orpheo28/physicallovablex/gtm-harness/context/profile.md

# Profile

Last updated: 2026-09-27. Truth order for product facts: `04_LIVRABLE/PRODUIT.md` > `04_LIVRABLE/PRD.md` > this file.

## Company
- **What it is:** PhysicalLovableX is a working name for an idea Hexa WTF is scoping. It is not a launched company: no revenue, no customers, no reference accounts (`00_ENONCE.md`; `03_DISCOVERY/envoi/SUIVI.md` shows 0 sent on 27/09).
- **Team (GTM):** Orphéo (O) runs outreach, calls and the harness. A hardware engineer contractor to sign Factory Packs is planned for W2 (**Hypothesis**, `04_LIVRABLE/deck/DECK_DRAFT.md` slide 9). Intros from the Hexa network are to ask, not assumed (same slide).
- **Stage:** pre-seed case study, 6-week plan W0-W6 (deck slide 9).

## Product (two pieces)
- **The Studio:** describe a product in one sentence, see it in 3D with unit cost and a factory shortlist, refine by prompting, then "Make it" runs 13 stages to a Launch Dossier. Measured: first version in 18-24 s; refines 4-7 s (colour, feature) and 11-24 s (geometry) (`PRODUIT.md`).
- **The Factory Pack (the primitive):** a spec package a factory can quote without back-and-forth: structured spec, CAD, BOM with component risk, DFM alerts, certification checklist, estimated landed cost, questions for the factory in EN + CN, assumption register (`PRODUIT.md`).
- **Two entry modes:** "I have an idea" (funnel, data) and "I have a prototype" (GTM wedge: funded founders stuck before production) (`PRODUIT.md`).

## What is real vs simulated
| Real (built, labelled Measured or Sourced) | Simulated (labelled "Fictional — demo data") |
|---|---|
| Brief, design, AI-written CAD (7/7 live prompts), measured DFM, certification map, LCSC part prices (dated snapshot), HTS lines from CBP rulings, Drewry freight index, cost engine, production plan, brand kit, production MCP over HTTP | The 15 partners (11 factories, 1 integrator, 3 installers), their capacity, quotes and negotiation replies, carrier quotes and transit days |

Source: `PRODUIT.md`, "Trust labels". Consequence for GTM: never present a factory, quote or delivery result as real in outreach or calls.

## Deal profile (all Hypothesis until a first deal)
| Tier | What the founder gets | Price | Cycle | Who signs |
|---|---|---|---|---|
| 1. Free Studio | Studio up to the Factory Pack | Free (land grab, data) | Self-serve | Founder |
| 2. Accompanied production | Human-reviewed pack, committed landed price, QC | Commission on the production order | Unknown; founder decides alone or with a co-founder (`context/icp.md`) | Founder |
| 3. Financing, logistics | Cash plan, freight | Take rate | Unknown | Founder |

Source: `PRODUIT.md`, "Business model (hypothesis)"; deck slide 5. Lighthouse founders are non-paying until proof of value; we test willingness to pay (amount already paid to intermediaries, W5 deposit or LOI), we do not optimise price (`context/icp.md`).
Comparable spend the founder already has: sourcing agents 5-10% of the order ([Dragon Sourcing](https://www.dragonsourcing.com/top-10-cost-insights-for-hiring-a-china-sourcing-agent/)); pre-shipment inspection $268 per man-day ([V-Trust](https://www.v-trust.com/en/our-network)).

## Reference customers
None yet. Do not imply any. The first documented case (prototype → Factory Pack → factory quote) is planned for W5-W6 (deck slide 9).
