orpheo28/physicallovablex/gtm-harness/outputs/research/pilet.md

# Pilet (Soulscircuit): account research (2026-09-26)

Run of `skills/account-research` on row 2 of `03_DISCOVERY/envoi/A_ENVOYER.md`.

## Pilet (Soulscircuit): score 5 (more than 12 months late, redesign after the campaign, backers organised a refund site; `outputs/accounts.csv`)
Problem: delivery promised for July 2025. On 2026-04-11, Update #20 ("Moving to Compute Module 5") switched the design from the Raspberry Pi 5 to the Compute Module 5, about five months past the deadline. The same articles say the team is also redesigning the case and building a display from scratch instead of using an off-the-shelf one. Raised CA$1,264,707 from 2,777 backers. No units shipped. ([C33 Technology](https://c33tech.com/blog/2026/04/how_not_to_pilet_a_kickstarter/), 2026-04-12; [Kickstarter update #20](https://www.kickstarter.com/projects/soulscircuit/pilet-opensource-modular-portable-mini-computer/posts/4654610), listed by search, page returns 403; [Hackster](https://www.hackster.io/news/soulscircuit-redesigns-its-pilet-handhelds-nearly-a-year-overdue-to-accept-the-raspberry-pi-cm5-d7f64a58cf36)). The creators' own sentence was not retrieved. The closest quote is from a backer in the C33 article: "We could use a quick message about how the manufacturer selection is going."
Root cause: design/engineering (redesign) | Confidence: high. **Hypothesis:** a second cause, factory selection, is suggested only by that backer quote, so it is not coded.
People: Christopher Stockall, co-founder ([Hackster post](https://www.facebook.com/hacksterio/posts/christopher-stockall-has-launched-a-crowdfunding-campaign-for-the-soulscircuit-p/1030775865757133/)); a second co-founder named "James" per `outputs/accounts.csv`, surname not found; engineering co-founder: none found
Channel: Kickstarter message
Next product: none found. Pilet 5 and Pilet 7 belong to the same campaign.
Angle: design/engineering question from `brief.md`: what the team learned between the prototype and manufacturing that led to the CM5 redesign.
Do not say: refunds, piletrefund.com, "in way over their head" (the C33 author's words), or update #22 screen failures. That detail comes only from piletrefund.com and was not reopened, so `RELANCE.md` #2 cites it with a warning.
