orpheo28/physicallovablex/gtm-harness/outputs/research/the-minimal-phone.md

# The Minimal Phone: account research (2026-09-26)

Run of `skills/account-research` on row 1 of `03_DISCOVERY/envoi/A_ENVOYER.md`.

## The Minimal Phone: score 5 (delivery date passed, only partly shipped, refund and complaint pressure; `outputs/accounts.csv`)
Problem: the delivery promised for summer 2024 moved to September, November-December, January-March and April-May 2025. The March 2025 Indiegogo update blamed a faulty screen temperature sensor and said assembly would resume 7 April. Complaints to the BBB continued into August 2026. Units affected: not stated. ([iTechGuides](https://www.itechguides.com/with-backers-losing-patience-the-long-delayed-minimal-phone-was-rumored-to-ship-in-two-weeks-what-happened/), 2026-08-18). The exact creator sentence was not retrieved: the page timed out and the Indiegogo page was not opened, so the sensor detail is from a search summary of that article. Medium confidence.
Root cause: components (screen temperature sensor defect) | Confidence: medium
People: Andre Youkhna, founder and CEO ([LinkedIn](https://www.linkedin.com/in/andre-youkhna/)); co-founder Armen Youssefian per `outputs/accounts.csv`, role not verified; engineering co-founder: none found
Channel: LinkedIn message to Andre Youkhna
Next product: **Minimal Phone 2 is now verified.** It launched on Kickstarter on 2026-08-11 at $599 / $675 / $899, with more than $800,000 from over 1,200 backers ([Gizmochina](https://www.gizmochina.com/2026/08/11/minimal-phone-2-swaps-e-ink-for-3-92-inch-oled-retains-qwerty-keyboard/)); a waitlist page existed on 2026-08-10 ([The Gadgeteer](https://the-gadgeteer.com/2026/08/10/minimal-phone-2-keyboard-smartphone/)). Shipping "December" comes from a search summary only: **Hypothesis**. This changes the note in `CLAUDE.md` and `signals.md` that called it unverified.
Angle: components question from `brief.md` ("How did you choose and qualify that component?"), tied to the screen sensor.
Do not say: BBB complaints, refunds, or backer anger; Minimal Phone 2 (the draft message leaves it out on purpose, and it is a delicate topic while the first phone is not fully shipped); "delivery not fully shipped" as fact, since full delivery status is unverified.
