orpheo28/physicallovablex/app/web/README.md

# web/

**Owner: W1 — Frontend.** Only this session edits this folder.

Next.js App Router + TS + Tailwind. Types: `src/types/contracts.ts` (generated — never edit; regenerate with `npm run gen:types`). API base URL: `NEXT_PUBLIC_API_URL` (default http://localhost:8000).

Contracts: `contracts/artifacts.py`, `contracts/api.md`, `contracts/stage_runner.md`, `contracts/fixtures.md`. Never edit `contracts/`, `api/main.py`, `pyproject.toml`, `web/package.json` — send a CONTRACT CHANGE REQUEST to the Monitor.
