orpheo28/physicallovablex/gtm-harness/outputs/weekly-log.md

# Weekly log

One row per `skills/weekly-update` run or harness change. Newest first. Details of skill runs are in `RUN_LOG.md`.

| Date | Files changed | Most significant change |
|---|---|---|
| 2026-09-27 | New `context/metrics.md`; new `skills/pvp-pack`, `skills/reply-handler`, `skills/aeo-check`; new `workflows/hook-experiments.md`; new `playbooks/free-as-marketing.md`, `build-in-public.md`, `lighthouse-ambassadors.md`; one-line links in `weekly-update`, `signal-to-sequence`, `founder-replied`; `CLAUDE.md`, `README.md` indexes + Borrowed playbooks | Lighthouse North Star set to products with a real factory quote from a Factory Pack, with the plan funnel (150 → 30 → 15 → 10 → 3, own targets); lessons from Verna/Osika (Lovable), Voje, Diode and Applied Intuition mapped to one file each. AEO, build in public and free-as-marketing are gated (post-go or Phase 2). |
| 2026-09-27 | `CLAUDE.md`, `README.md`; `context/` (new `profile.md`, `personas/factory-owner.md`, `personas/ecosystem-partner.md`; `icp.md`, `signals.md`, `positioning.md`, `competitors.md`, `personas/hardware-founder.md` rewritten); `skills/` (new `weekly-update`, `call-debrief`; the other 4 point to the new files and output names); new `workflows/` (3) and `playbooks/` (3); `outputs/` (`RUN_LOG.md` index, this file, campaign 01 `brief.md` and `tracking.md`, contact address removed from `research/wordrunner.md`) | Harness upgraded to the GTM repository structure (credits in `README.md`): signals now carry points, decay, combination bonuses, hooks and a performance table (all zeros, nothing sent); ICP gains tiers, qualification questions and an evolution log; campaign 01 tracking moves from 23 to 36 drafts (~32 sendable) plus the warm track (counts only). Open item: `outputs/accounts.csv` has 45 rows, `03_DISCOVERY/comptes.csv` has 55 (batch 3 not mirrored). |
