orpheo28/physicallovablex/gtm-harness/context/competitors.md

# Competitors (battlecards)

Last updated: 2026-09-27. Facts: `02_RECHERCHE/parallel/B_concurrence.md` (26/09/2026) unless linked. "Claimed" = stated by the company, not audited. **Every "we win / we lose" line is Hypothesis:** no deal has been won or lost yet. Format adapted from the GTM repository competitor radar (credits in `README.md`).

## The real alternatives (what founders do today)
| Alternative | What it is | We win when | We lose when |
|---|---|---|---|
| **DIY / "my contact in Shenzhen"** + spreadsheet + WeChat + third-party QC | The default (deck slide 7). Kill criterion if every founder already has a trusted contact (`PRD.md` §3) | The founder names a translation miss (spec read differently, component, certification) the contact did not catch | The contact already does the translation well: then stop, per the kill criterion |
| **Sourcing agent** (JingSourcing 5%, $100 min, [pricing](https://jingsourcing.com/pricing); agents 5-10%, [Dragon Sourcing](https://www.dragonsourcing.com/top-10-cost-insights-for-hiring-a-china-sourcing-agent/)) | Human commission on the order | Price committed upfront beats a commission, and the spec stays with the founder | The agent is trusted and cheap; no AI needed for a simple product |
| **Do nothing (tolerate the delay)** | > 75% of Kickstarter projects deliver late ([Mollick](https://papers.ssrn.com/sol3/papers.cfm?abstract_id=2088298)), ~9% never deliver ([Mollick](https://papers.ssrn.com/sol3/papers.cfm?abstract_id=2699251)) | The next product is at stake (S6) | Backers keep funding despite delay: vitamin risk (assumption A2) |
| Backer tools: PledgeBox, BackerKit (`outputs/accounts.csv`); QC $268 per man-day ([V-Trust](https://www.v-trust.com/en/our-network)) | Adjacent, not competing | Possible partners (`personas/ecosystem-partner.md`) | — |

## Idea to finished product
| Player | What it does | Funding | We win when | We lose when |
|---|---|---|---|---|
| **No Logo** (YC) | Vague idea → shipped product in ~1 month for creators; 25% on cost ([pricing](https://nologo.com/pricing)) | Not established | The founder already has a prototype and wants to own the spec; molds and specs stay the client's at No Logo | A creator with an audience and no product wants it done for them |
| **Cavela** | AI agent + human team: brief, RFQ, samples, QC, freight | $6.6M seed ([PR](https://www.prnewswire.com/news-releases/as-tariffs-drive-up-costs-cavela-ai-secures-6-6m-to-help-e-commerce-brands-pivot-production-fast-302621997.html)) | Outcome guarantee vs service; electronics with certification risk | E-commerce brand re-sourcing an existing product |
| **Sourcy** | "Prompt-to-product": spec → manufacturers, MOQ, samples; claims 300+ brands | $5M ([The Runway](https://www.therunway.ventures/p/sourcy)) | We publish delivery metrics | They show references we do not have |
| **Pietra** | Creator SaaS, $39 or $199 a month ([pricing](https://www.pietrastudio.com/plans-and-pricing)); Trustpilot 3/5, 107 reviews ([Trustpilot](https://ca.trustpilot.com/review/pietrastudio.com)) | ~$36M ([Tracxn](https://tracxn.com/d/companies/pietra/__JwjBftQ-SFH8mZMMACBpjOK6s2zcdriAyfKM6lLVEa8/funding-and-investors)) | The founder wants the lot risk carried, not a subscription | Simple private-label goods |
| **Sourcify / Wonnda** | Factory network, matchmaking ([Sourcify](https://www.sourcify.com/home-page-main), [Wonnda](https://wonnda.com/)) | Sourcify $150k ([Tracxn](https://tracxn.com/d/companies/sourcify/__Kv_MHbfagGUxUkLAHZy1HrHQJnQ0qoUO4--3tYcuLmc)) | No guarantee on their side | Founder only needs a factory name |

## AI sourcing, procurement and factory-side tools
| Player | What it does | Funding | We win when | We lose when |
|---|---|---|---|---|
| **Accio / Accio Work** (Alibaba). **Threat #1** | Supplier search, specs, RFQs, negotiation; $19.90-199 a month ([pricing](https://www.accio.com/pricing?pricingScene=manager&region=accio_work&language=en)); 230,000 businesses ([PR](https://www.prnewswire.com/news-releases/alibabas-accio-work-now-powers-230-000-online-stores-globally-302756549.html)) | Alibaba Group | Someone must be accountable for the delivered lot; Accio does not carry the risk | Price and supply depth decide; Alibaba owns both |
| **Saudara AI** (YC) | AI + human broker; claims "$1M+ sourced for 40+ brands in 5 months" ([YC](https://www.ycombinator.com/companies/saudara-ai)) | YC | Same as Accio | Same |
| **Didero, LightSource, Axya** | Procurement agents for industrial buyers | $30M ([blog](https://blog.didero.ai/blog/series-a-announcement)); $33M ([news](https://lightsource.ai/news/lightsource-secures-33-million-in-funding)); CAD 17M ([PR](https://www.prnewswire.com/news-releases/axya-secures-17-million-cad-in-funding-to-help-manufacturers-modernize-procurement-with-ai-302888441.html)) | Different buyer: a founder, not a procurement team | Not in our deals |
| **Monce** (Paris, 2024). Seller side, complementary | AI agents read inbound orders and quote requests in any format and push them into the factory ERP; claims 25 min → < 60 s per order, errors 8-12% → < 1% ([meetmonce.com](https://meetmonce.com/), 27/09/2026; [Automat-it case](https://newsblaze.com/business/technology/automat-it-helps-monce-build-an-aws-foundation-for-faster-industrial-growth_213346/), 13/04/2026). Verticals: construction, glass, aerospace, aluminium, mostly France | None disclosed (searched 27/09/2026); probable entity MONCE SAS ([Pappers](https://www.pappers.fr/entreprise/monce-934817198)), match unverified | We produce the clean RFQ (Factory Pack) that a Monce-equipped factory ingests: possible MCP partner | Not a competitor for founders; low threat |

## Upstream and downstream (parts, CAD)
Xometry $229M Q2 2026 revenue ([results](https://finance.yahoo.com/markets/stocks/articles/xometry-reports-record-second-quarter-110500200.html)); Fictiv joined MISUMI ([Fictiv](https://www.fictiv.com/articles/fictiv-joins-misumi-to-power-the-next-generation-of-digital-manufacturing)); Jiga $12M ([PR](https://www.prnewswire.com/news-releases/jiga-secures-12m-series-a-to-eliminate-hardware-sourcing-bottleneck-threatening-ai-scale-302618846.html)); text-to-CAD: RapidDirect AI Creator Lab ([GlobeNewswire](https://www.globenewswire.com/news-release/2026/06/15/3311907/0/en/Breaking-Design-Barriers-RapidDirect-s-AI-Creator-Lab-Allows-Anyone-to-Speak-Their-Product-Into-Ex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)), Adam, Zoo. Parts for engineers or AI design, not a finished consumer product with a guarantee.

**So what:** prompt-to-product is no longer empty and nobody publishes proof of delivery; carrying the risk is the gap (`B_concurrence.md`, "Lecture").

## Win / loss log
| Date | Account | Alternative chosen | Reason | Real loss or wrong fit? |
|---|---|---|---|---|
| — | none yet | — | Fill from `skills/call-debrief` whenever a founder names what they use instead | — |
