orpheo28/physicallovablex/gtm-harness/outputs/research/wordrunner.md

# Wordrunner (Astrohaus / Freewrite): account research (2026-09-26)

Run of `skills/account-research` on row 3 of `03_DISCOVERY/envoi/A_ENVOYER.md`.

## Wordrunner (Astrohaus / Freewrite): score 4 (date passed and still on pre-order, no redesign or silence signal to reach 5; `outputs/accounts.csv`)
Problem: shipping was promised for January 2026 ([Good e-Reader](https://goodereader.com/blog/technology/freewrite-wordrunner-is-shipping-out-in-january), 2025-11-15). On 2026-09-26 the product page still says "Preorder now to secure the best price and earliest priority" and gives no ship date ([getfreewrite.com](https://getfreewrite.com/products/wordrunner)). Kickstarter: $235,528 from 723 backers (`outputs/accounts.csv`). No creator statement was found: Kickstarter returns 403 and no update text was read. Units affected: not stated.
Root cause: not stated | Confidence: low. **Hypothesis:** a Reddit post reportedly mentions tooling and component changes, but it could not be opened (`outputs/accounts.csv`), so nothing is coded from it.
People: Adam Leeb, co-founder and CEO; Patrick Paul, co-founder ([Wikipedia: Astrohaus](https://en.wikipedia.org/wiki/Astrohaus)); engineering co-founder: none found
Channel: email (public brand address on the product page; the address itself is kept in `03_DISCOVERY/comptes.csv`, not in the harness)
Next product: none found. Astrohaus is a repeat hardware team per `02_RECHERCHE/parallel/00_SYNTHESE.md` §3, but no next product has a source.
Angle: since the cause is unknown, use open question 2 from `brief.md` ("What took longer or cost more than planned?") and let the founder name the bucket.
Do not say: tooling or component changes (Reddit, unverified), that the product is "late" beyond the two dated facts above, or the current price (three different prices are in circulation: $379, $459 and $500).
