orpheo28/physicallovablex/app/api/cad/prebuilt/demo_desk_lamp/d1.png

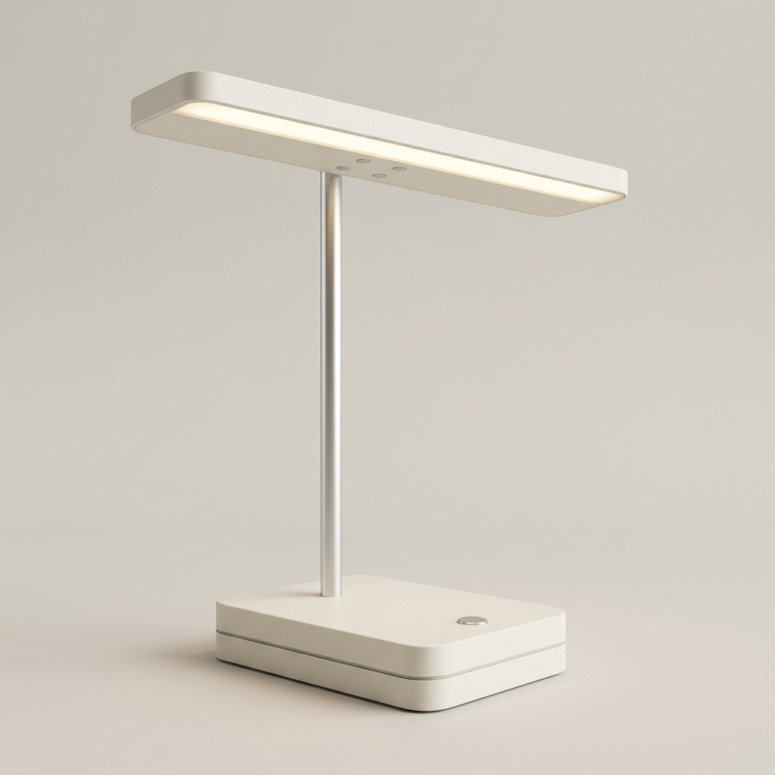
app/api/cad/prebuilt/demo_desk_lamp/d1.png
