orpheo28/physicallovablex/app/api/cad/prebuilt/demo_desk_lamp/d2.png

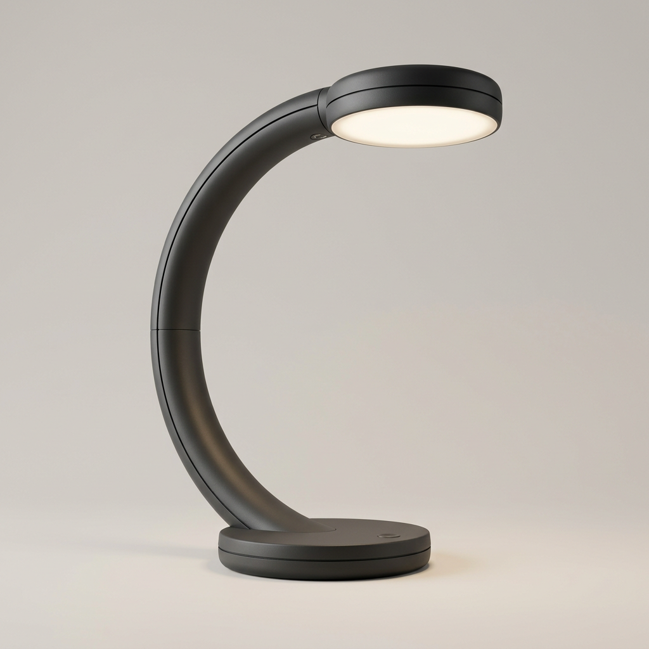
app/api/cad/prebuilt/demo_desk_lamp/d2.png
