orpheo28/physicallovablex/app/api/cad/prebuilt/demo_desk_lamp/hero_d3.png

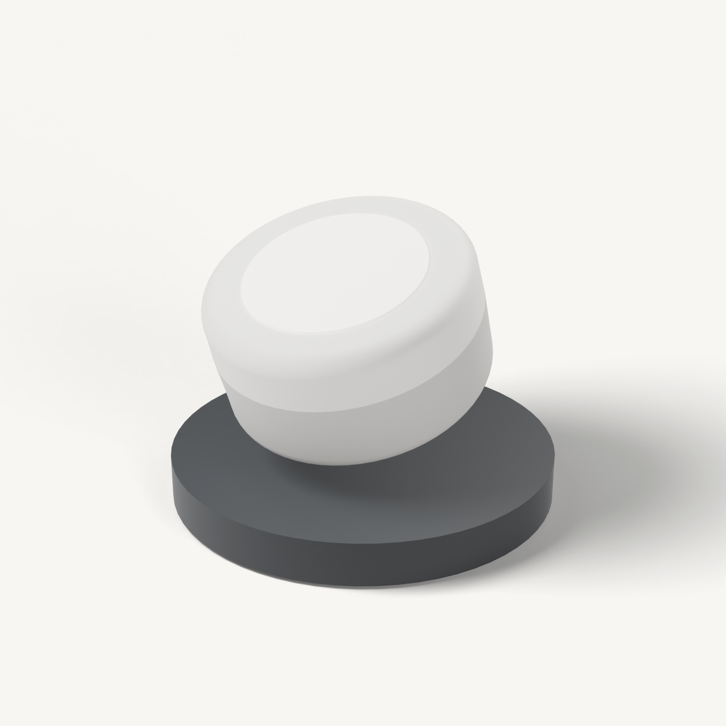
app/api/cad/prebuilt/demo_desk_lamp/hero_d3.png
