orpheo28/physicallovablex/app/api/cad/prebuilt/demo_tracker_card/d1.png

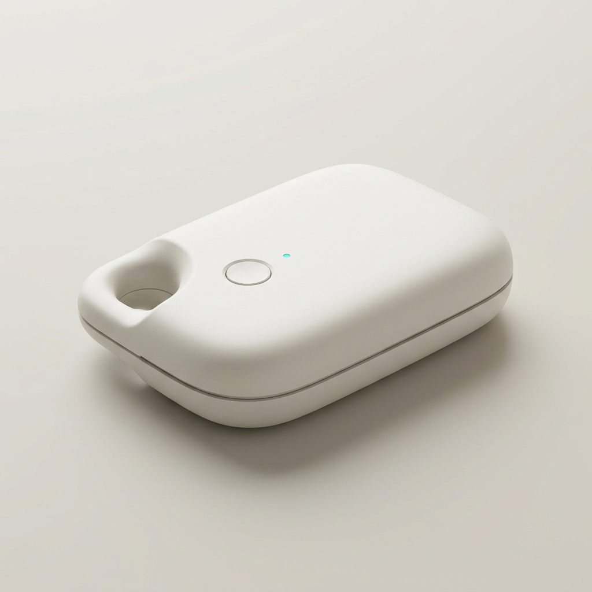
app/api/cad/prebuilt/demo_tracker_card/d1.png
