orpheo28/physicallovablex/app/api/cad/prebuilt/demo_tracker_card/hero_d3.png

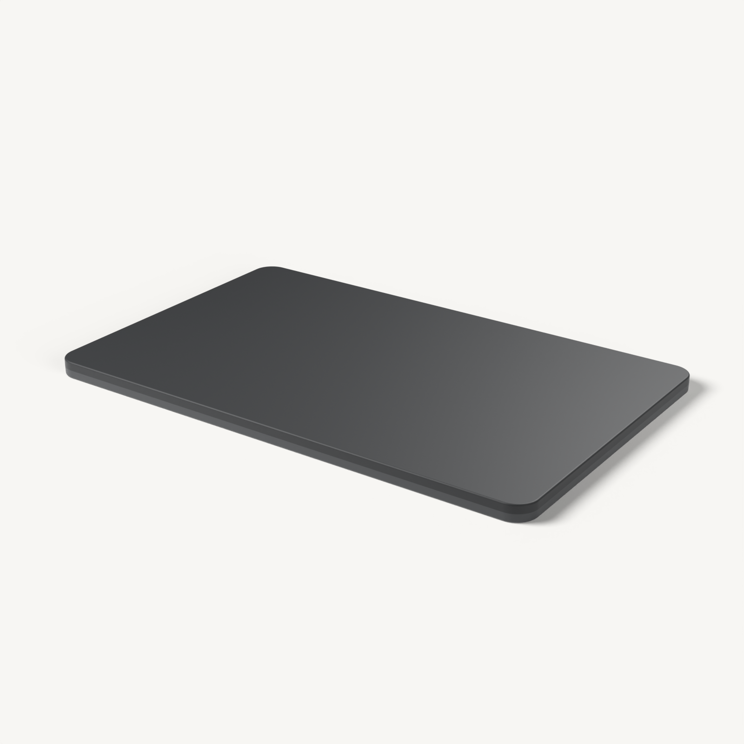
app/api/cad/prebuilt/demo_tracker_card/hero_d3.png
