orpheo28/physicallovablex/app/api/cad/prebuilt/showcase_changing_table/photo_v2_lifestyle.png

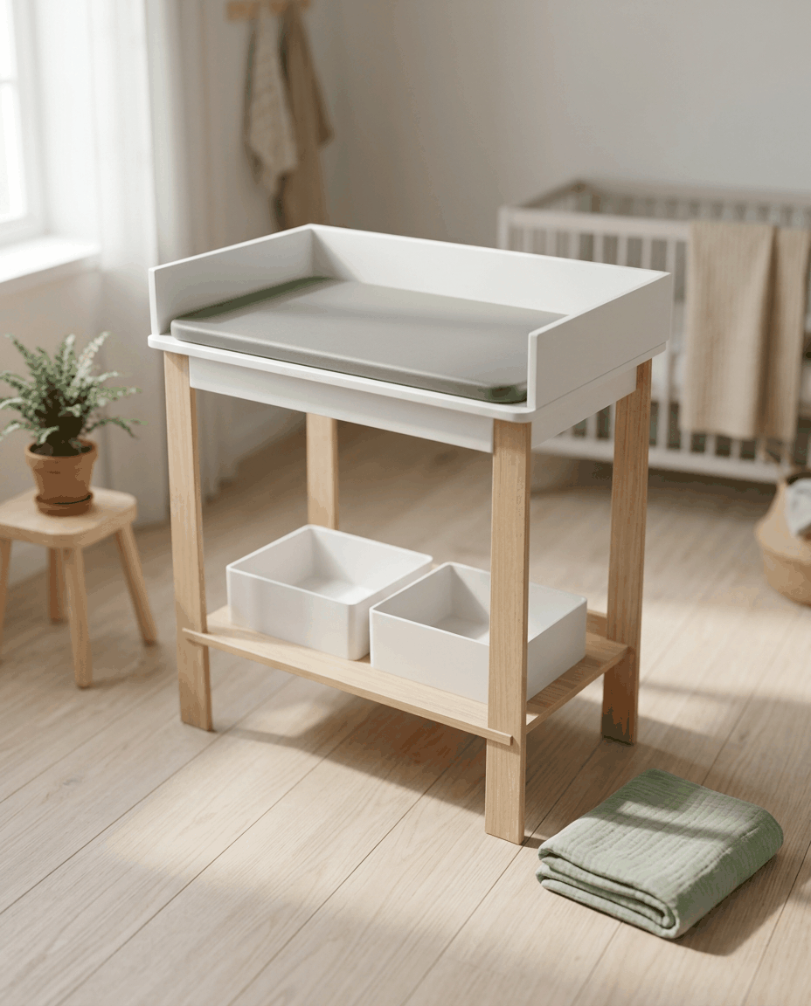
app/api/cad/prebuilt/showcase_changing_table/photo_v2_lifestyle.png
