orpheo28/physicallovablex/app/api/cad/prebuilt/showcase_changing_table/v1.png

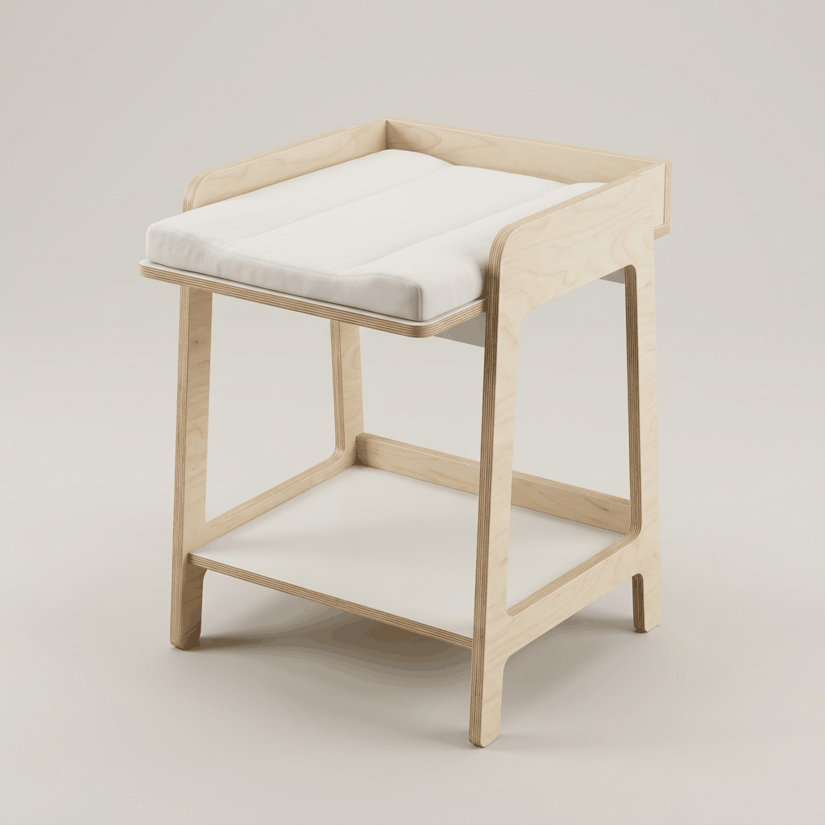
app/api/cad/prebuilt/showcase_changing_table/v1.png
