orpheo28/physicallovablex/app/api/cad/prebuilt/showcase_drone_follow/hero_v2.png

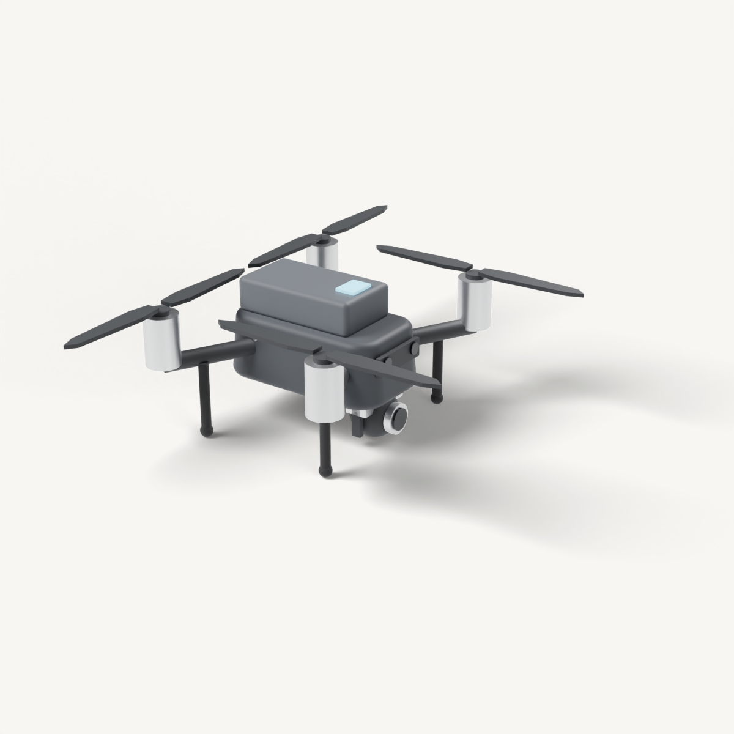
app/api/cad/prebuilt/showcase_drone_follow/hero_v2.png
