orpheo28/physicallovablex/app/api/cad/prebuilt/showcase_drone_follow/photo_v2_hero_studio.png

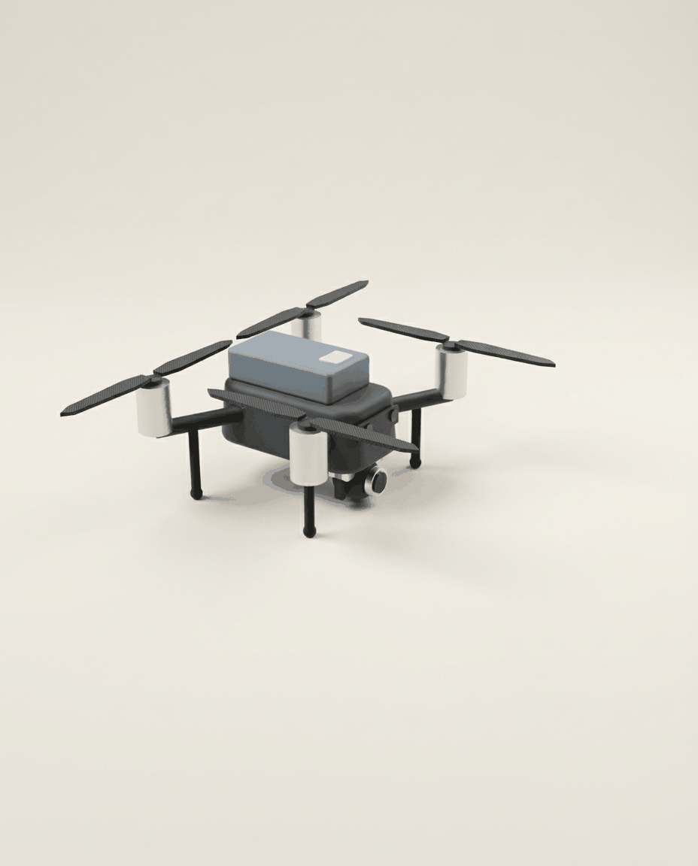
app/api/cad/prebuilt/showcase_drone_follow/photo_v2_hero_studio.png
