orpheo28/physicallovablex/app/api/cad/prebuilt/showcase_drone_follow/photo_v2_lifestyle.png

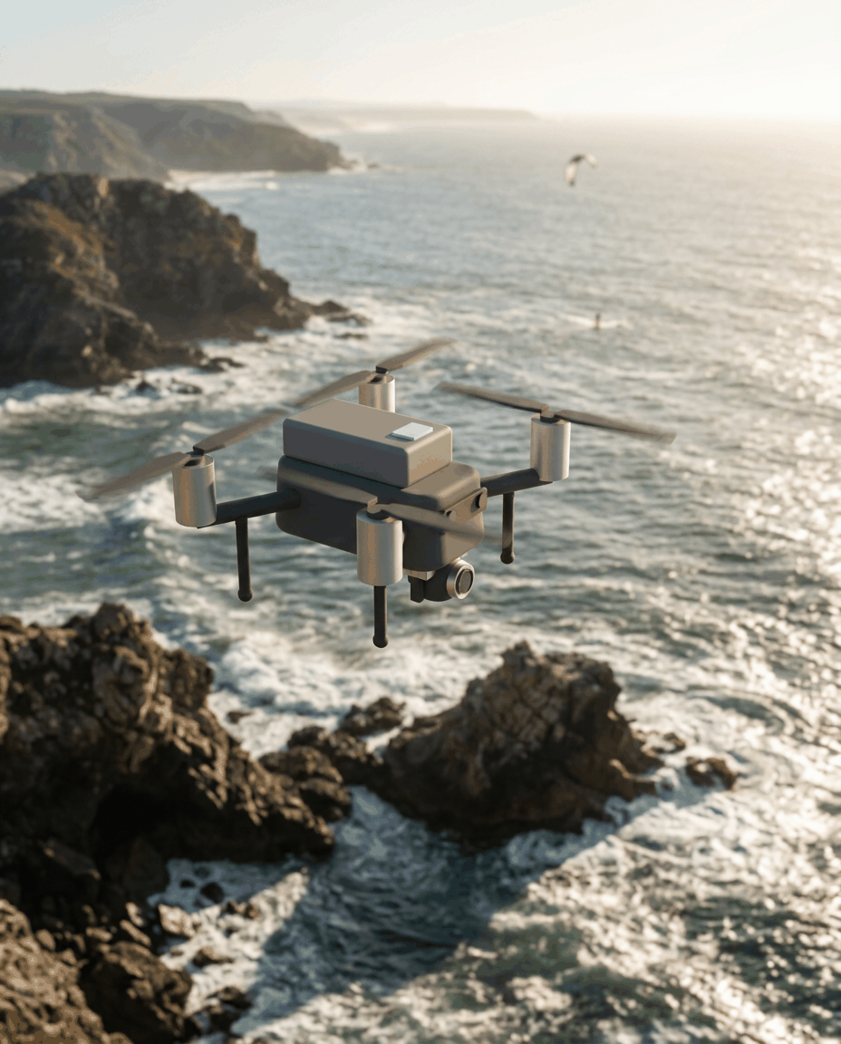
app/api/cad/prebuilt/showcase_drone_follow/photo_v2_lifestyle.png
