orpheo28/physicallovablex/app/api/cad/prebuilt/showcase_drone_follow/v1.png

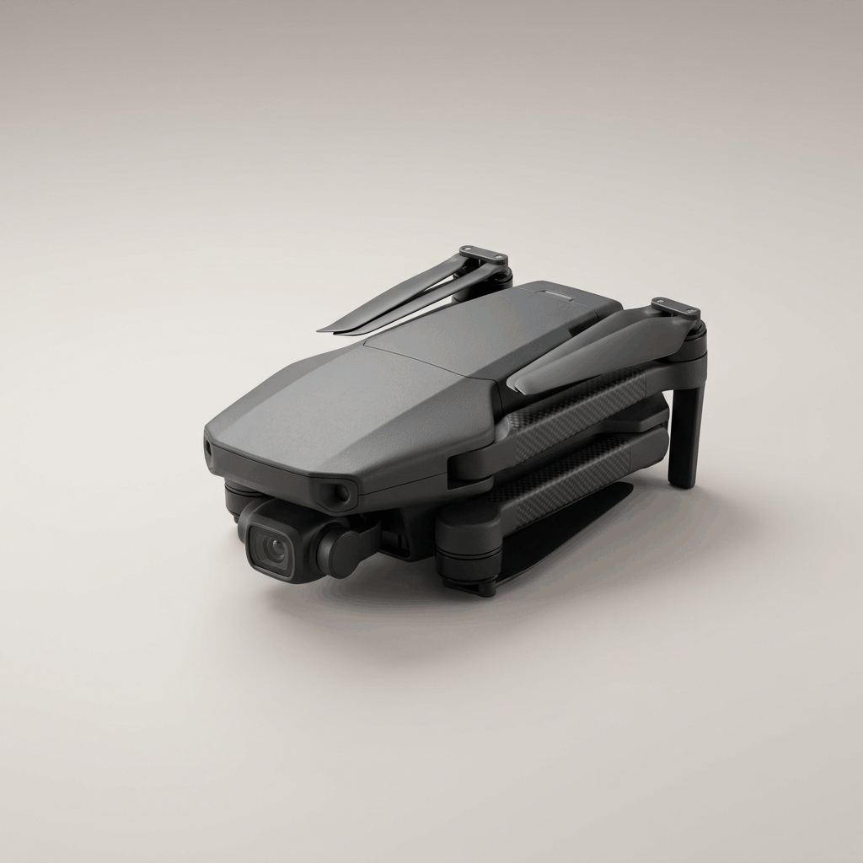
app/api/cad/prebuilt/showcase_drone_follow/v1.png
