orpheo28/physicallovablex/app/api/cad/prebuilt/showcase_hair_dryer/hero_v1.png

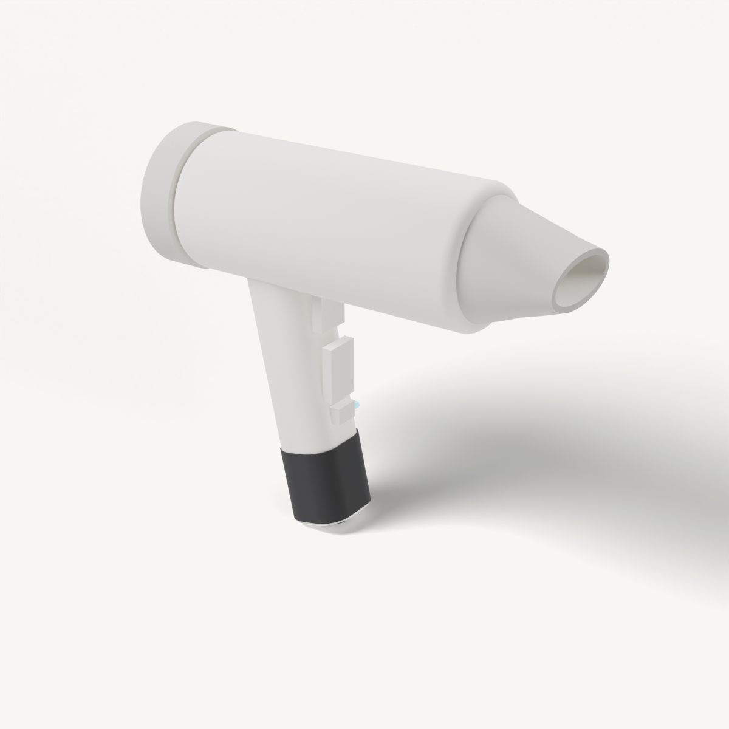
app/api/cad/prebuilt/showcase_hair_dryer/hero_v1.png
