orpheo28/physicallovablex/app/api/cad/prebuilt/showcase_hair_dryer/photo_v1_lifestyle.png

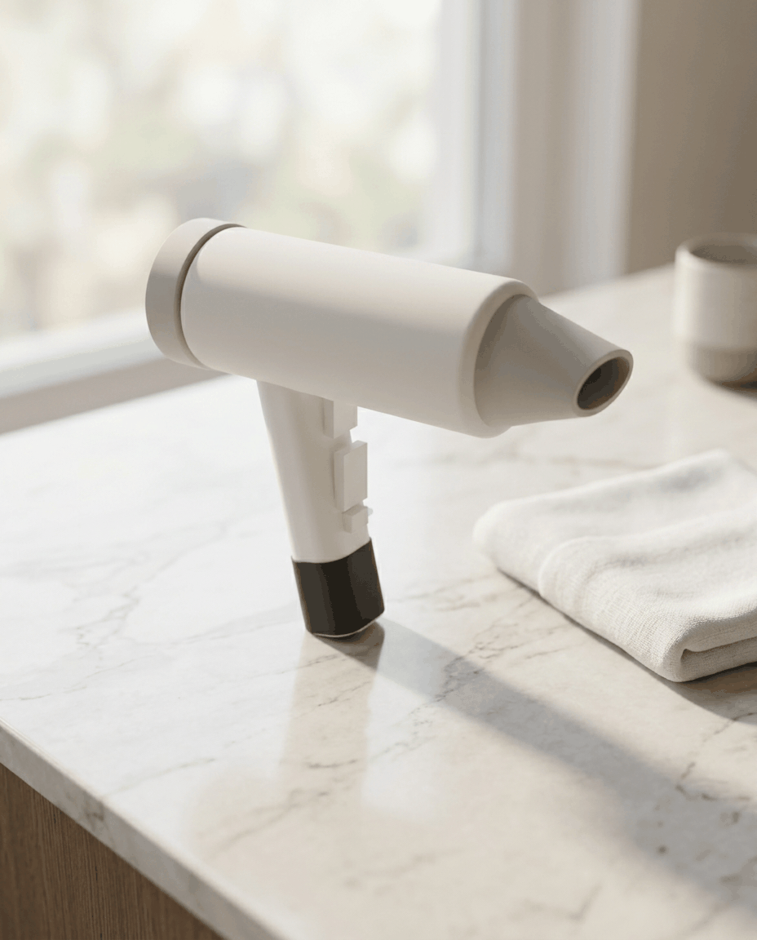
app/api/cad/prebuilt/showcase_hair_dryer/photo_v1_lifestyle.png
