orpheo28/physicallovablex/app/api/cad/prebuilt/showcase_home_robot/hero_v1.png

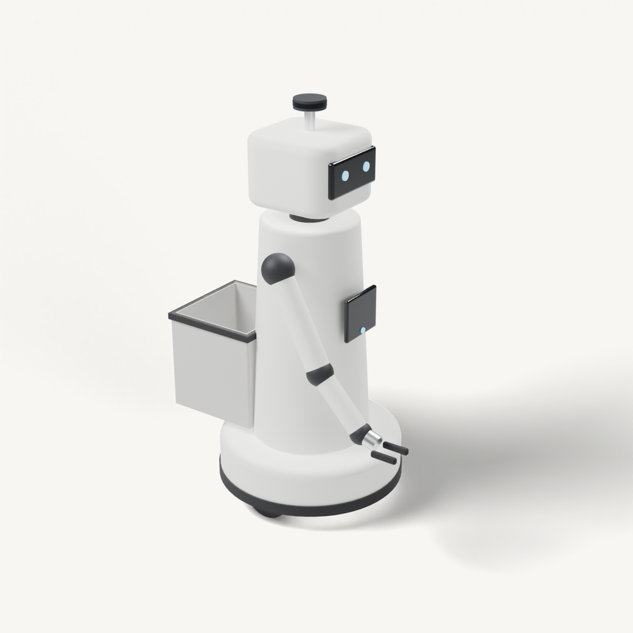
app/api/cad/prebuilt/showcase_home_robot/hero_v1.png
