orpheo28/physicallovablex/app/api/cad/prebuilt/showcase_home_robot/photo_v1_hero_studio.png

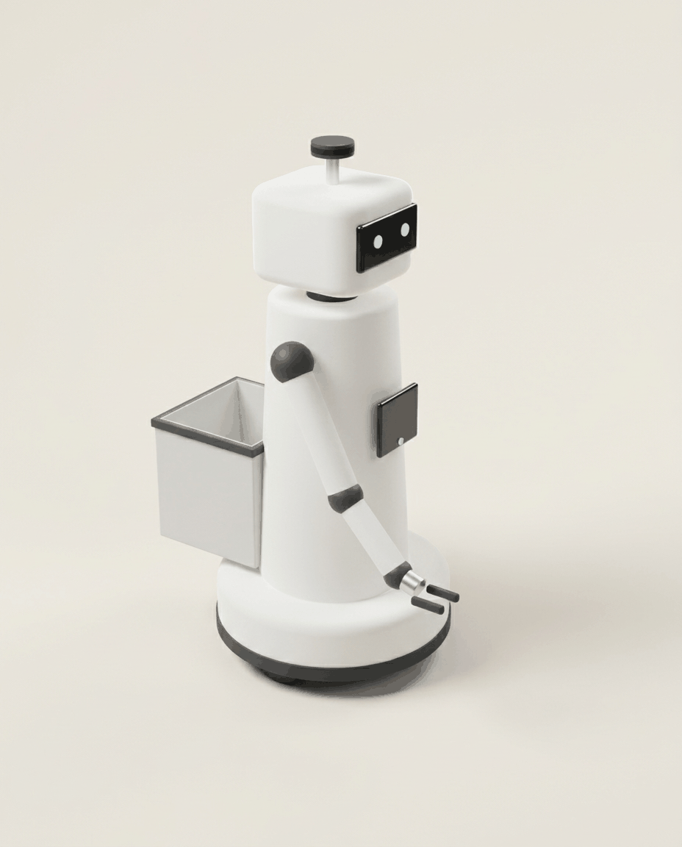
app/api/cad/prebuilt/showcase_home_robot/photo_v1_hero_studio.png
