orpheo28/physicallovablex/app/api/cad/prebuilt/showcase_home_robot/photo_v1_lifestyle.png

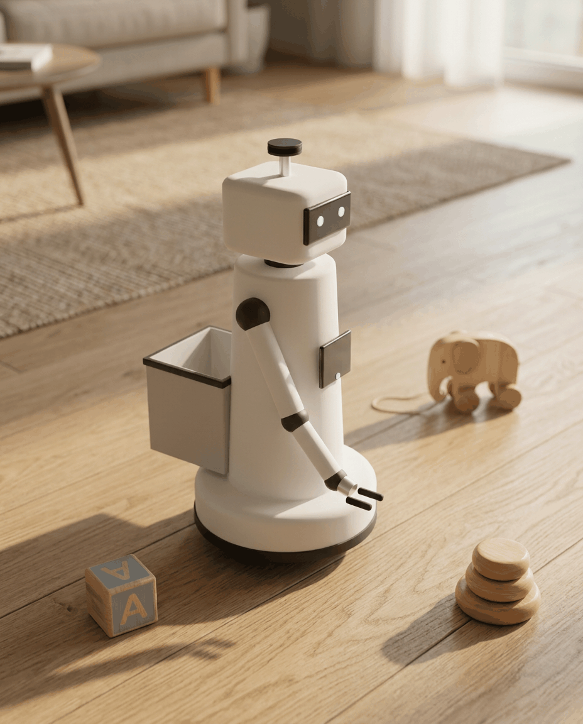
app/api/cad/prebuilt/showcase_home_robot/photo_v1_lifestyle.png
