orpheo28/physicallovablex/app/api/cad/prebuilt/showcase_instant_camera/hero_v1.png

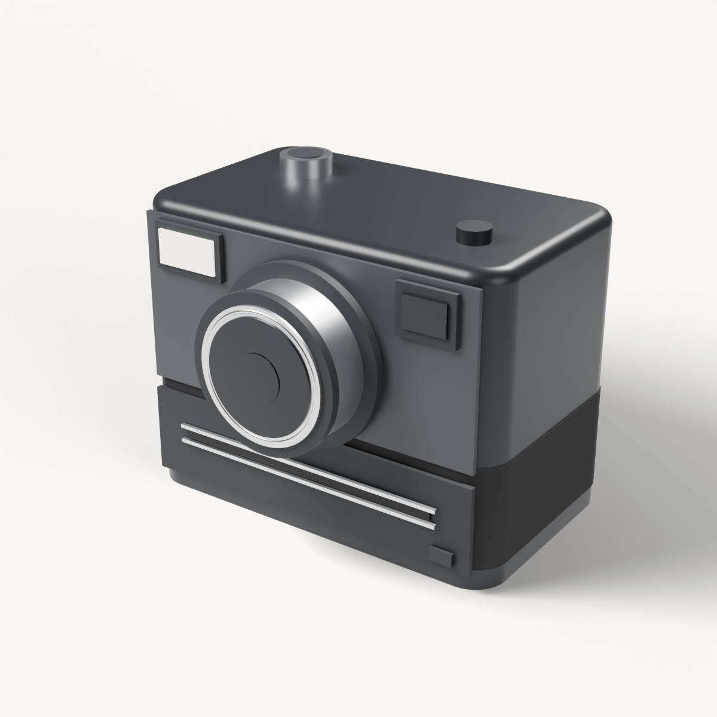
app/api/cad/prebuilt/showcase_instant_camera/hero_v1.png
