orpheo28/physicallovablex/app/api/cad/prebuilt/showcase_instant_camera/photo_v1_hero_studio.png

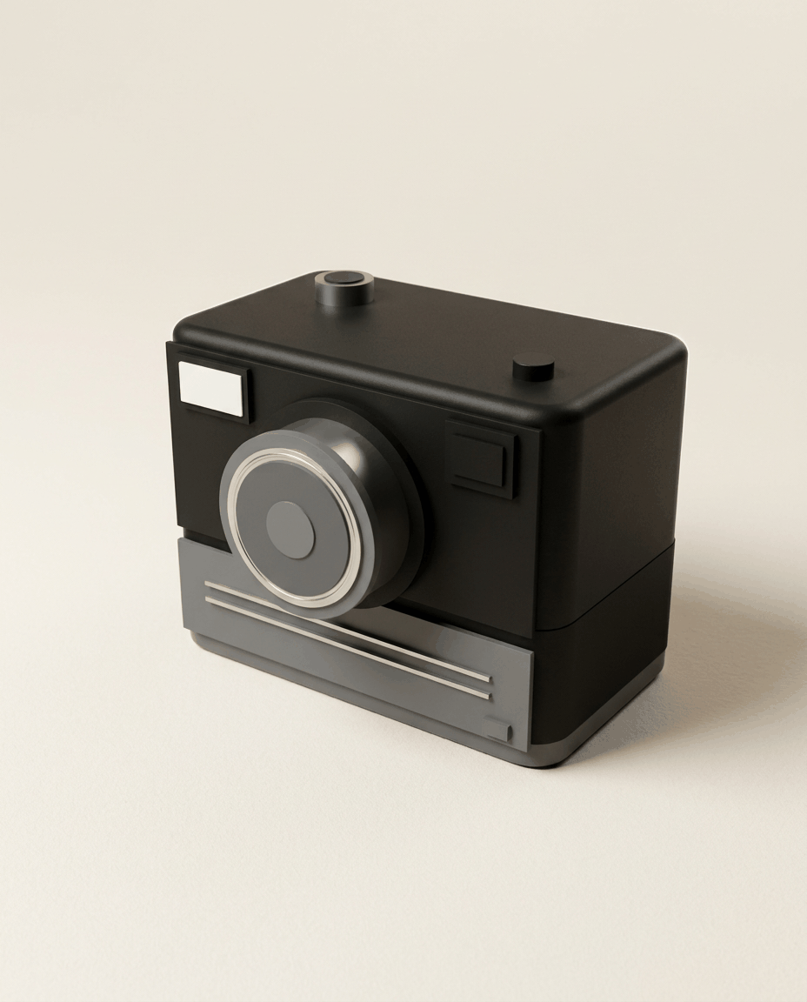
app/api/cad/prebuilt/showcase_instant_camera/photo_v1_hero_studio.png
