orpheo28/physicallovablex/app/api/cad/prebuilt/showcase_instant_camera/photo_v1_lifestyle.png

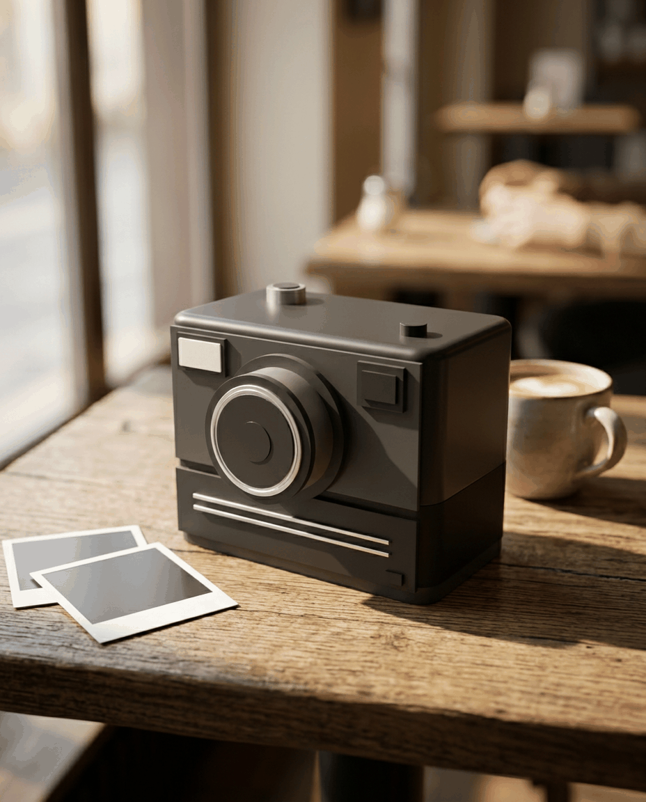
app/api/cad/prebuilt/showcase_instant_camera/photo_v1_lifestyle.png
