orpheo28/physicallovablex/app/api/cad/prebuilt/showcase_instant_camera/v1.png

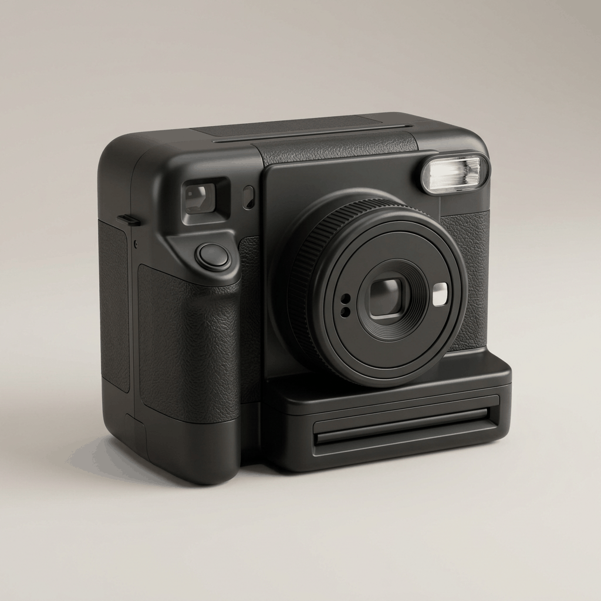
app/api/cad/prebuilt/showcase_instant_camera/v1.png
