orpheo28/physicallovablex/app/api/cad/prebuilt/showcase_irrigation_biarritz/hero_v2.png

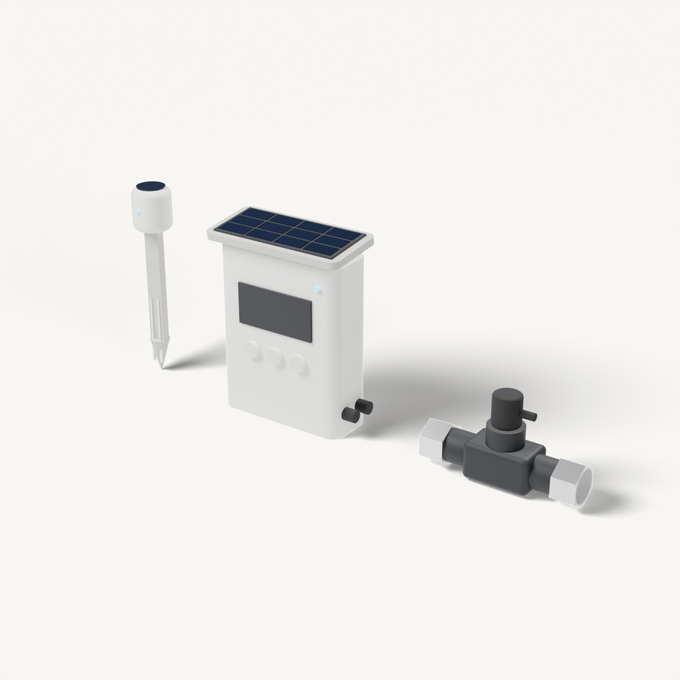
app/api/cad/prebuilt/showcase_irrigation_biarritz/hero_v2.png
