orpheo28/physicallovablex/app/api/cad/prebuilt/showcase_irrigation_biarritz/v1.png

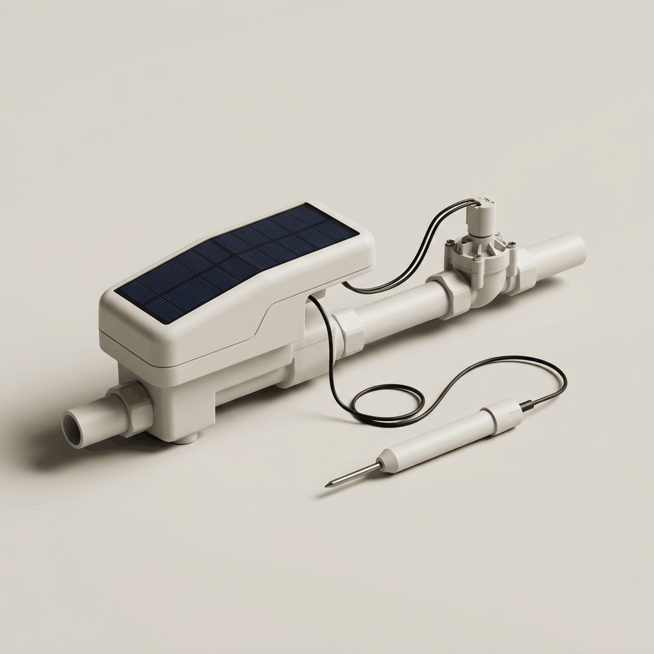
app/api/cad/prebuilt/showcase_irrigation_biarritz/v1.png
