orpheo28/physicallovablex/app/api/cad/prebuilt/showcase_minimal_phone/hero_v1.png

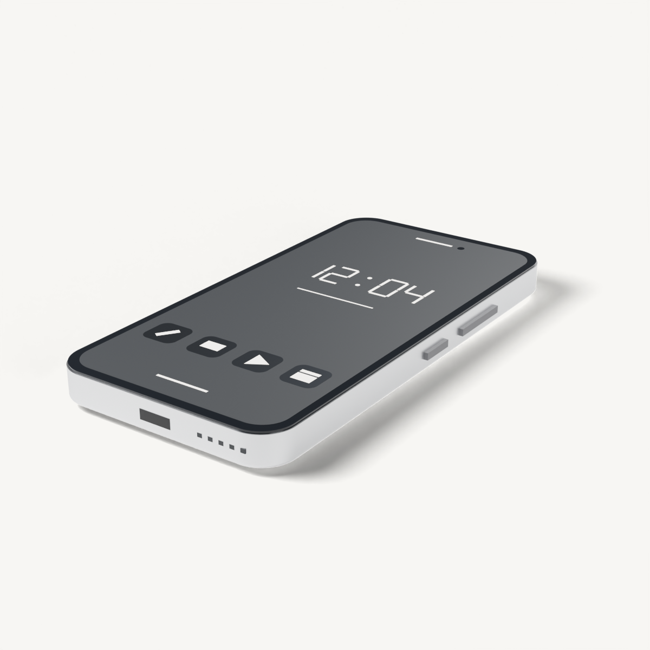
app/api/cad/prebuilt/showcase_minimal_phone/hero_v1.png
