orpheo28/physicallovablex/app/api/cad/prebuilt/showcase_minimal_phone/photo_v1_lifestyle.png

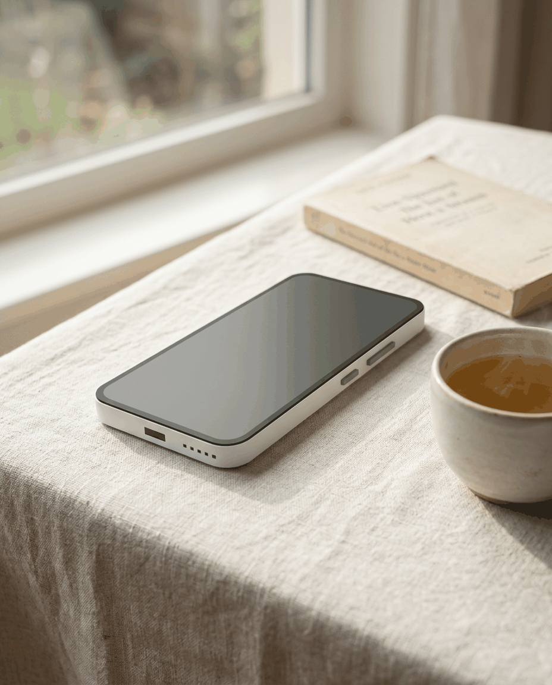
app/api/cad/prebuilt/showcase_minimal_phone/photo_v1_lifestyle.png
