orpheo28/physicallovablex/app/api/cad/prebuilt/showcase_solar_biarritz/hero_v2.png

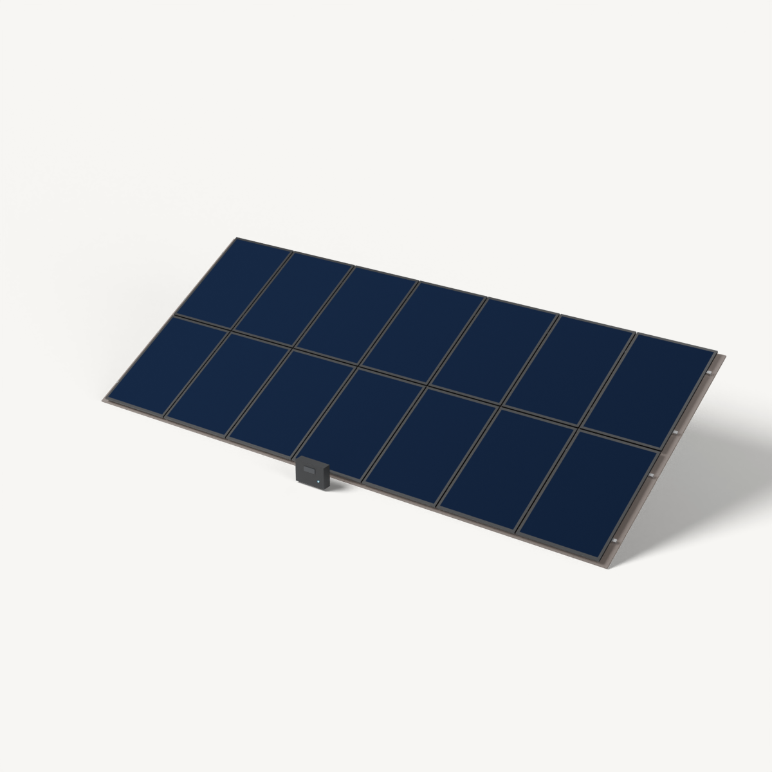
app/api/cad/prebuilt/showcase_solar_biarritz/hero_v2.png
