orpheo28/physicallovablex/app/api/cad/prebuilt/showcase_solar_biarritz/photo_v2_hero_studio.png

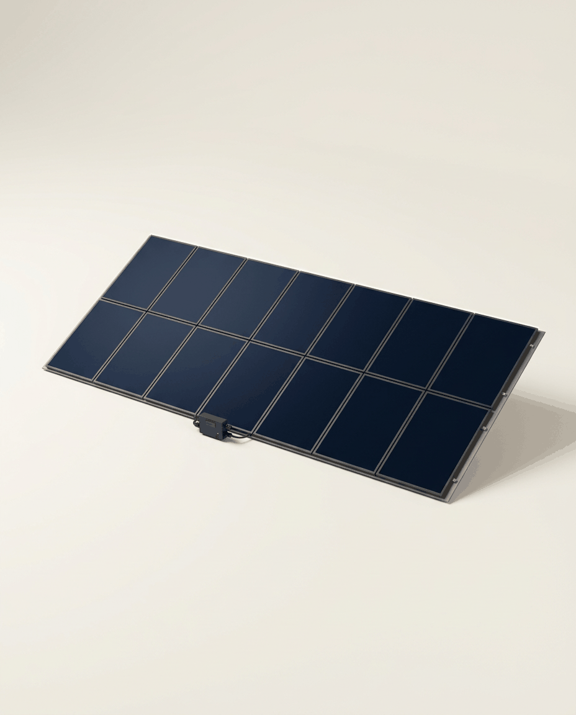
app/api/cad/prebuilt/showcase_solar_biarritz/photo_v2_hero_studio.png
