orpheo28/physicallovablex/app/api/cad/prebuilt/showcase_solar_biarritz/photo_v2_lifestyle.png

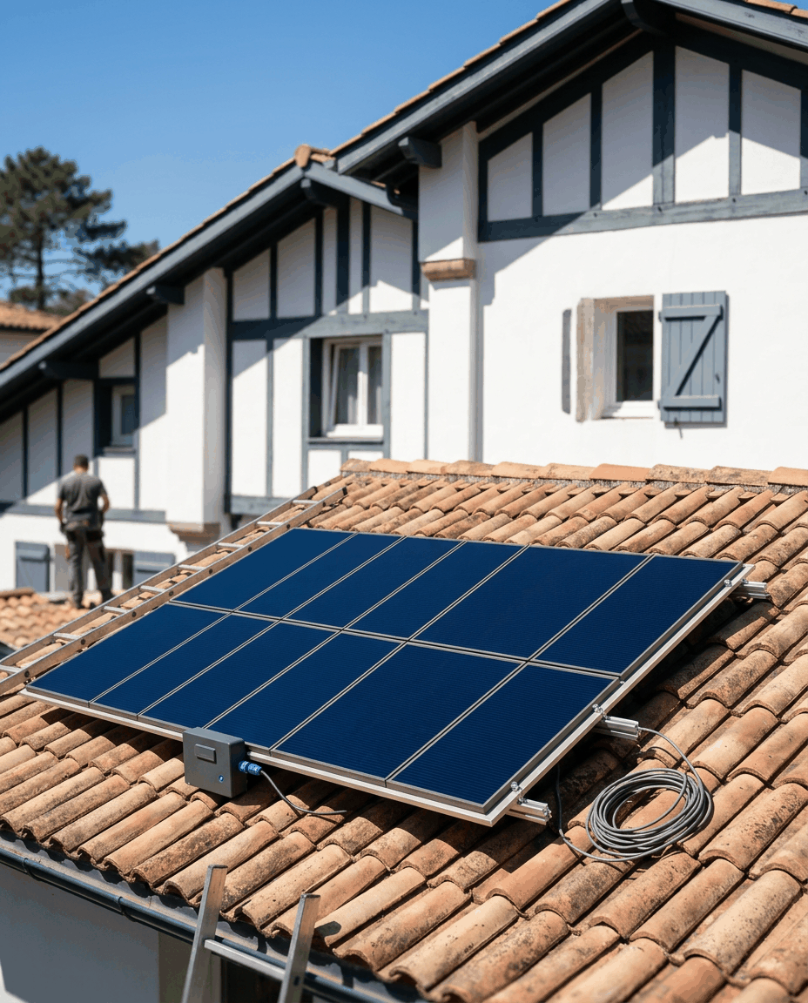
app/api/cad/prebuilt/showcase_solar_biarritz/photo_v2_lifestyle.png
