orpheo28/physicallovablex/app/api/cad/prebuilt/showcase_solar_biarritz/v1.png

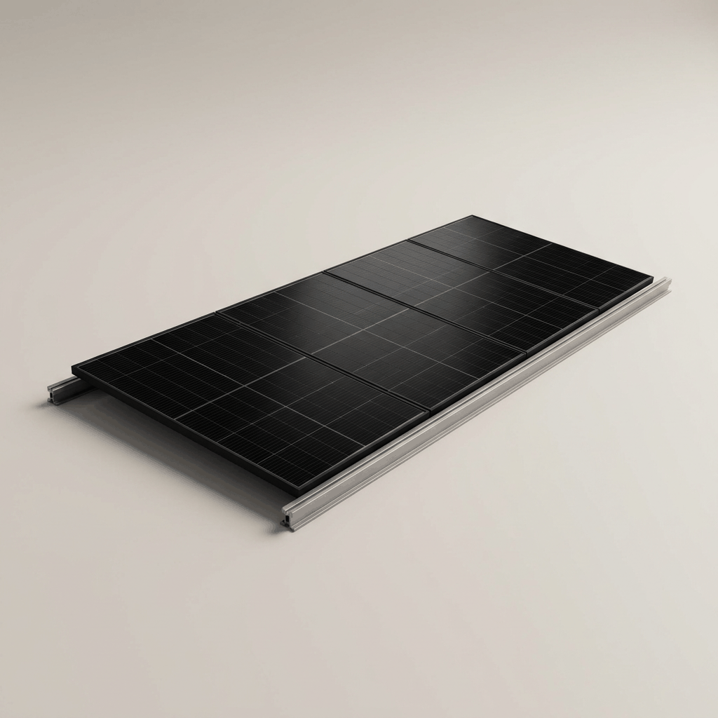
app/api/cad/prebuilt/showcase_solar_biarritz/v1.png
