orpheo28/physicallovablex/app/api/cad/prebuilt/showcase_stick_vacuum/hero_v2.png

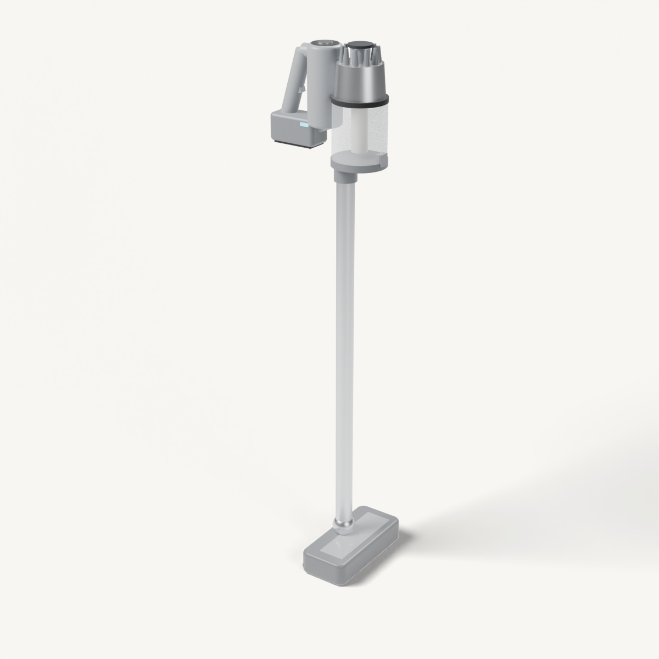
app/api/cad/prebuilt/showcase_stick_vacuum/hero_v2.png
