orpheo28/physicallovablex/app/api/cad/prebuilt/showcase_stick_vacuum/photo_v2_hero_studio.png

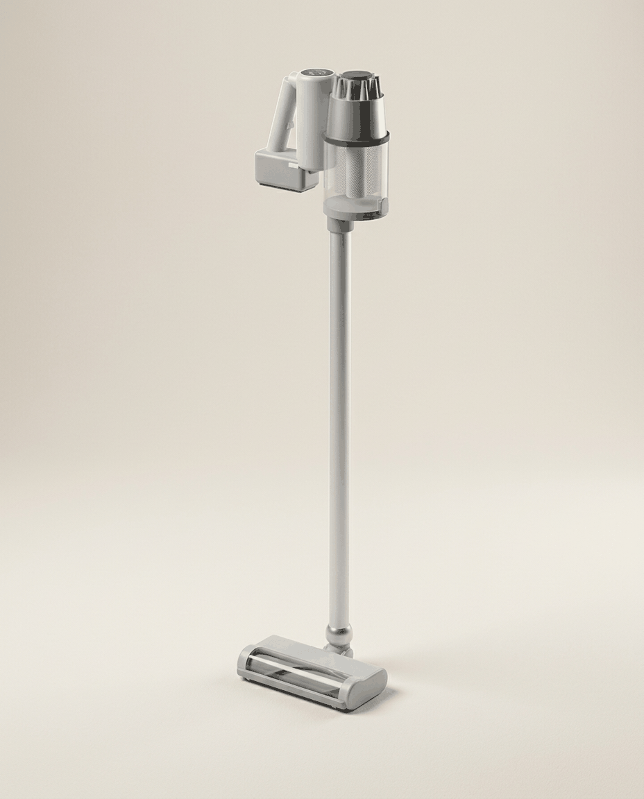
app/api/cad/prebuilt/showcase_stick_vacuum/photo_v2_hero_studio.png
