orpheo28/physicallovablex/app/api/cad/prebuilt/showcase_stick_vacuum/photo_v2_lifestyle.png

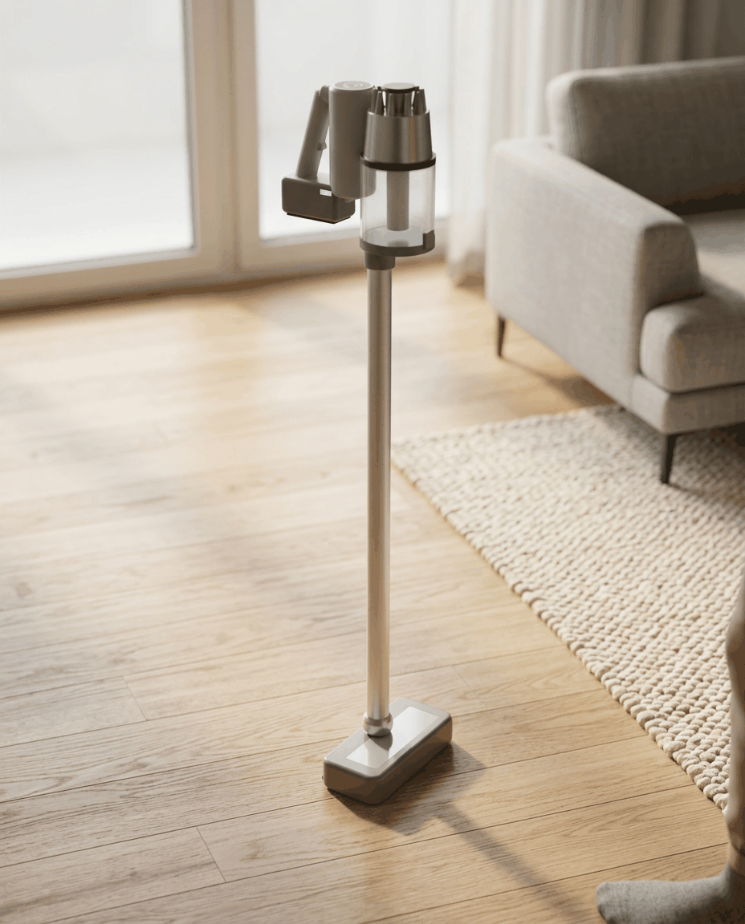
app/api/cad/prebuilt/showcase_stick_vacuum/photo_v2_lifestyle.png
