orpheo28/physicallovablex/app/api/cad/prebuilt/showcase_stick_vacuum/v1.png

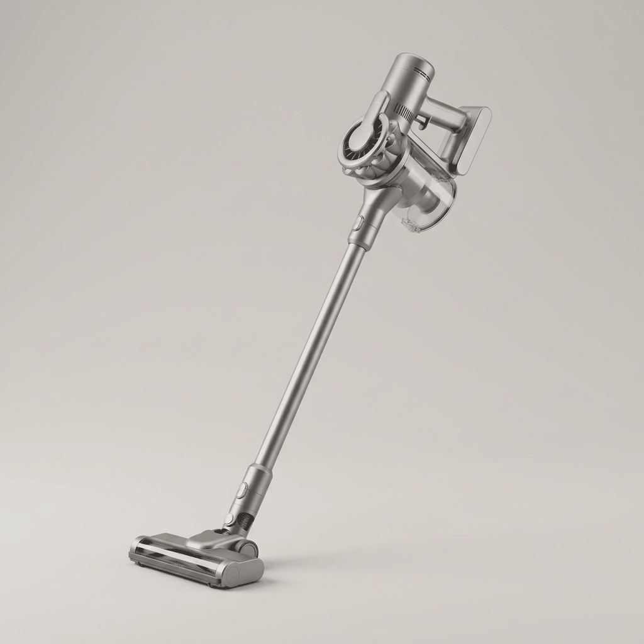
app/api/cad/prebuilt/showcase_stick_vacuum/v1.png
