orpheo28/physicallovablex/app/api/cad/prebuilt/showcase_surfboard_beginner/hero_v2.png

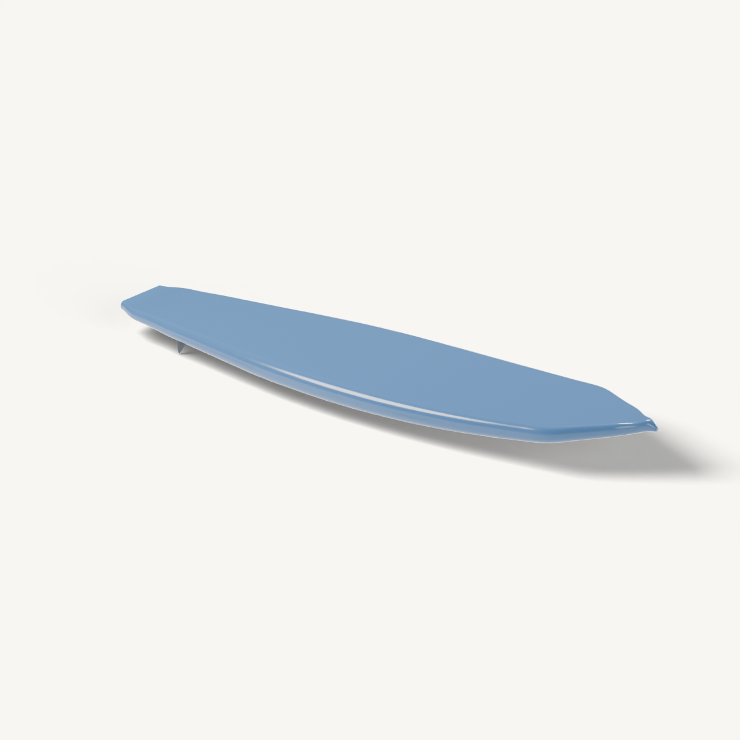
app/api/cad/prebuilt/showcase_surfboard_beginner/hero_v2.png
