orpheo28/physicallovablex/app/api/cad/prebuilt/showcase_surfboard_beginner/photo_v2_hero_studio.png

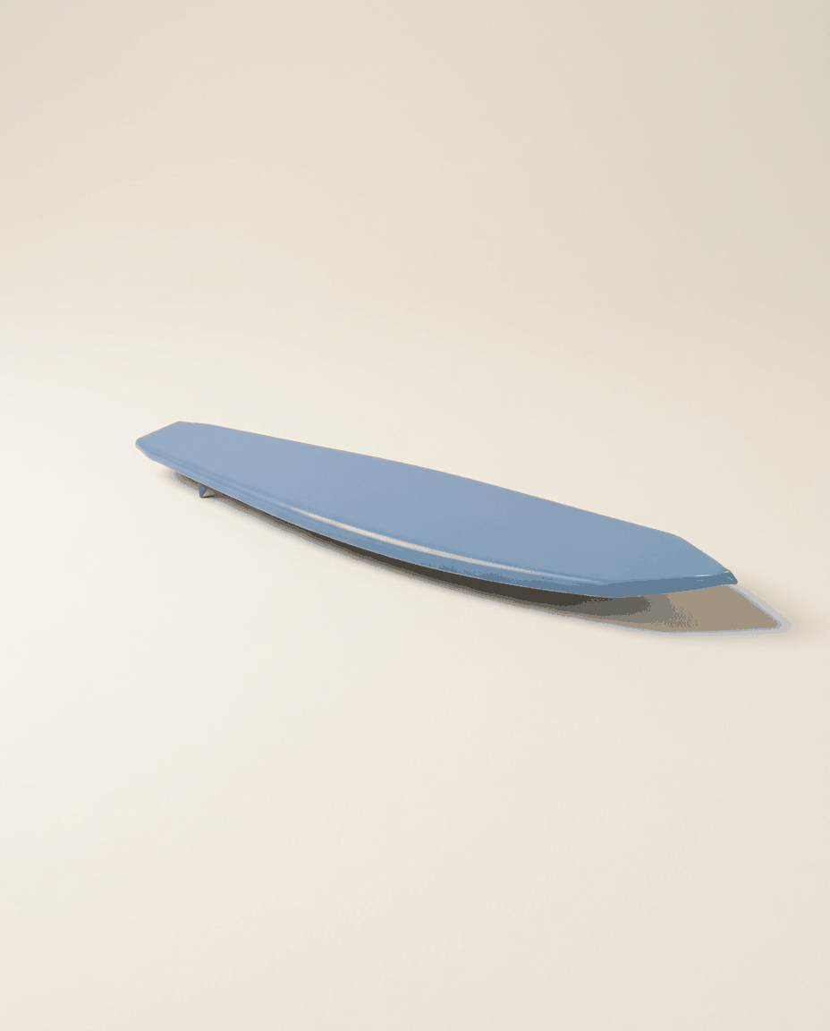
app/api/cad/prebuilt/showcase_surfboard_beginner/photo_v2_hero_studio.png
