orpheo28/physicallovablex/app/api/cad/prebuilt/showcase_surfboard_beginner/photo_v2_lifestyle.png

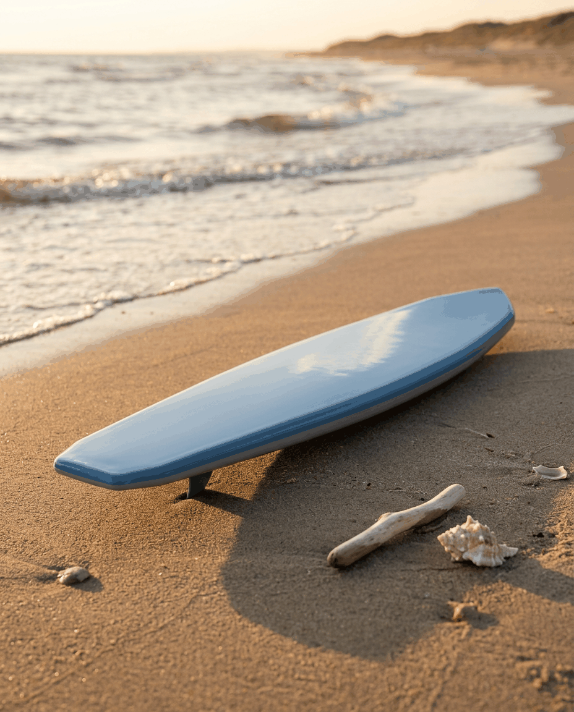
app/api/cad/prebuilt/showcase_surfboard_beginner/photo_v2_lifestyle.png
