orpheo28/physicallovablex/app/api/cad/prebuilt/showcase_surfboard_beginner/v1.png

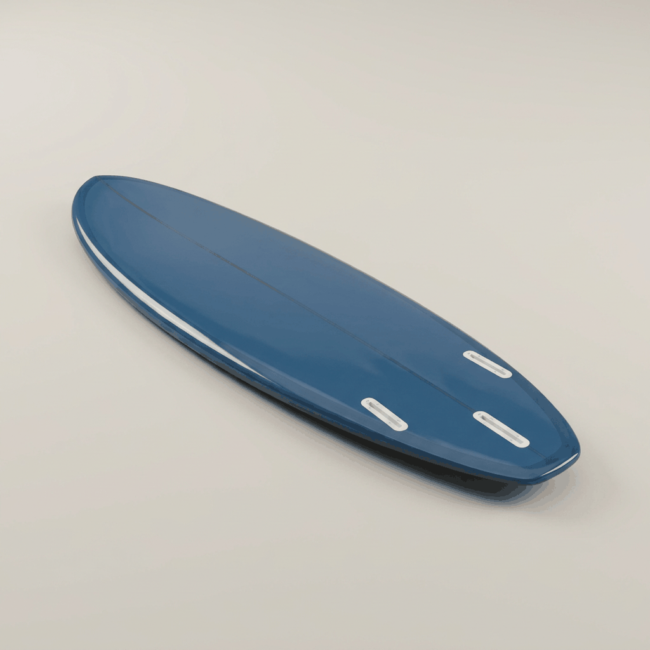
app/api/cad/prebuilt/showcase_surfboard_beginner/v1.png
