orpheo28/physicallovablex/app/api/cad/prebuilt/showcase_whoop_kitesurf/photo_v4_hero_studio.png

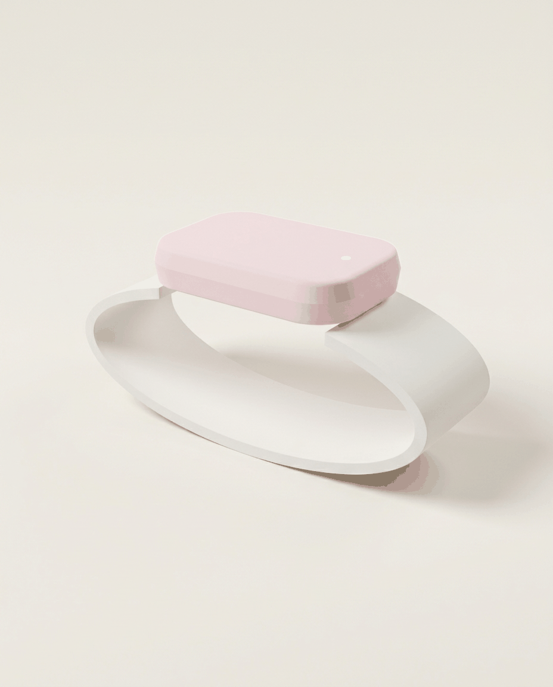
app/api/cad/prebuilt/showcase_whoop_kitesurf/photo_v4_hero_studio.png
