orpheo28/physicallovablex/app/api/cad/prebuilt/showcase_whoop_kitesurf/photo_v4_in_hand_scale.png

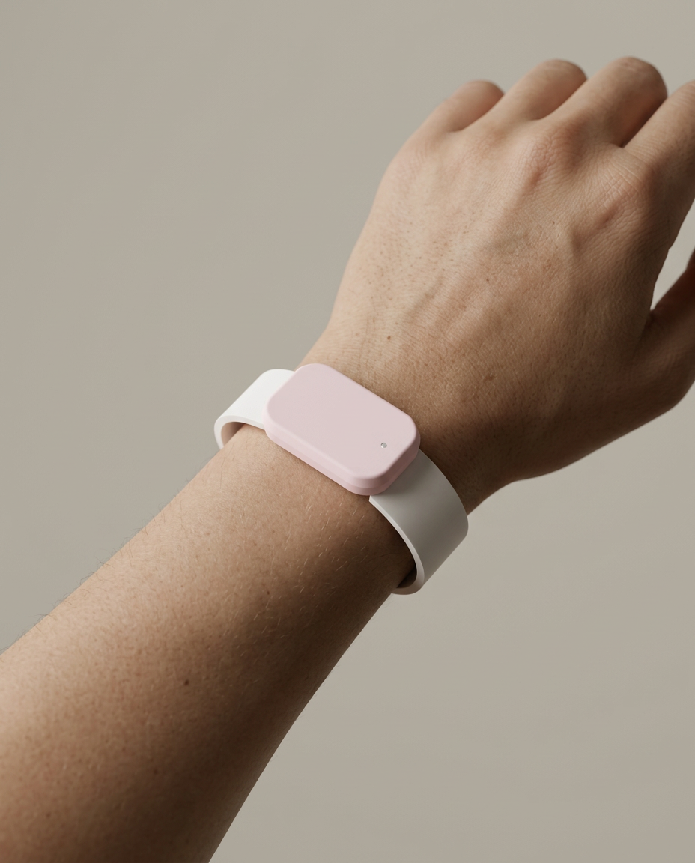
app/api/cad/prebuilt/showcase_whoop_kitesurf/photo_v4_in_hand_scale.png
