orpheo28/physicallovablex/app/api/cad/prebuilt/showcase_whoop_kitesurf/v3.png

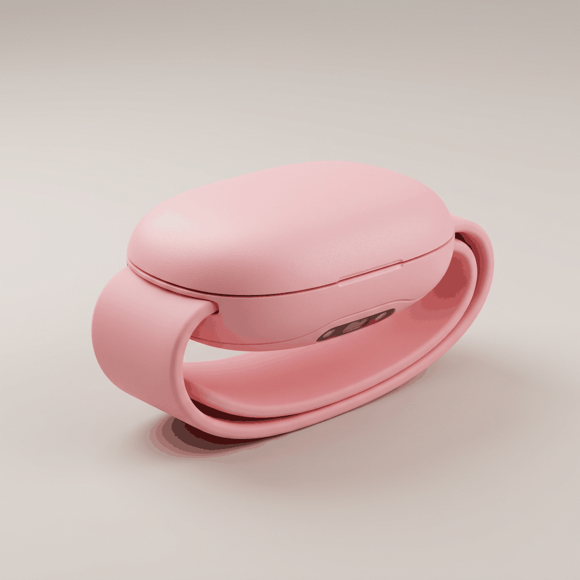
app/api/cad/prebuilt/showcase_whoop_kitesurf/v3.png
