orpheo28/physicallovablex/app/docs/screens/after/00_home.png

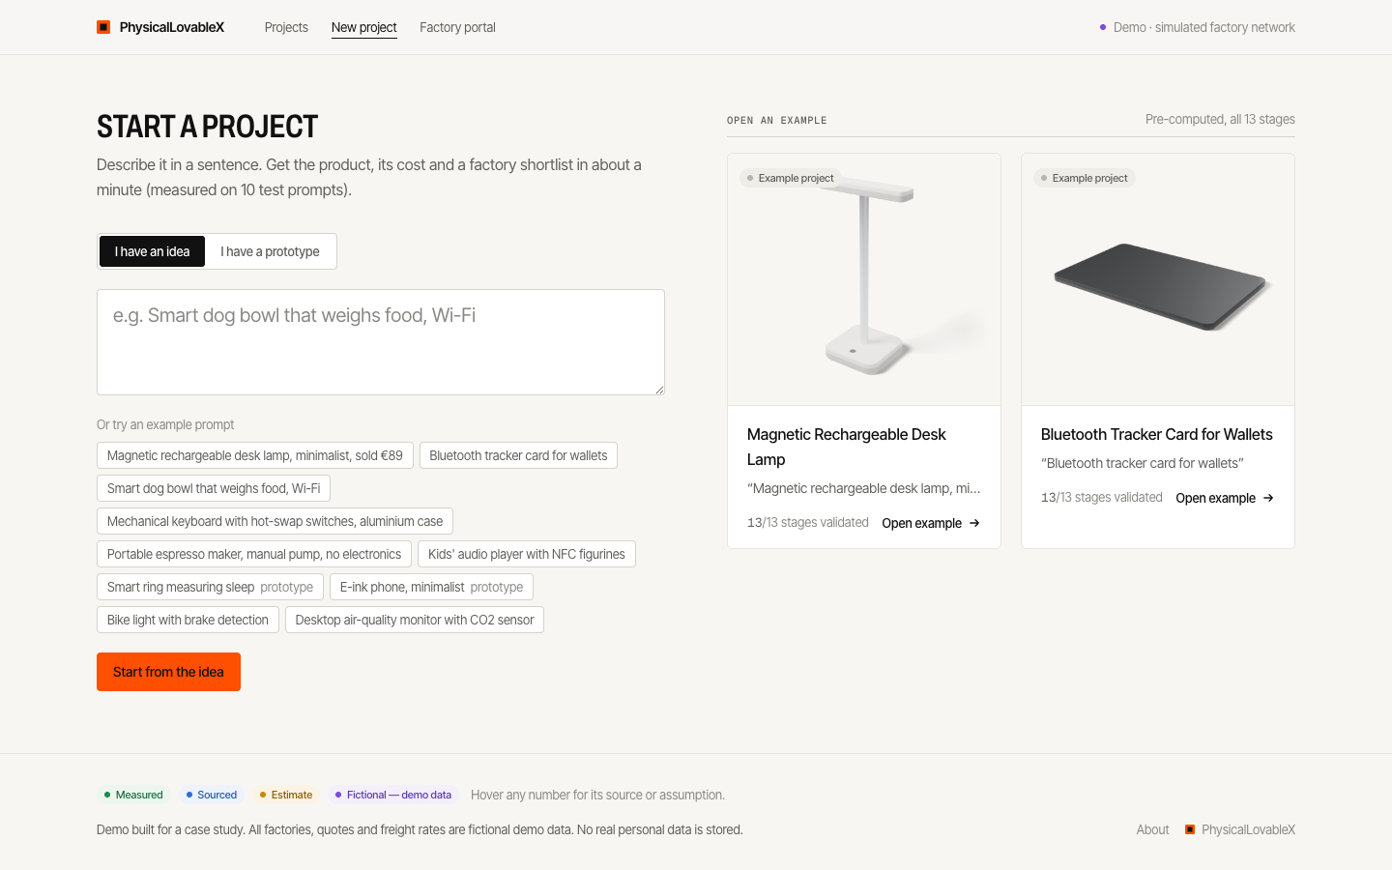
app/docs/screens/after/00_home.png
