orpheo28/physicallovablex/app/docs/screens/after/00_home_deeplink.png

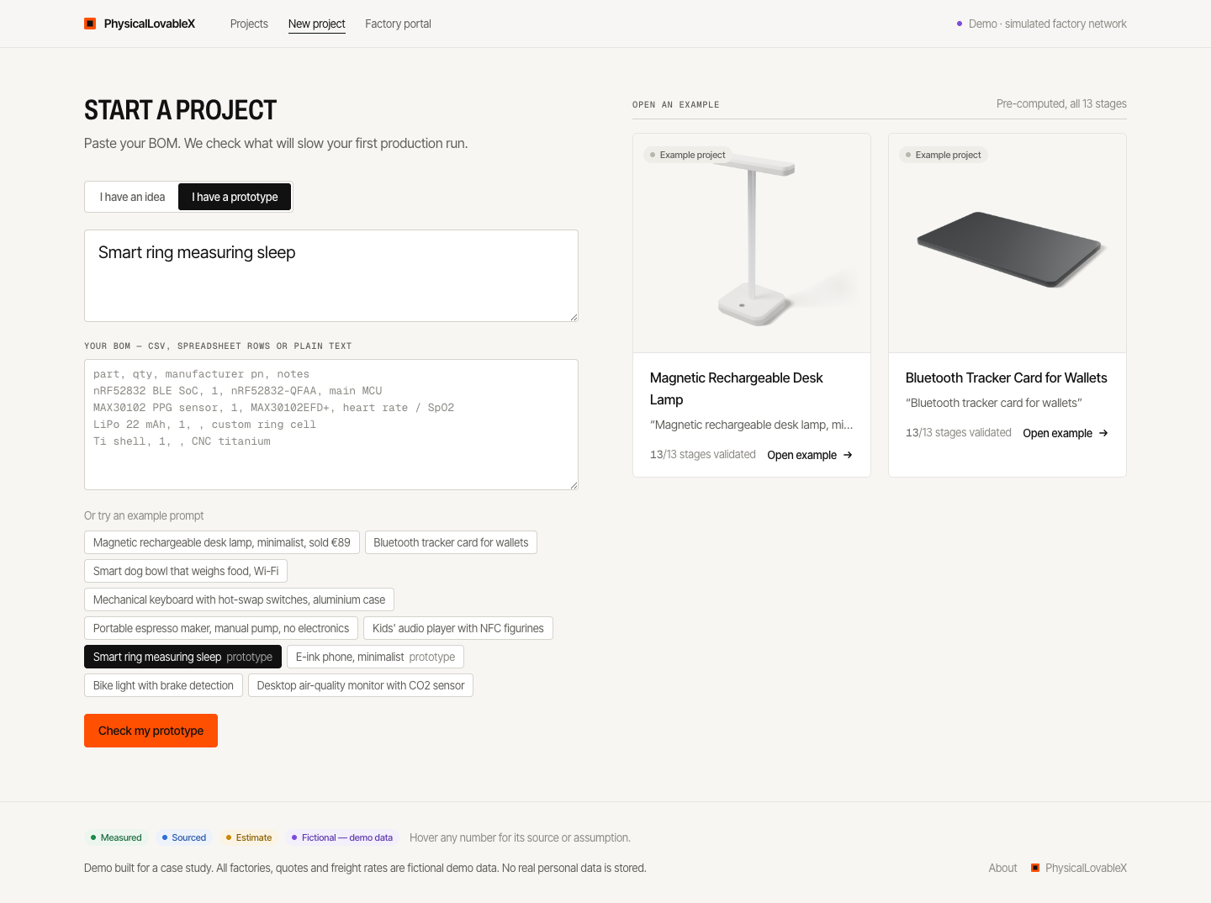
app/docs/screens/after/00_home_deeplink.png
