orpheo28/physicallovablex/app/docs/screens/after/01_wow_generated_cached.png

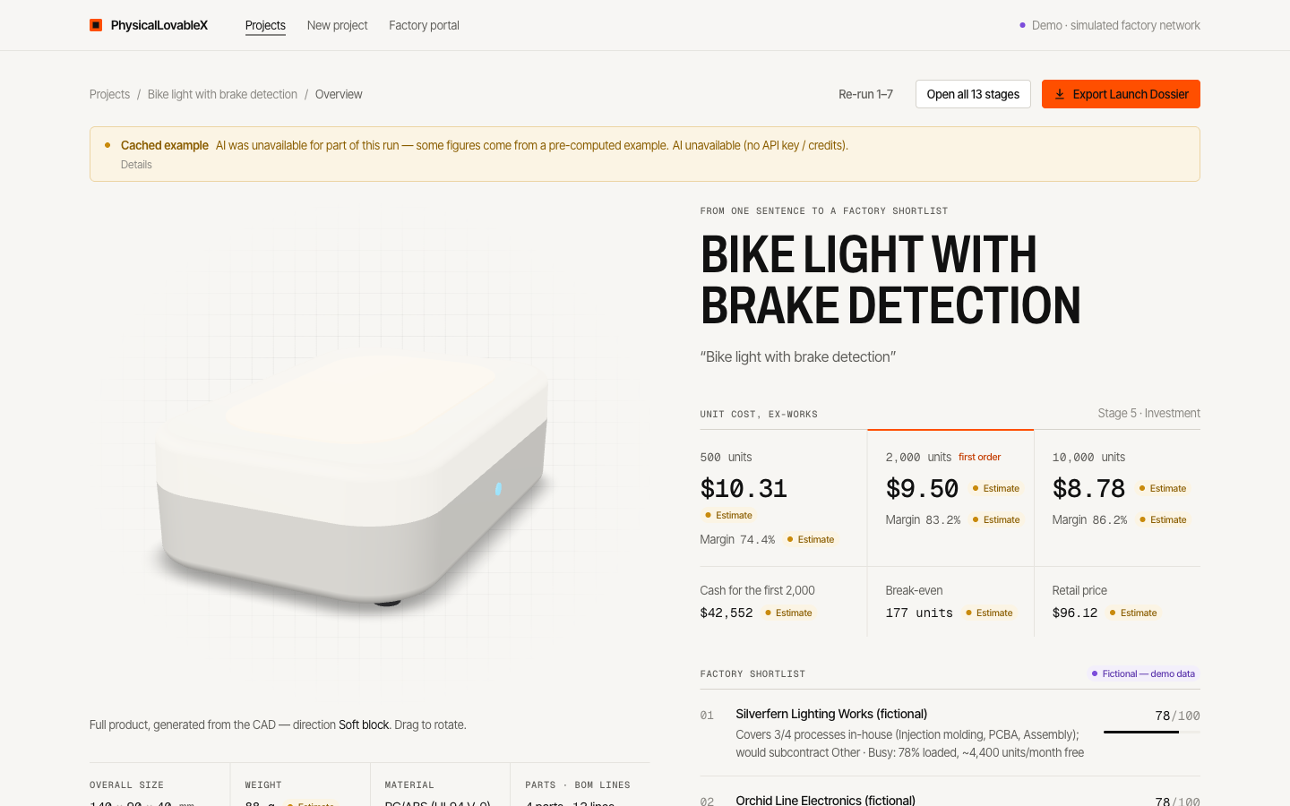
app/docs/screens/after/01_wow_generated_cached.png
