orpheo28/physicallovablex/app/docs/screens/after/01_wow_lamp.png

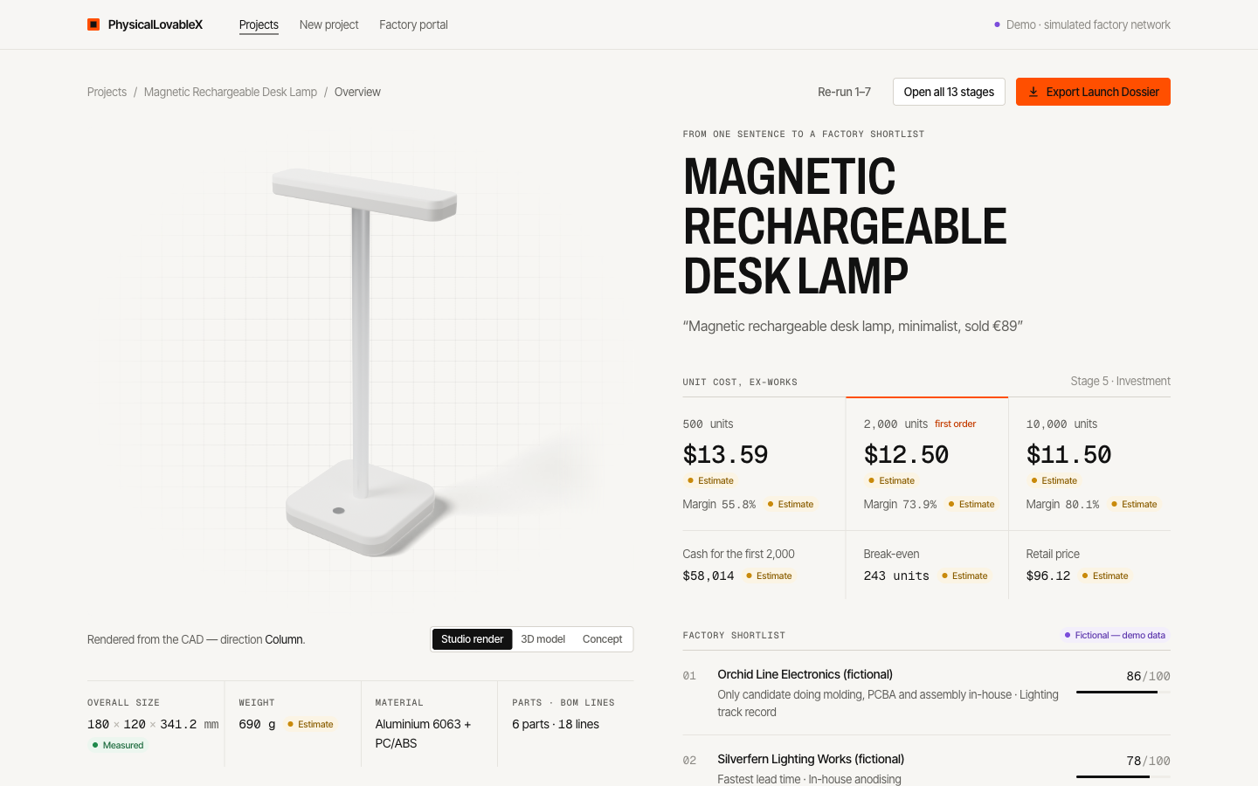
app/docs/screens/after/01_wow_lamp.png
