orpheo28/physicallovablex/app/docs/screens/after/01_wow_tracker.png

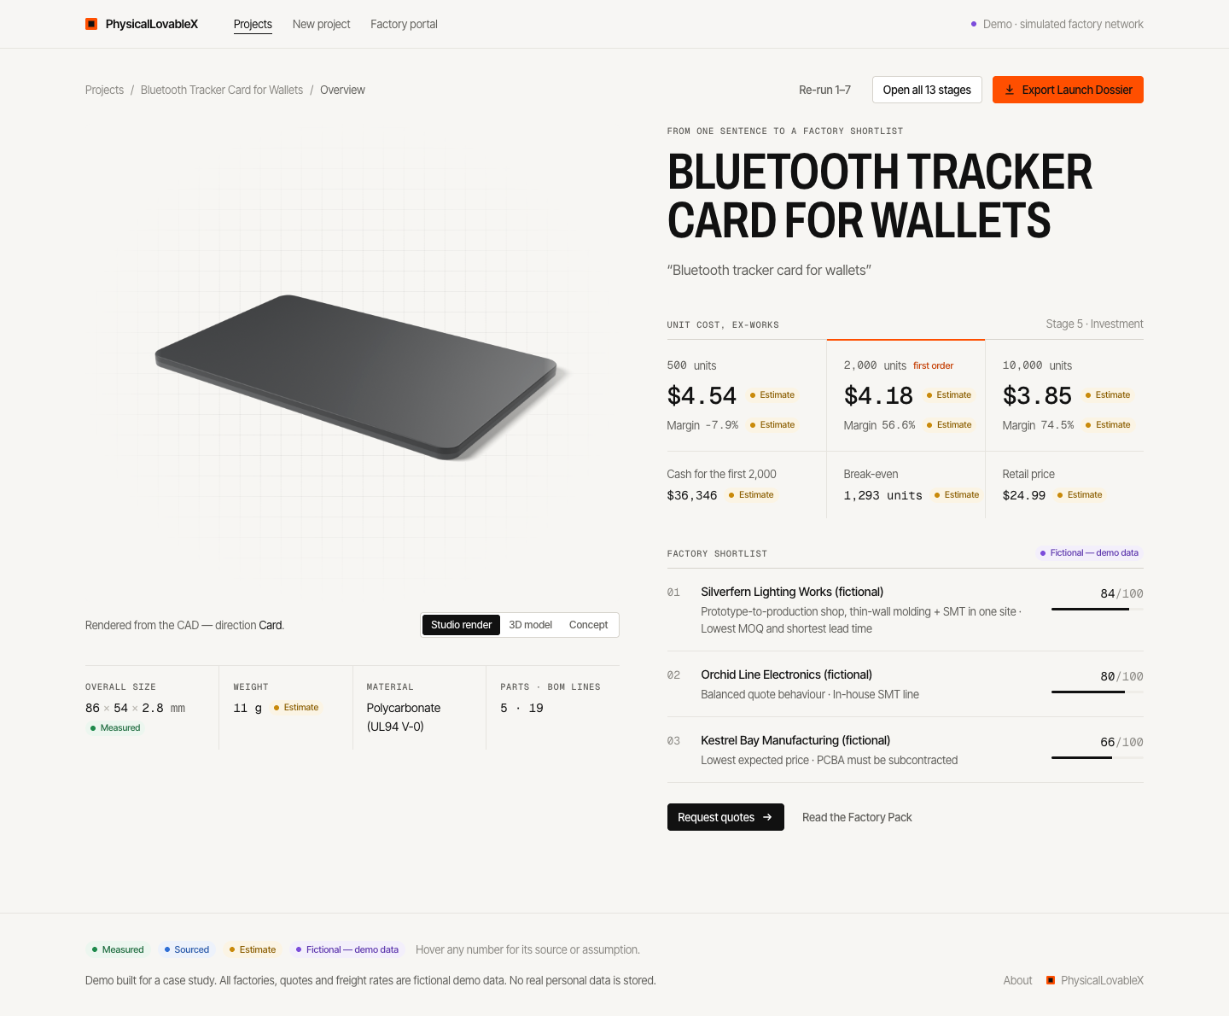
app/docs/screens/after/01_wow_tracker.png
