orpheo28/physicallovablex/app/docs/screens/after/02_about_landing_backup.png

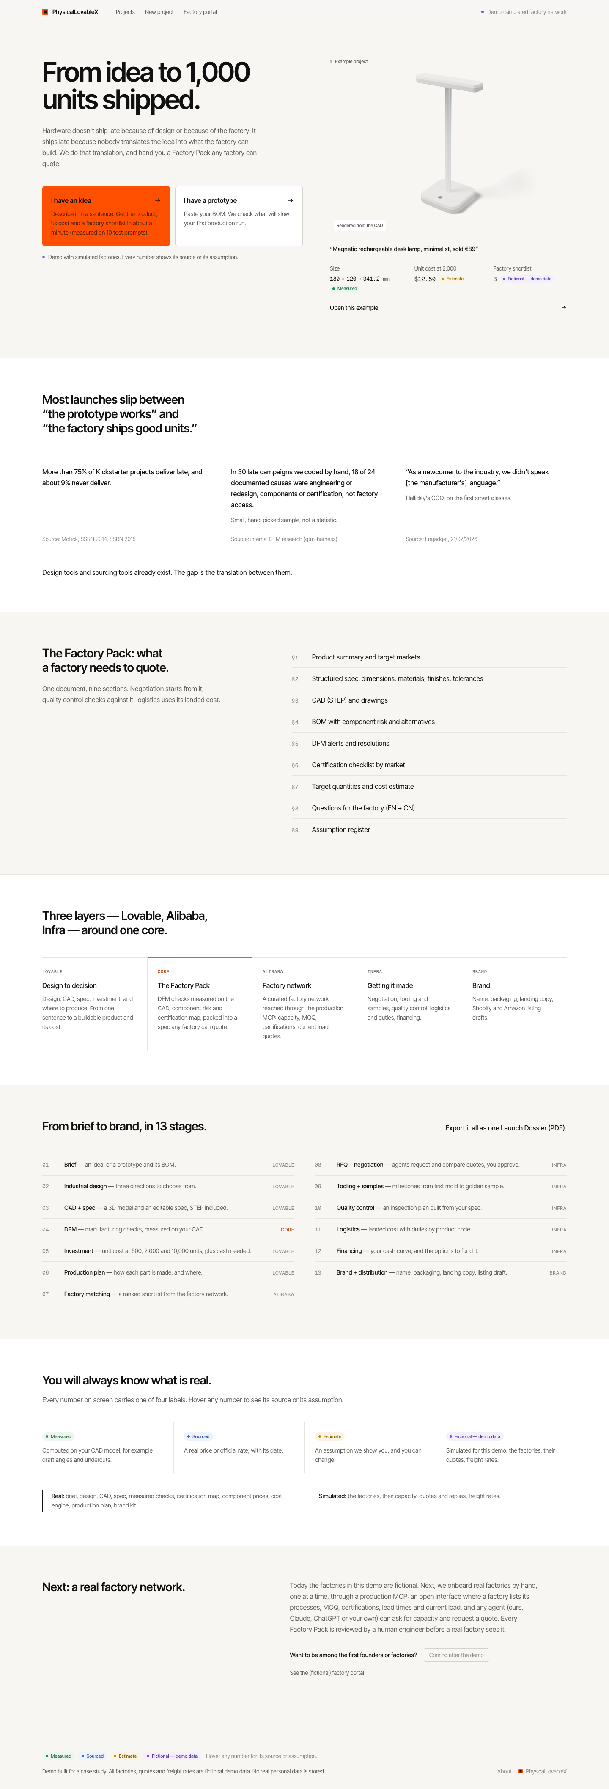
app/docs/screens/after/02_about_landing_backup.png
