orpheo28/physicallovablex/app/docs/screens/after/03_lamp_stage03.png

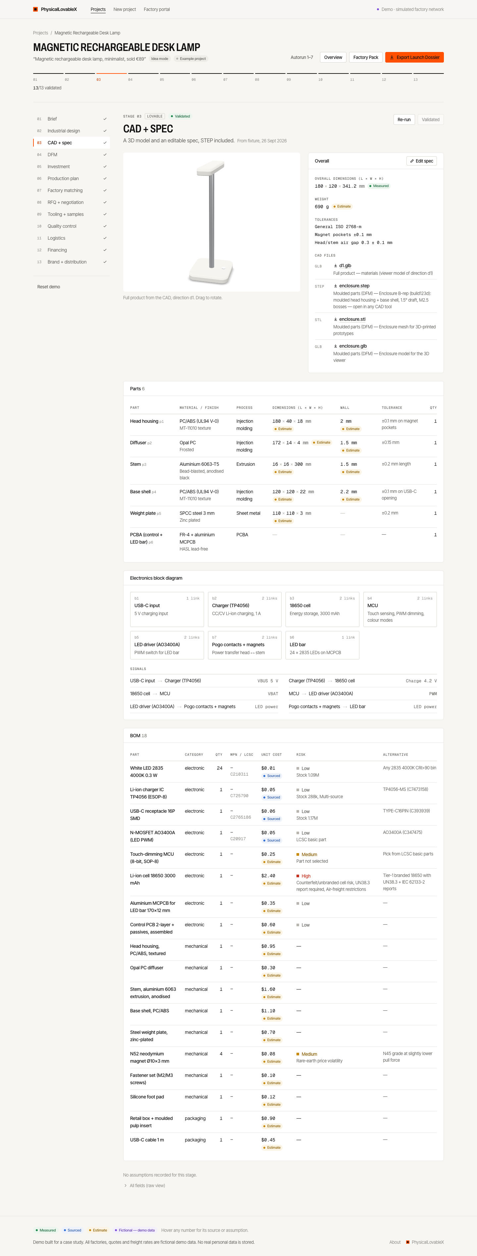
app/docs/screens/after/03_lamp_stage03.png
