orpheo28/physicallovablex/app/docs/screens/after/03_lamp_stage05.png

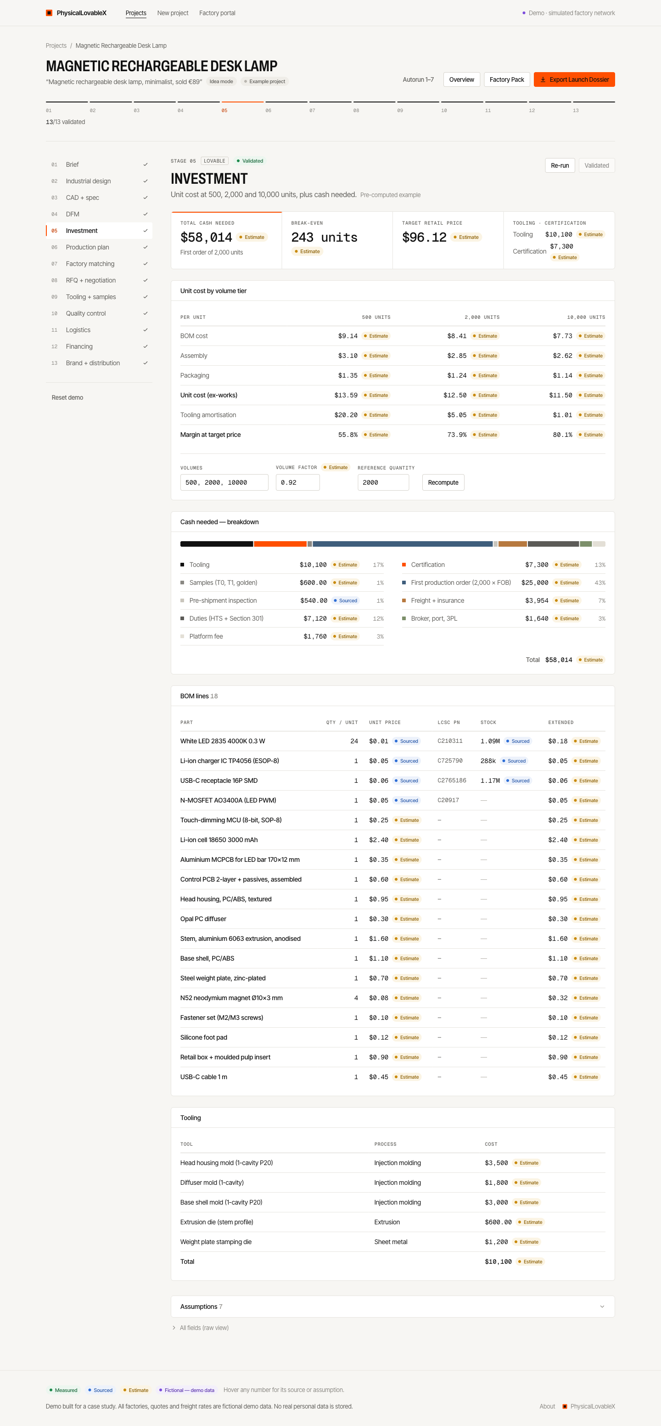
app/docs/screens/after/03_lamp_stage05.png
