orpheo28/physicallovablex/app/docs/screens/after/03_lamp_stage06.png

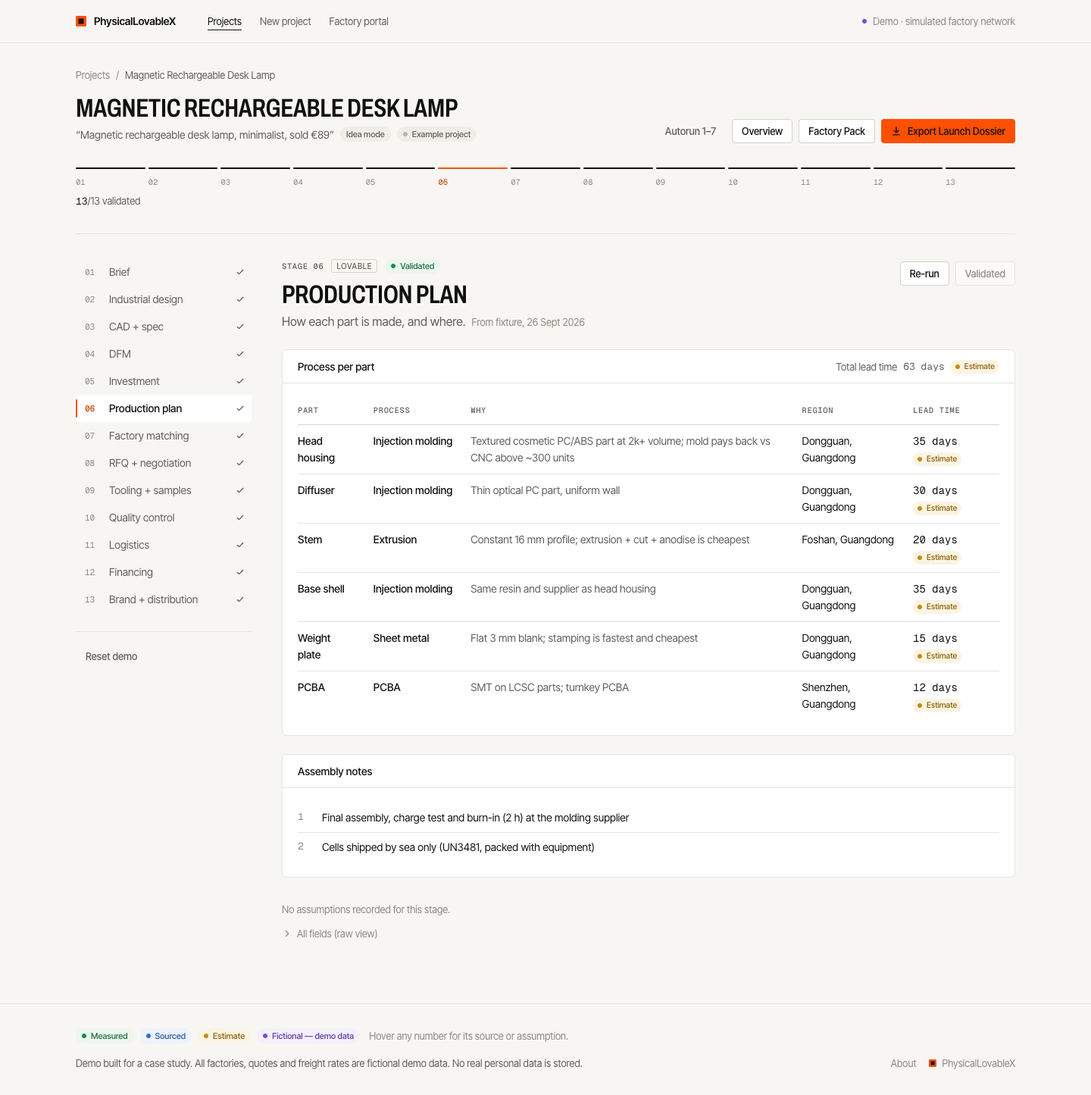
app/docs/screens/after/03_lamp_stage06.png
