orpheo28/physicallovablex/app/docs/screens/after/03_lamp_stage11.png

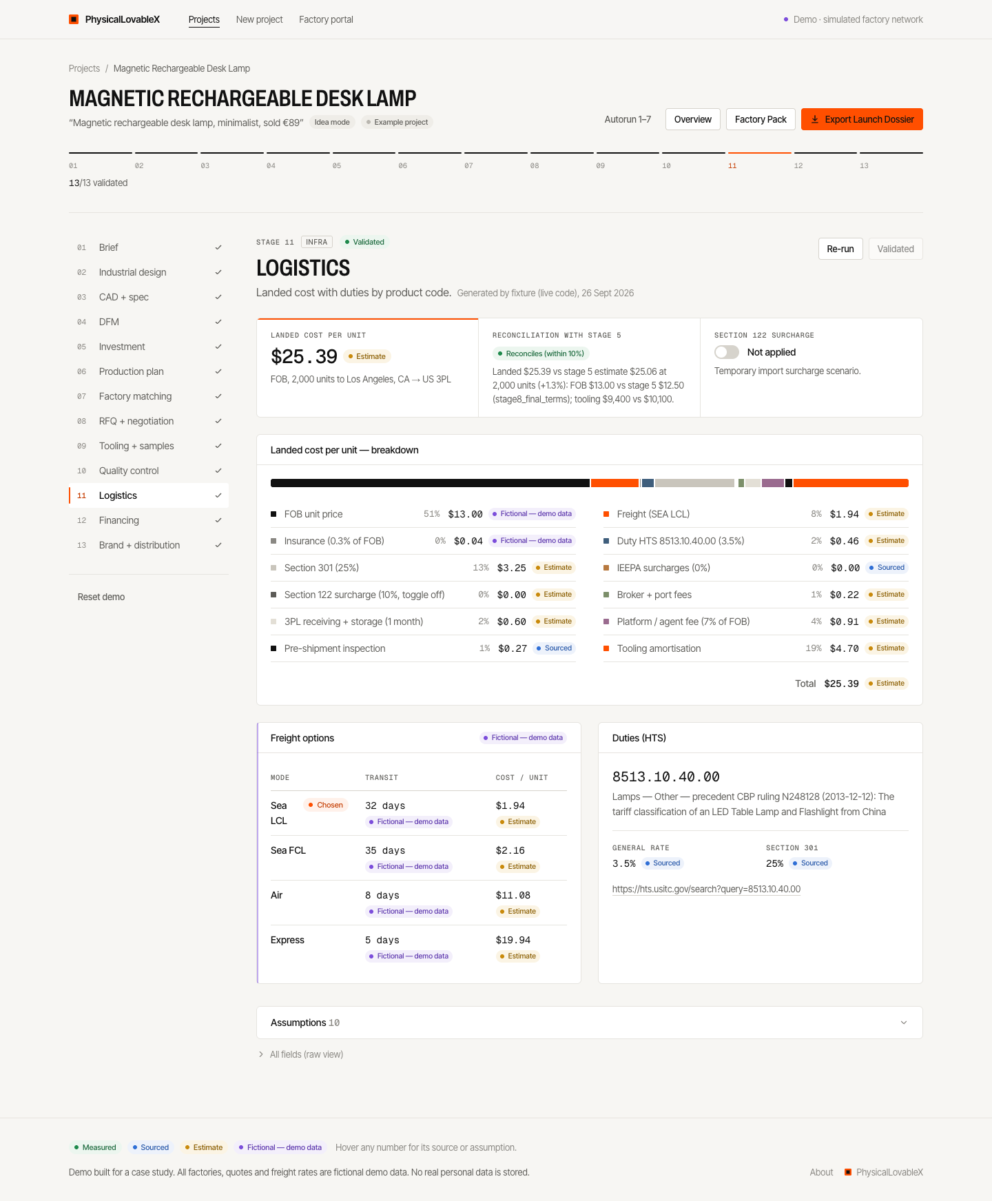
app/docs/screens/after/03_lamp_stage11.png
