orpheo28/physicallovablex/app/docs/screens/after/03_tracker_stage05.png

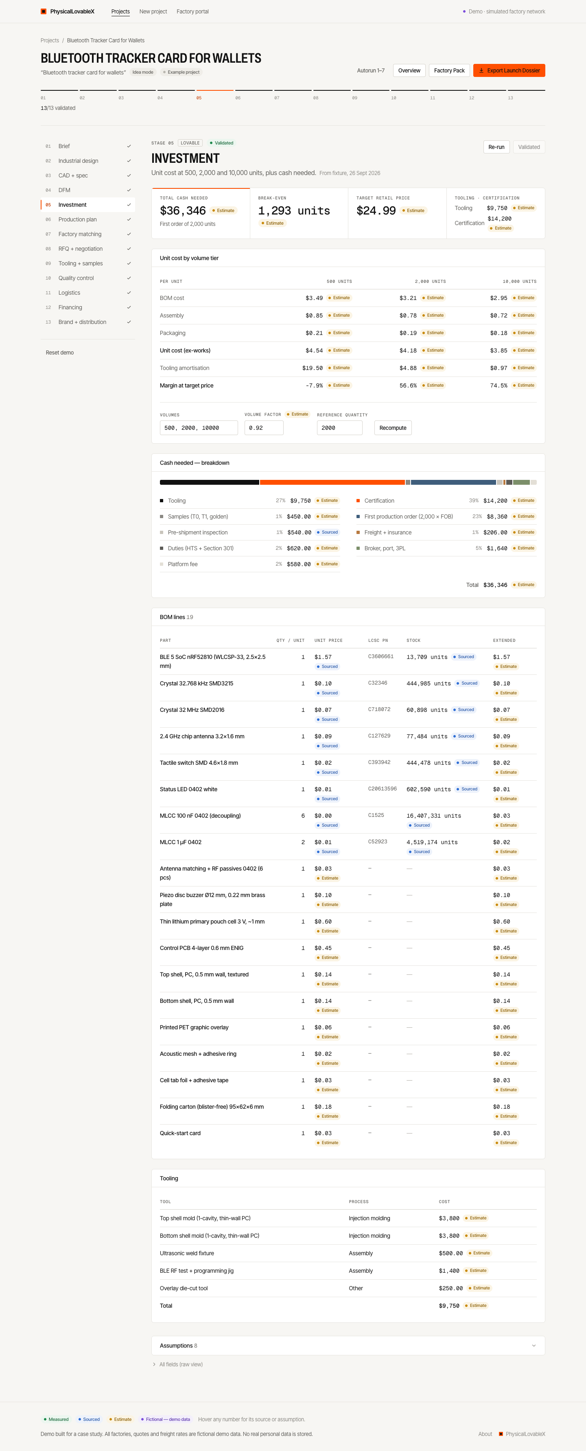
app/docs/screens/after/03_tracker_stage05.png
