orpheo28/physicallovablex/app/docs/screens/after/03_tracker_stage11.png

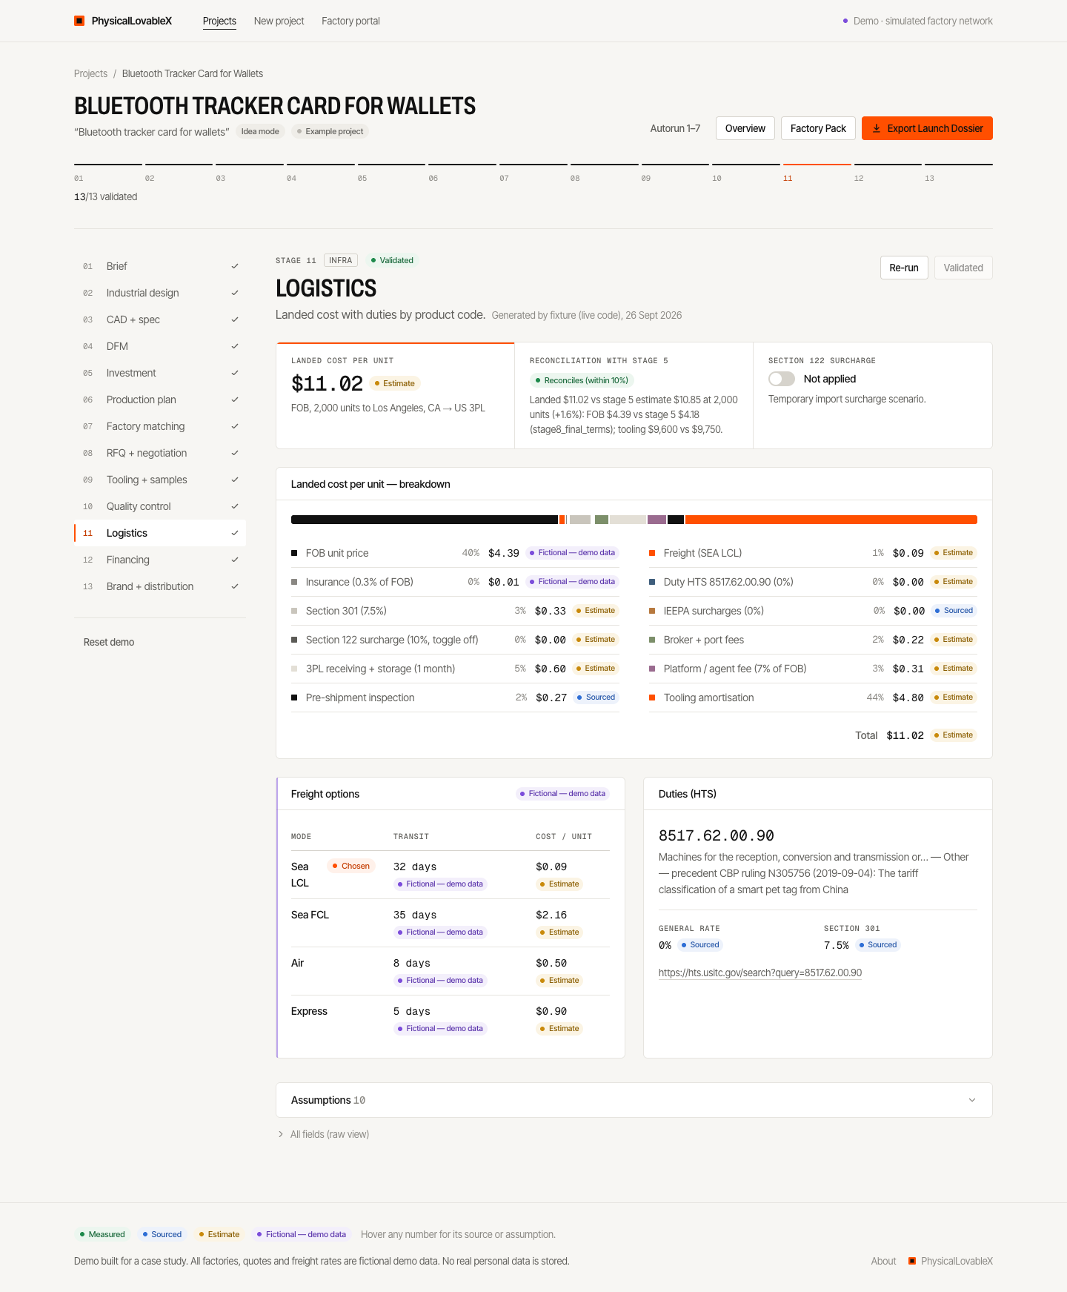
app/docs/screens/after/03_tracker_stage11.png
