orpheo28/physicallovablex/app/docs/screens/after/04_factory_pack_lamp.png

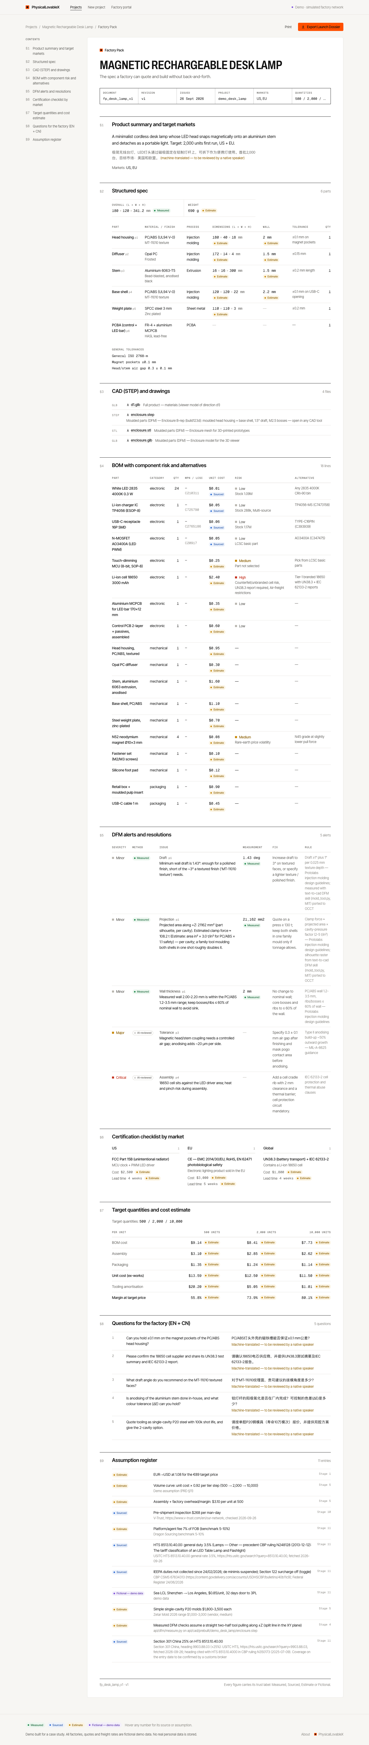
app/docs/screens/after/04_factory_pack_lamp.png
