orpheo28/physicallovablex/app/docs/screens/after/05_factories.png

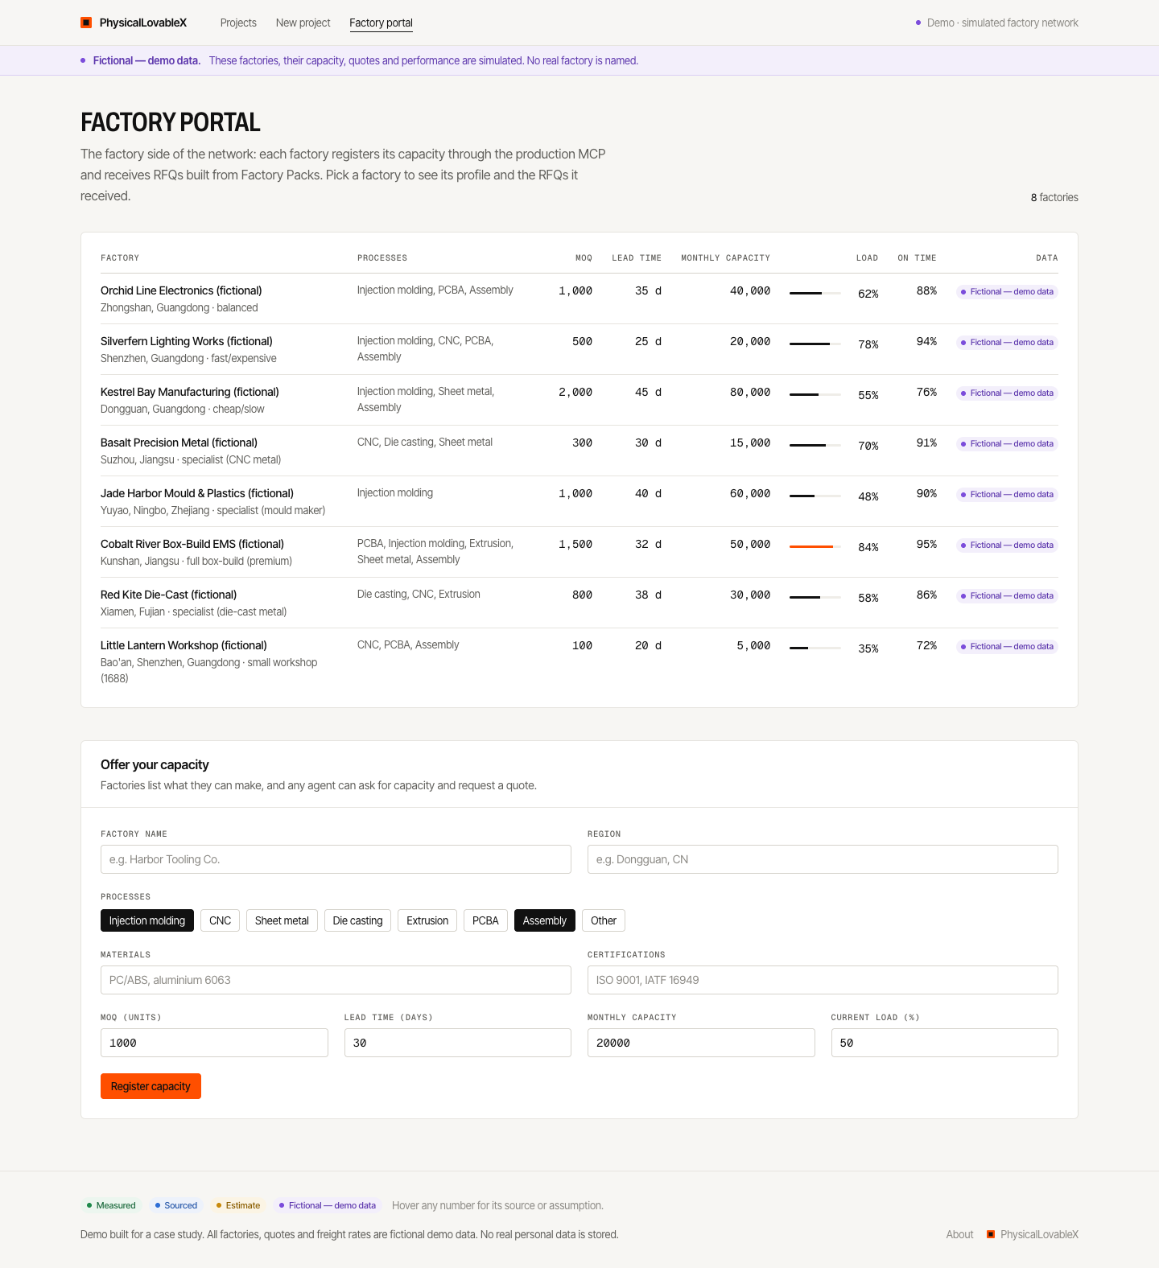
app/docs/screens/after/05_factories.png
