orpheo28/physicallovablex/app/docs/screens/after/05_factories_offer_capacity.png

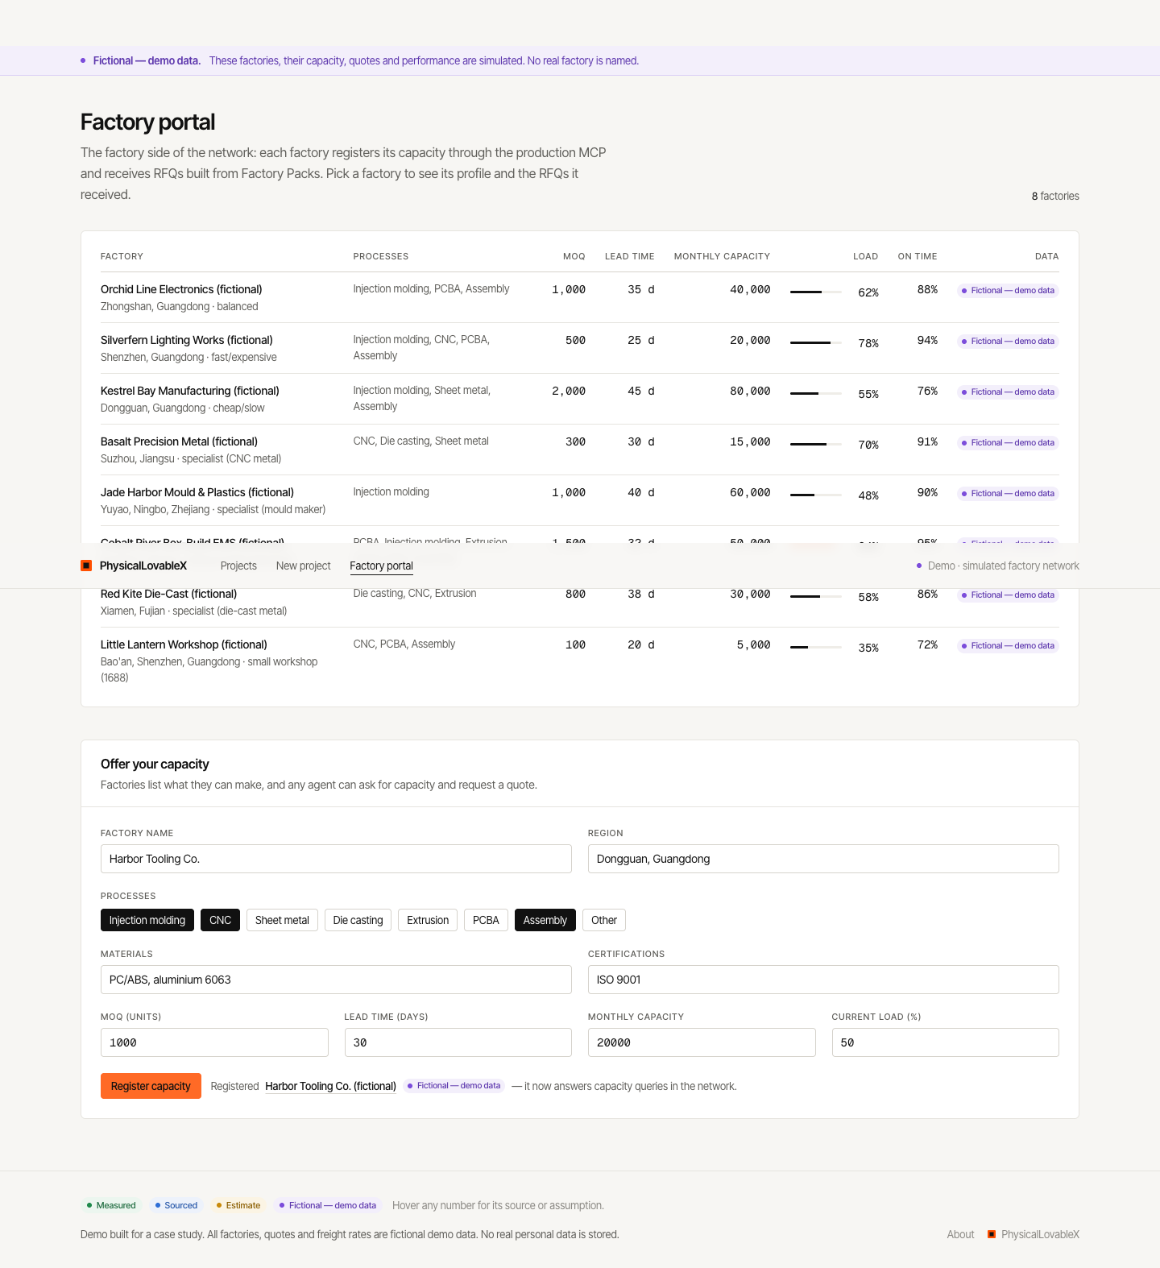
app/docs/screens/after/05_factories_offer_capacity.png
