orpheo28/physicallovablex/app/docs/screens/after/05_factory_orchid.png

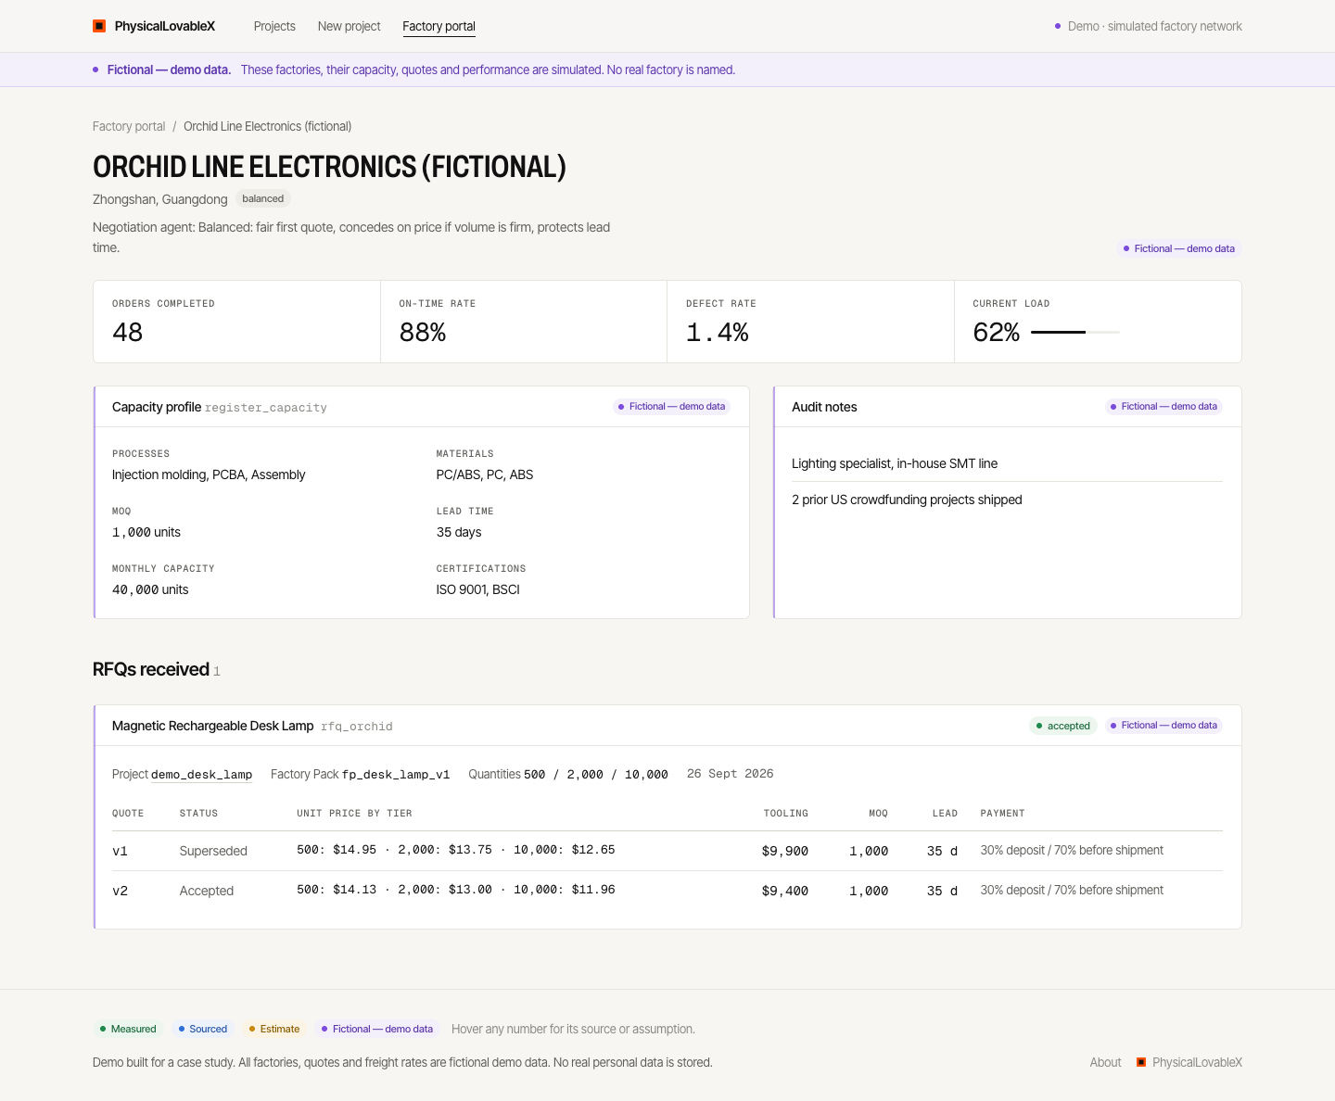
app/docs/screens/after/05_factory_orchid.png
