orpheo28/physicallovablex/app/docs/screens/after/06_new.png

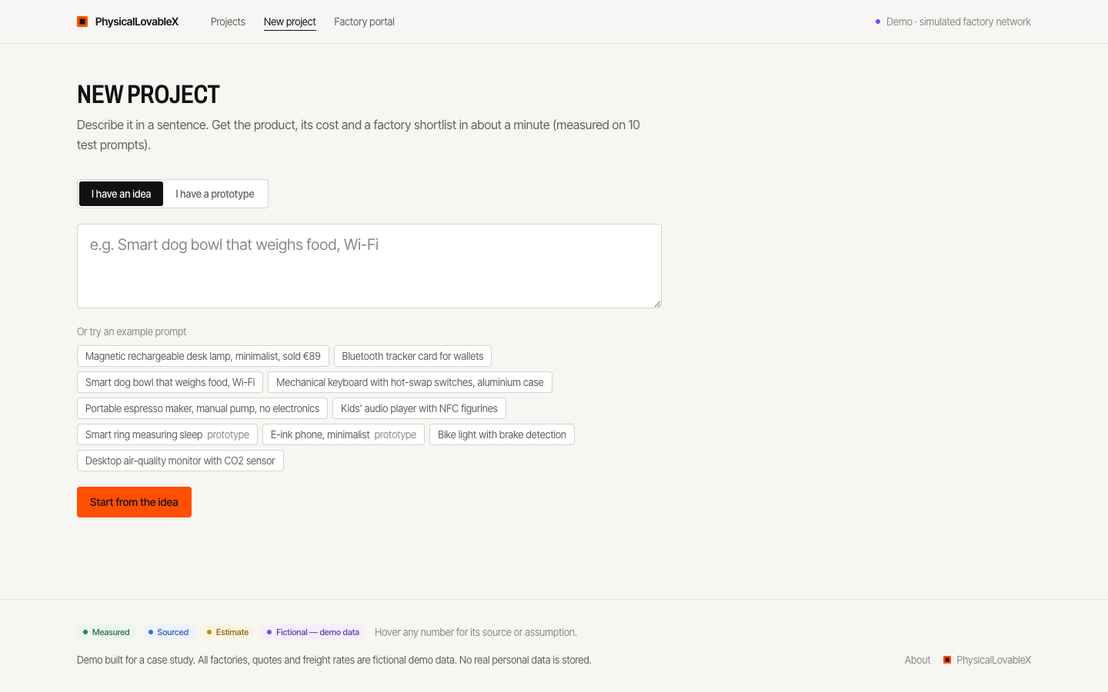
app/docs/screens/after/06_new.png
