orpheo28/physicallovablex/app/docs/screens/after/07_projects.png

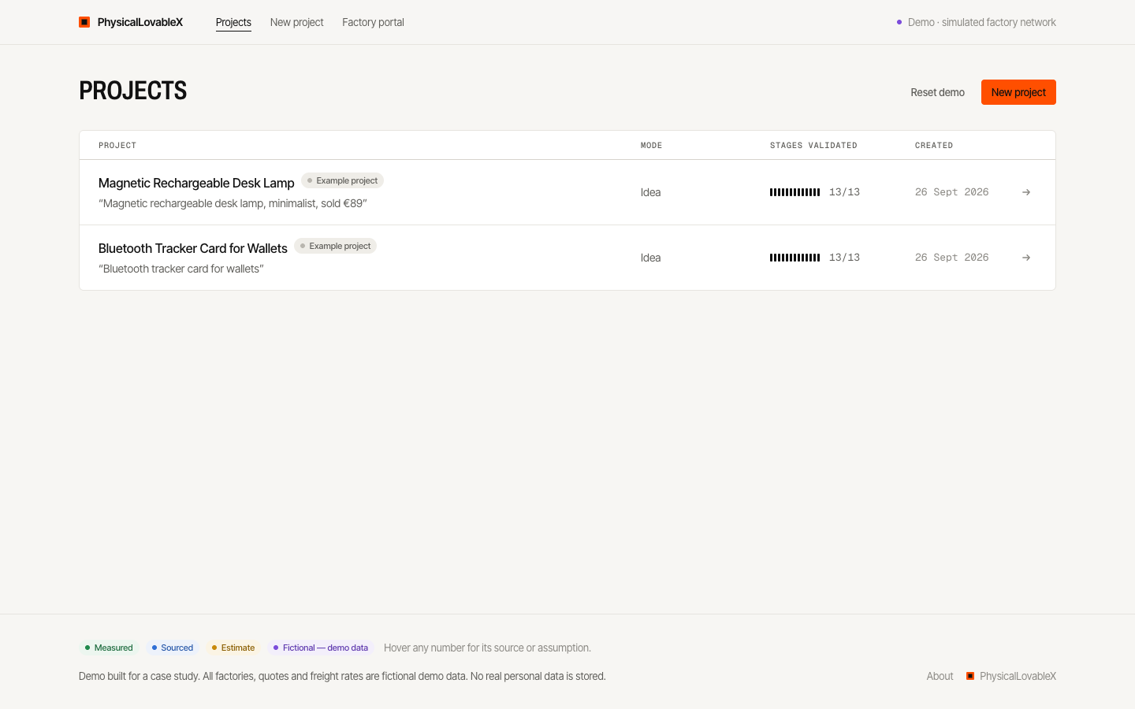
app/docs/screens/after/07_projects.png
