orpheo28/physicallovablex/app/docs/screens/after/08_live_03_wow_dog_bowl.png

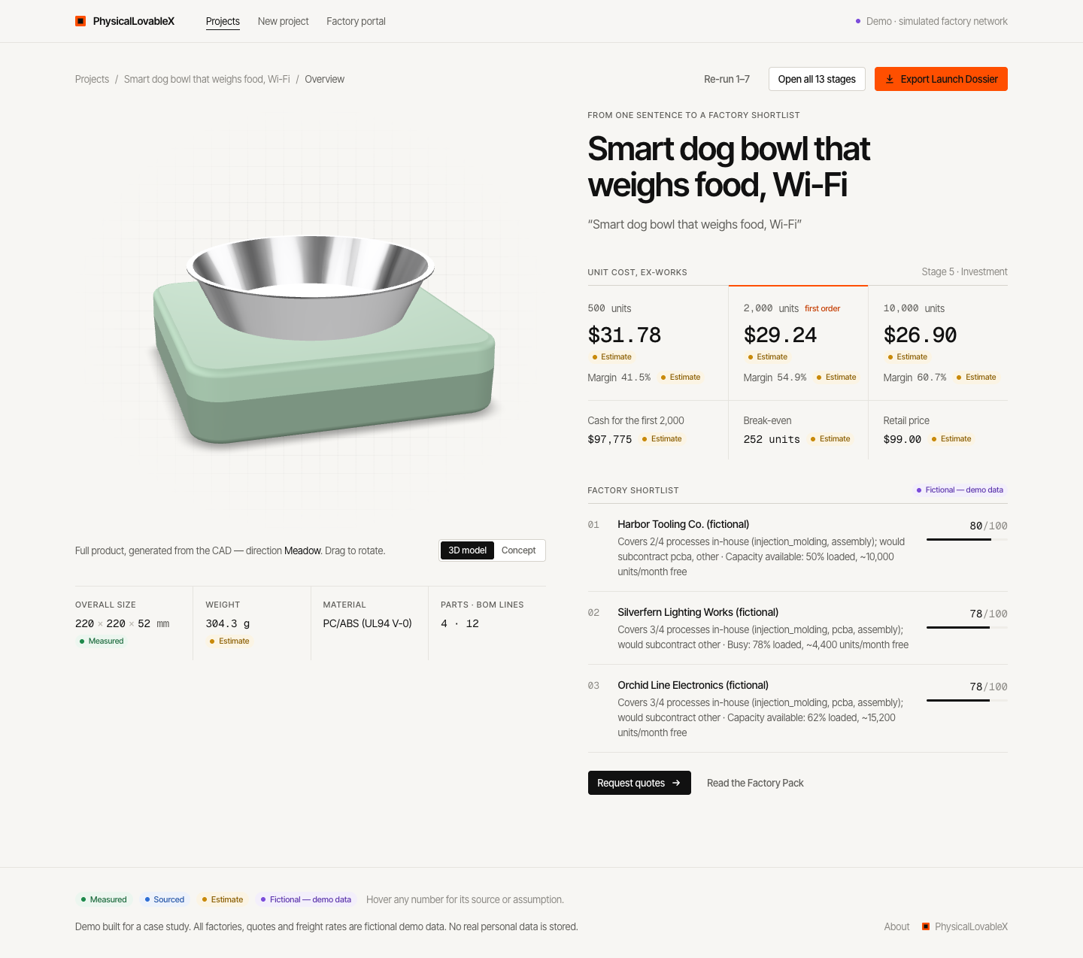
app/docs/screens/after/08_live_03_wow_dog_bowl.png
