orpheo28/physicallovablex/app/docs/screens/after/08_live_04_stage2_dog_bowl.png

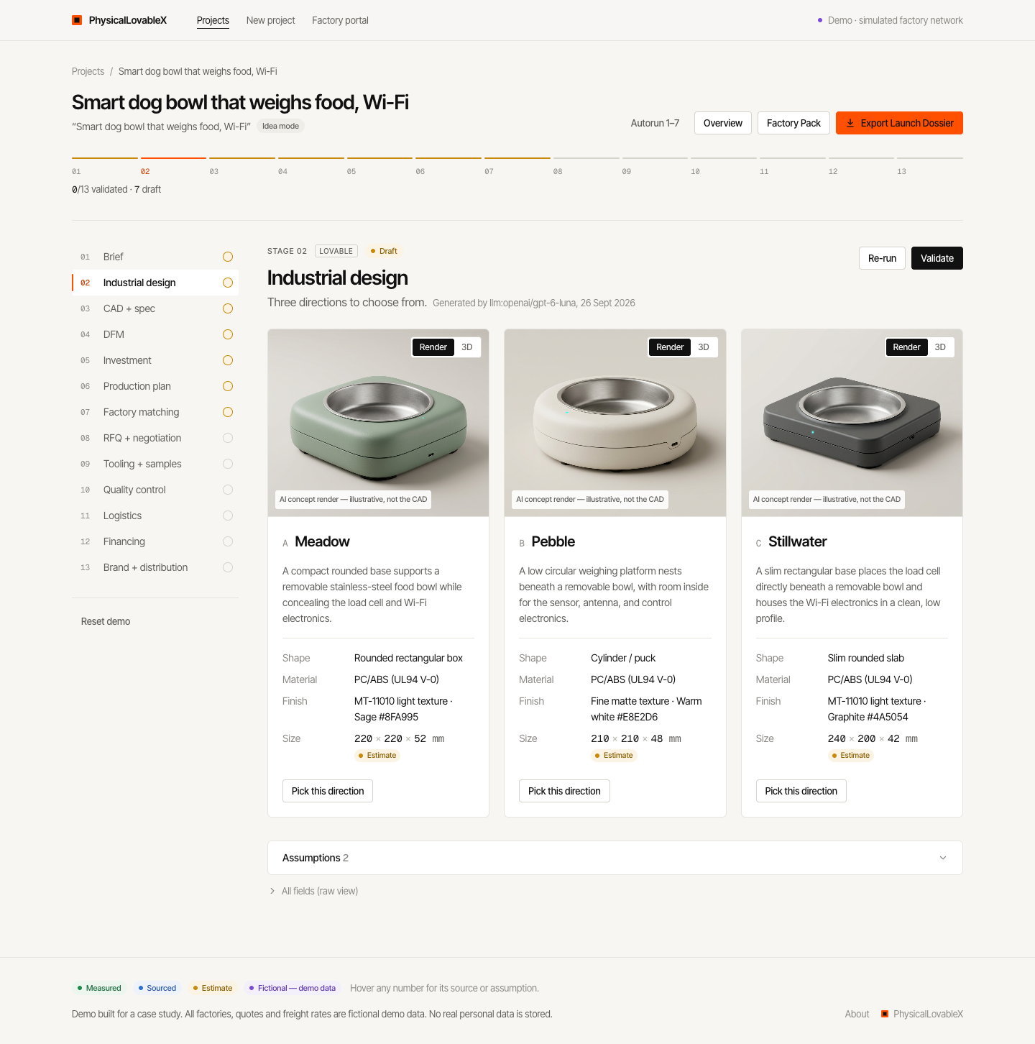
app/docs/screens/after/08_live_04_stage2_dog_bowl.png
