orpheo28/physicallovablex/app/docs/screens/after/08_live_05_stage3_dog_bowl.png

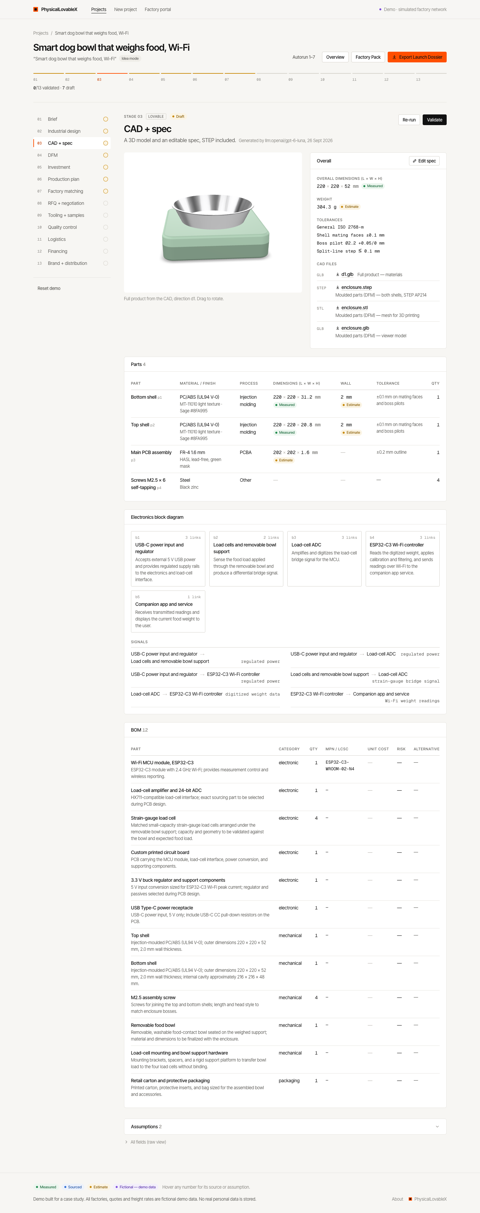
app/docs/screens/after/08_live_05_stage3_dog_bowl.png
