orpheo28/physicallovablex/app/docs/screens/after/09_stage2_render_busy.png

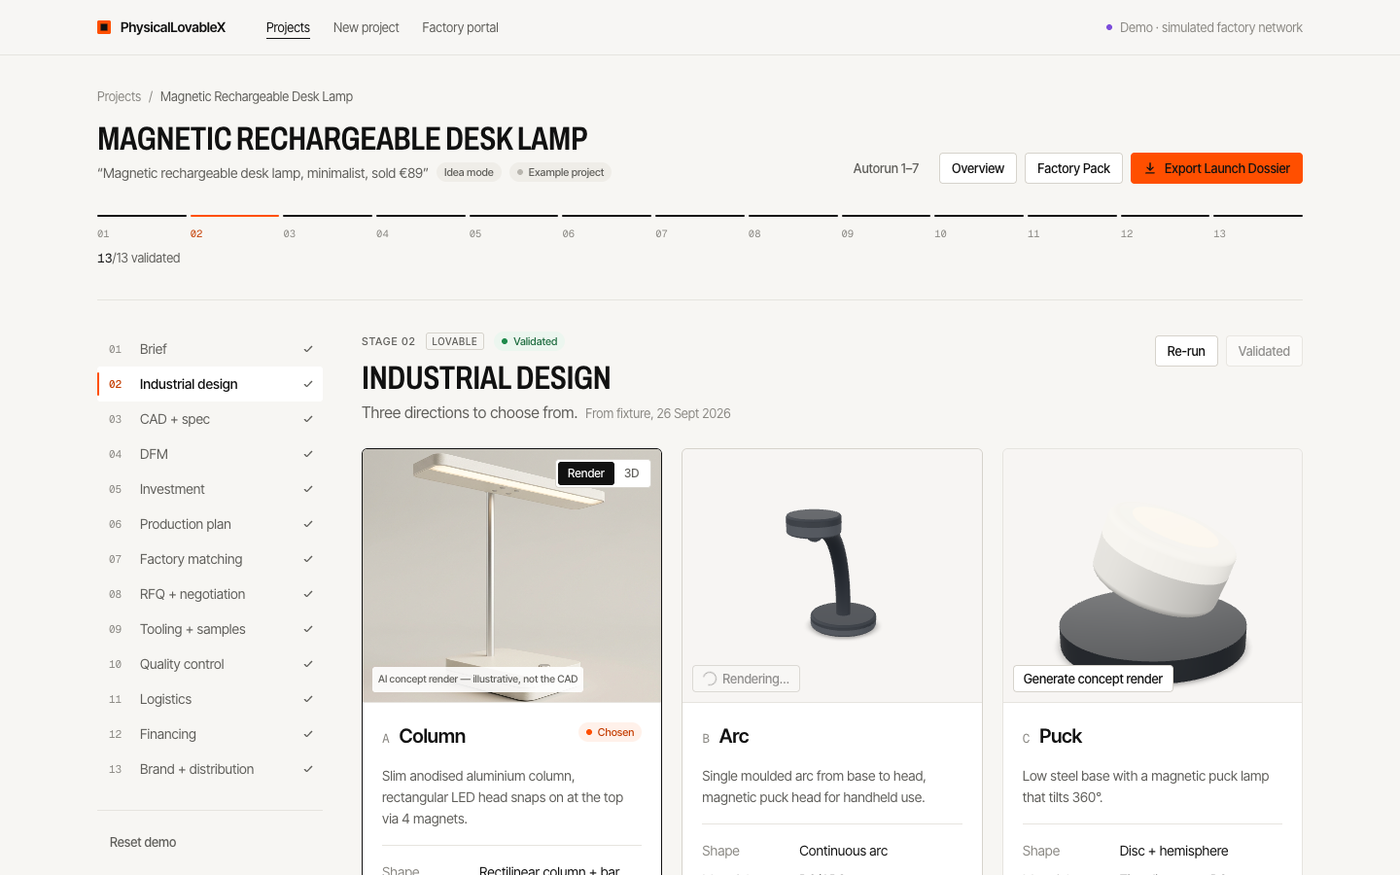
app/docs/screens/after/09_stage2_render_busy.png
