orpheo28/physicallovablex/app/docs/screens/after/09_stage2_render_done.png

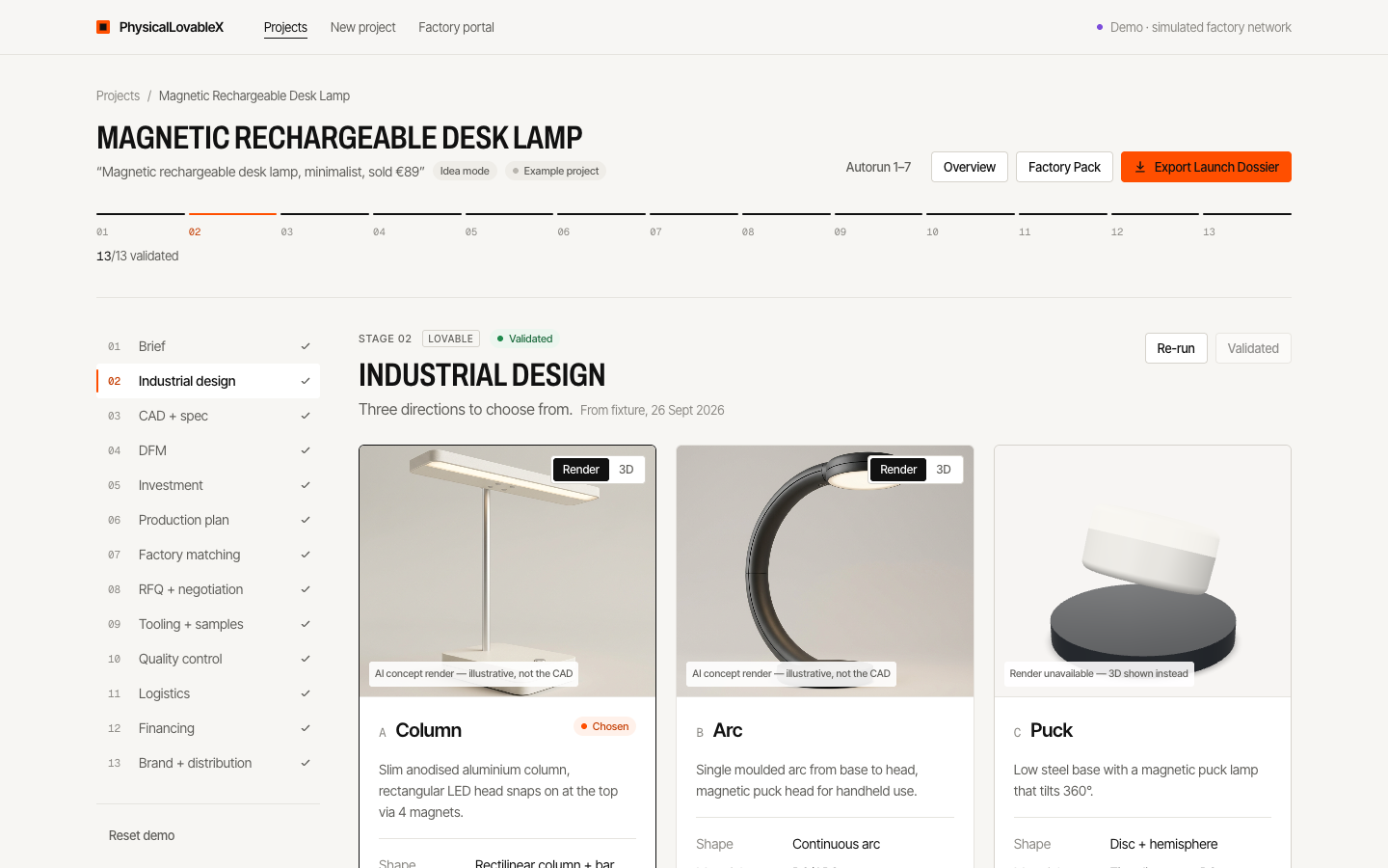
app/docs/screens/after/09_stage2_render_done.png
