orpheo28/physicallovablex/app/docs/screens/after/10_login.png

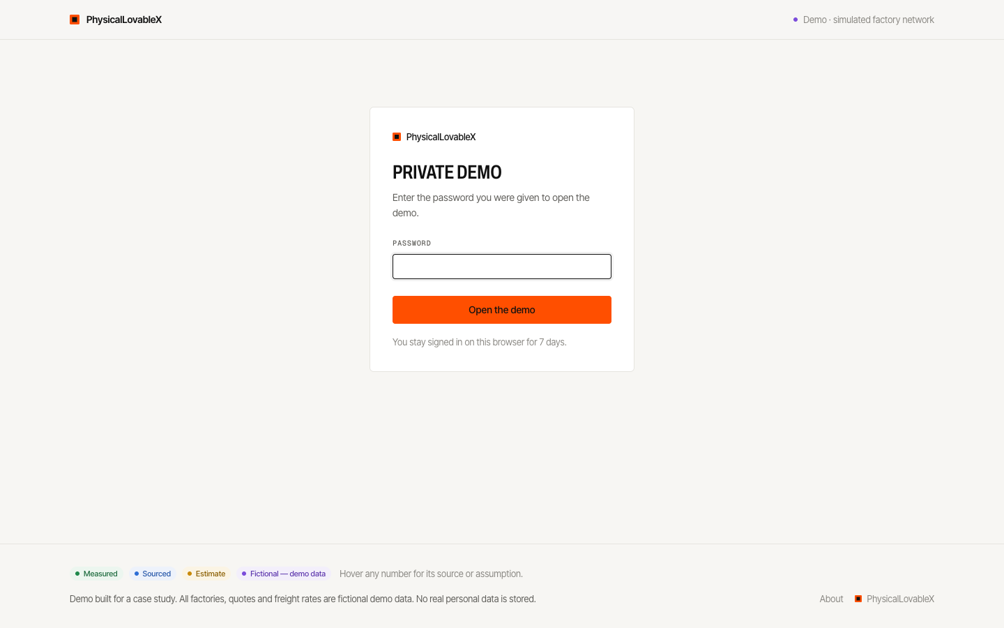
app/docs/screens/after/10_login.png
