orpheo28/physicallovablex/app/docs/screens/before/01_wow_lamp.png

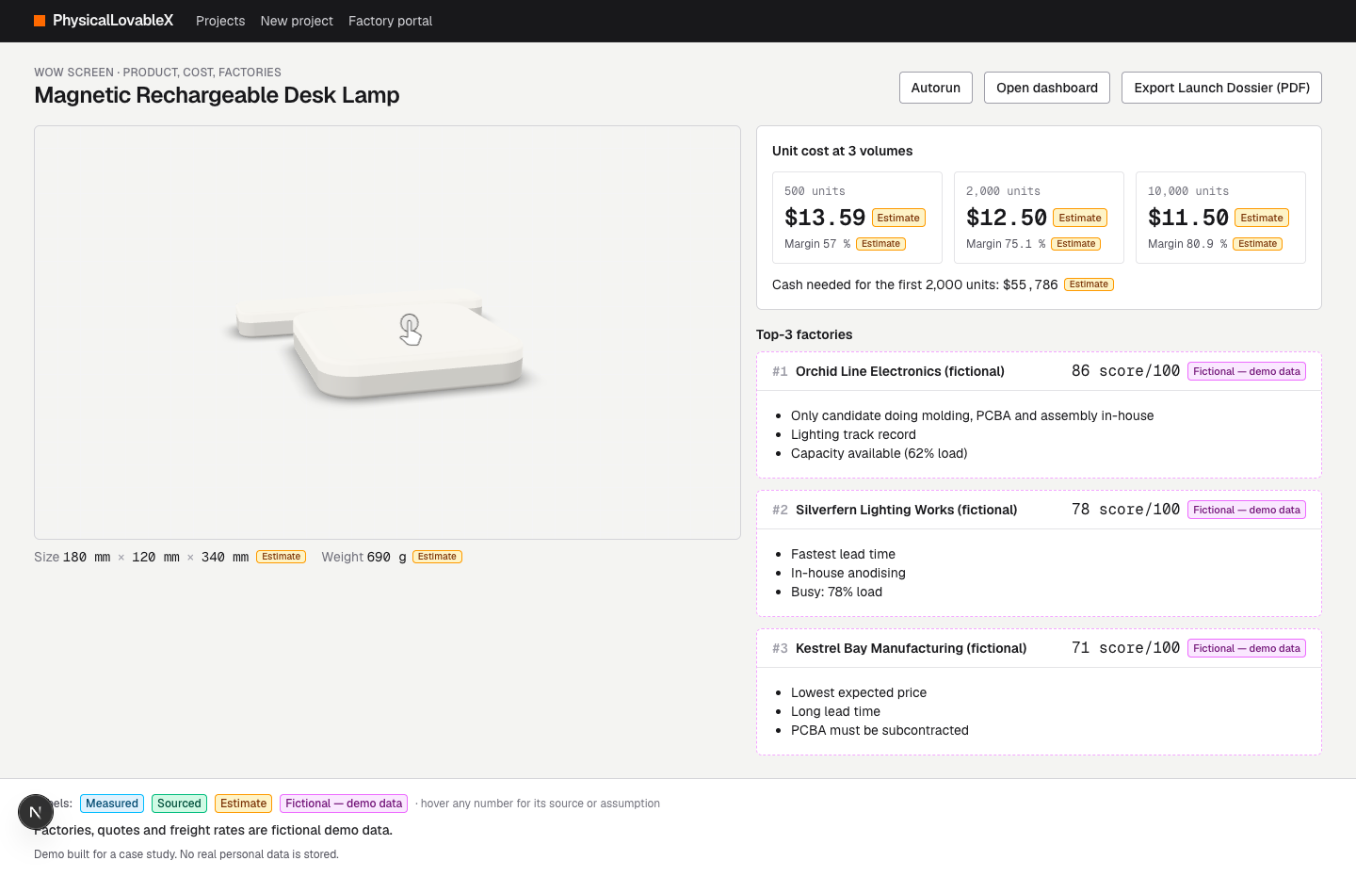
app/docs/screens/before/01_wow_lamp.png
