orpheo28/physicallovablex/app/docs/screens/before/02_landing.png

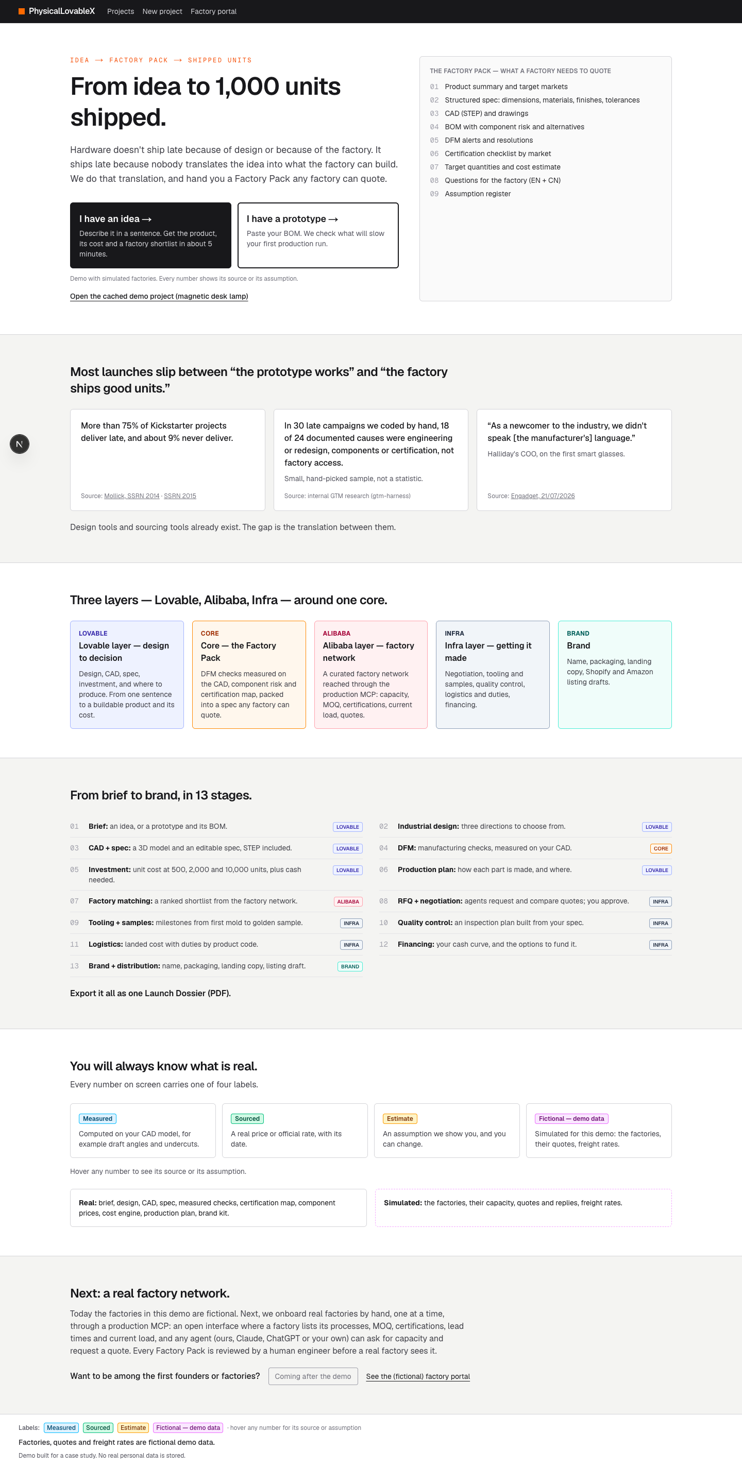
app/docs/screens/before/02_landing.png
