orpheo28/physicallovablex/app/docs/screens/before/03_dashboard_s2.png

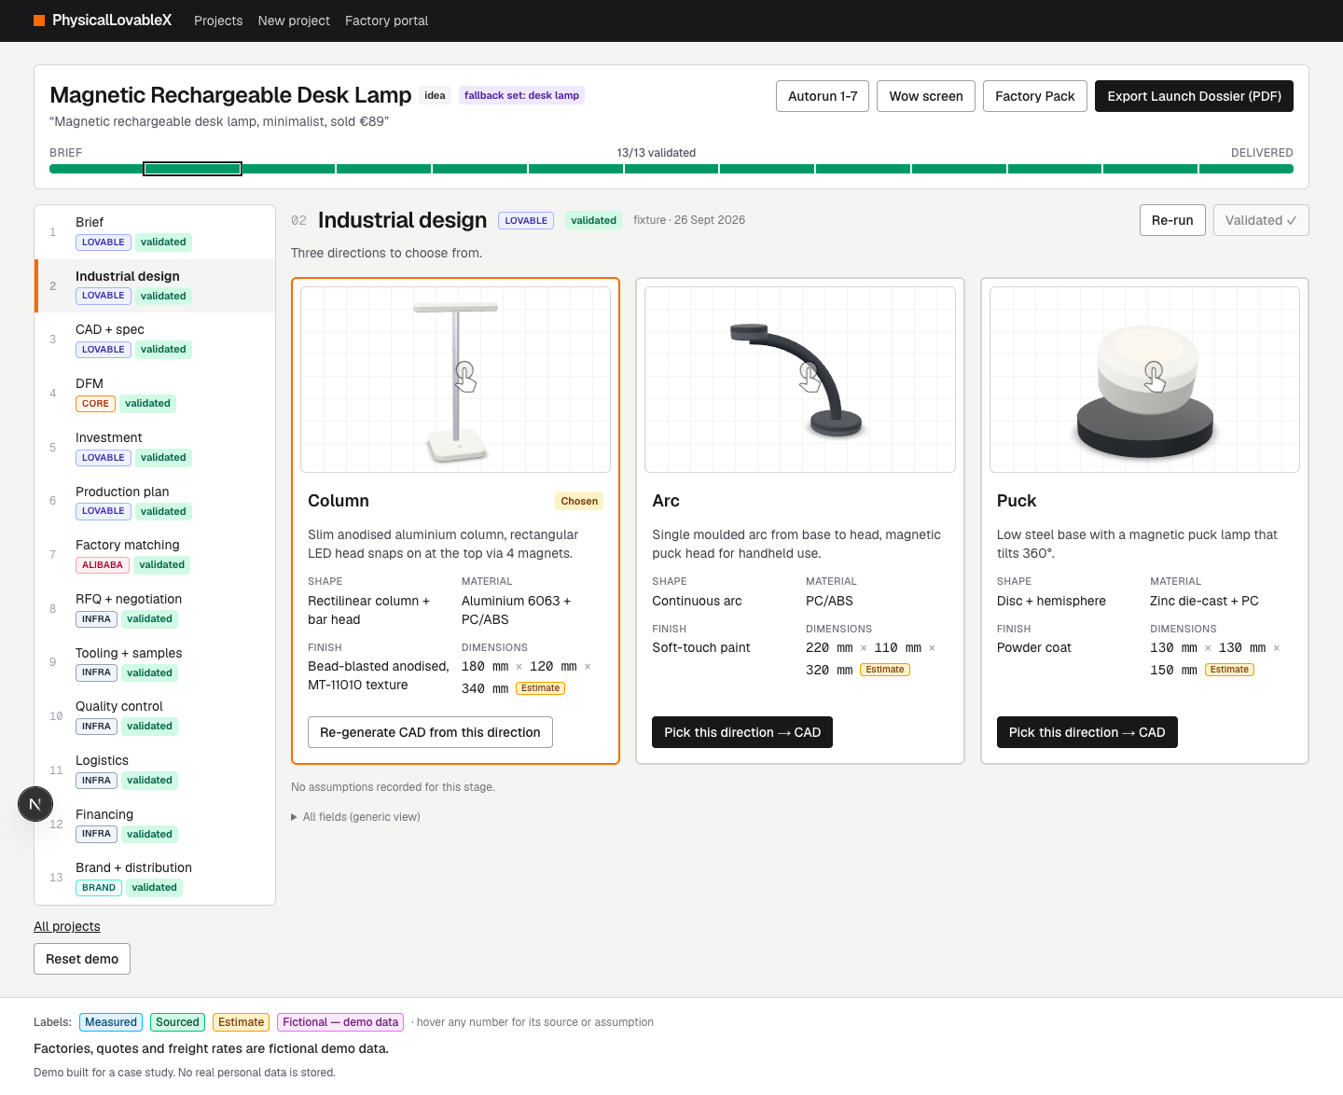
app/docs/screens/before/03_dashboard_s2.png
