orpheo28/physicallovablex/app/docs/screens/before/03_dashboard_s3.png

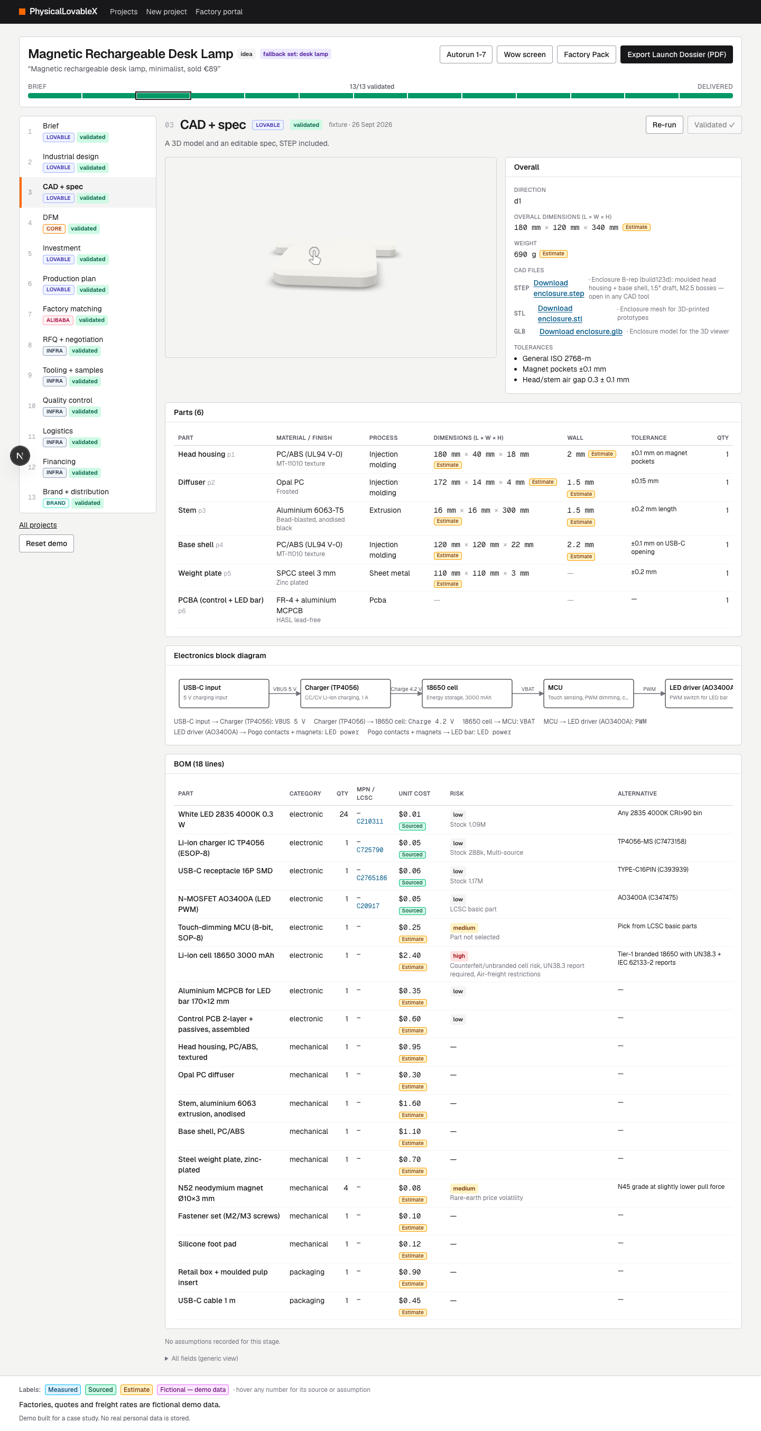
app/docs/screens/before/03_dashboard_s3.png
