orpheo28/physicallovablex/app/docs/screens/before/03_s4.png

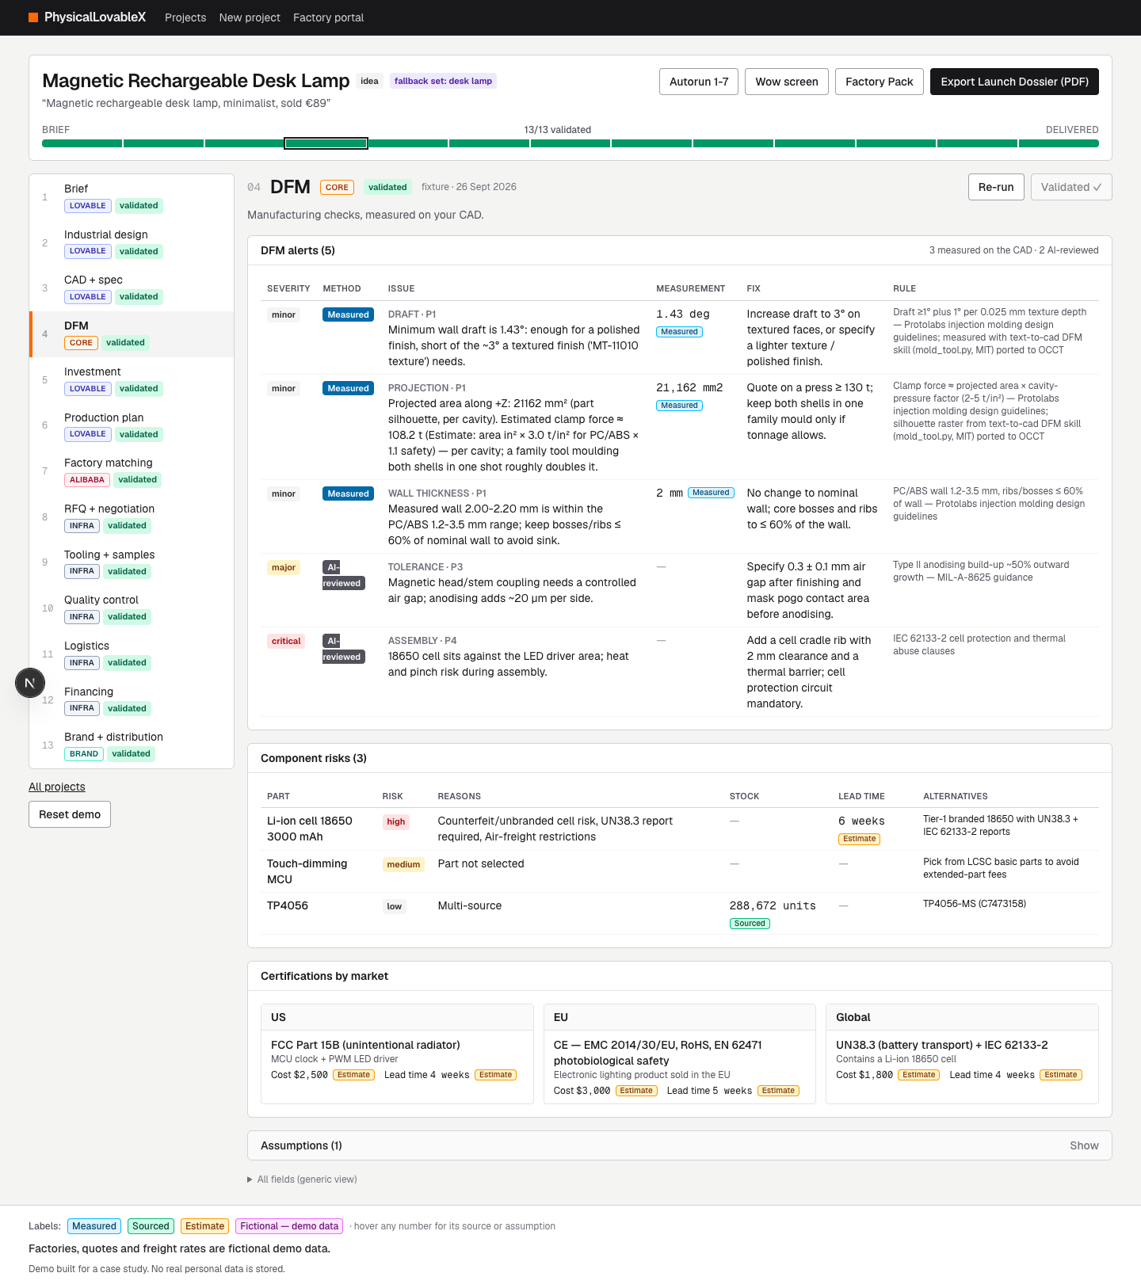
app/docs/screens/before/03_s4.png
