orpheo28/physicallovablex/app/docs/screens/before/03_s5.png

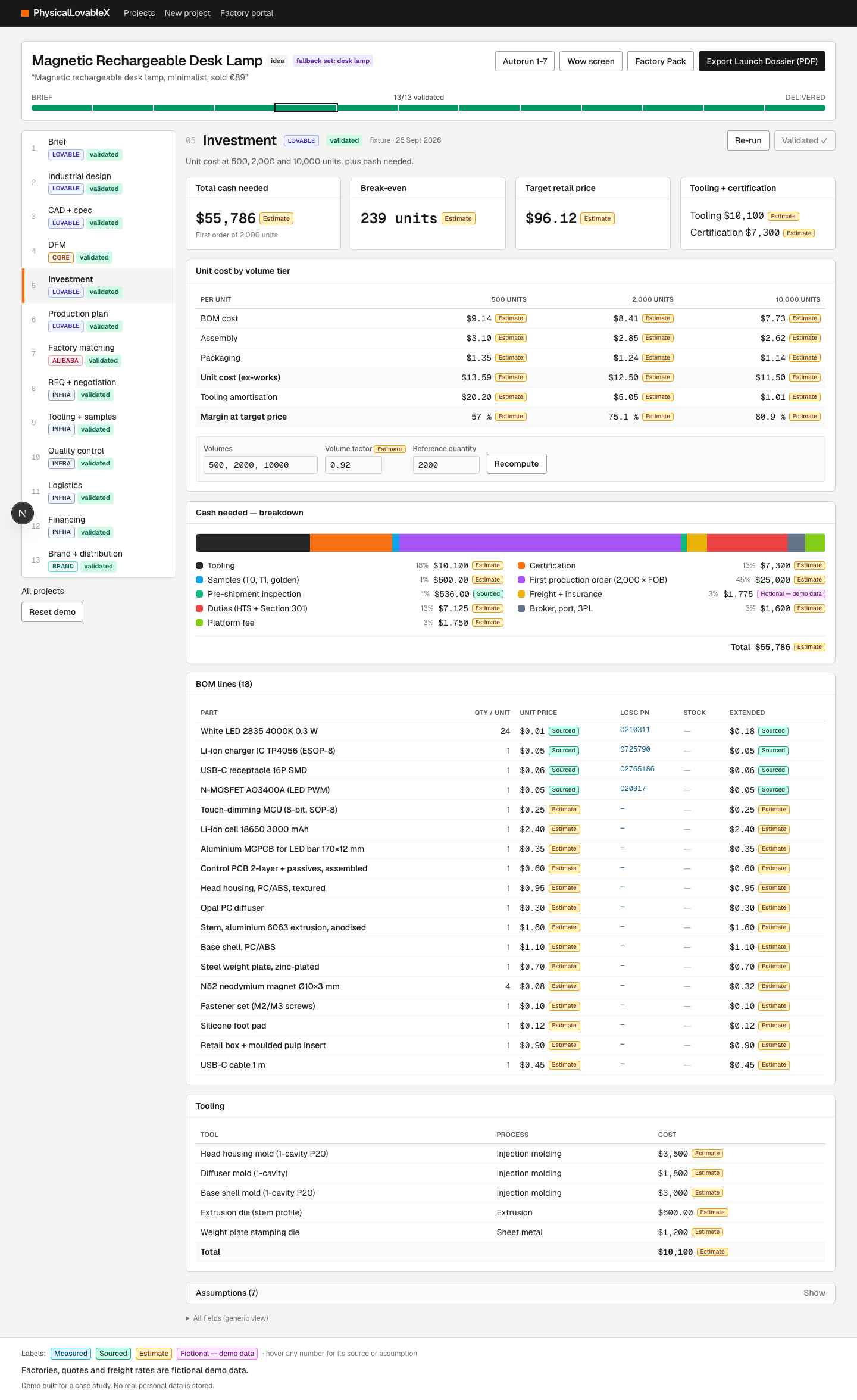
app/docs/screens/before/03_s5.png
