orpheo28/physicallovablex/app/docs/screens/before/03_s8.png

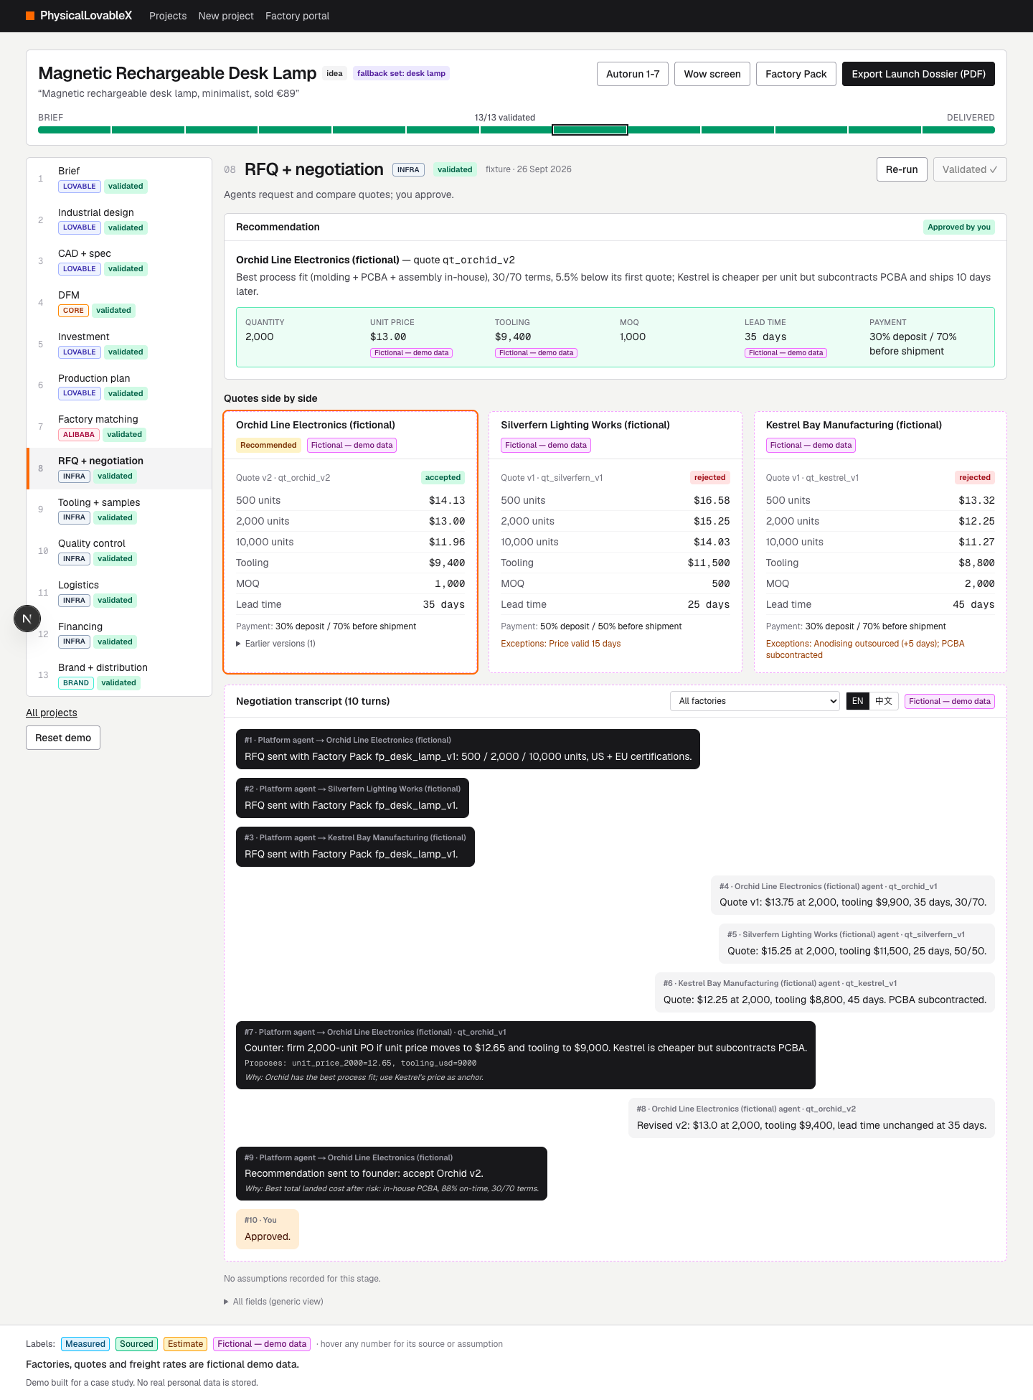
app/docs/screens/before/03_s8.png
