orpheo28/physicallovablex/app/docs/screens/before/03_s11.png

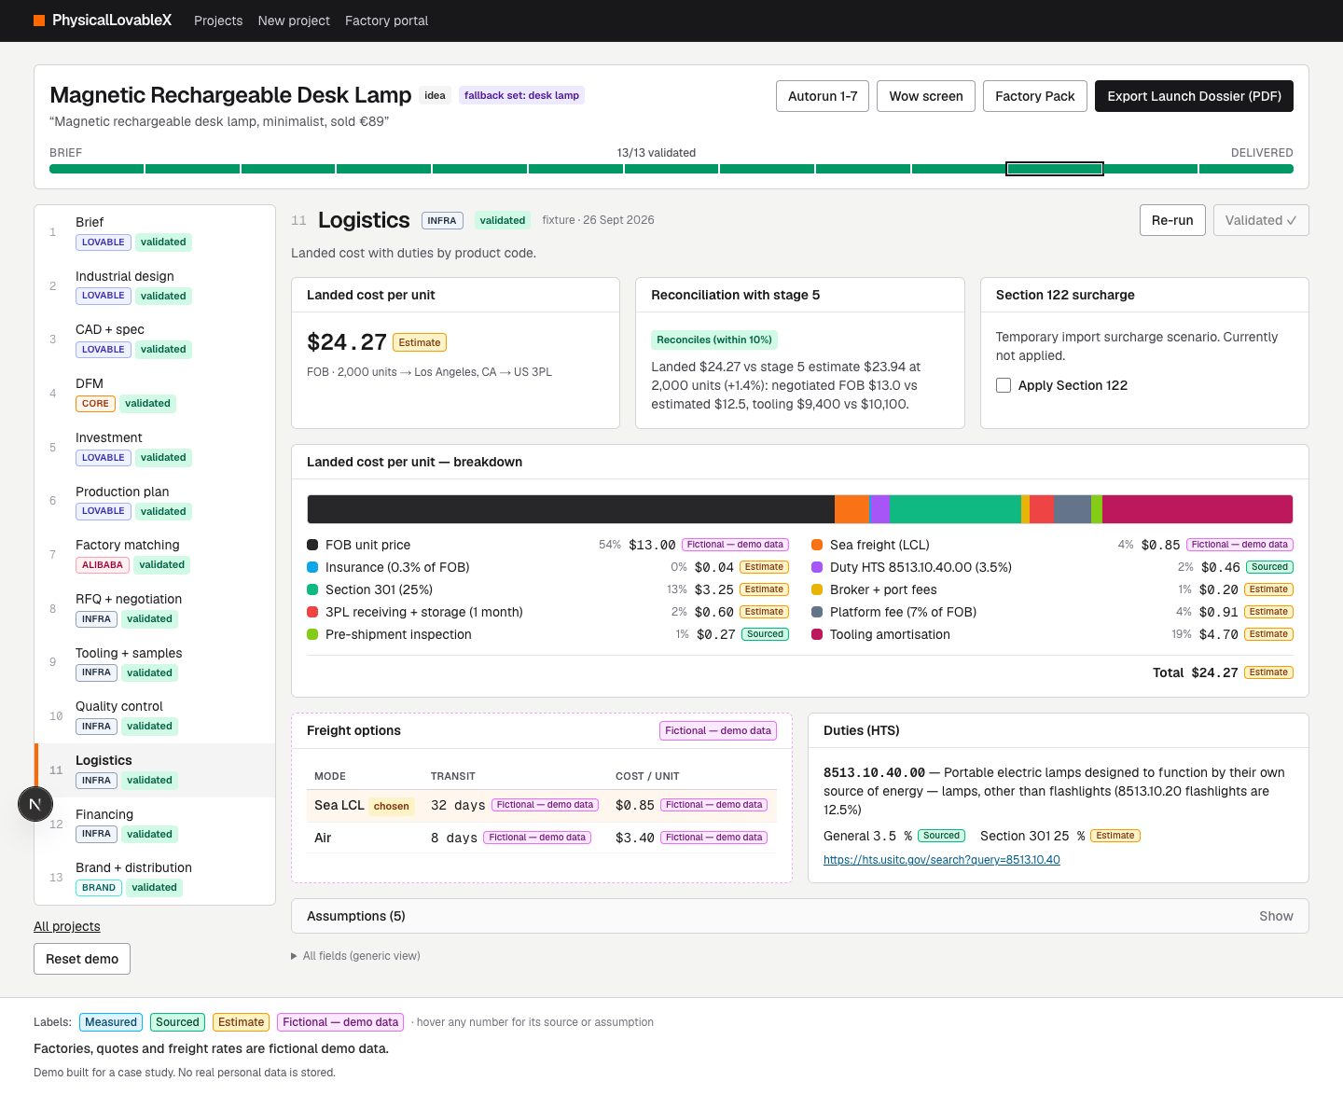
app/docs/screens/before/03_s11.png
