orpheo28/physicallovablex/app/docs/screens/before/03_s12.png

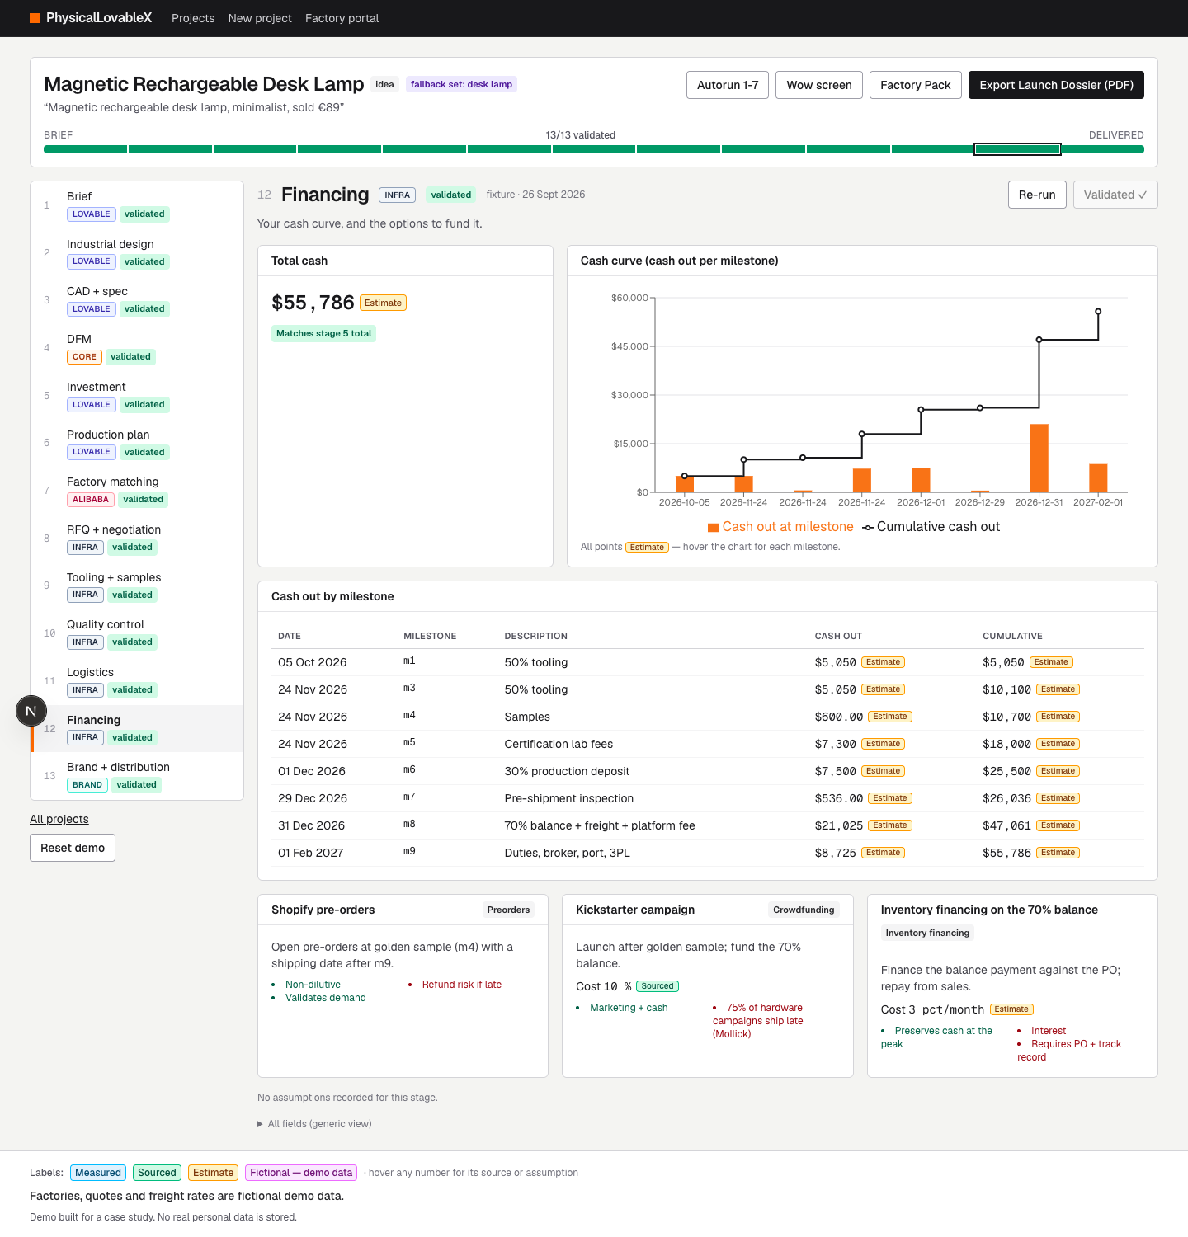
app/docs/screens/before/03_s12.png
