orpheo28/physicallovablex/app/docs/screens/before/04_factory_pack.png

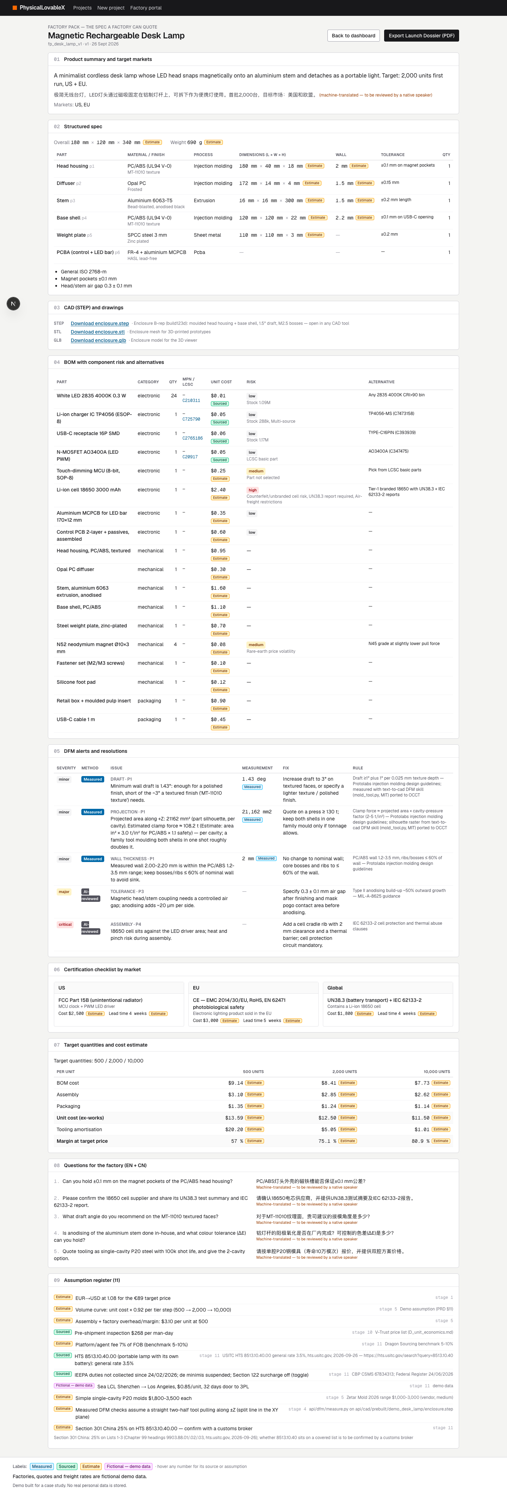
app/docs/screens/before/04_factory_pack.png
