orpheo28/physicallovablex/app/docs/screens/before/05_factories.png

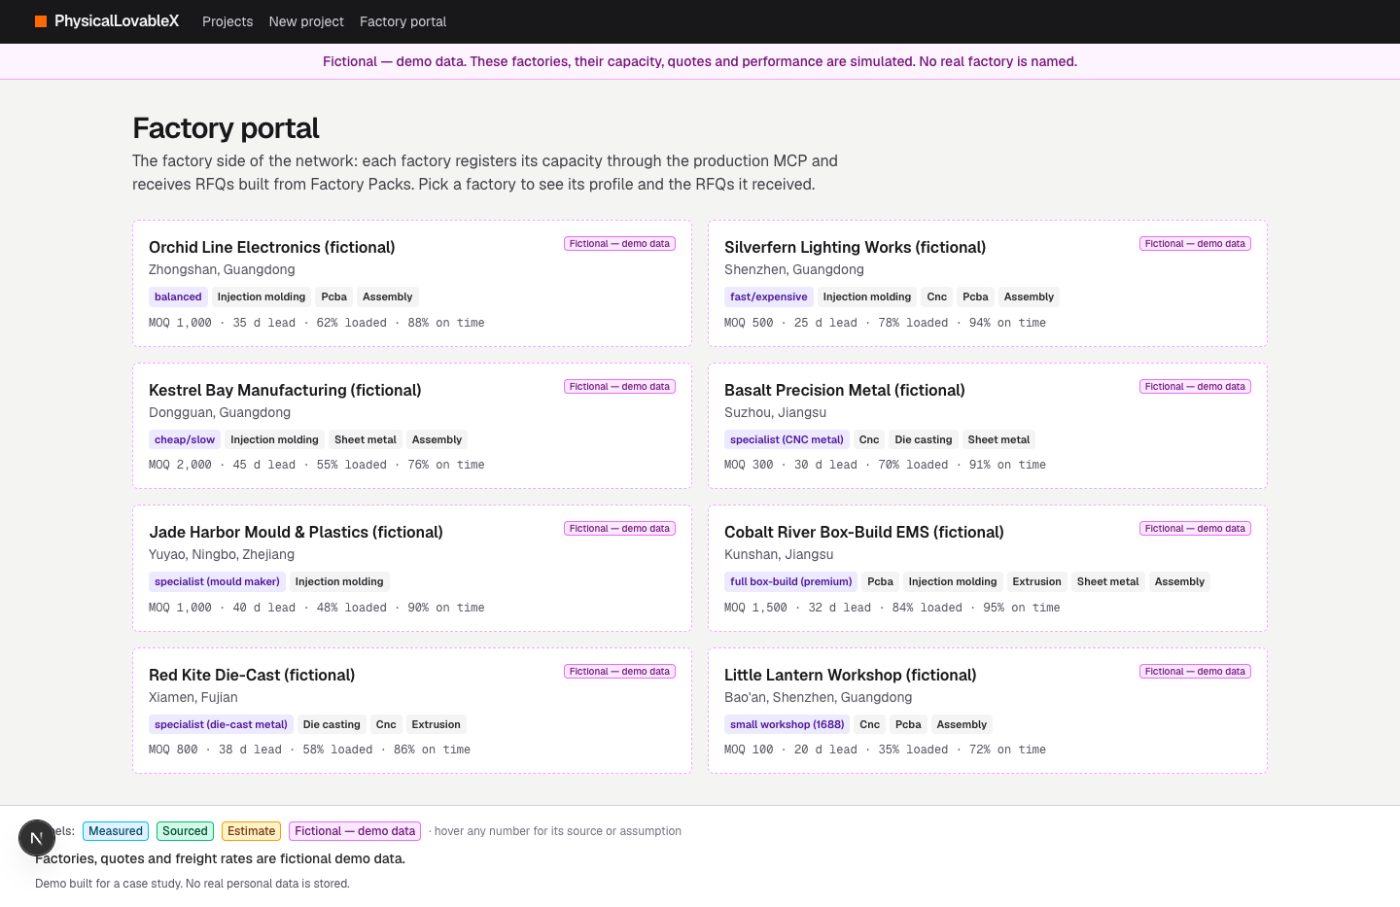
app/docs/screens/before/05_factories.png
