orpheo28/physicallovablex/app/docs/screens/before/05_factory.png

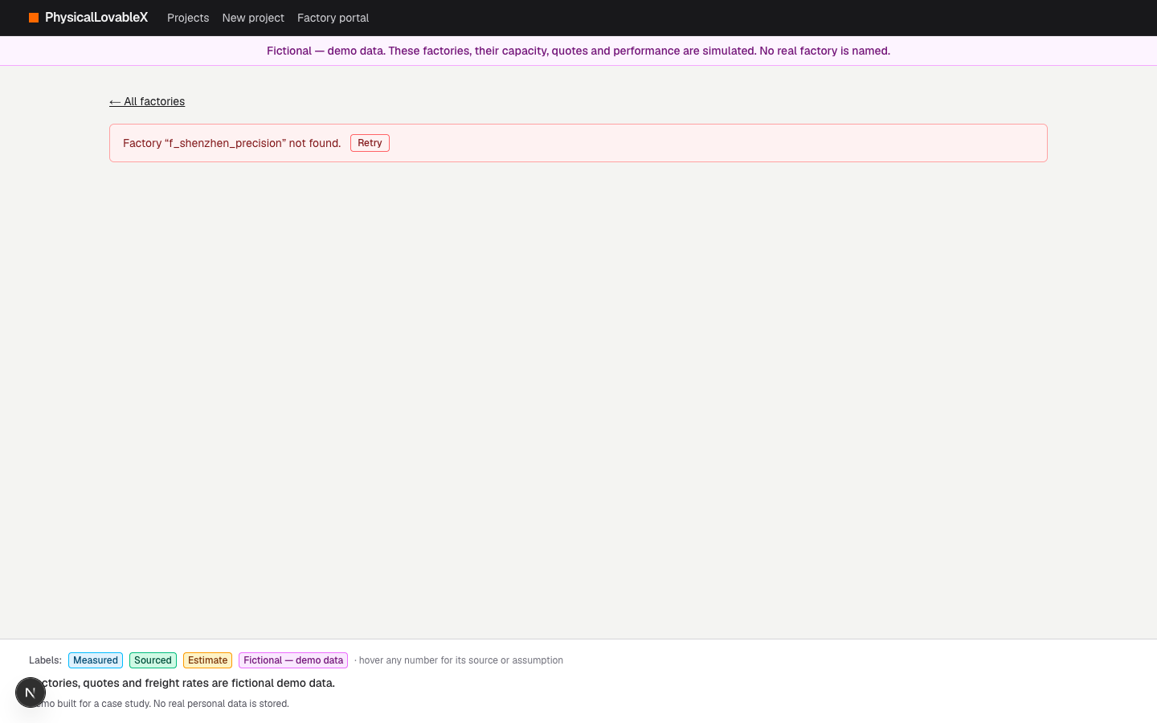
app/docs/screens/before/05_factory.png
