orpheo28/physicallovablex/app/docs/screens/before/06_new.png

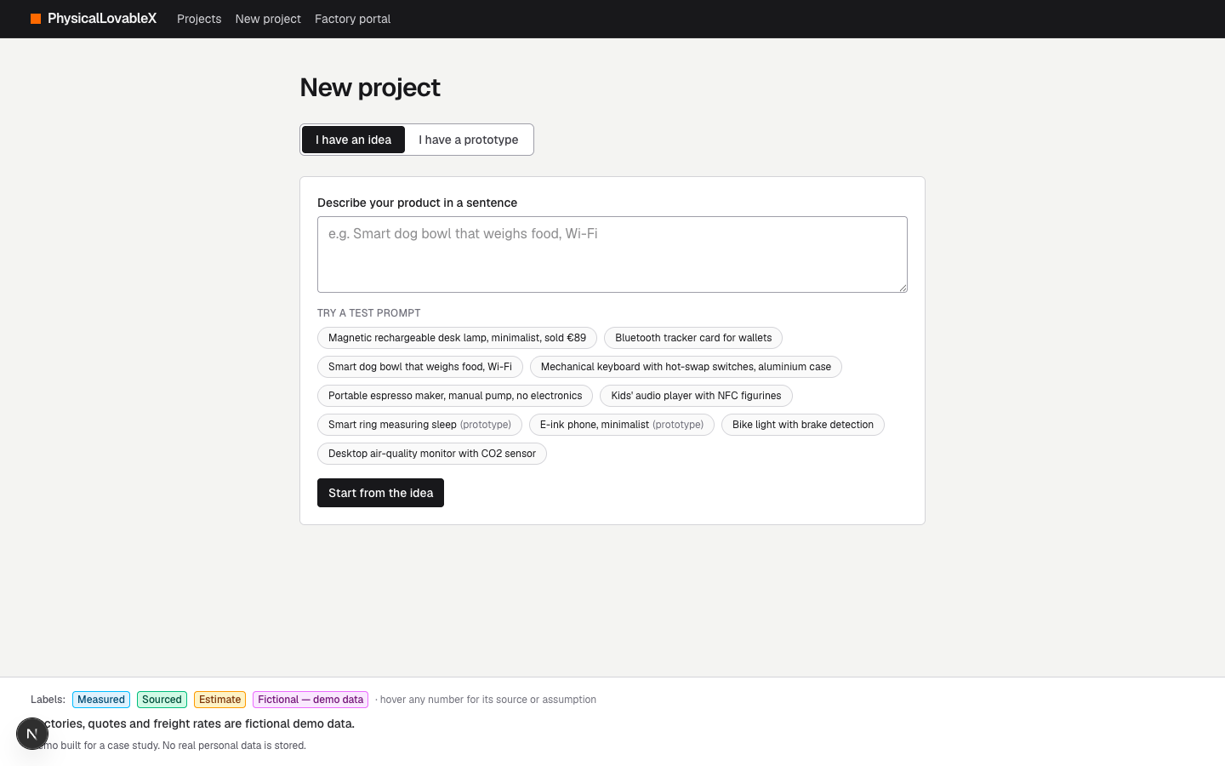
app/docs/screens/before/06_new.png
