orpheo28/physicallovablex/app/docs/screens/before/07_projects.png

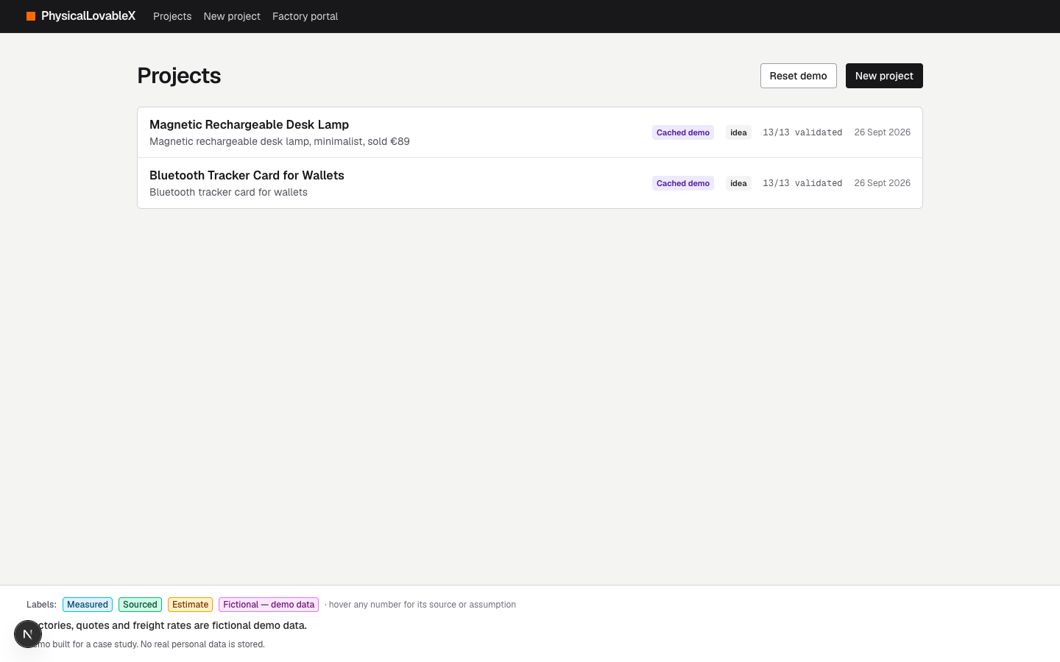
app/docs/screens/before/07_projects.png
