orpheo28/physicallovablex/app/docs/screens/cad/ai_changing_table.png

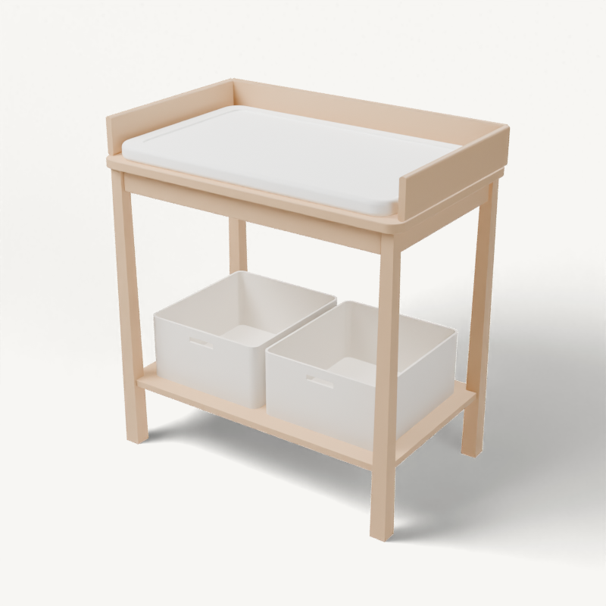
app/docs/screens/cad/ai_changing_table.png
