orpheo28/physicallovablex/app/docs/screens/cad/ai_home_robot.png

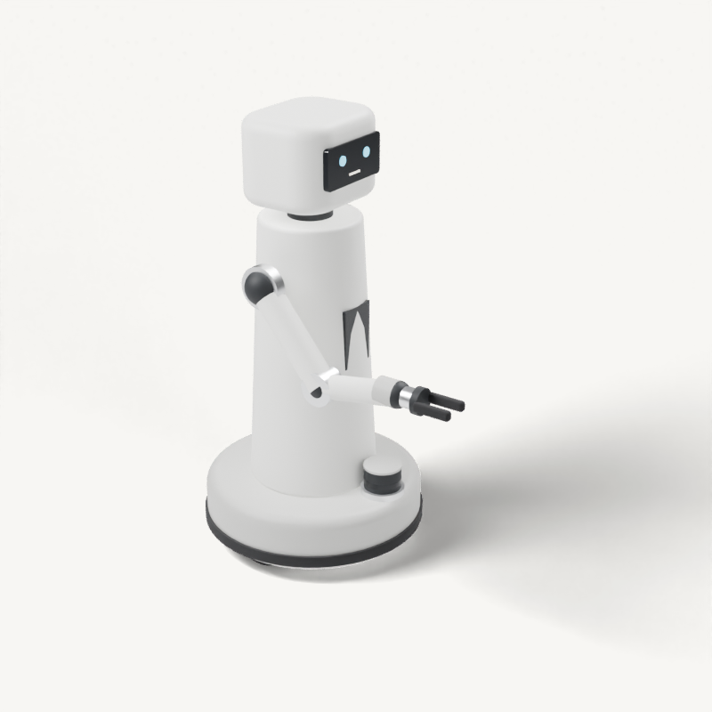
app/docs/screens/cad/ai_home_robot.png
