orpheo28/physicallovablex/app/docs/screens/cad/ai_irrigation.png

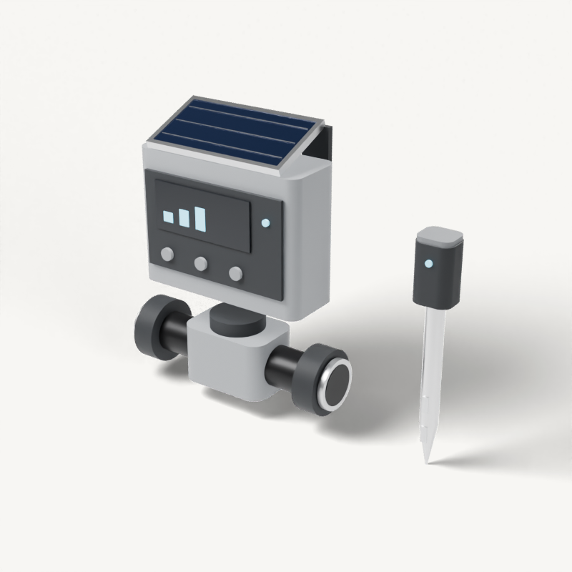
app/docs/screens/cad/ai_irrigation.png
