orpheo28/physicallovablex/app/docs/screens/cad/ai_solar_roof.png

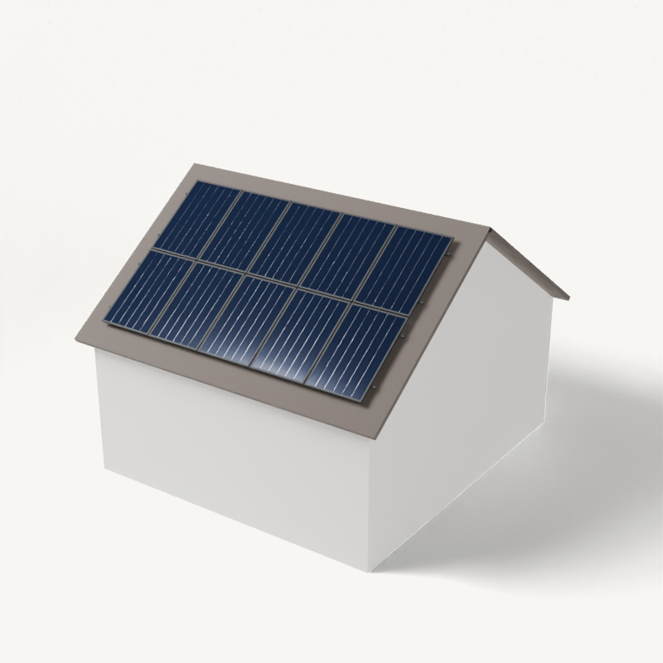
app/docs/screens/cad/ai_solar_roof.png
