orpheo28/physicallovablex/app/docs/screens/cad/ai_stick_vacuum.png

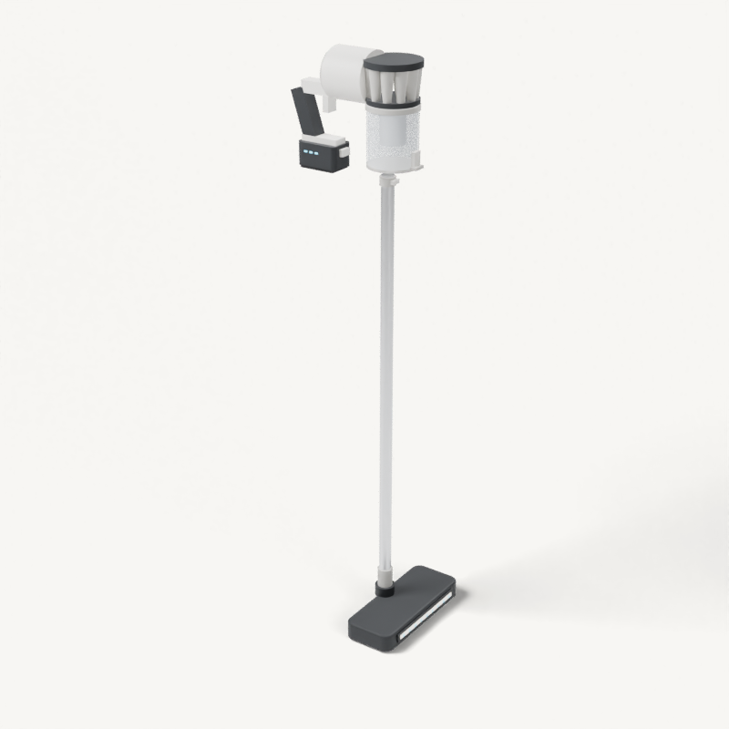
app/docs/screens/cad/ai_stick_vacuum.png
