orpheo28/physicallovablex/app/docs/screens/cad/family_furniturechanging_table.png

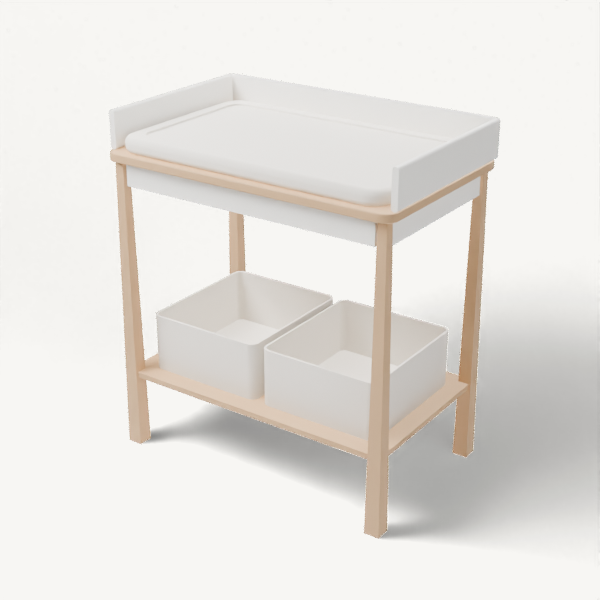
app/docs/screens/cad/family_furniturechanging_table.png
