orpheo28/physicallovablex/app/docs/screens/cad/family_home_robothelper.png

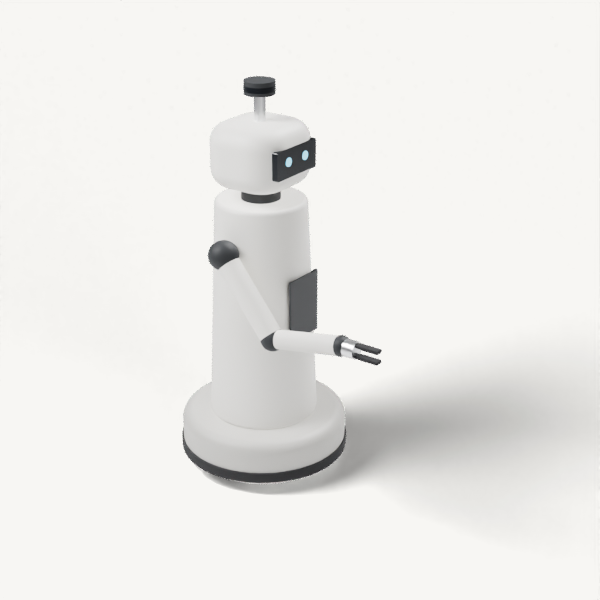
app/docs/screens/cad/family_home_robothelper.png
