orpheo28/physicallovablex/app/docs/screens/cad_bench/ble_tag_rag0.png

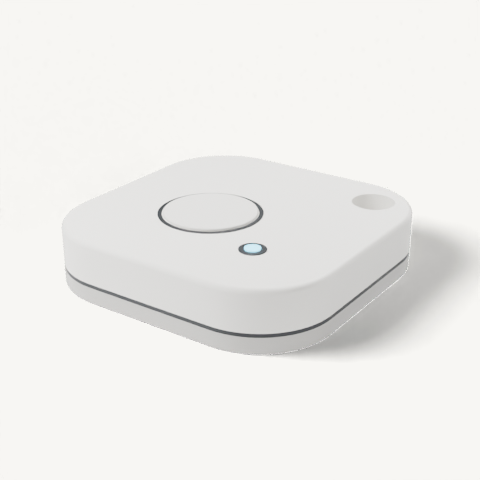
app/docs/screens/cad_bench/ble_tag_rag0.png
