orpheo28/physicallovablex/app/docs/screens/cad_bench/ble_tag_rag1.png

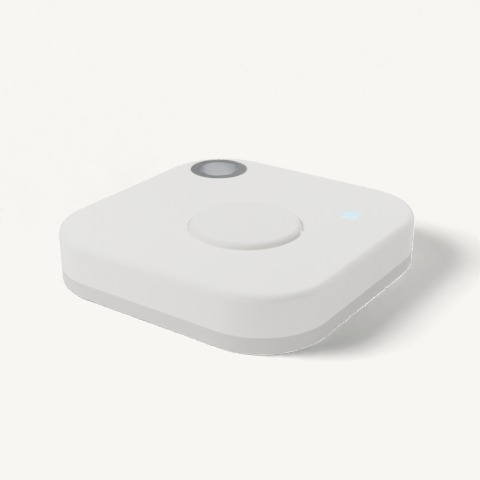
app/docs/screens/cad_bench/ble_tag_rag1.png
