orpheo28/physicallovablex/app/docs/screens/cad_bench/cable_gland_rag0.png

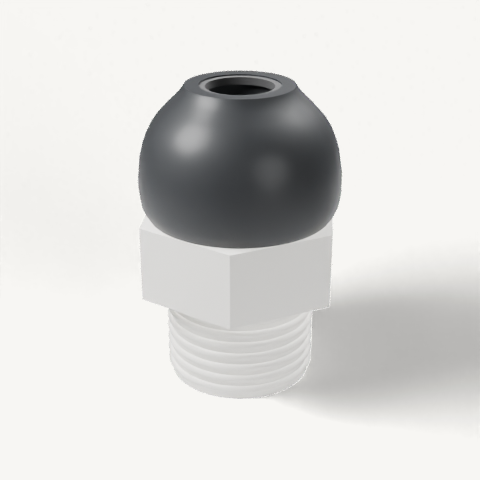
app/docs/screens/cad_bench/cable_gland_rag0.png
