orpheo28/physicallovablex/app/docs/screens/cad_bench/cable_gland_rag0_r2.png

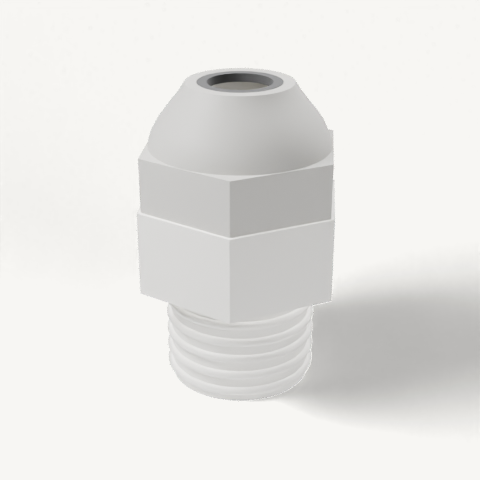
app/docs/screens/cad_bench/cable_gland_rag0_r2.png
