orpheo28/physicallovablex/app/docs/screens/cad_bench/camera_rag0.png

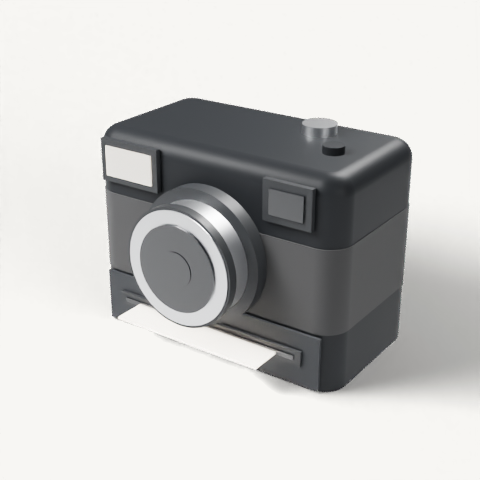
app/docs/screens/cad_bench/camera_rag0.png
