orpheo28/physicallovablex/app/docs/screens/cad_bench/changing_table_rag0.png

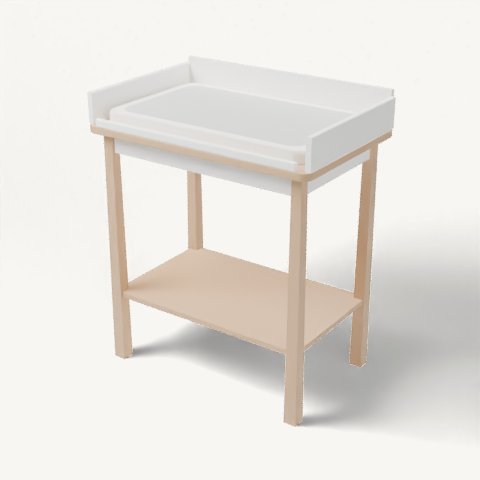
app/docs/screens/cad_bench/changing_table_rag0.png
