orpheo28/physicallovablex/app/docs/screens/cad_bench/changing_table_rag1.png

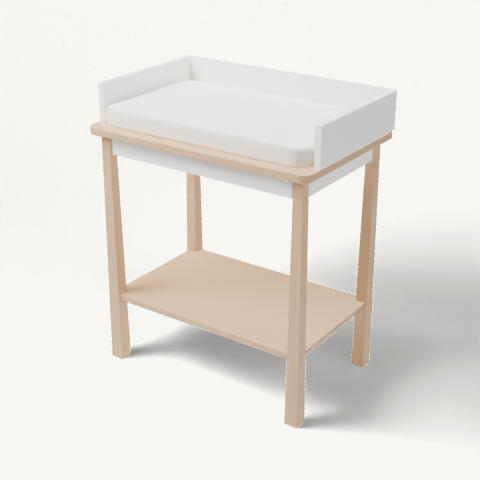
app/docs/screens/cad_bench/changing_table_rag1.png
