orpheo28/physicallovablex/app/docs/screens/cad_bench/curved_handle_rag1.png

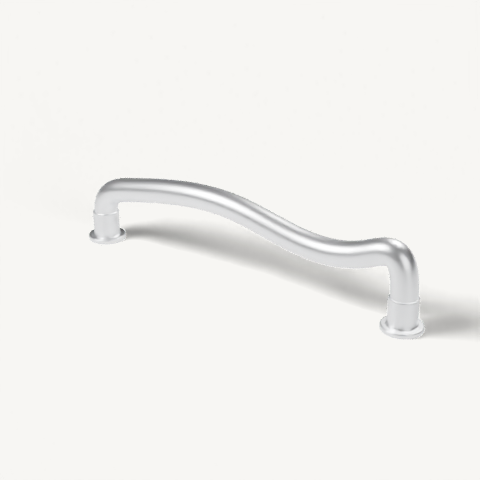
app/docs/screens/cad_bench/curved_handle_rag1.png
