orpheo28/physicallovablex/app/docs/screens/cad_bench/desk_lamp_rag0.png

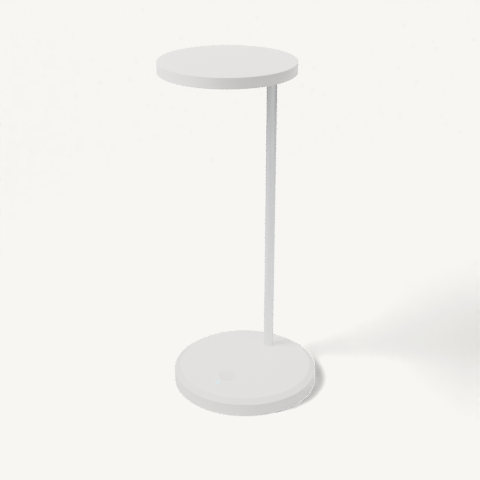
app/docs/screens/cad_bench/desk_lamp_rag0.png
