orpheo28/physicallovablex/app/docs/screens/cad_bench/drone_rag0.png

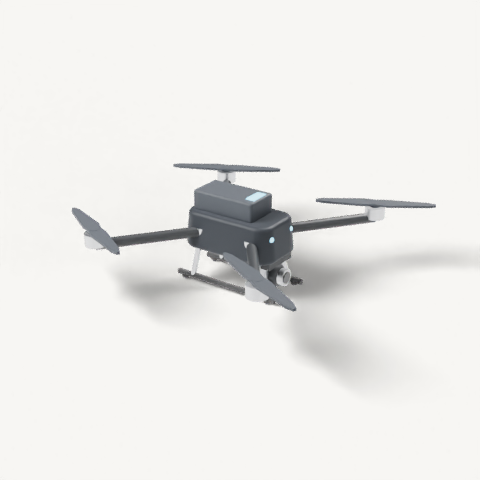
app/docs/screens/cad_bench/drone_rag0.png
