orpheo28/physicallovablex/app/docs/screens/cad_bench/gear_rag0.png

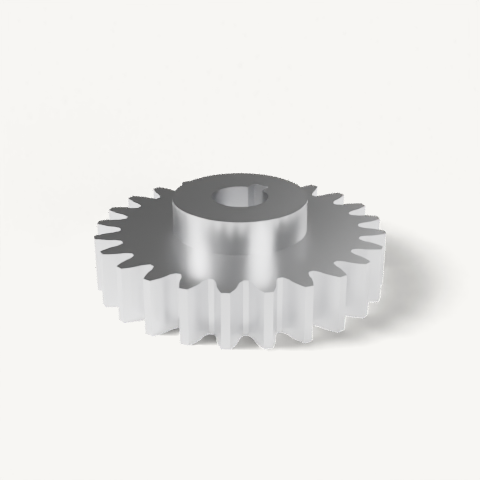
app/docs/screens/cad_bench/gear_rag0.png
