orpheo28/physicallovablex/app/docs/screens/cad_bench/gear_rag1.png

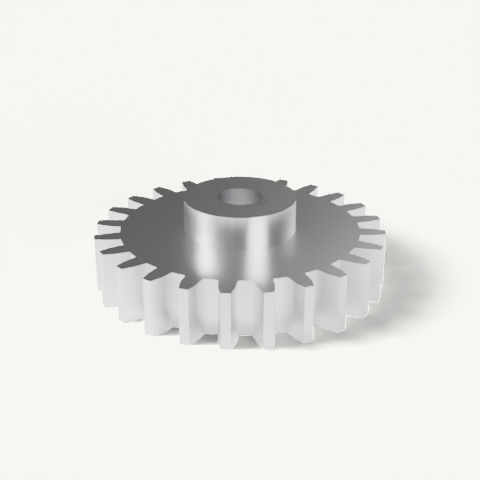
app/docs/screens/cad_bench/gear_rag1.png
