orpheo28/physicallovablex/app/docs/screens/cad_bench/hair_dryer_rag0.png

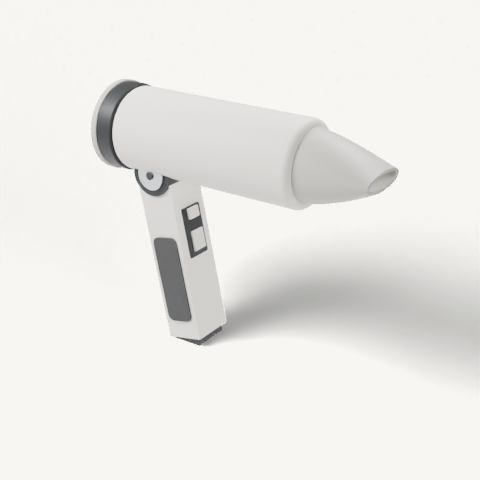
app/docs/screens/cad_bench/hair_dryer_rag0.png
