orpheo28/physicallovablex/app/docs/screens/cad_bench/hair_dryer_rag1.png

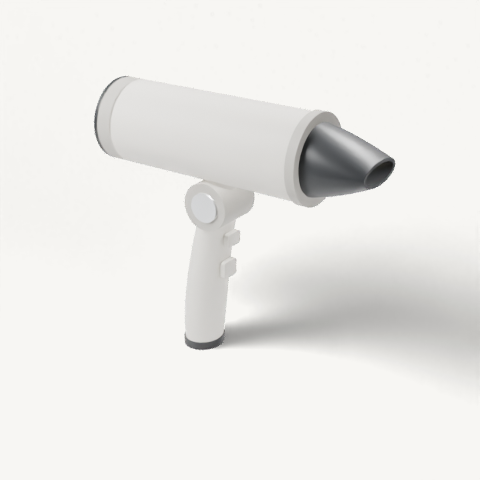
app/docs/screens/cad_bench/hair_dryer_rag1.png
