orpheo28/physicallovablex/app/docs/screens/cad_bench/hinge_rag0.png

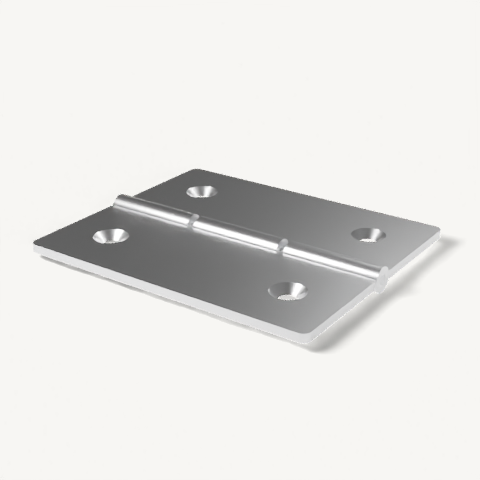
app/docs/screens/cad_bench/hinge_rag0.png
