orpheo28/physicallovablex/app/docs/screens/cad_bench/hinge_rag1.png

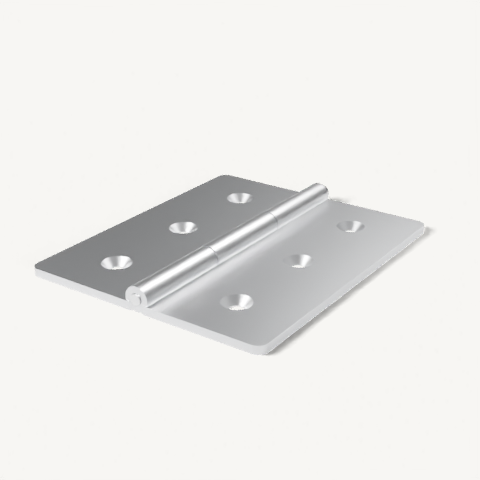
app/docs/screens/cad_bench/hinge_rag1.png
