orpheo28/physicallovablex/app/docs/screens/cad_bench/home_robot_rag0.png

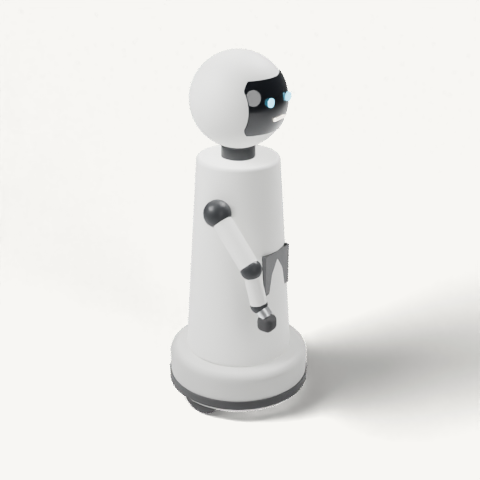
app/docs/screens/cad_bench/home_robot_rag0.png
