orpheo28/physicallovablex/app/docs/screens/cad_bench/irrigation_rag1.png

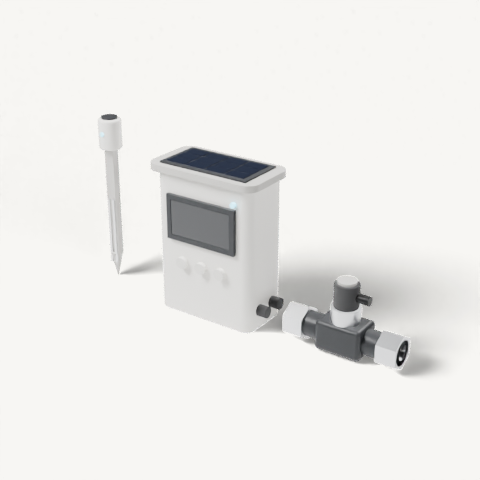
app/docs/screens/cad_bench/irrigation_rag1.png
