orpheo28/physicallovablex/app/docs/screens/cad_bench/sheet_r2.png

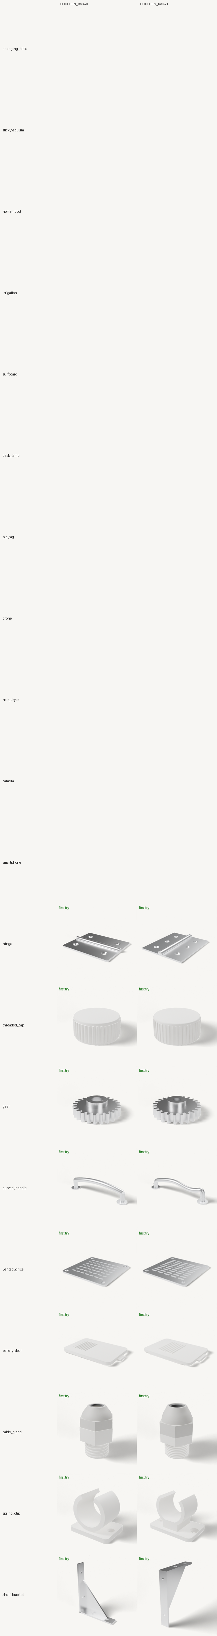
app/docs/screens/cad_bench/sheet_r2.png
