orpheo28/physicallovablex/app/docs/screens/cad_bench/shelf_bracket_rag0.png

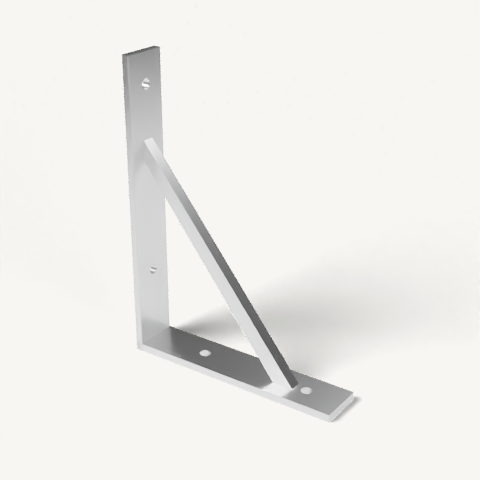
app/docs/screens/cad_bench/shelf_bracket_rag0.png
