orpheo28/physicallovablex/app/docs/screens/cad_bench/shelf_bracket_rag0_r2.png

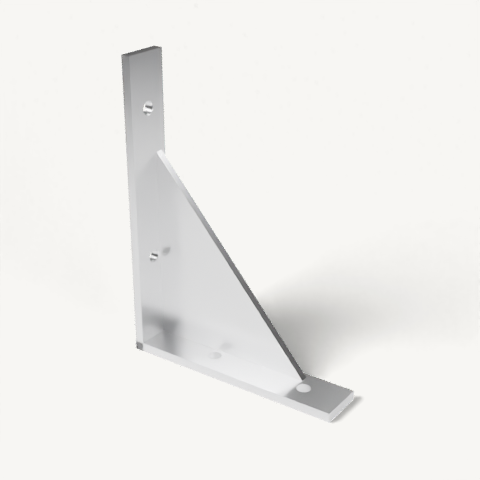
app/docs/screens/cad_bench/shelf_bracket_rag0_r2.png
