orpheo28/physicallovablex/app/docs/screens/cad_bench/shelf_bracket_rag1.png

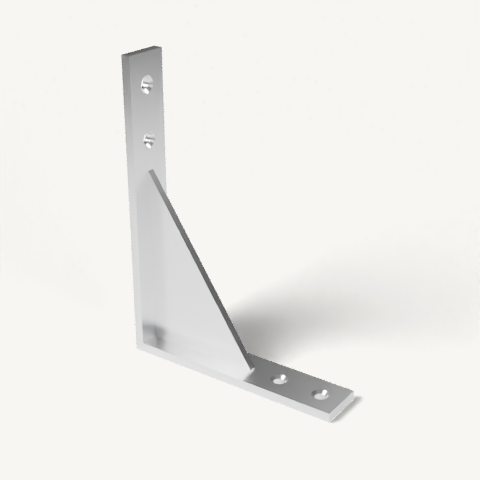
app/docs/screens/cad_bench/shelf_bracket_rag1.png
