orpheo28/physicallovablex/app/docs/screens/cad_bench/spring_clip_rag0.png

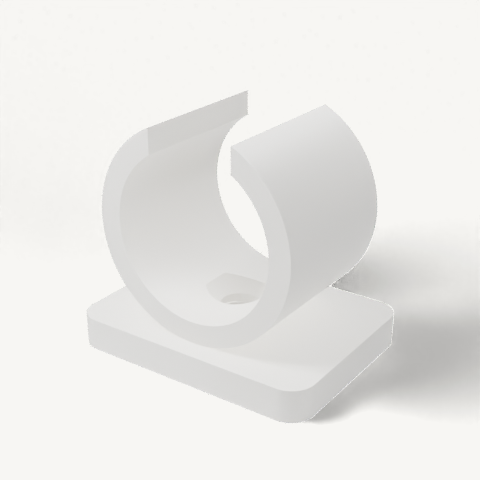
app/docs/screens/cad_bench/spring_clip_rag0.png
