orpheo28/physicallovablex/app/docs/screens/cad_bench/spring_clip_rag1_r2.png

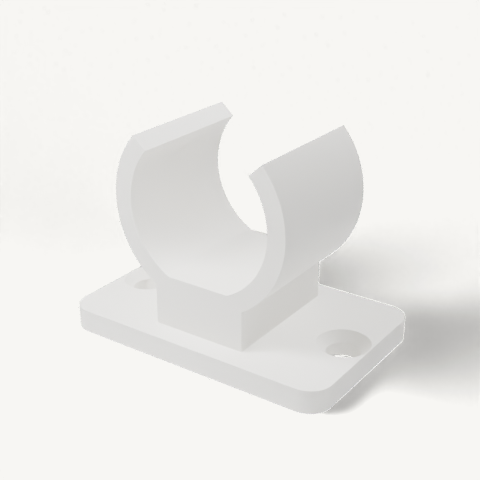
app/docs/screens/cad_bench/spring_clip_rag1_r2.png
