orpheo28/physicallovablex/app/docs/screens/cad_bench/threaded_cap_rag0.png

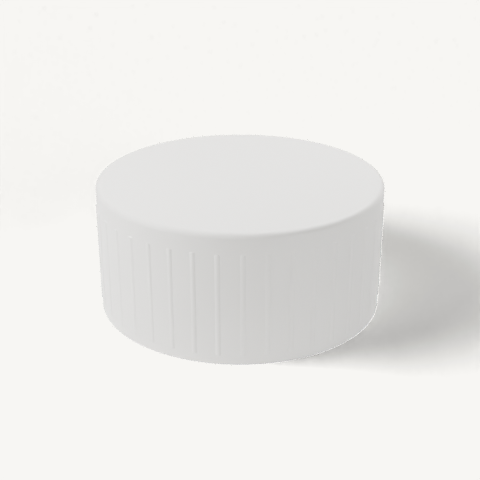
app/docs/screens/cad_bench/threaded_cap_rag0.png
