orpheo28/physicallovablex/app/docs/screens/cad_bench/threaded_cap_rag1_r2.png

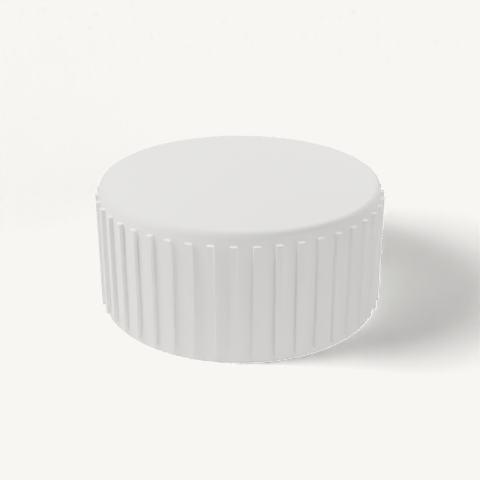
app/docs/screens/cad_bench/threaded_cap_rag1_r2.png
