orpheo28/physicallovablex/app/docs/screens/cad_bench/vented_grille_rag0.png

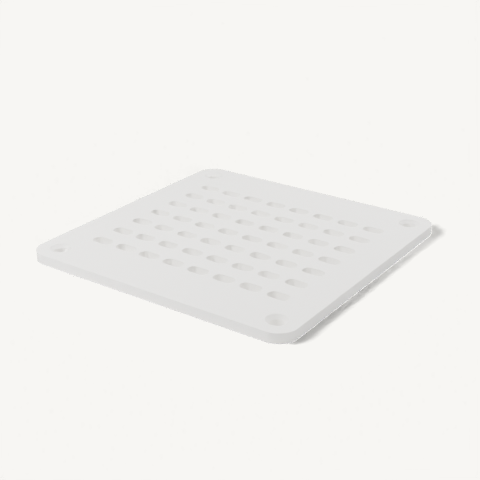
app/docs/screens/cad_bench/vented_grille_rag0.png
