orpheo28/physicallovablex/app/docs/screens/cad_pro/camera_basic.png

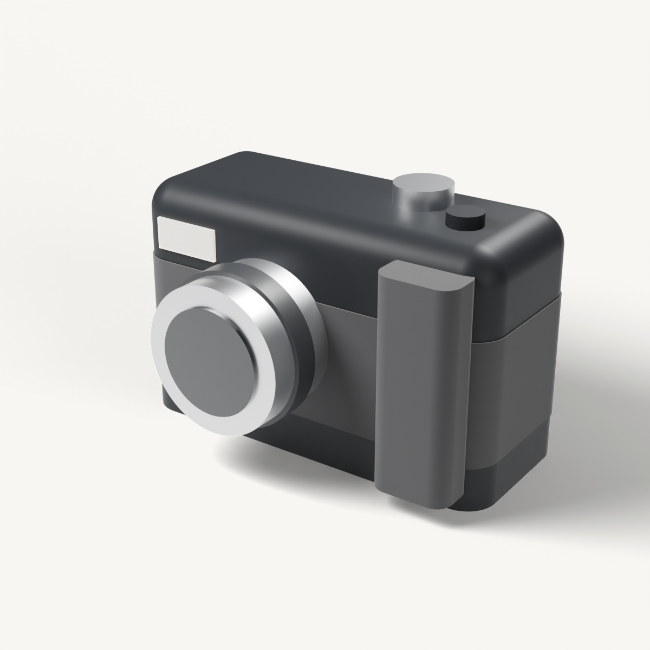
app/docs/screens/cad_pro/camera_basic.png
