orpheo28/physicallovablex/app/docs/screens/cad_pro/pod_internals_pro.png

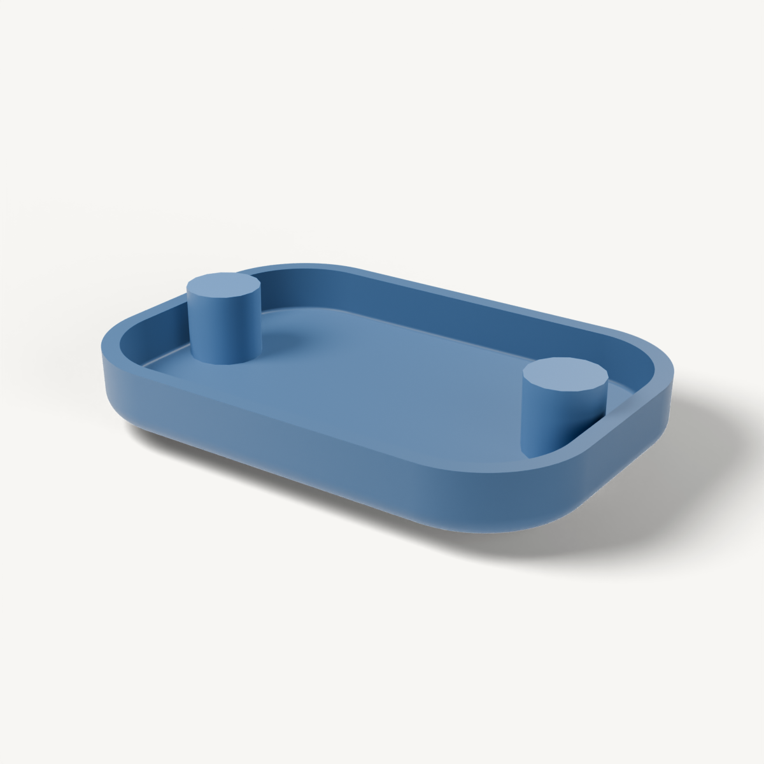
app/docs/screens/cad_pro/pod_internals_pro.png
