orpheo28/physicallovablex/app/docs/screens/drawings/sheet_demo_desk_lamp_v0_P01.png

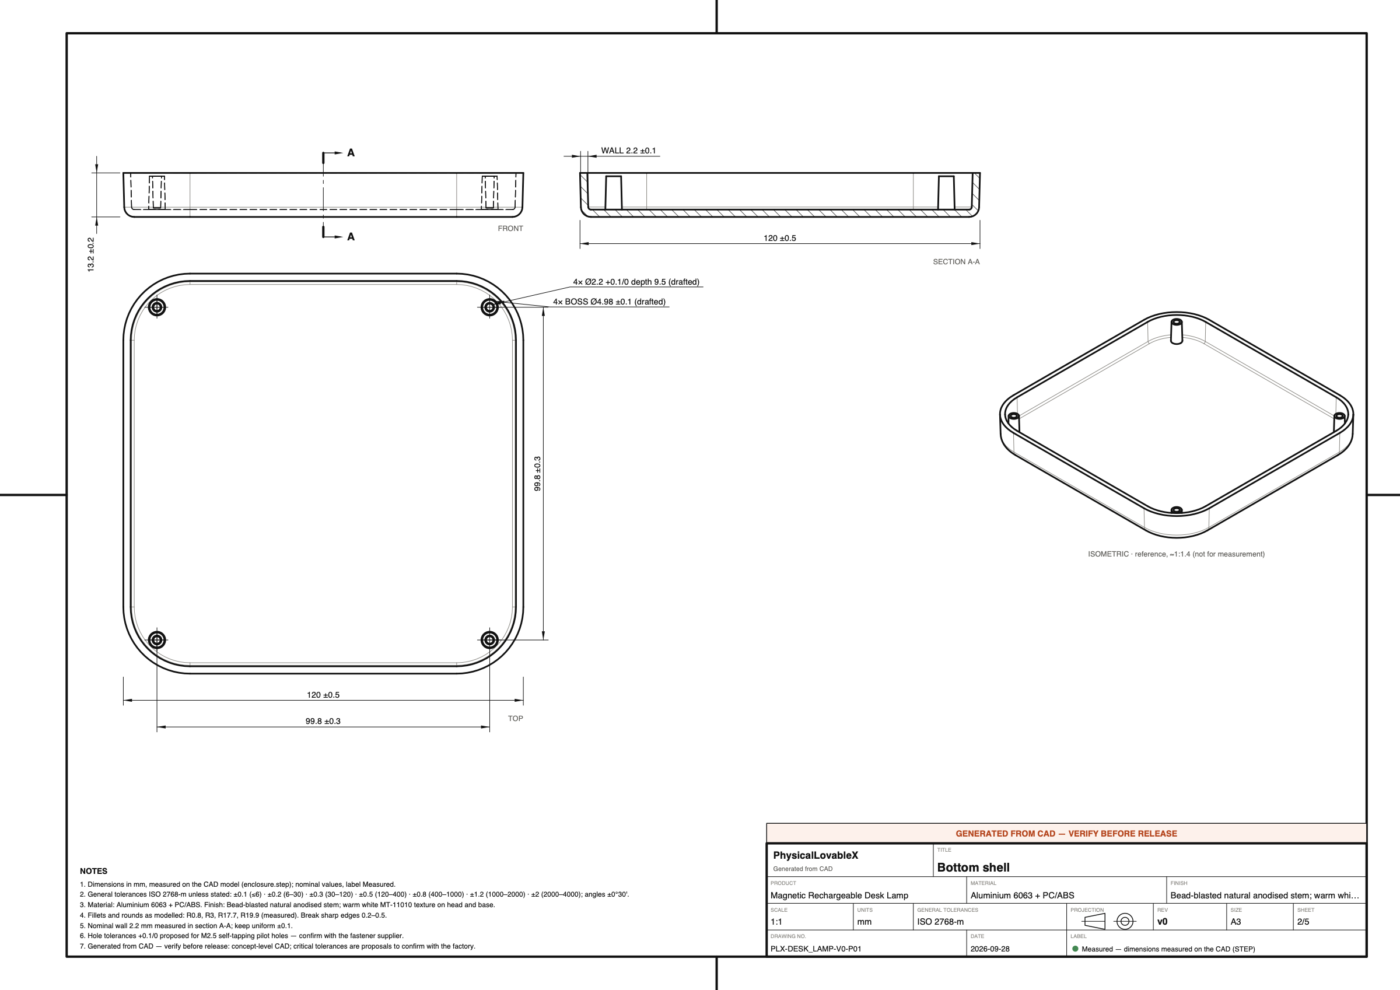
app/docs/screens/drawings/sheet_demo_desk_lamp_v0_P01.png
