orpheo28/physicallovablex/app/docs/screens/drawings/sheet_demo_drone_follow_v2_A1.png

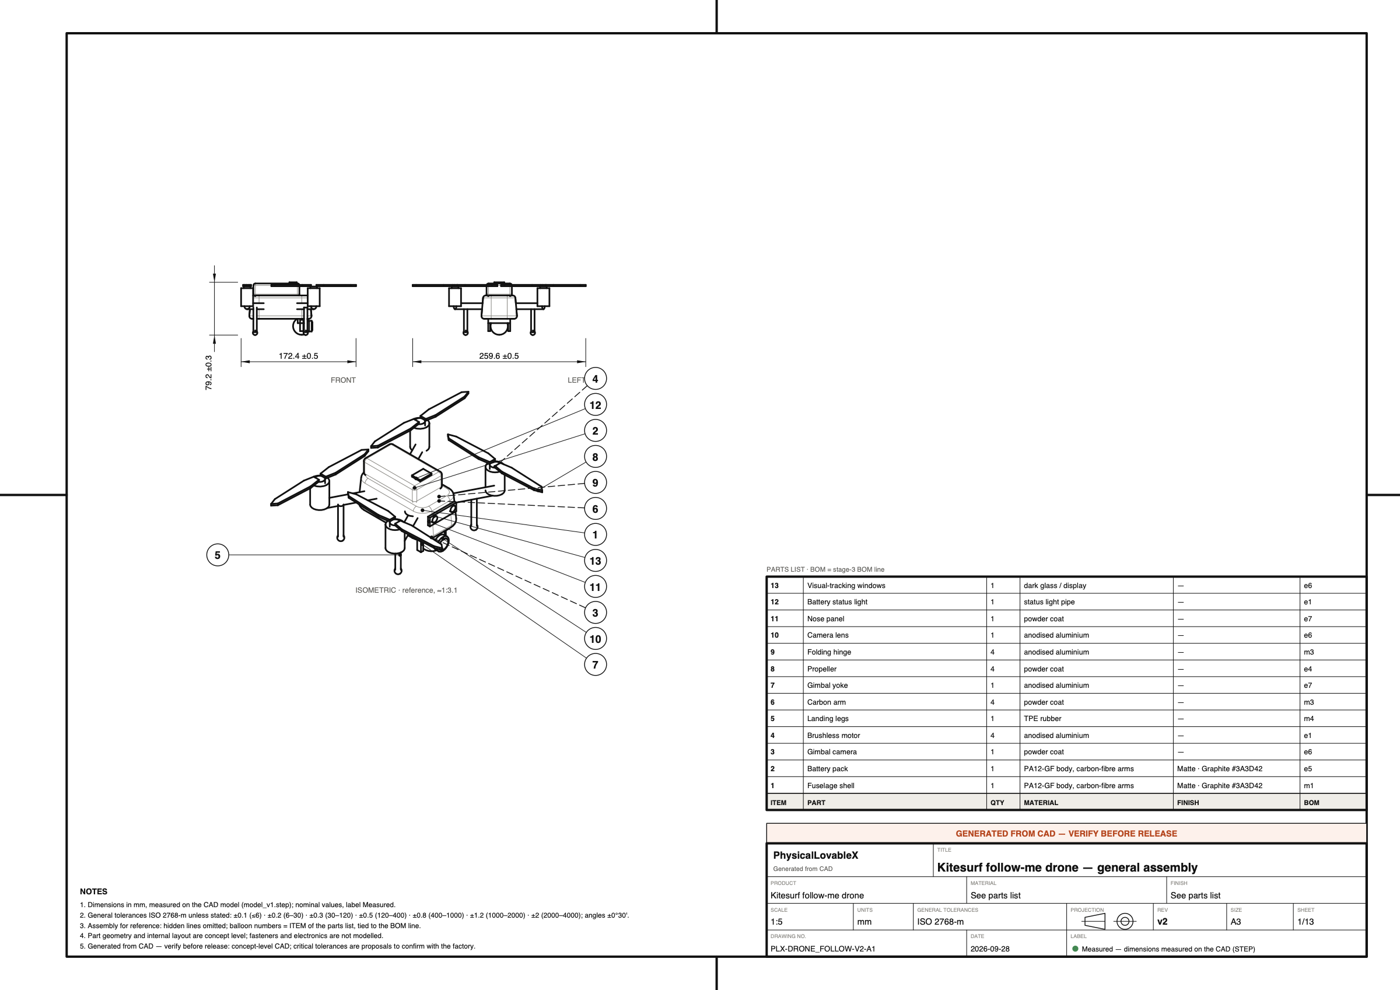
app/docs/screens/drawings/sheet_demo_drone_follow_v2_A1.png
