orpheo28/physicallovablex/app/docs/screens/drawings/sheet_demo_stick_vacuum_v2_A1.png

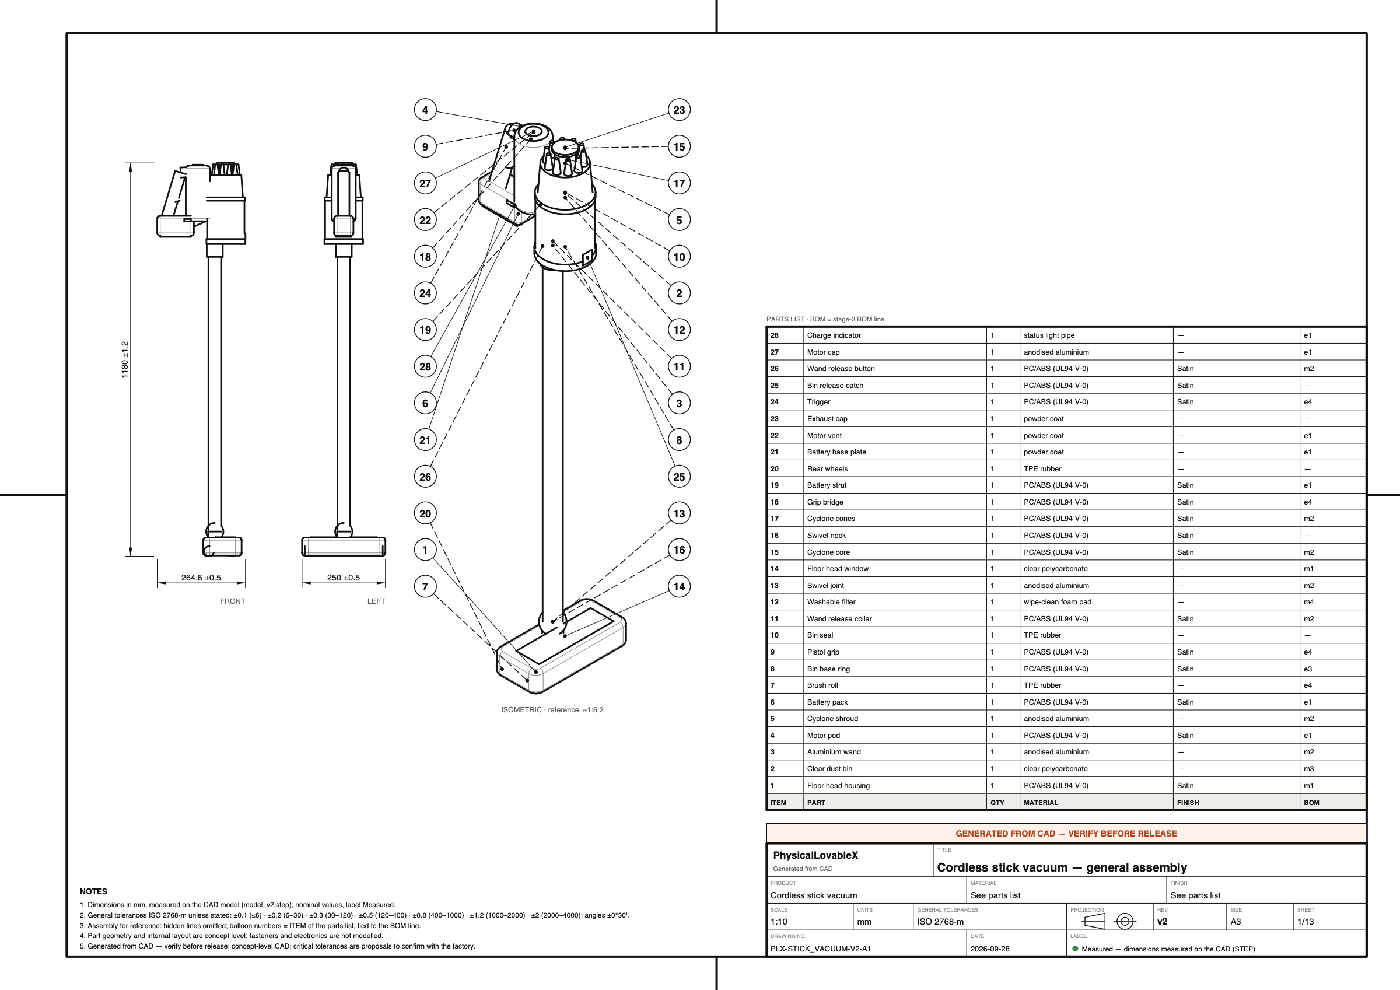
app/docs/screens/drawings/sheet_demo_stick_vacuum_v2_A1.png
