orpheo28/physicallovablex/app/docs/screens/drawings/sheet_demo_surfboard_beginner_v2_P01.png

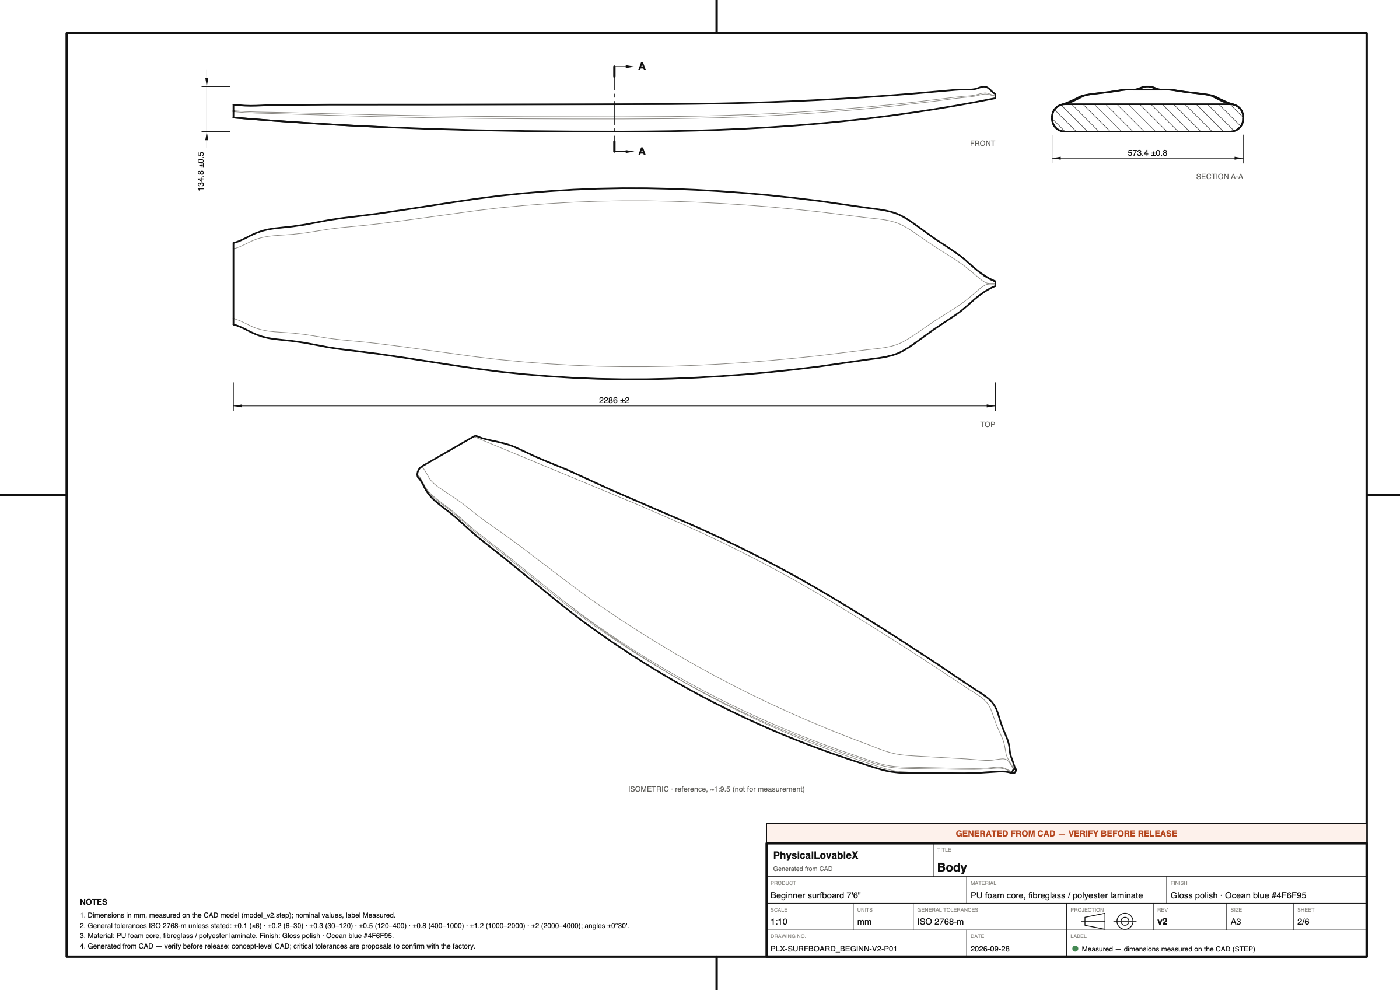
app/docs/screens/drawings/sheet_demo_surfboard_beginner_v2_P01.png
