orpheo28/physicallovablex/app/docs/screens/drawings/sheet_demo_whoop_kitesurf_v4_A1.png

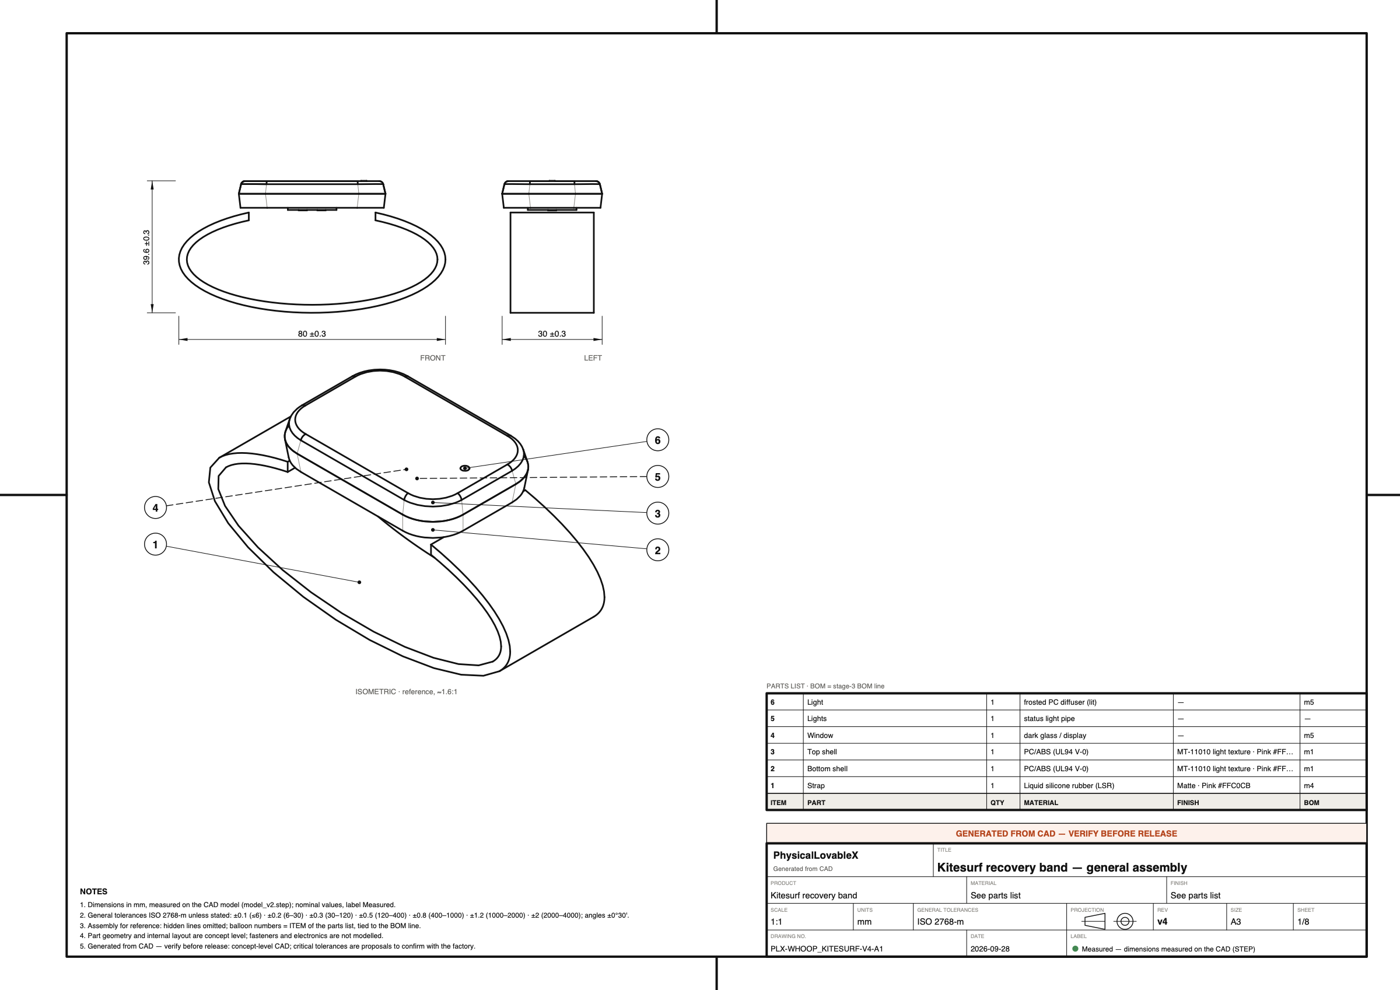
app/docs/screens/drawings/sheet_demo_whoop_kitesurf_v4_A1.png
