orpheo28/physicallovablex/app/docs/screens/drawings/sheet_demo_whoop_kitesurf_v4_M01.png

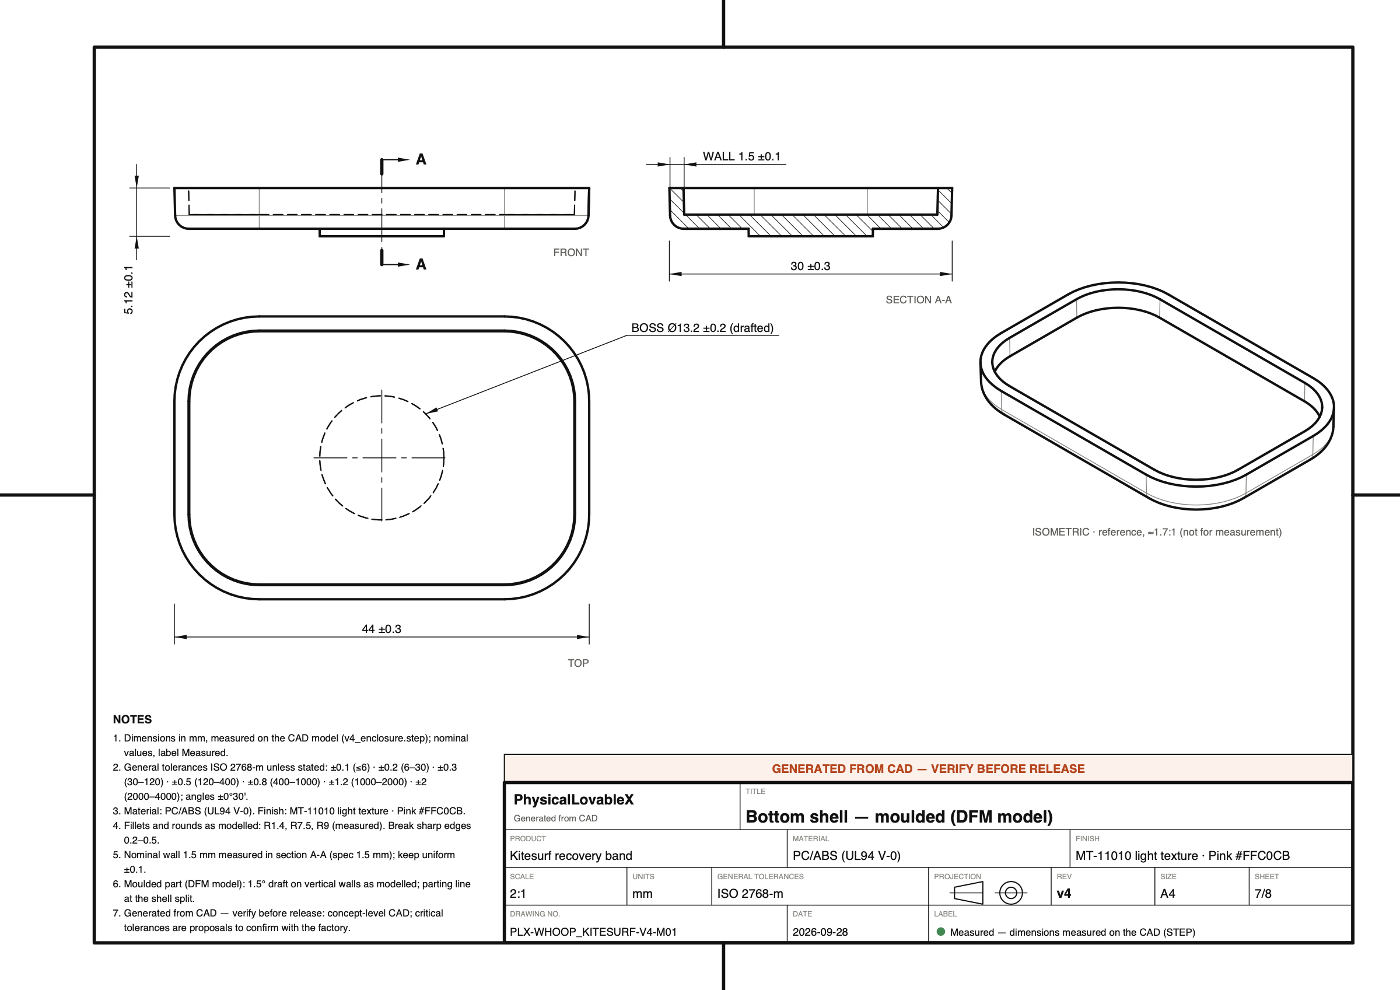
app/docs/screens/drawings/sheet_demo_whoop_kitesurf_v4_M01.png
