orpheo28/physicallovablex/app/docs/screens/drawings/stage3_drawings_link.png

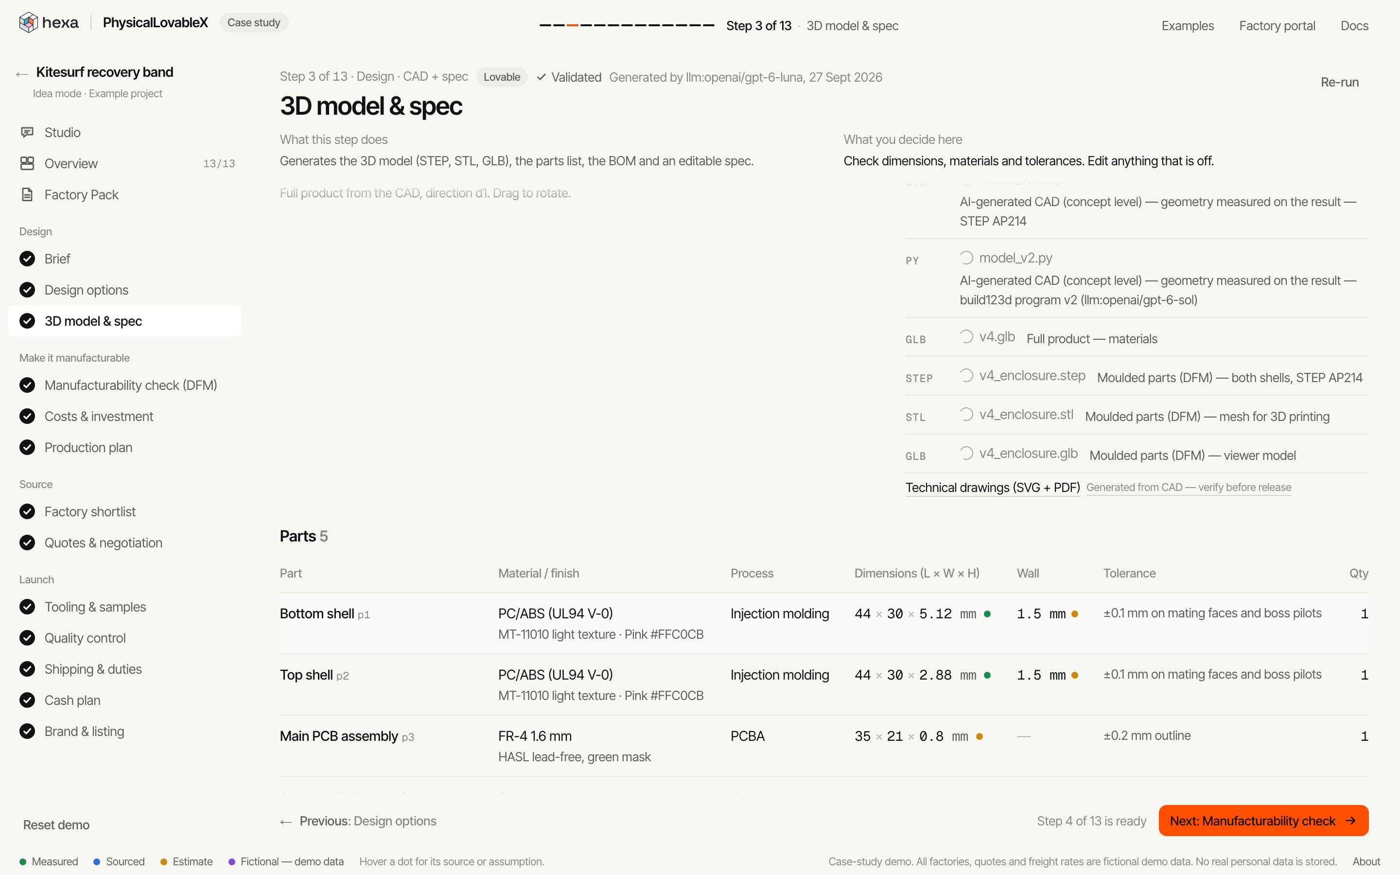
app/docs/screens/drawings/stage3_drawings_link.png
