orpheo28/physicallovablex/app/docs/screens/drawings/studio_drawings_changing_table.png

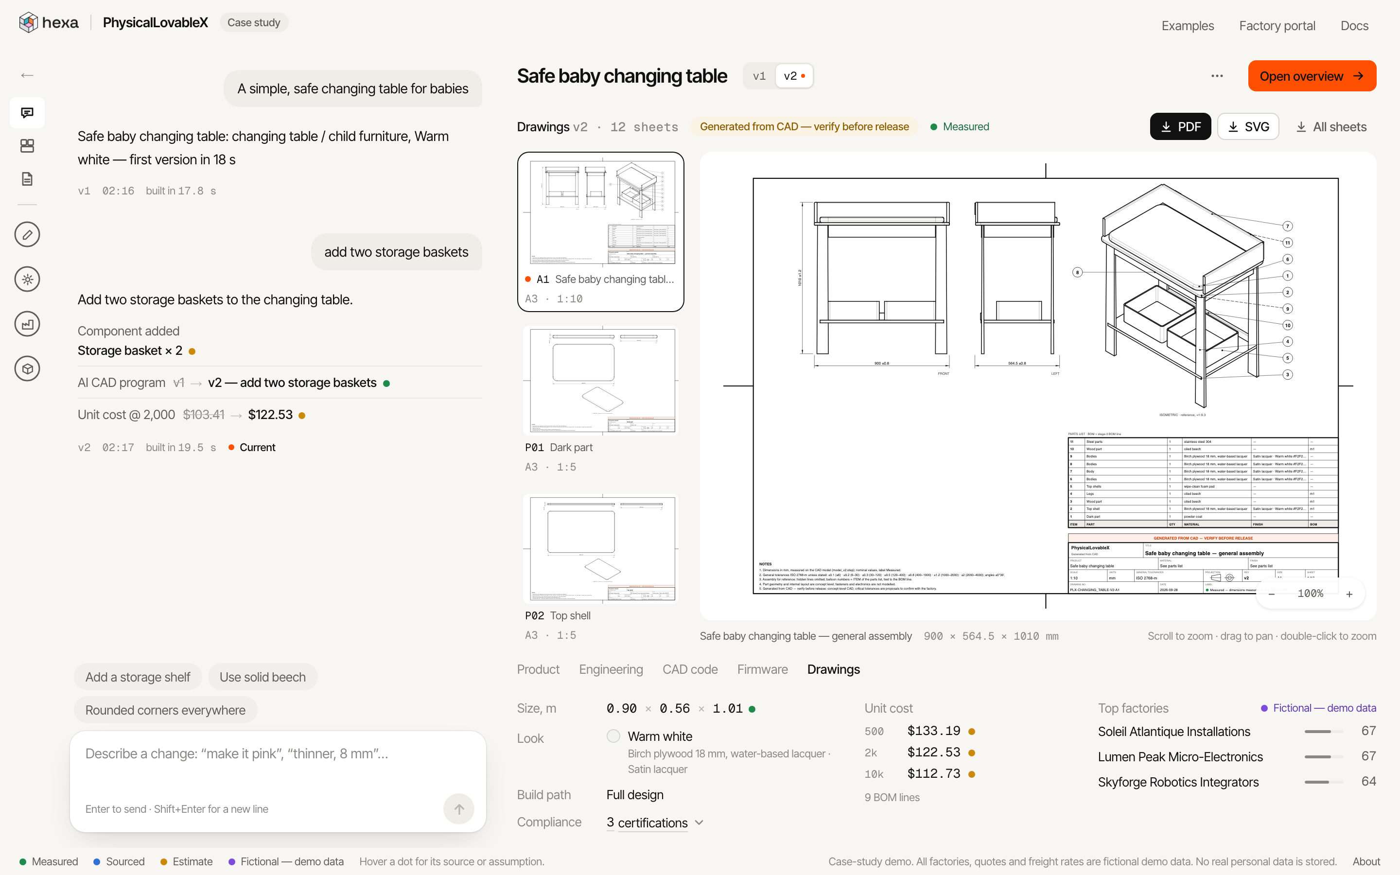
app/docs/screens/drawings/studio_drawings_changing_table.png
