orpheo28/physicallovablex/app/docs/screens/drawings/studio_drawings_drone.png

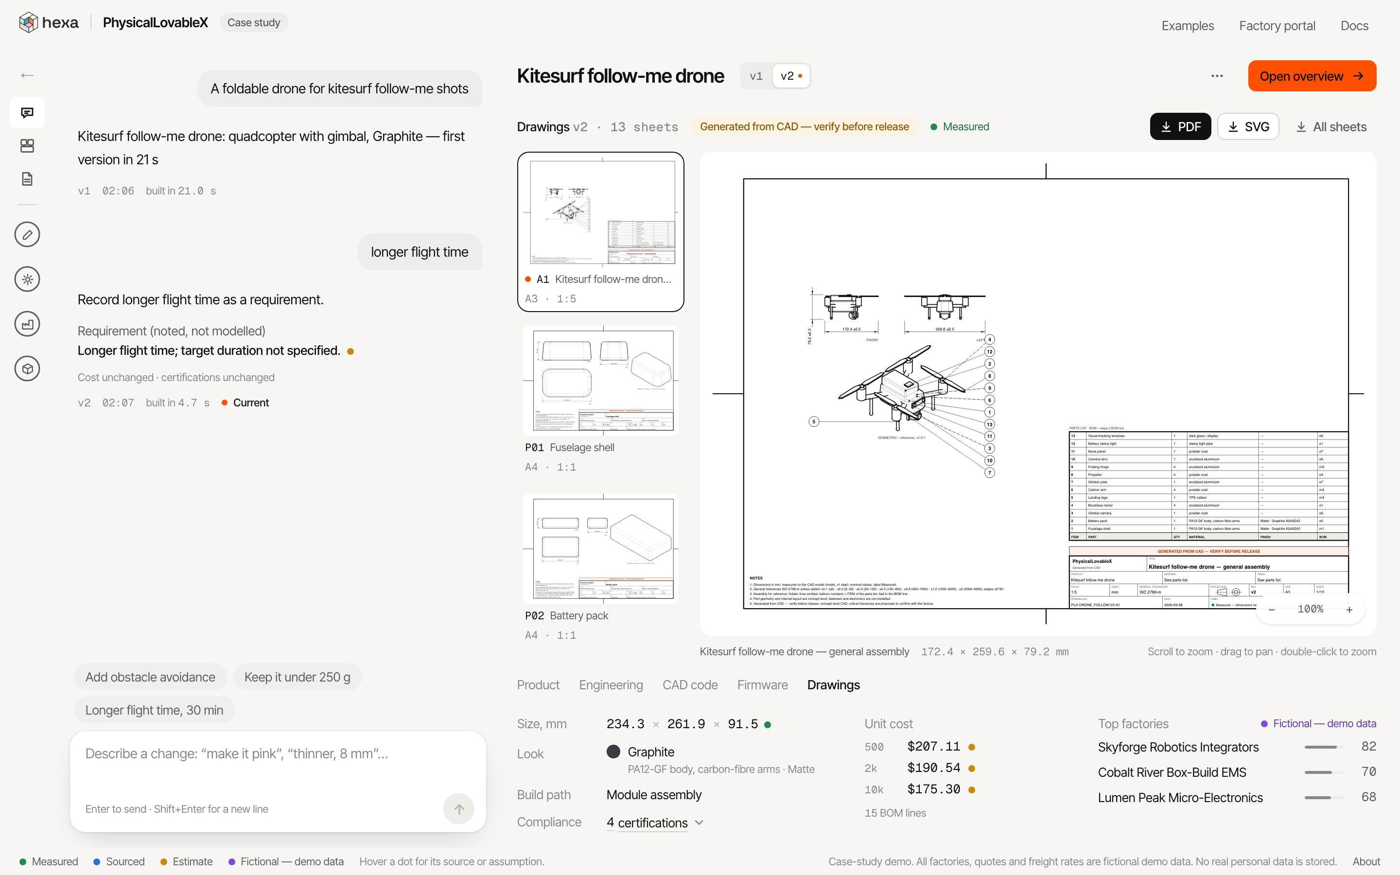
app/docs/screens/drawings/studio_drawings_drone.png
