orpheo28/physicallovablex/app/docs/screens/drawings/studio_drawings_surfboard.png

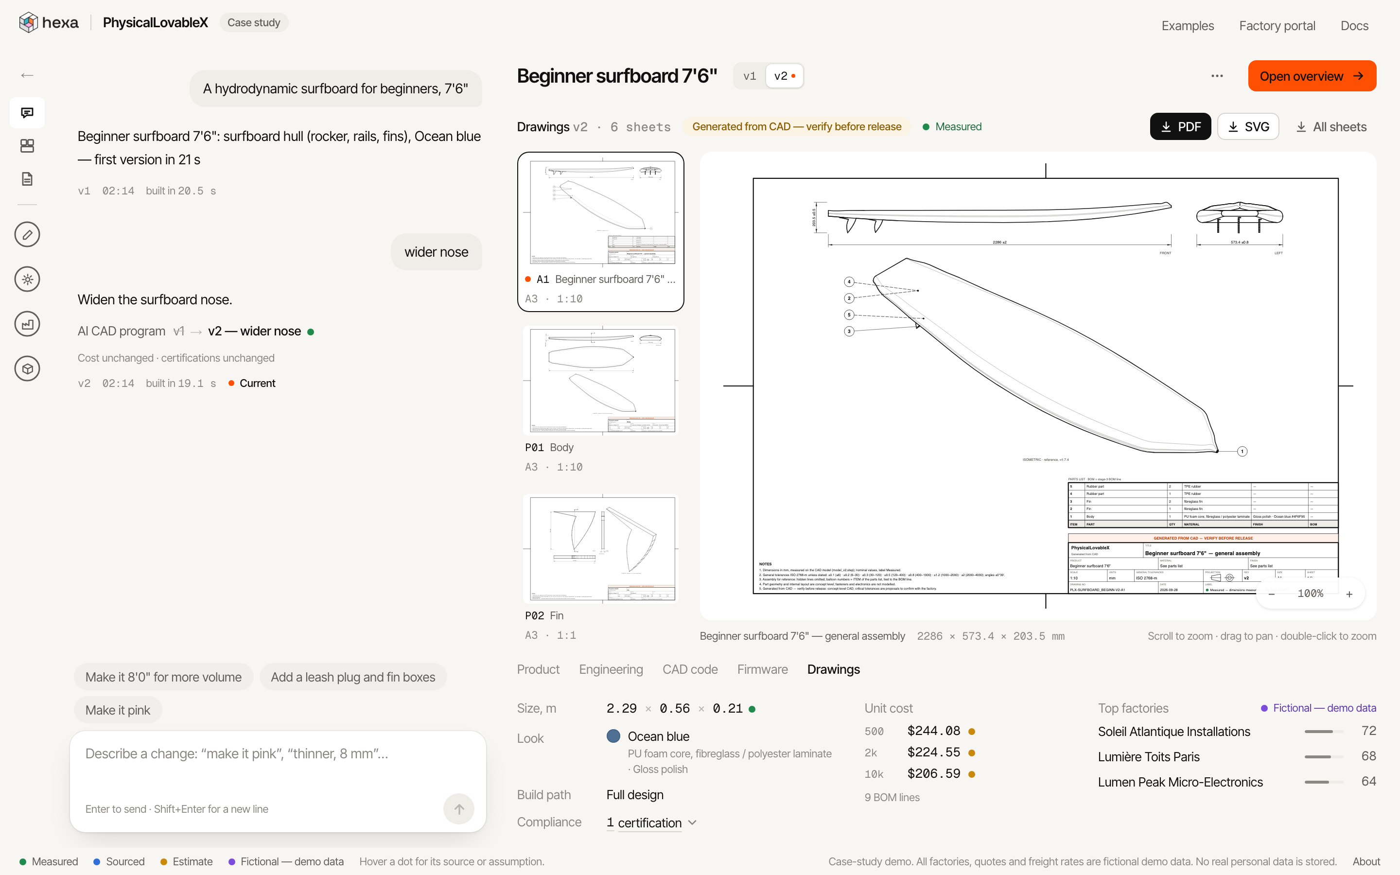
app/docs/screens/drawings/studio_drawings_surfboard.png
