orpheo28/physicallovablex/app/docs/screens/drawings/studio_drawings_vacuum.png

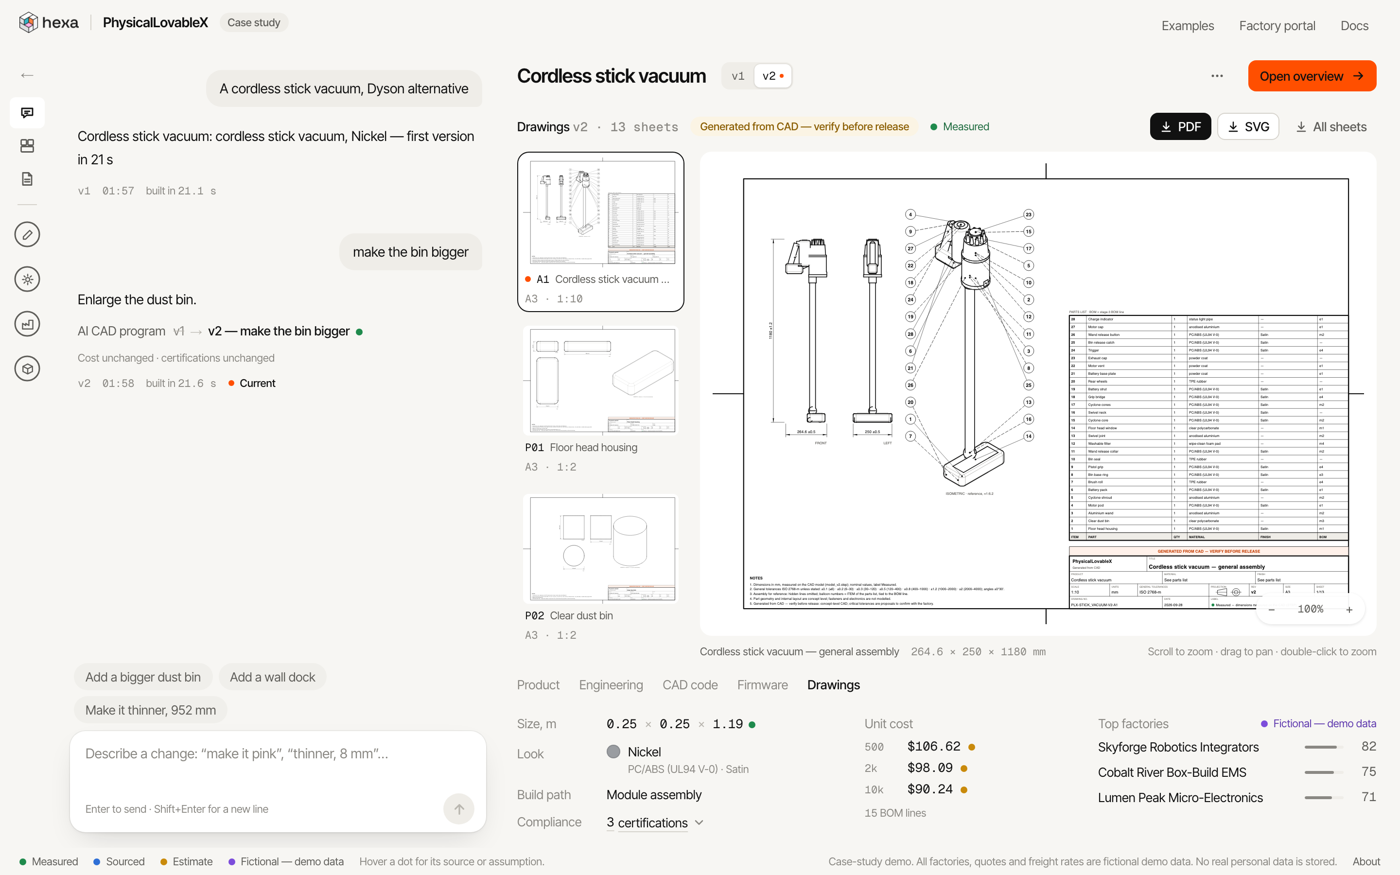
app/docs/screens/drawings/studio_drawings_vacuum.png
