orpheo28/physicallovablex/app/docs/screens/drawings/studio_drawings_whoop.png

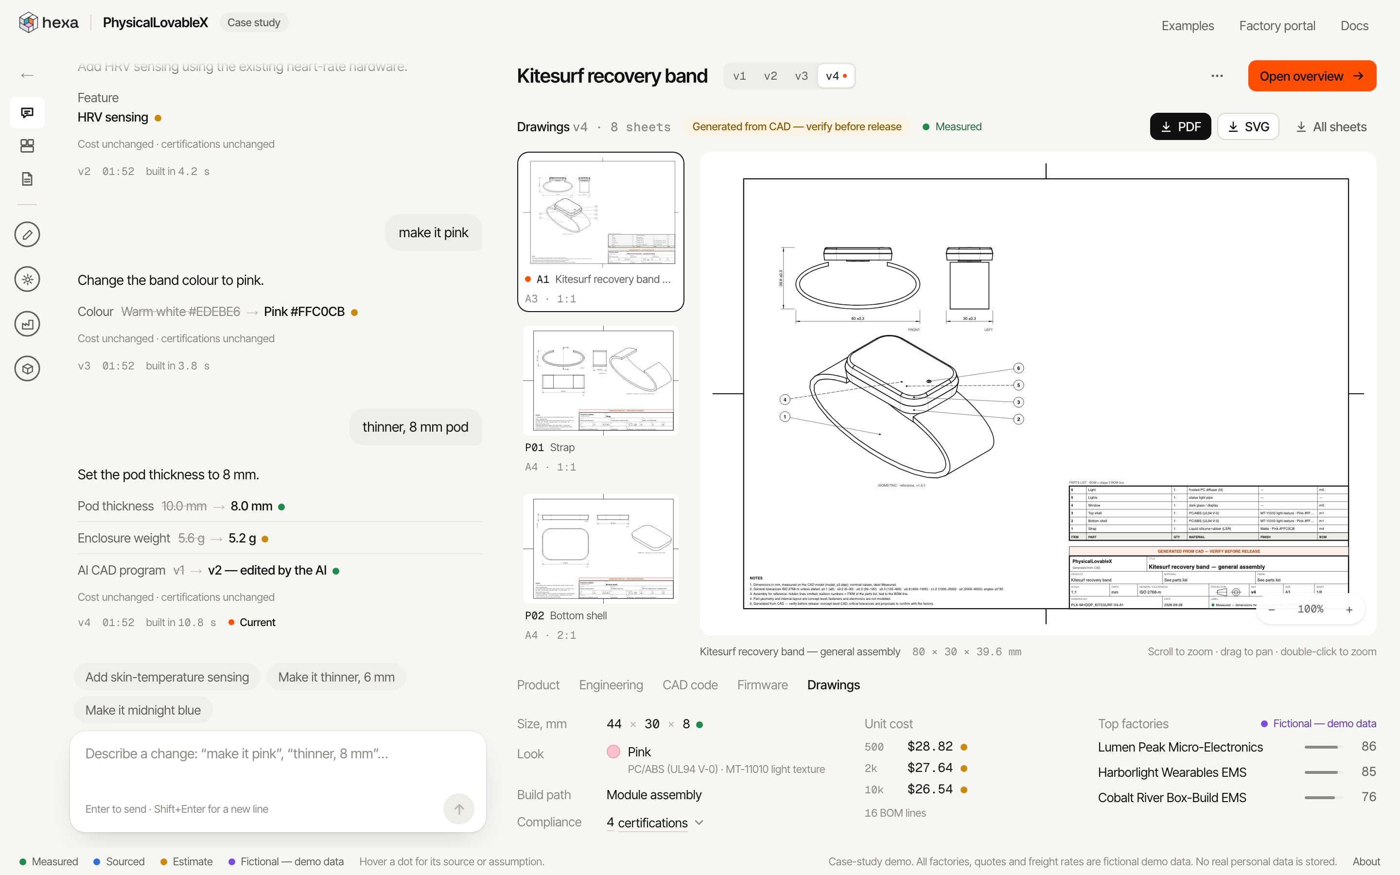
app/docs/screens/drawings/studio_drawings_whoop.png
