orpheo28/physicallovablex/app/docs/screens/drawings/studio_drawings_whoop_M01_zoom.png

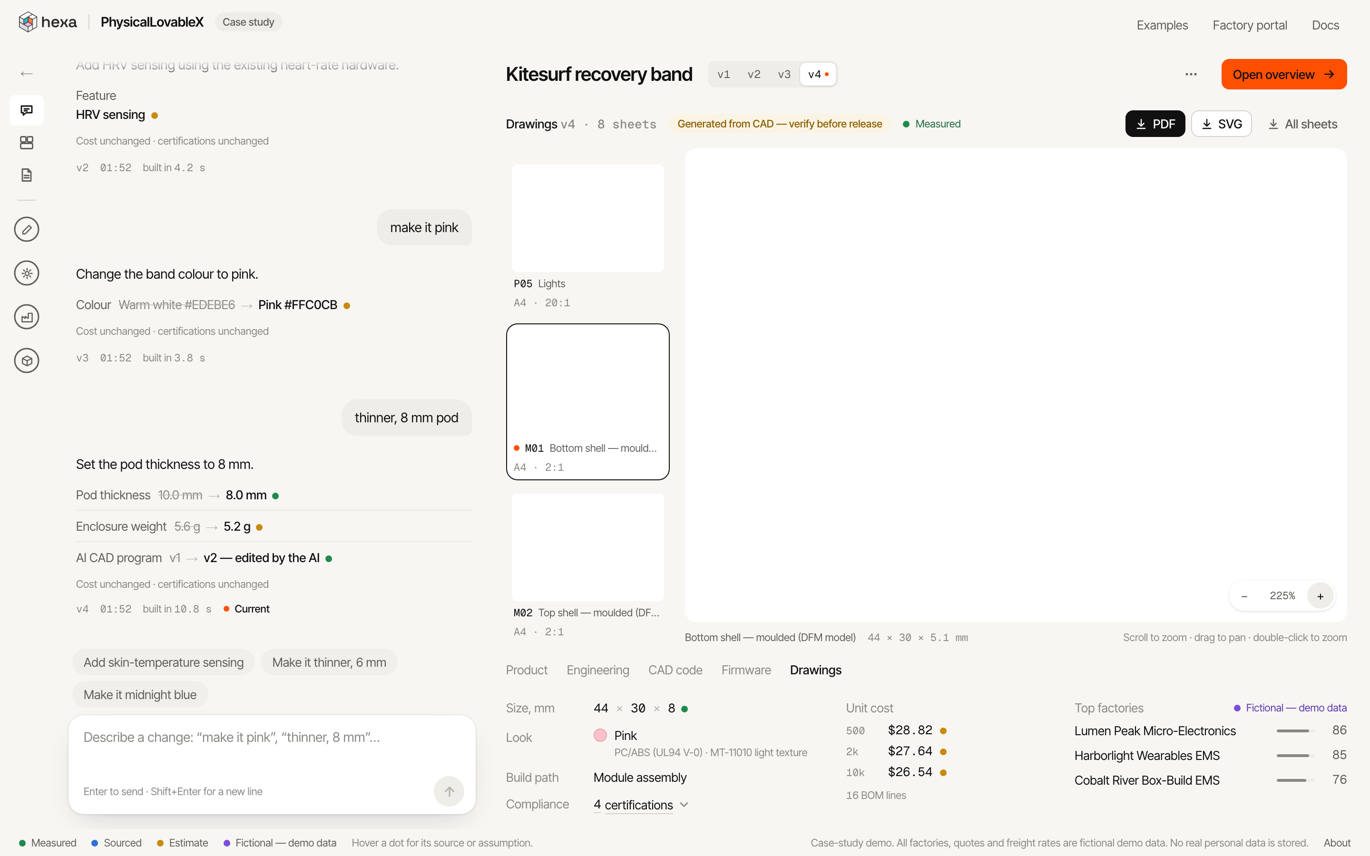
app/docs/screens/drawings/studio_drawings_whoop_M01_zoom.png
