orpheo28/physicallovablex/app/docs/screens/iterations/autorun_1.png

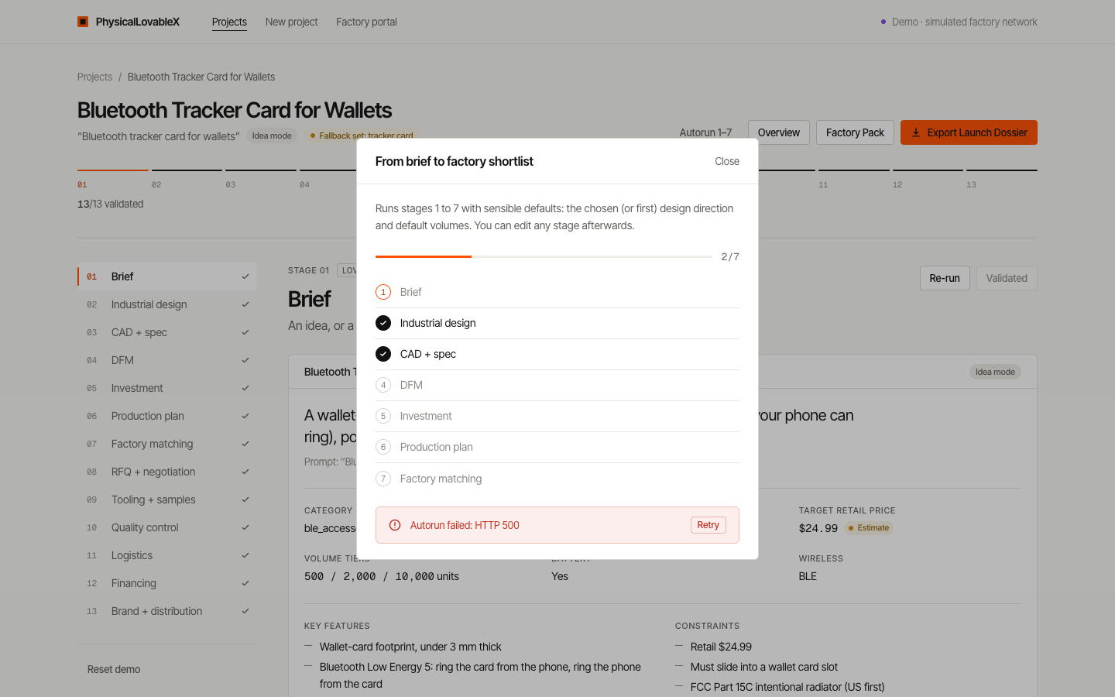
app/docs/screens/iterations/autorun_1.png
