orpheo28/physicallovablex/app/docs/screens/iterations/landing_fold.png

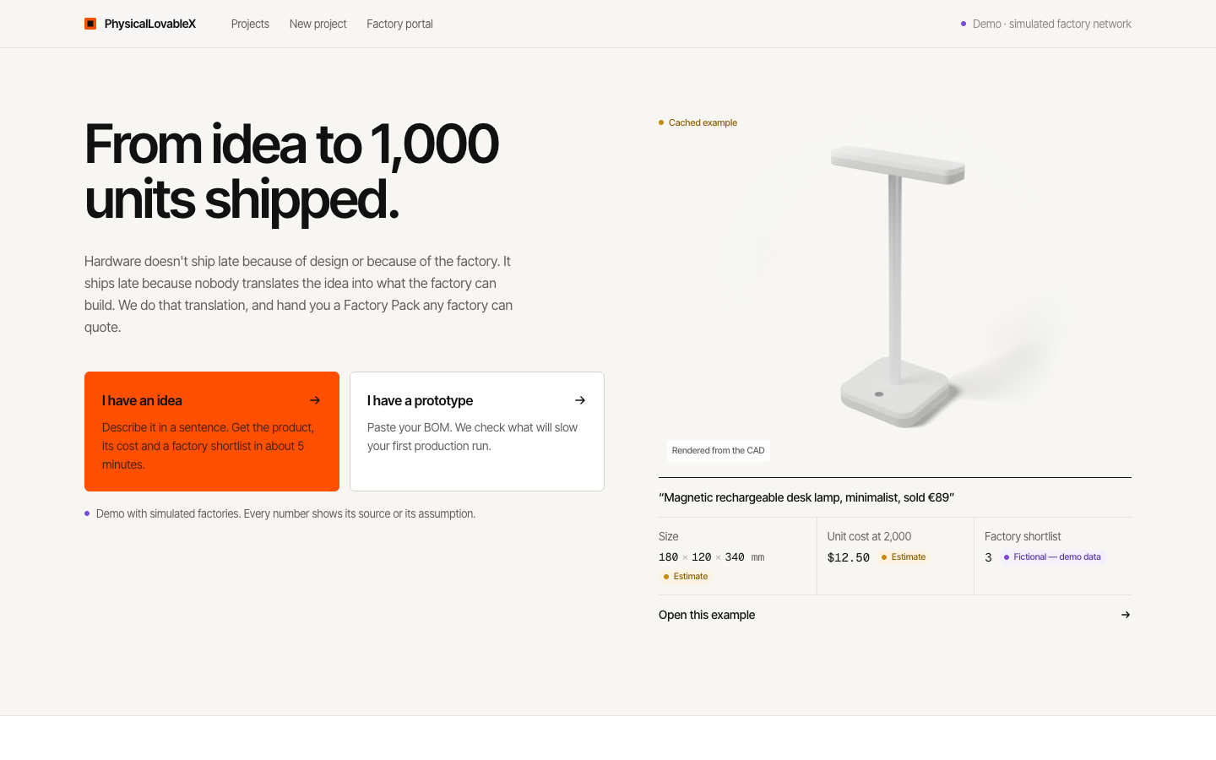
app/docs/screens/iterations/landing_fold.png
