orpheo28/physicallovablex/app/docs/screens/iterations/s3_edit.png

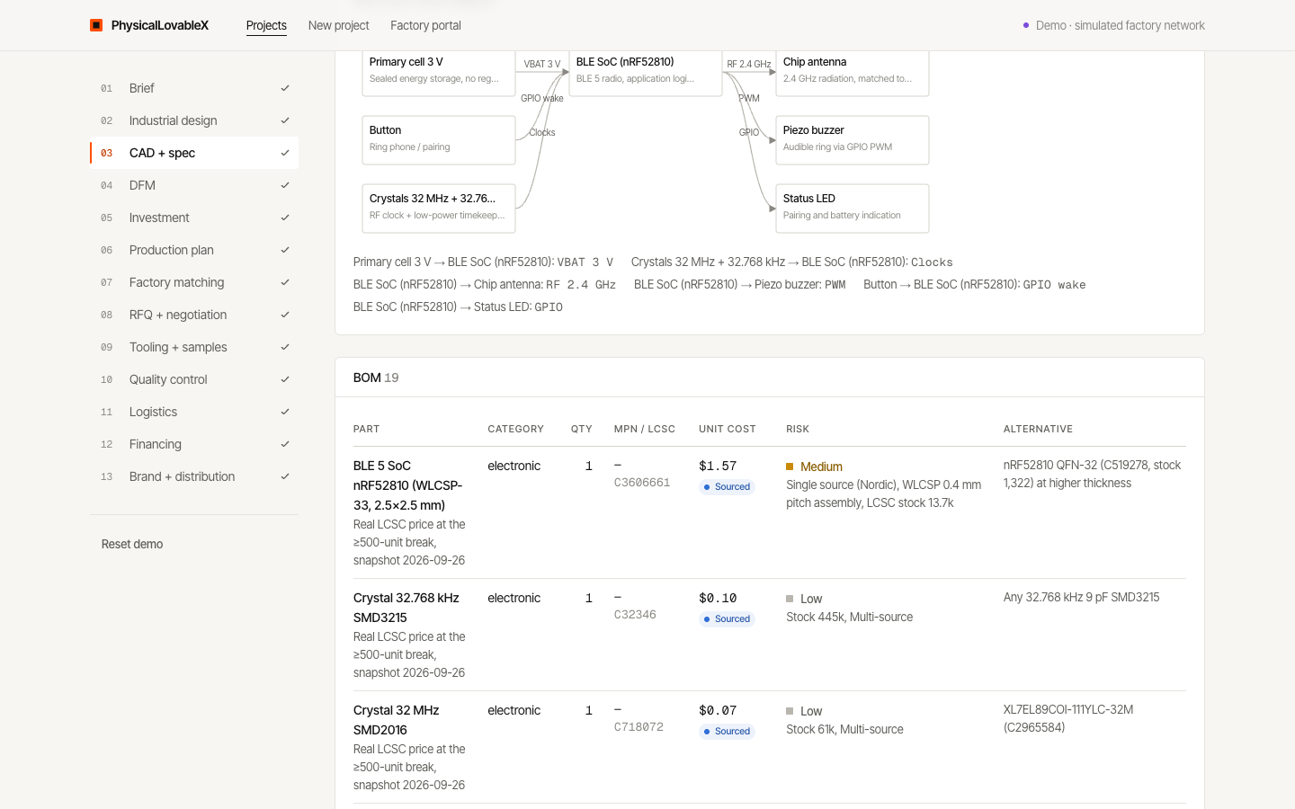
app/docs/screens/iterations/s3_edit.png
