orpheo28/physicallovablex/app/docs/screens/photos/ab/vacuum_hero_flash.png

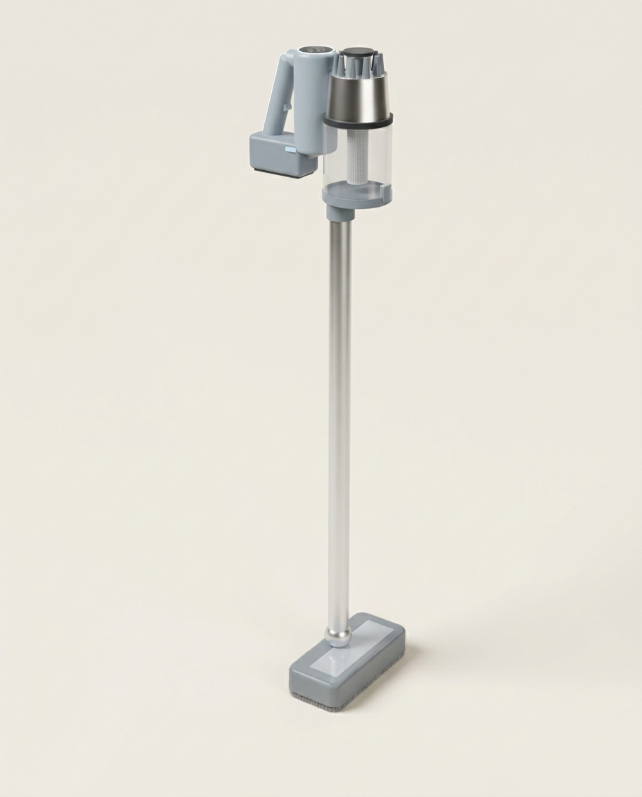
app/docs/screens/photos/ab/vacuum_hero_flash.png
