orpheo28/physicallovablex/app/docs/screens/photos/ab/vacuum_hero_pro.png

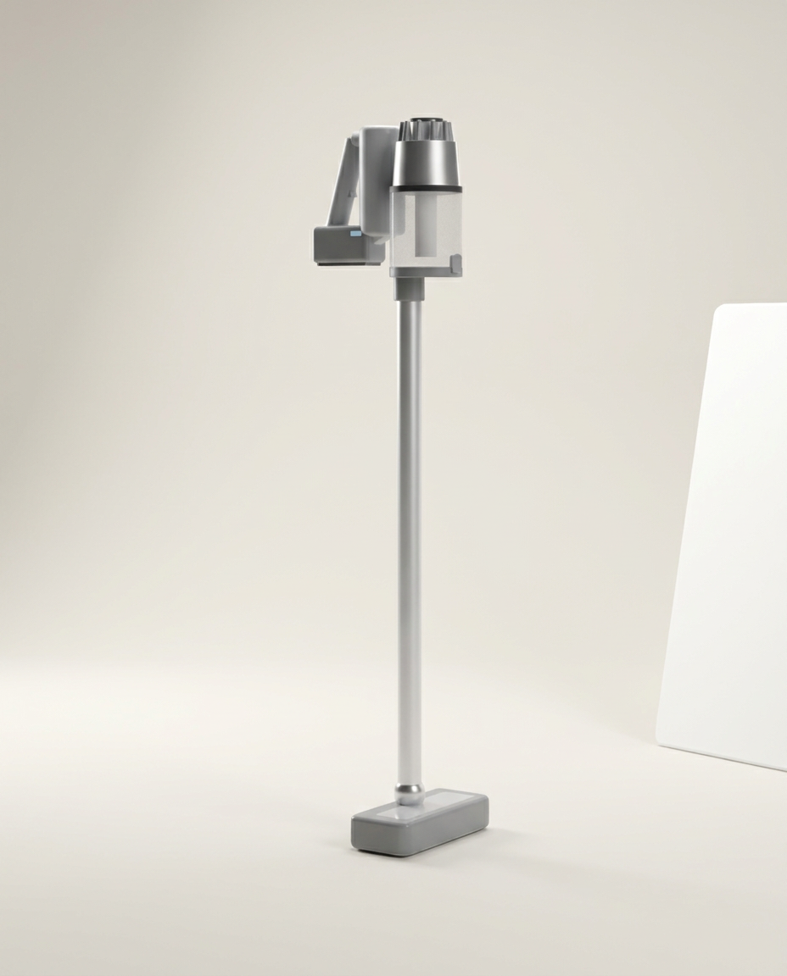
app/docs/screens/photos/ab/vacuum_hero_pro.png
