orpheo28/physicallovablex/app/docs/screens/photos/ab/whoop_hero_flash.png

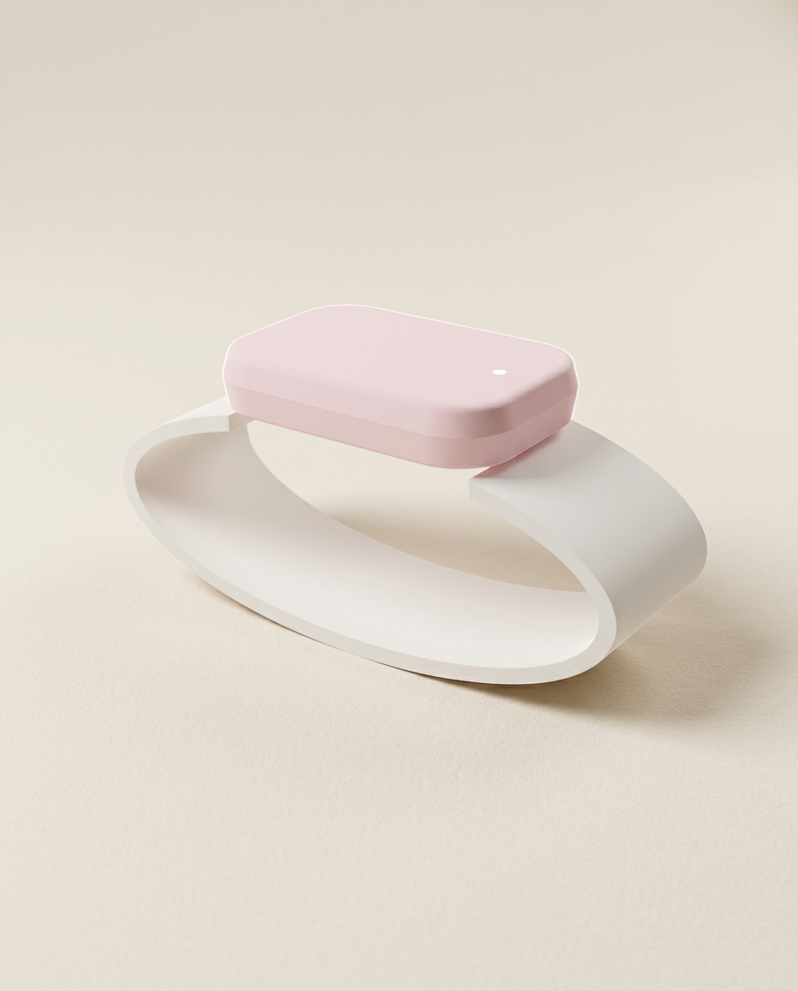
app/docs/screens/photos/ab/whoop_hero_flash.png
