orpheo28/physicallovablex/app/docs/screens/photos/ab/whoop_hero_pro.png

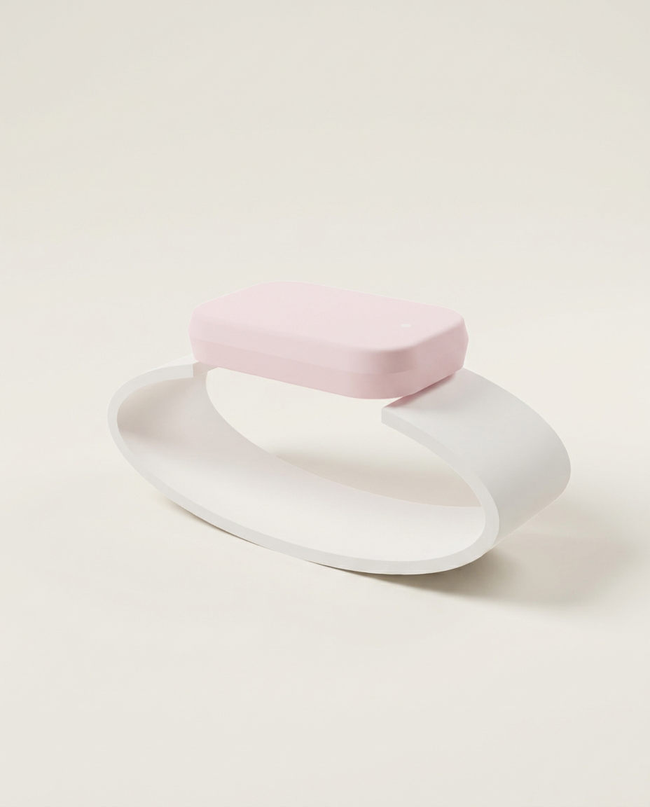
app/docs/screens/photos/ab/whoop_hero_pro.png
