orpheo28/physicallovablex/app/docs/screens/photos/kit/stick_vacuum_detail_macro.png

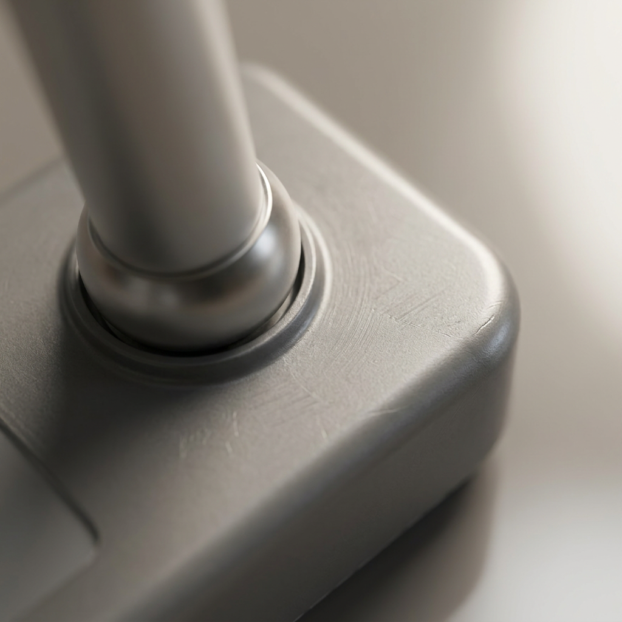
app/docs/screens/photos/kit/stick_vacuum_detail_macro.png
