orpheo28/physicallovablex/app/docs/screens/photos/kit/stick_vacuum_in_hand_scale.png

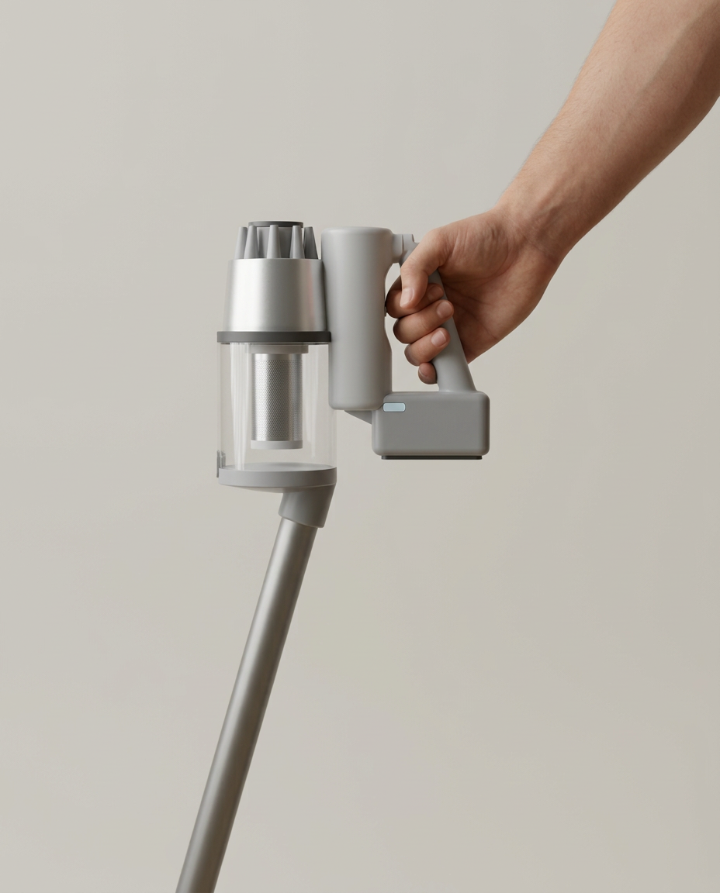
app/docs/screens/photos/kit/stick_vacuum_in_hand_scale.png
