orpheo28/physicallovablex/app/docs/screens/photos/kit/stick_vacuum_lifestyle.png

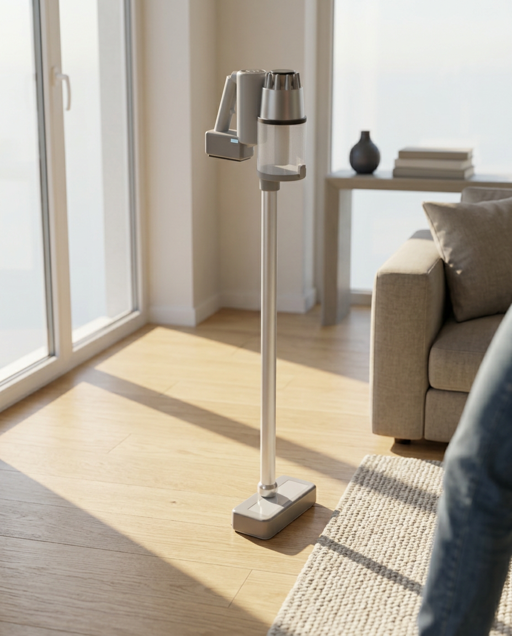
app/docs/screens/photos/kit/stick_vacuum_lifestyle.png
