orpheo28/physicallovablex/app/docs/screens/photos/kit/stick_vacuum_packshot_white.png

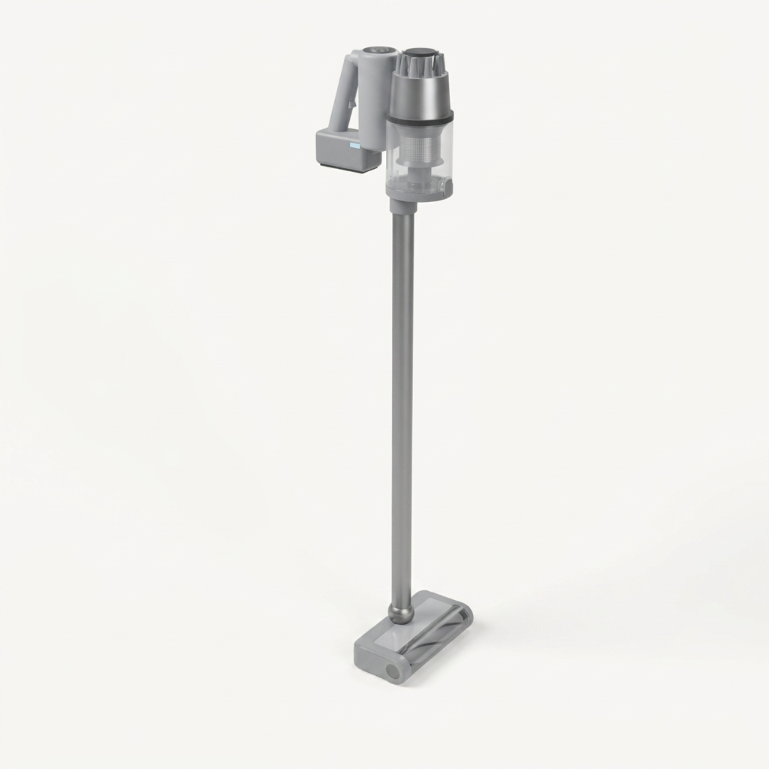
app/docs/screens/photos/kit/stick_vacuum_packshot_white.png
