orpheo28/physicallovablex/app/docs/screens/photos/showcases/contact_cad_references.png

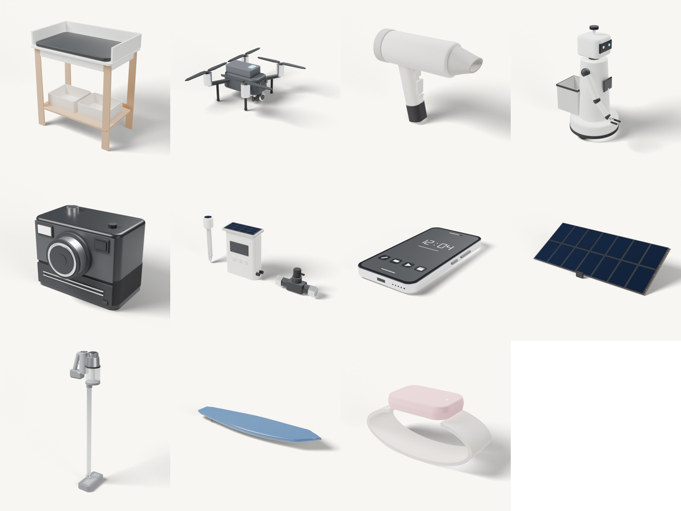
app/docs/screens/photos/showcases/contact_cad_references.png
