orpheo28/physicallovablex/app/docs/screens/photos/showcases/contact_lifestyle.png

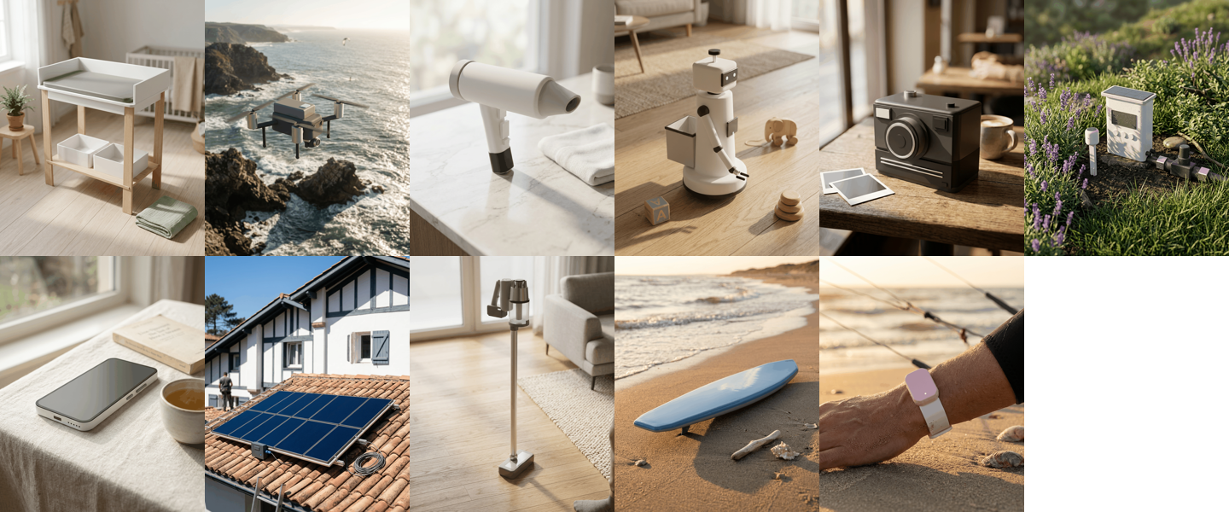
app/docs/screens/photos/showcases/contact_lifestyle.png
