orpheo28/physicallovablex/app/docs/screens/v4/after/anatomy_drone_inside.png

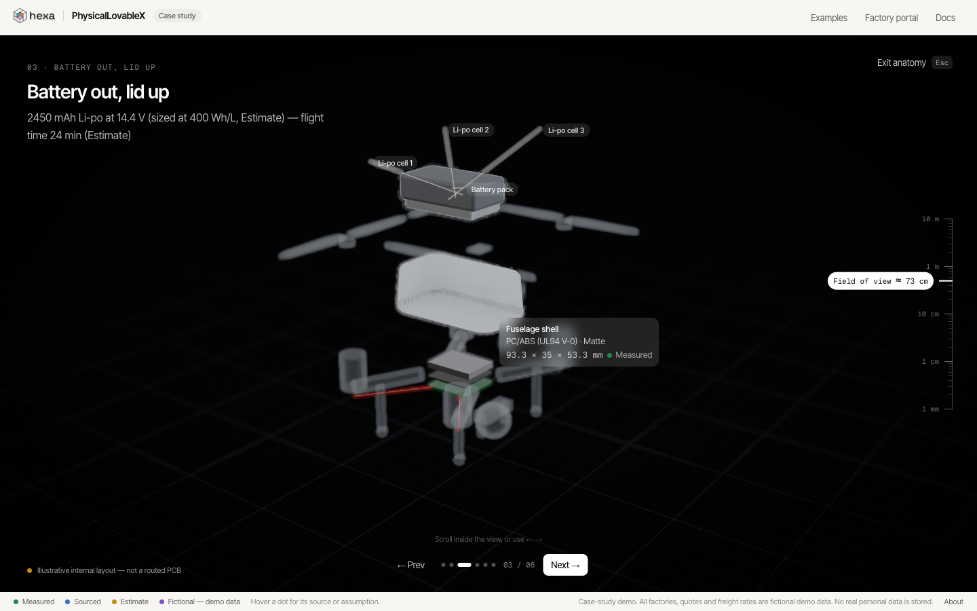
app/docs/screens/v4/after/anatomy_drone_inside.png
