orpheo28/physicallovablex/app/docs/screens/v4/after/studio_drone_xray.png

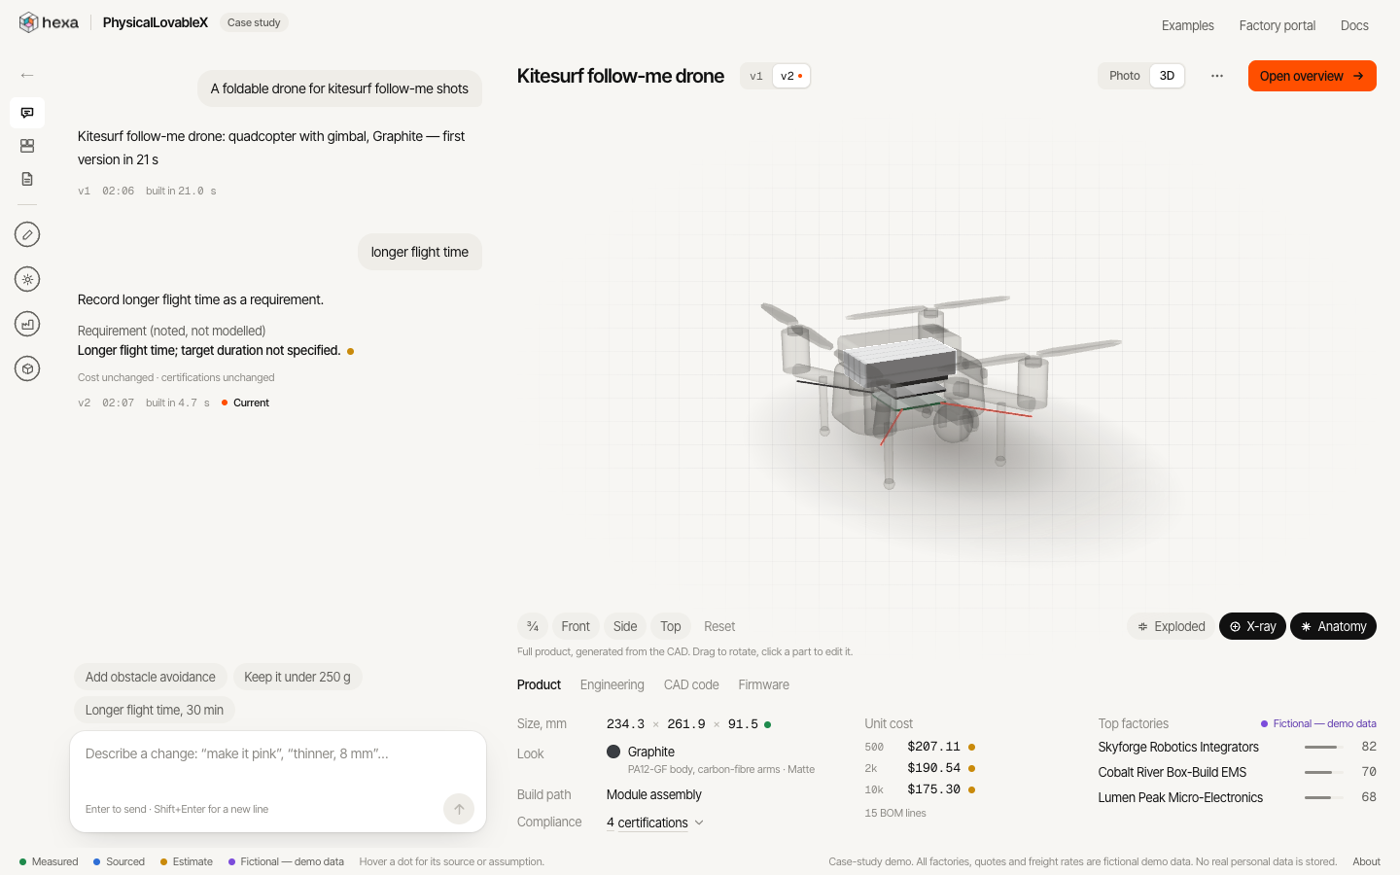
app/docs/screens/v4/after/studio_drone_xray.png
