orpheo28/physicallovablex/app/docs/screens/v4/after/studio_whoop.png

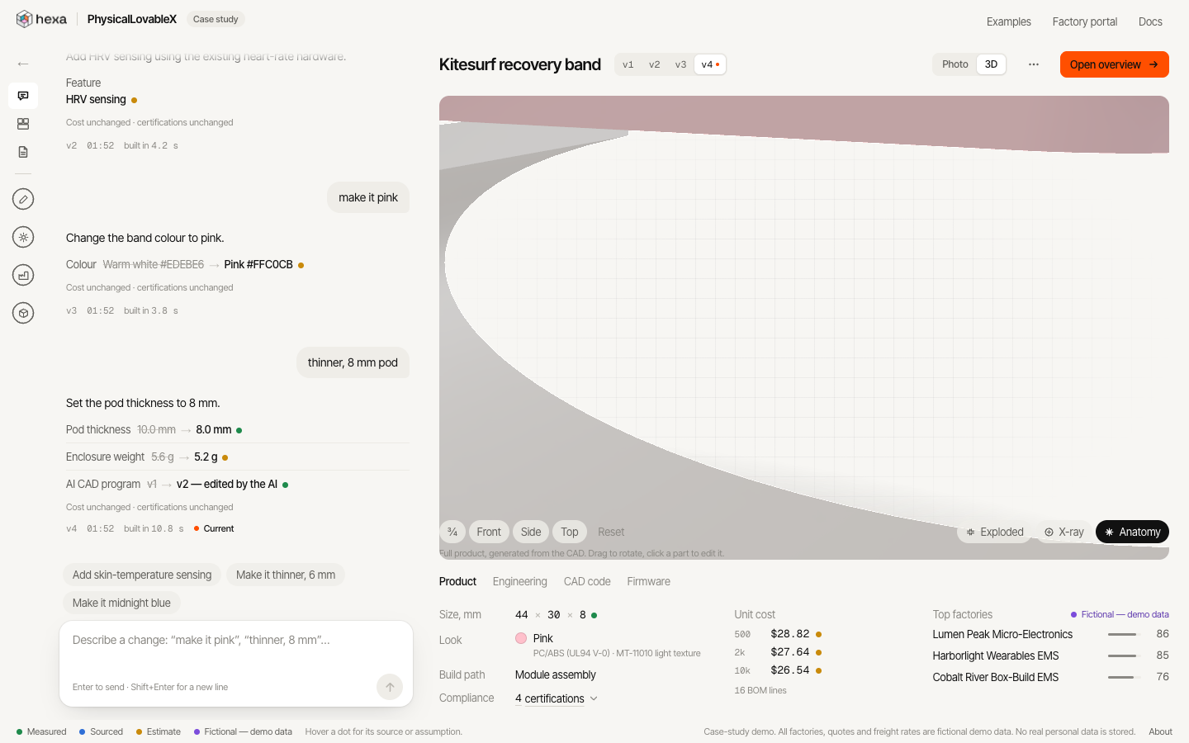
app/docs/screens/v4/after/studio_whoop.png
