orpheo28/physicallovablex/app/docs/screens/v4/after/w28b_desk_lamp_part_card.png

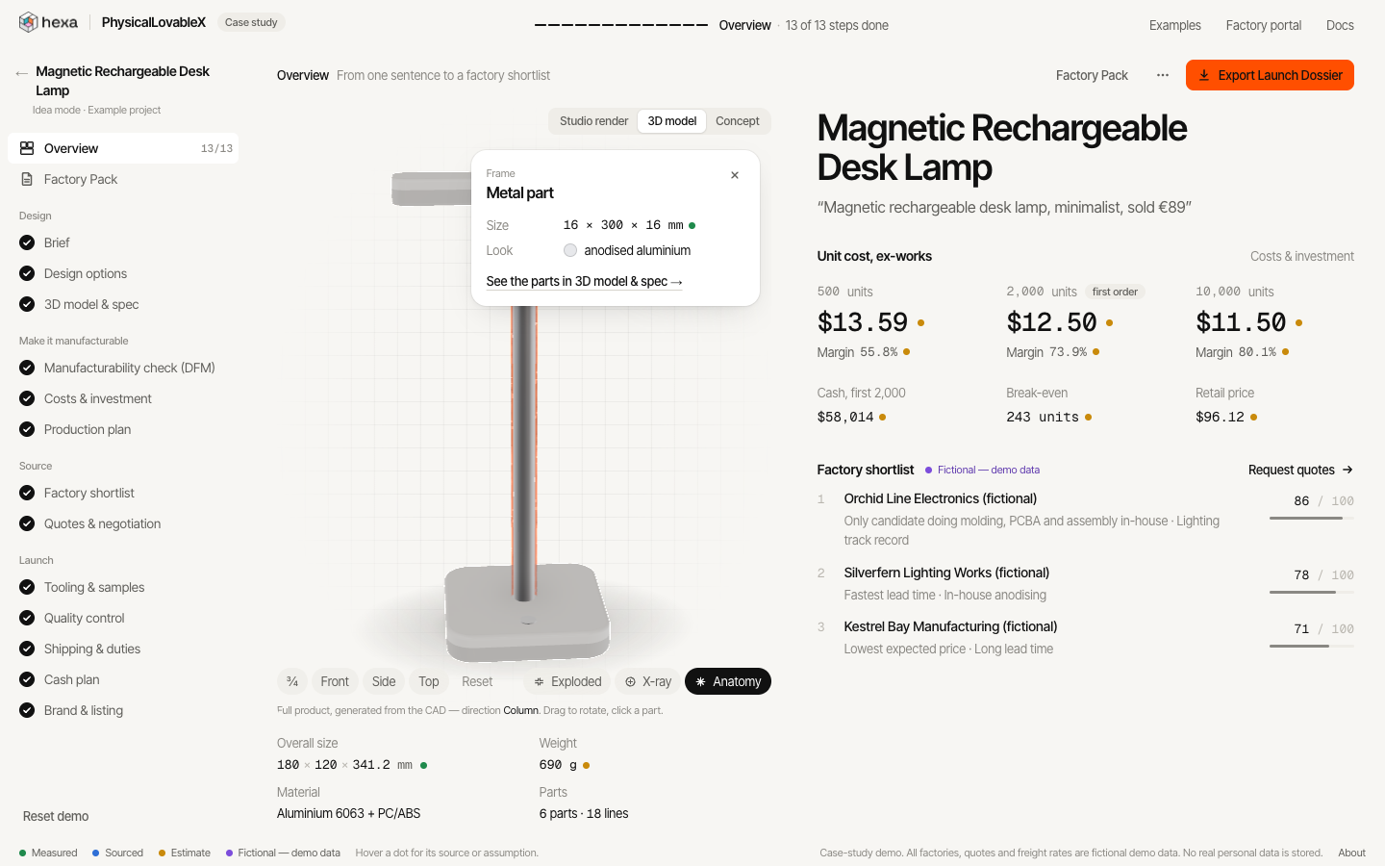
app/docs/screens/v4/after/w28b_desk_lamp_part_card.png
