orpheo28/physicallovablex/app/docs/screens/v4/after/w28b_desk_lamp_studio.png

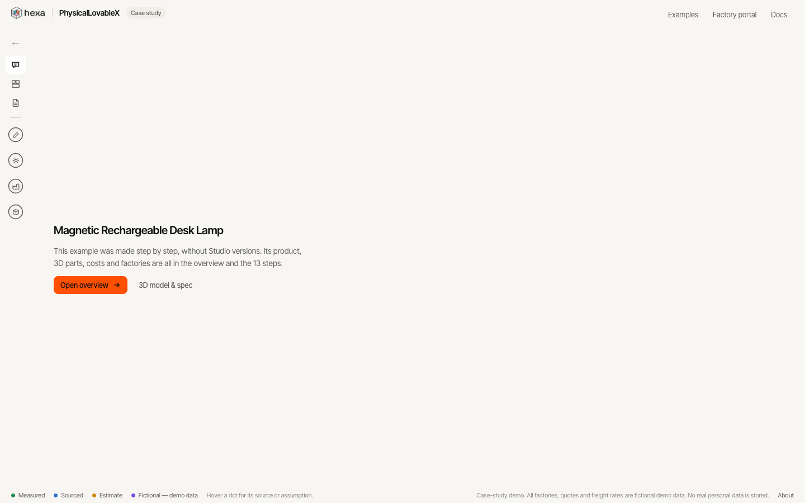
app/docs/screens/v4/after/w28b_desk_lamp_studio.png
