orpheo28/physicallovablex/app/docs/screens/v4/after/w28b_drone_follow_exploded.png

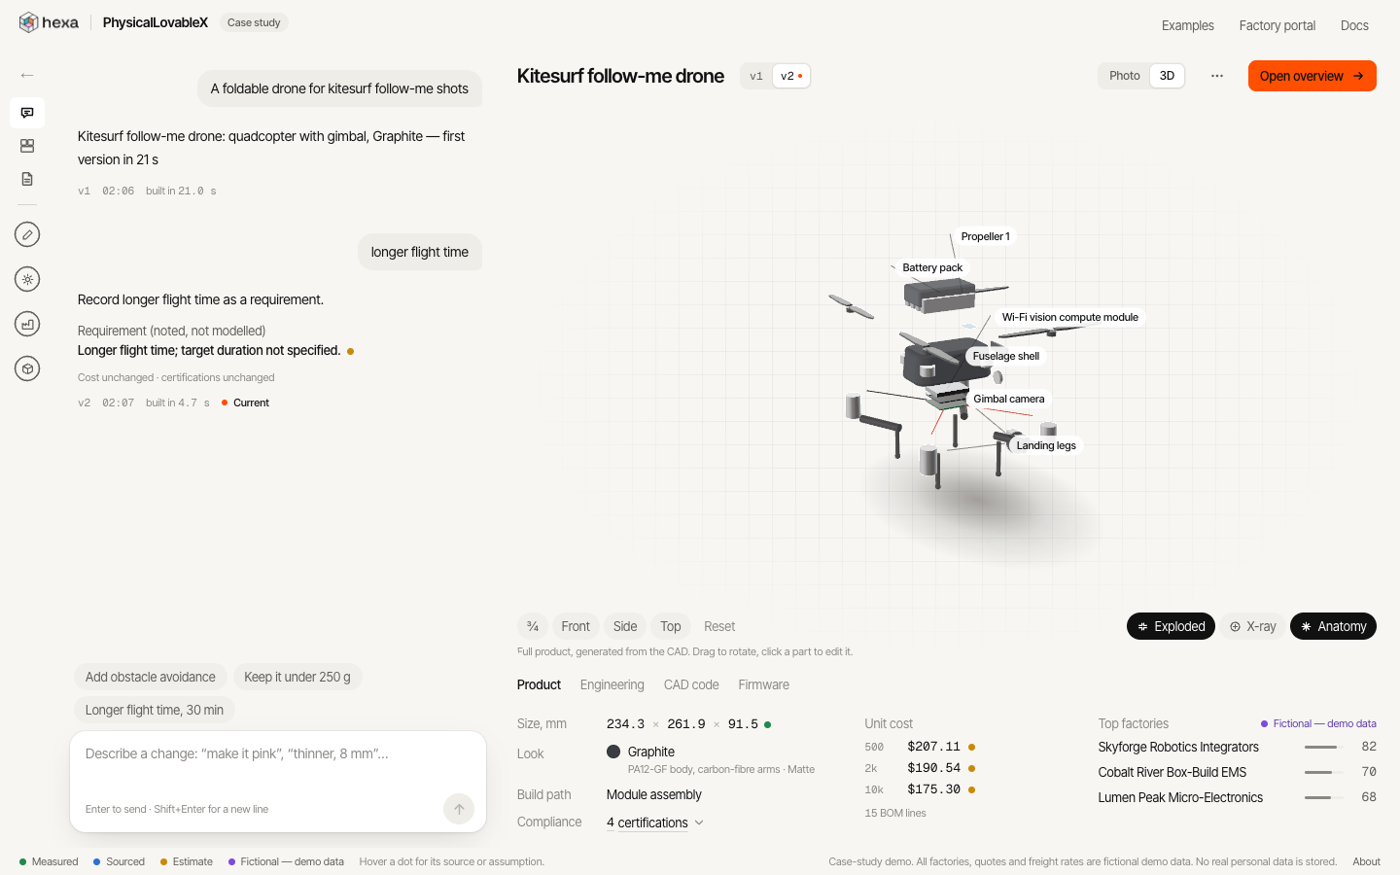
app/docs/screens/v4/after/w28b_drone_follow_exploded.png
