orpheo28/physicallovablex/app/docs/screens/v4/after/w28b_photo_stale_studio.png

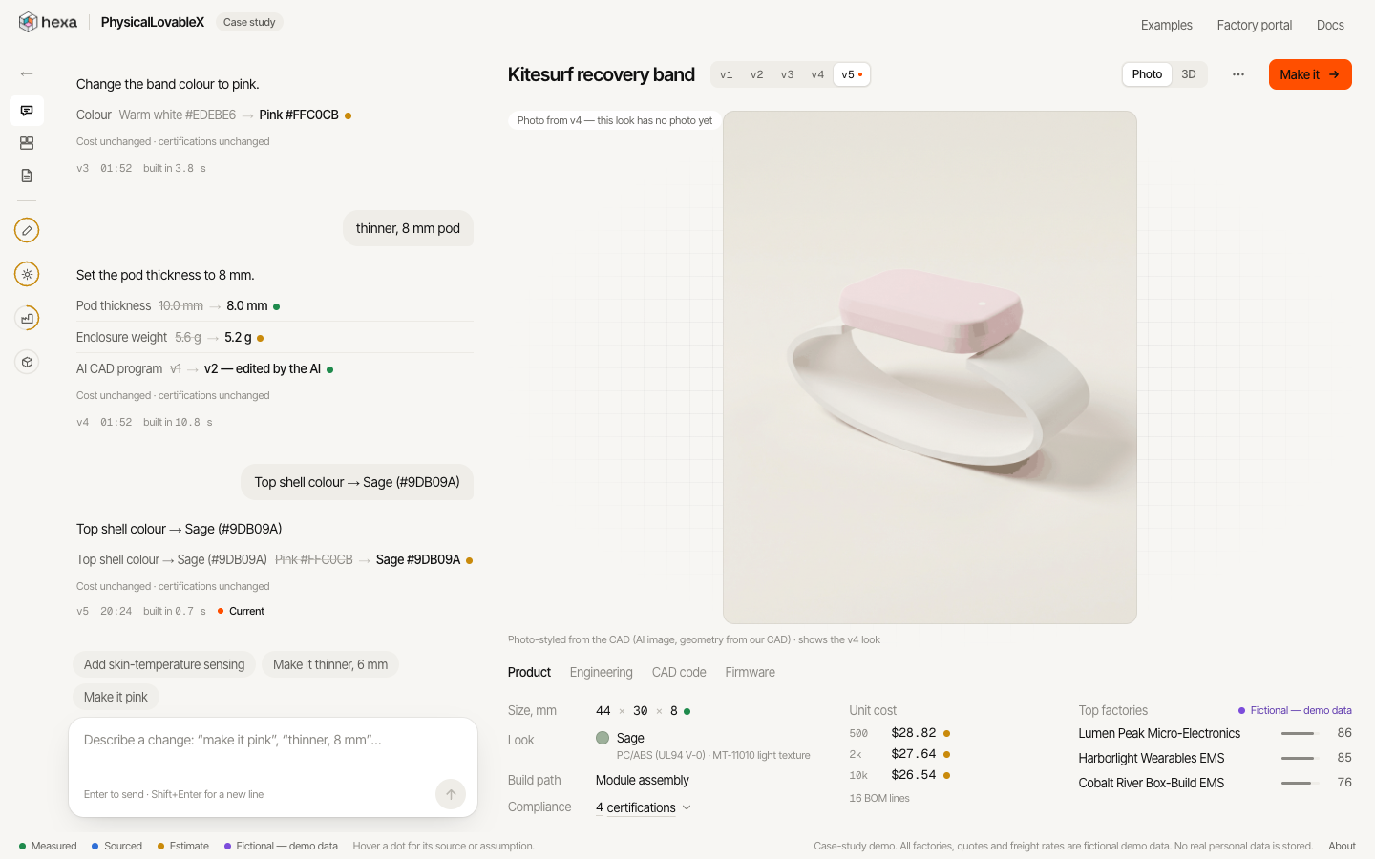
app/docs/screens/v4/after/w28b_photo_stale_studio.png
