orpheo28/physicallovablex/app/docs/screens/v4/after/w28b_stick_vacuum_exploded.png

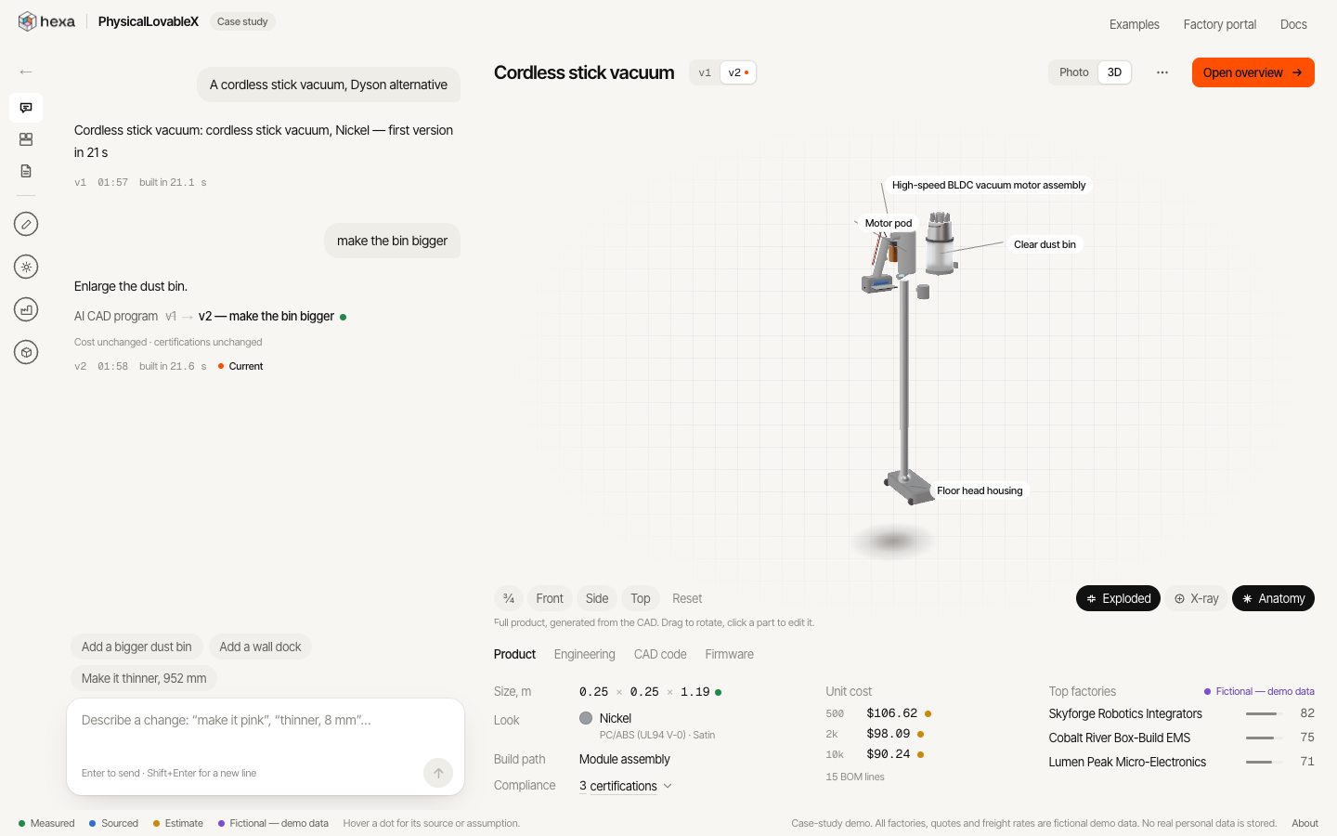
app/docs/screens/v4/after/w28b_stick_vacuum_exploded.png
