orpheo28/physicallovablex/app/docs/screens/v4/after/w28b_whoop_kitesurf_exploded.png

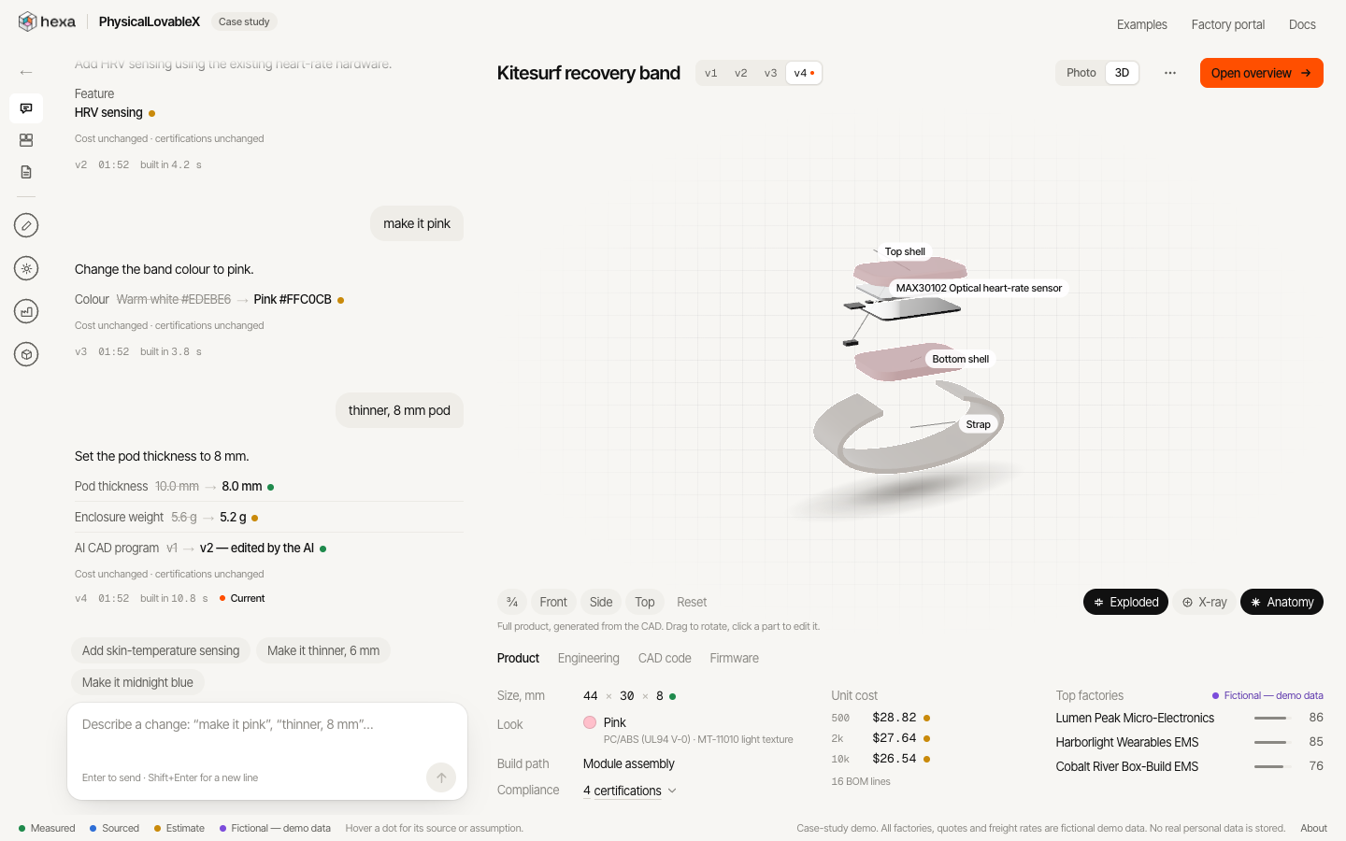
app/docs/screens/v4/after/w28b_whoop_kitesurf_exploded.png
