orpheo28/physicallovablex/gtm/fantom_screens/00_fullpage_1440.png

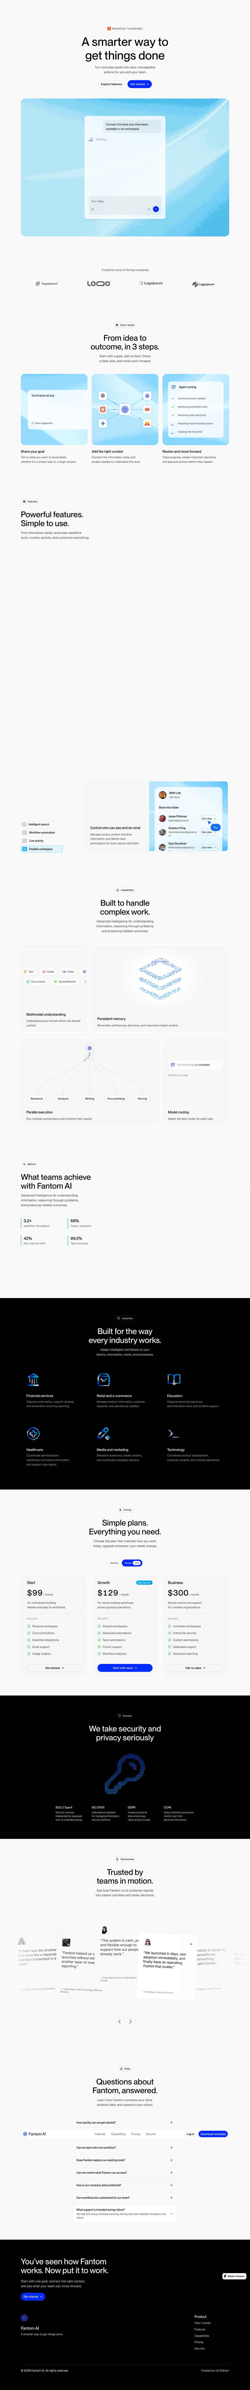
gtm/fantom_screens/00_fullpage_1440.png
