orpheo28/physicallovablex/gtm/fantom_screens/01_hero.png

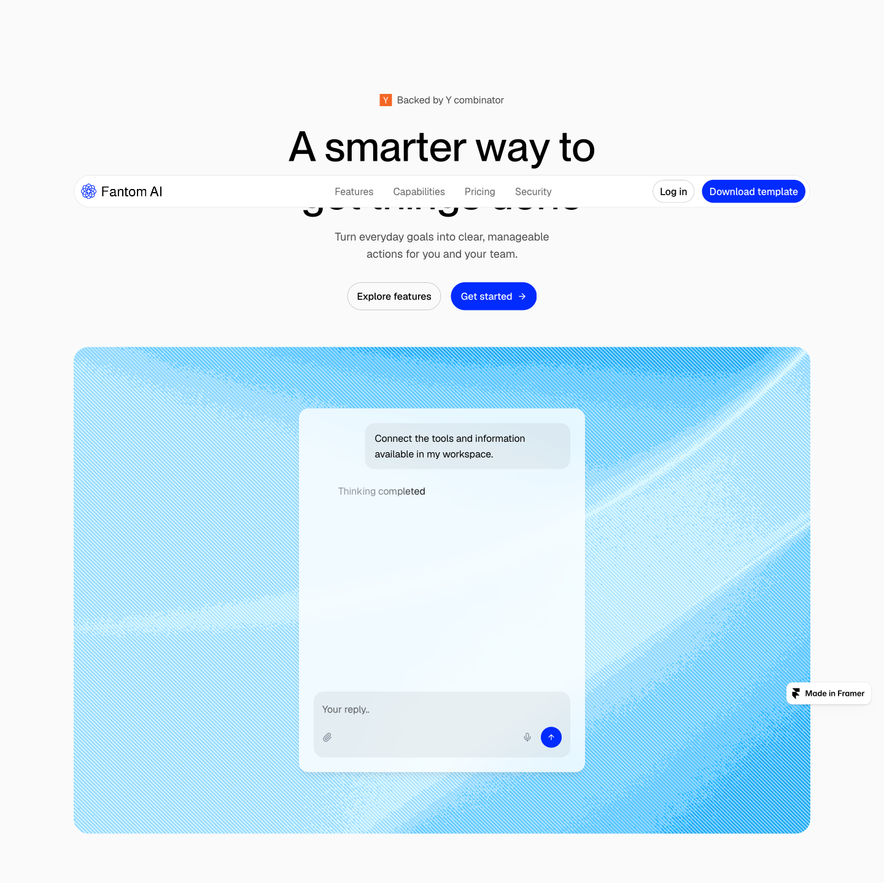
gtm/fantom_screens/01_hero.png
