orpheo28/physicallovablex/gtm/fantom_screens/02_how-it-works.png

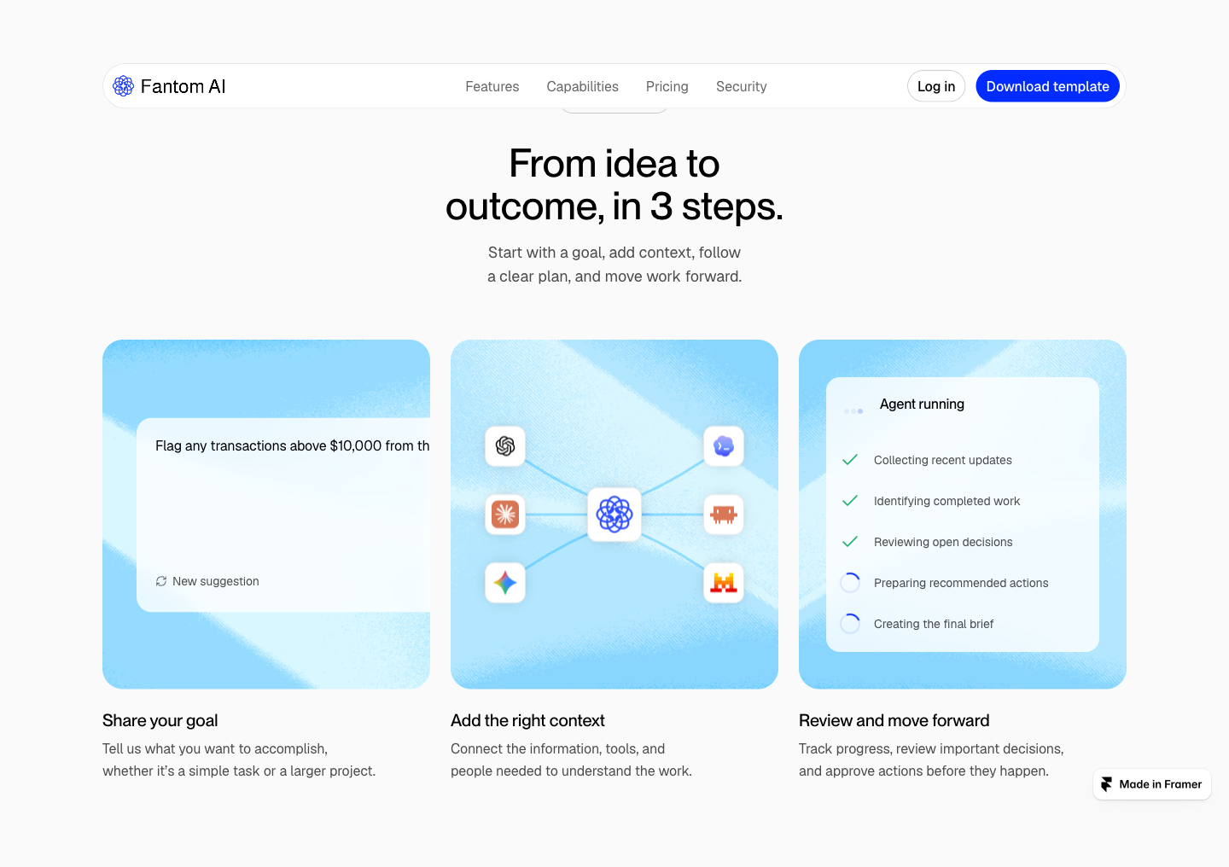
gtm/fantom_screens/02_how-it-works.png
