orpheo28/physicallovablex/gtm/fantom_screens/03_features.png

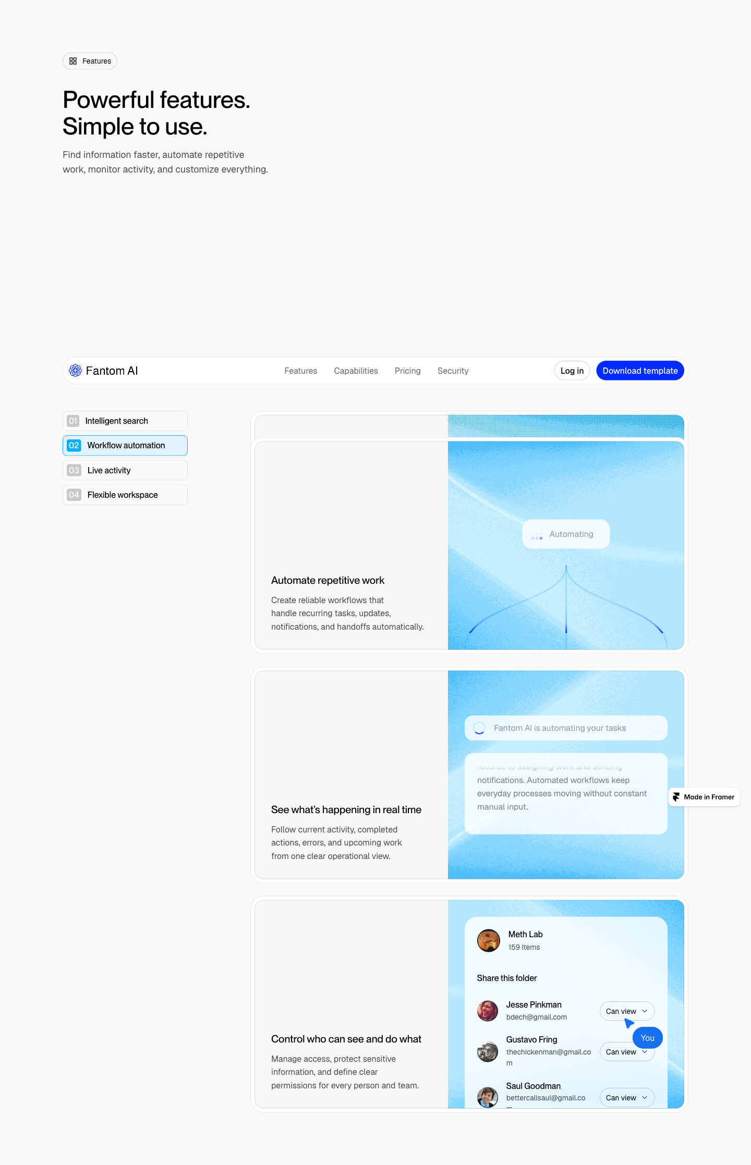
gtm/fantom_screens/03_features.png
