orpheo28/physicallovablex/gtm/fantom_screens/04_capabilities.png

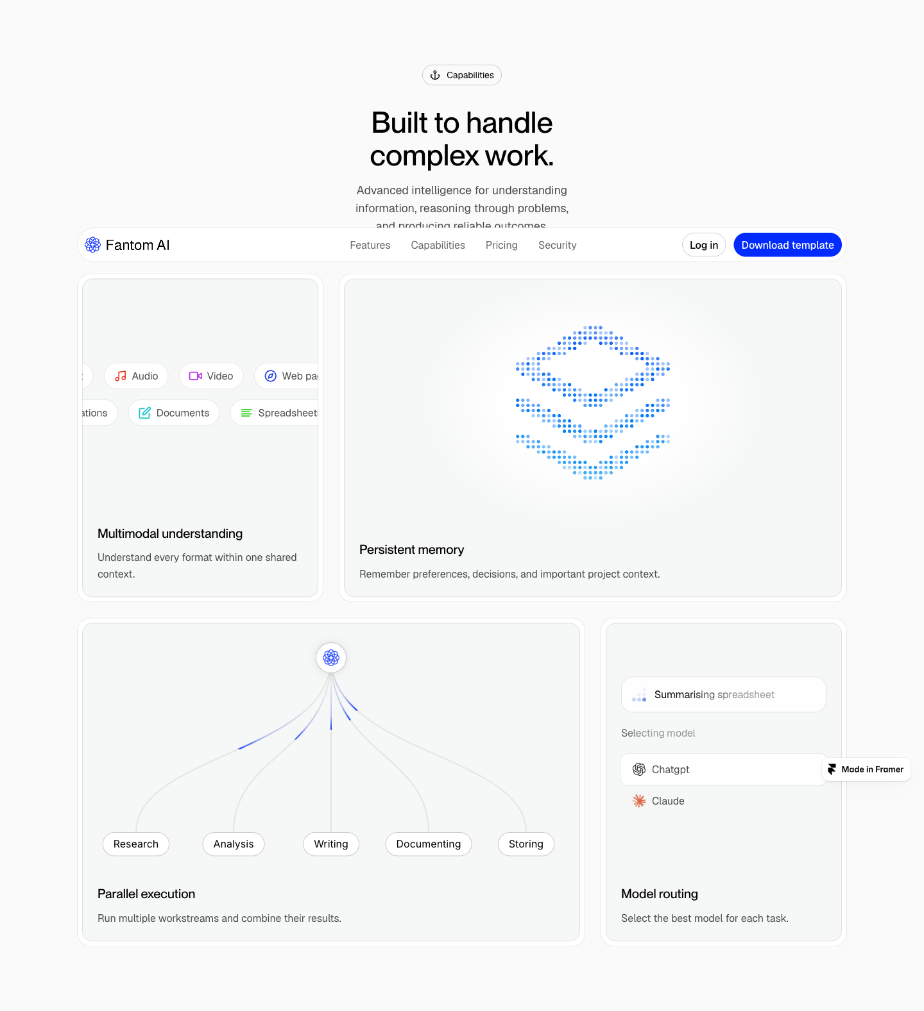
gtm/fantom_screens/04_capabilities.png
