orpheo28/physicallovablex/gtm/fantom_screens/05_metrics.png

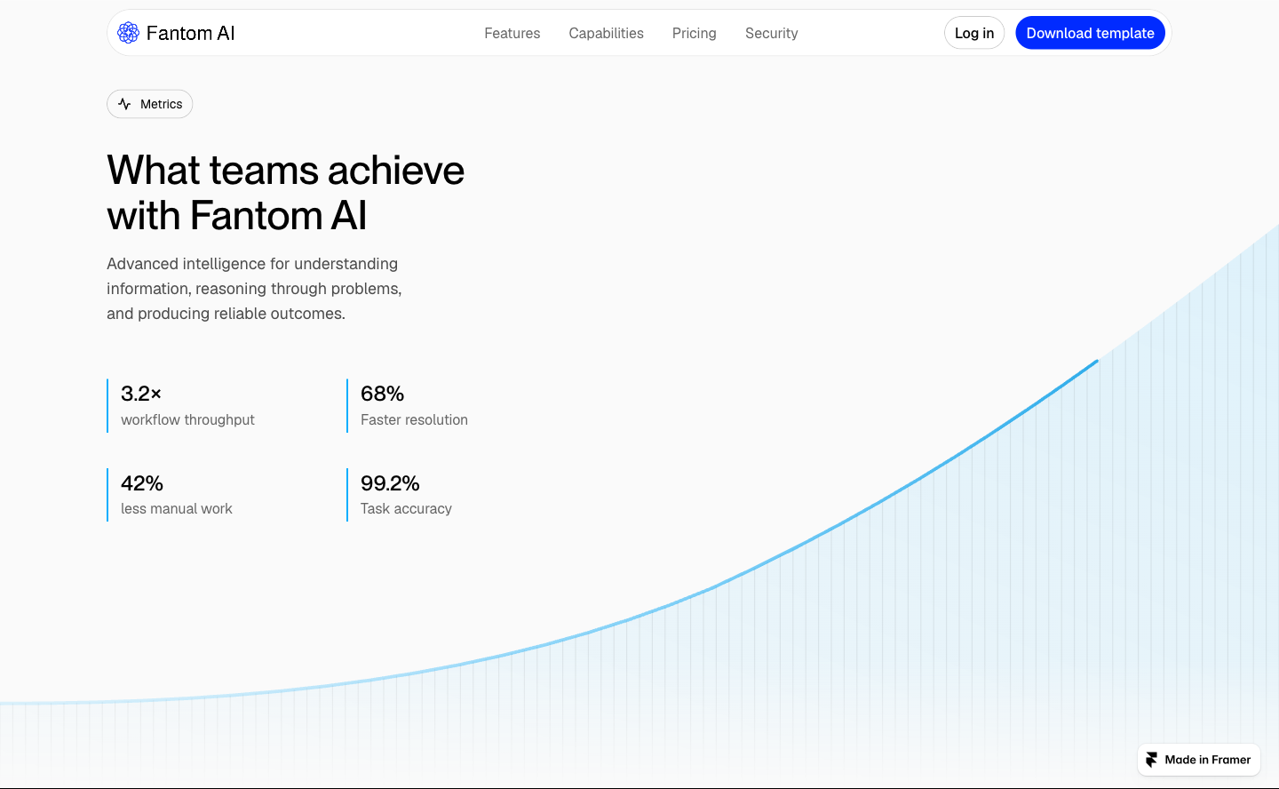
gtm/fantom_screens/05_metrics.png
