orpheo28/physicallovablex/gtm/fantom_screens/06_industries.png

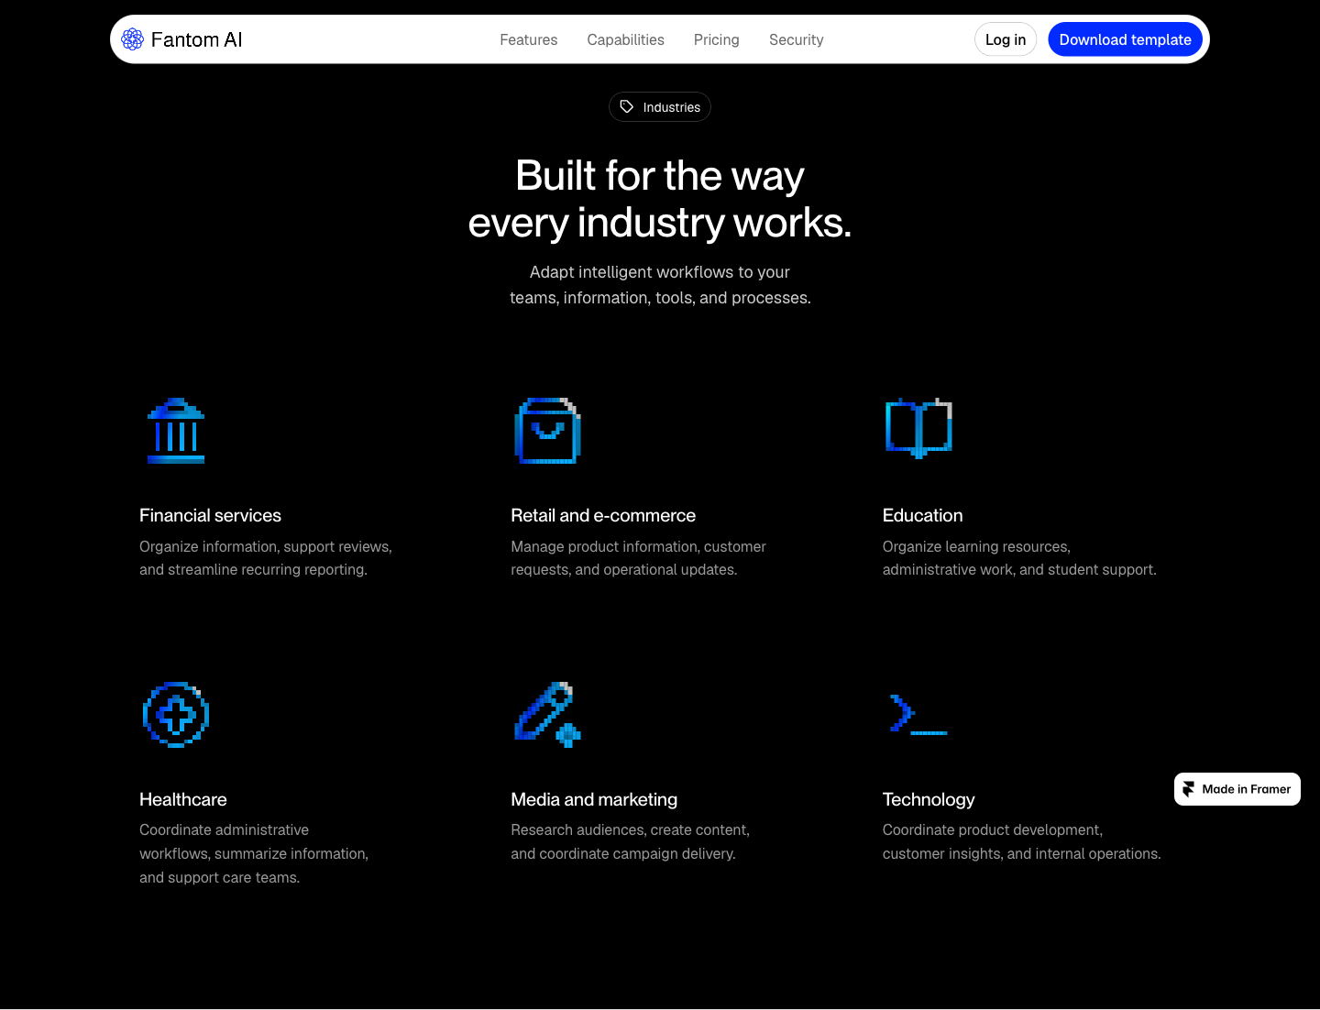
gtm/fantom_screens/06_industries.png
