orpheo28/physicallovablex/gtm/fantom_screens/07_pricing.png

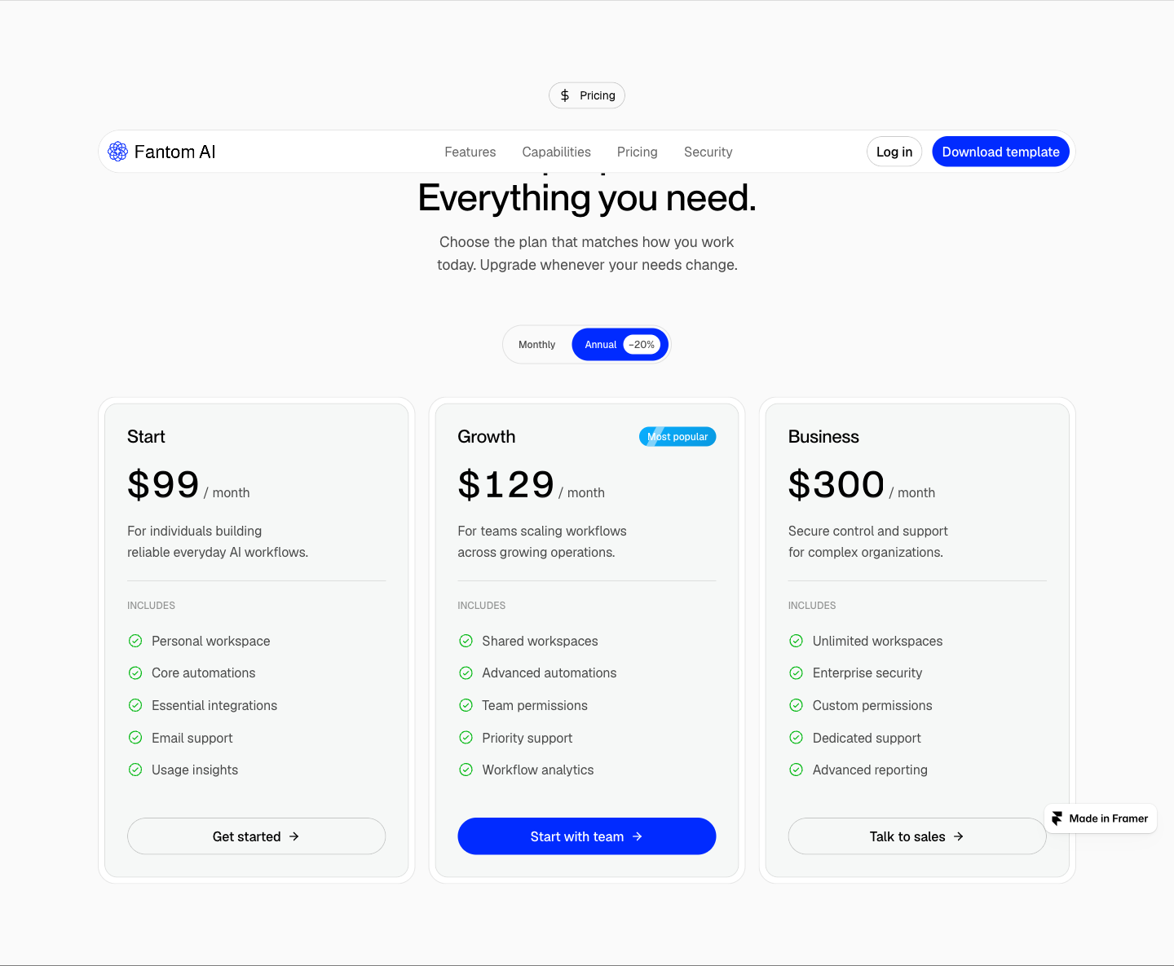
gtm/fantom_screens/07_pricing.png
