orpheo28/physicallovablex/gtm/fantom_screens/08_security.png

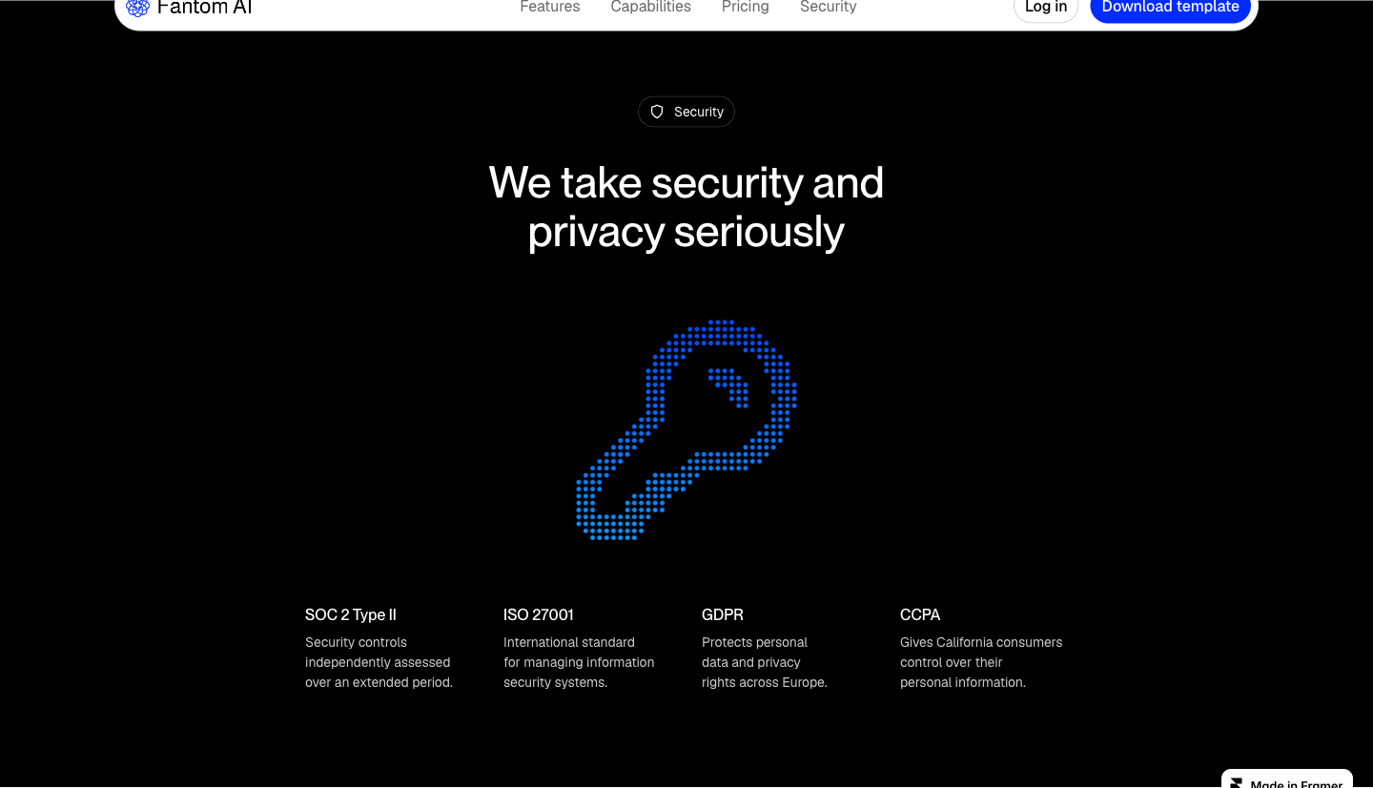
gtm/fantom_screens/08_security.png
