orpheo28/physicallovablex/gtm/fantom_screens/12_final_cta_footer.png

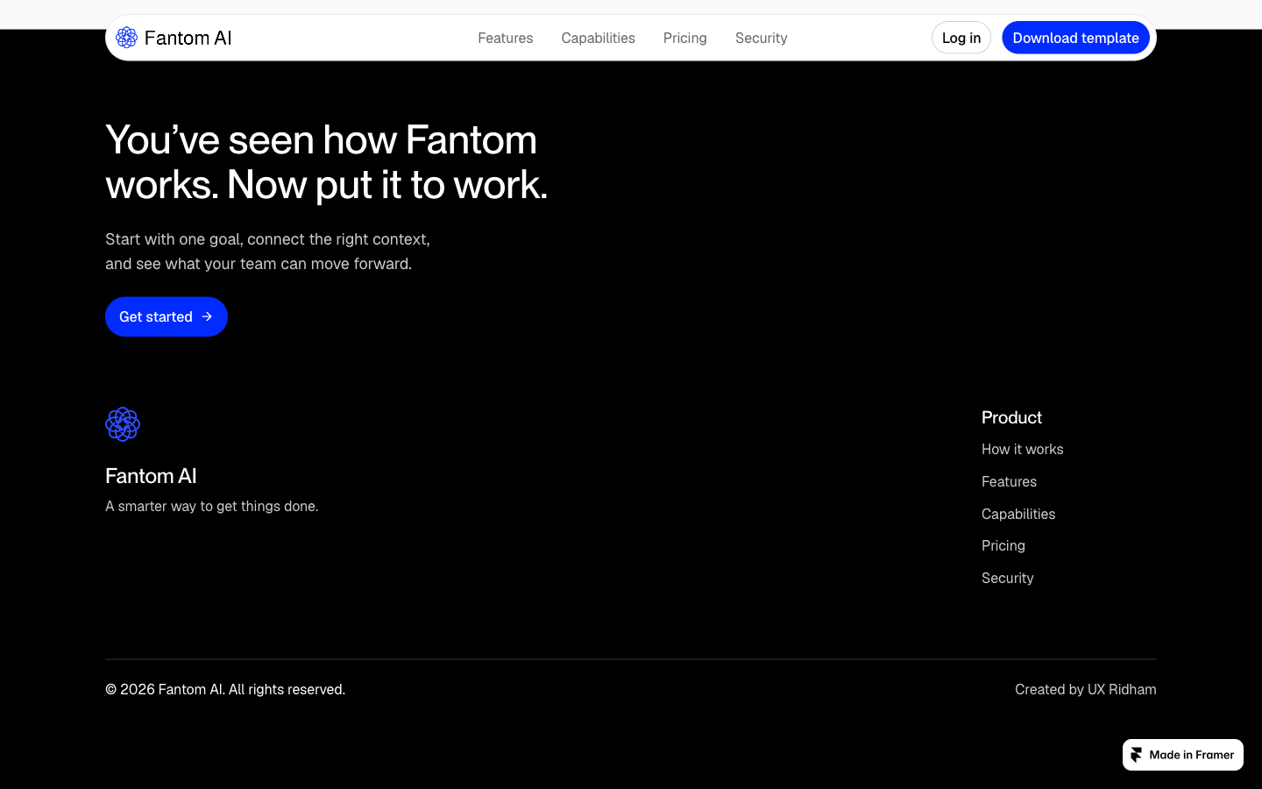
gtm/fantom_screens/12_final_cta_footer.png
