orpheo28/physicallovablex/gtm/fantom_screens/13_404.png

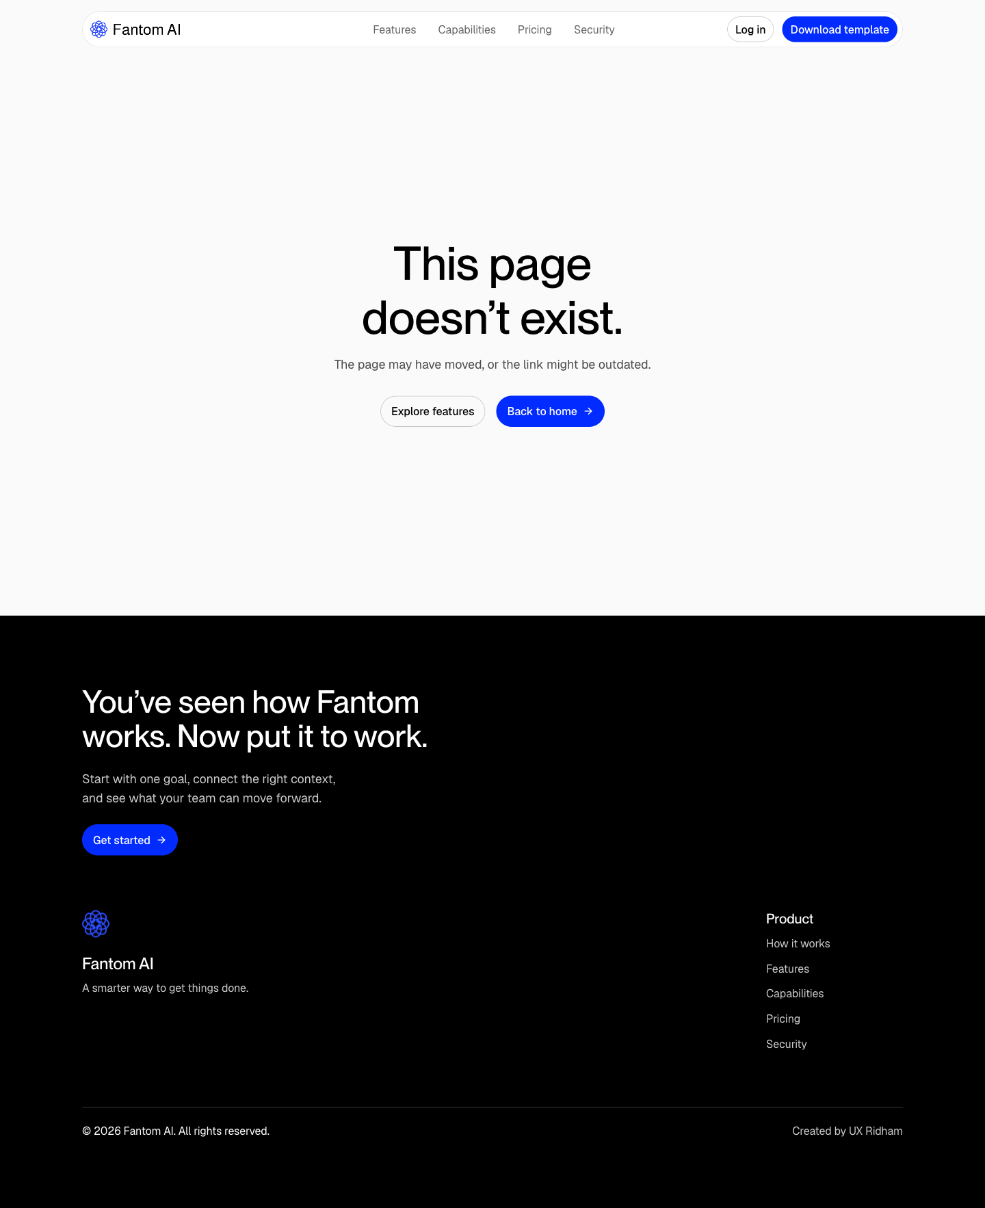
gtm/fantom_screens/13_404.png
