orpheo28/physicallovablex/gtm/illustrations/honesty_labels.png

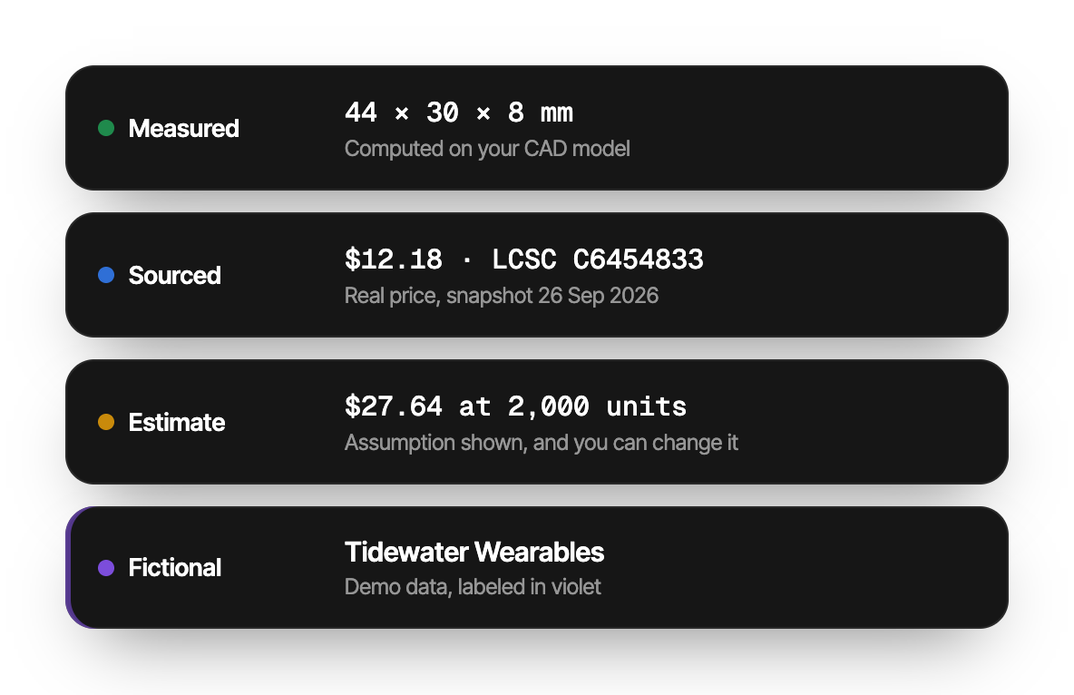
gtm/illustrations/honesty_labels.png
