orpheo28/physicallovablex/gtm/illustrations/metrics_ranges.png

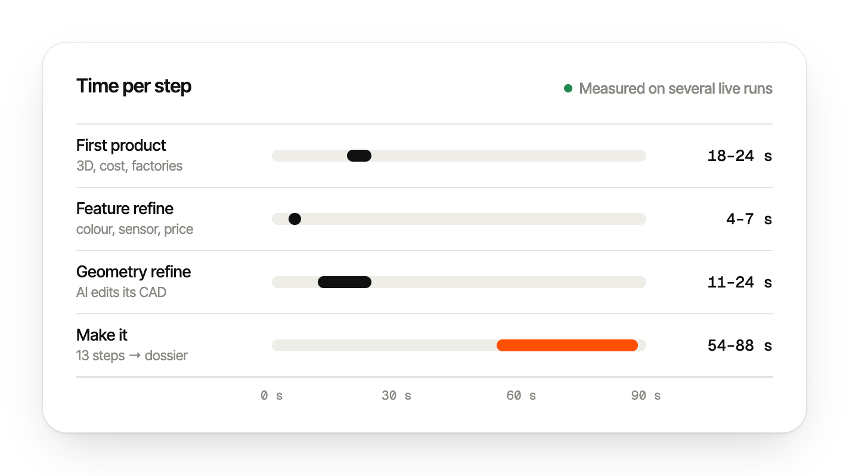
gtm/illustrations/metrics_ranges.png
