orpheo28/physicallovablex/gtm/illustrations/usecase_changing_table.png

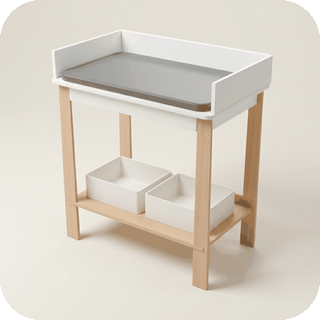
gtm/illustrations/usecase_changing_table.png
