orpheo28/physicallovablex/gtm/illustrations/usecase_drone.png

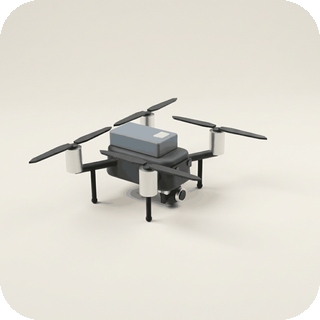
gtm/illustrations/usecase_drone.png
