orpheo28/physicallovablex/gtm/illustrations/usecase_rooftop_solar.png

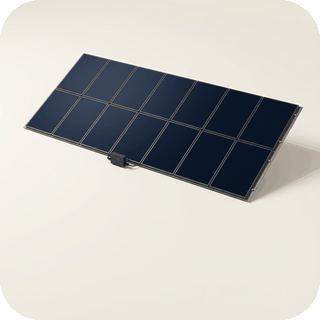
gtm/illustrations/usecase_rooftop_solar.png
