orpheo28/physicallovablex/gtm/illustrations/usecase_stick_vacuum.png

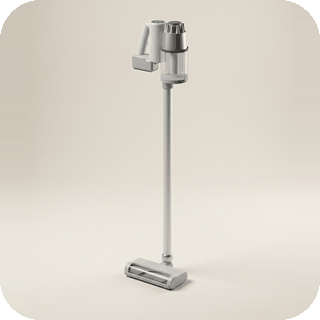
gtm/illustrations/usecase_stick_vacuum.png
