orpheo28/physicallovablex/gtm/illustrations/usecase_surfboard.png

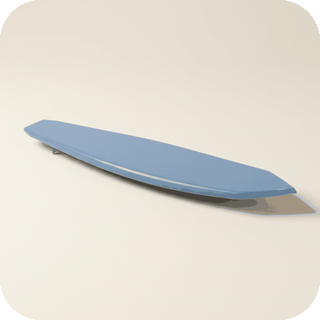
gtm/illustrations/usecase_surfboard.png
