orpheo28/physicallovablex/gtm/illustrations/usecase_wearable.png

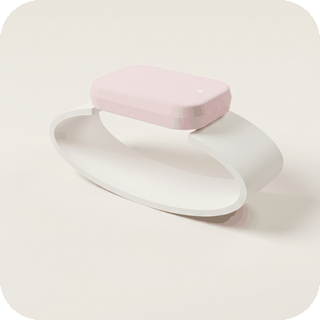
gtm/illustrations/usecase_wearable.png
