orpheo28/physicallovablex/gtm/paper_assets/anatomy_drone_crop.png

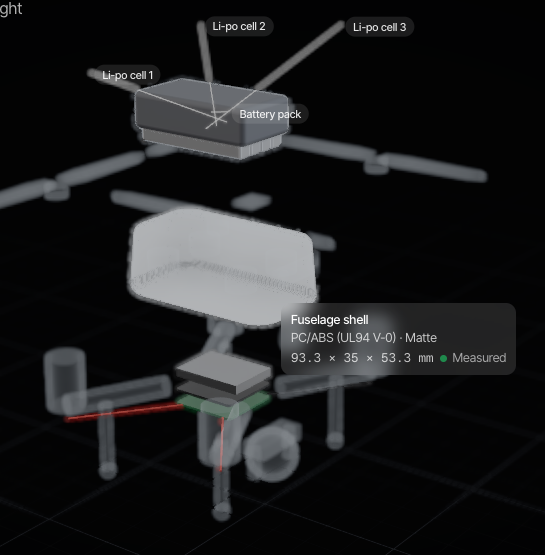
gtm/paper_assets/anatomy_drone_crop.png
