orpheo28/physicallovablex/gtm/paper_assets/anatomy_drone_full.png

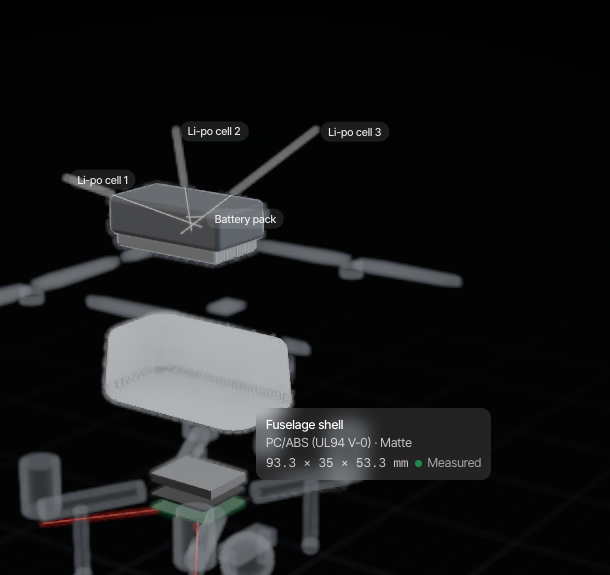
gtm/paper_assets/anatomy_drone_full.png
