orpheo28/physicallovablex/gtm/paper_assets/anatomy_whoop_crop2.png

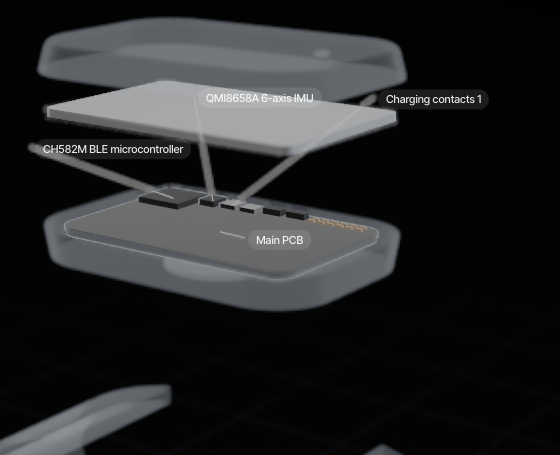
gtm/paper_assets/anatomy_whoop_crop2.png
