orpheo28/physicallovablex/gtm/paper_assets/anatomy_whoop_crop.png

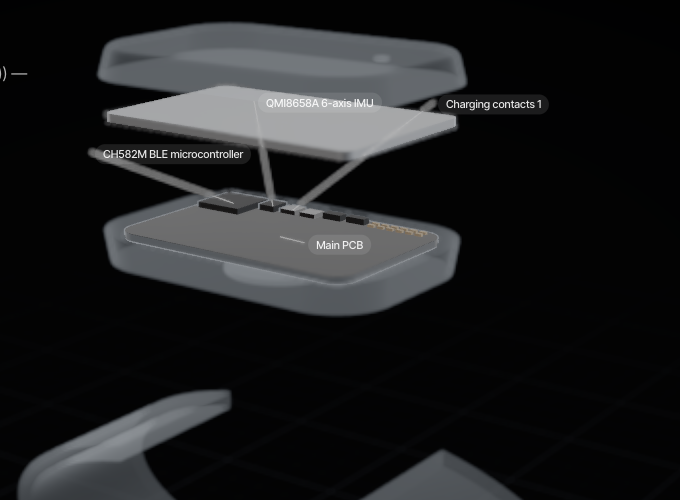
gtm/paper_assets/anatomy_whoop_crop.png
