orpheo28/physicallovablex/gtm/paper_assets/drone_hero_studio.png

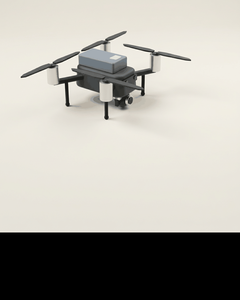
gtm/paper_assets/drone_hero_studio.png
