orpheo28/physicallovablex/gtm/paper_assets/drone_hero_studio_wide.png

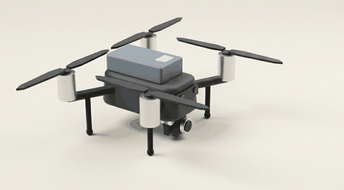
gtm/paper_assets/drone_hero_studio_wide.png
