orpheo28/physicallovablex/gtm/paper_assets/drone_lifestyle.png

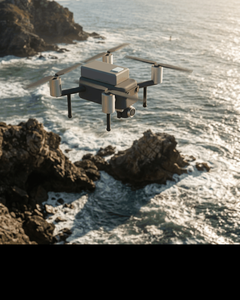
gtm/paper_assets/drone_lifestyle.png
