orpheo28/physicallovablex/gtm/paper_assets/drone_lifestyle_wide.png

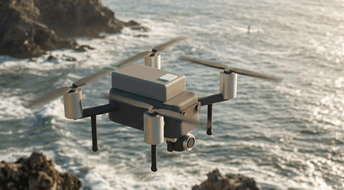
gtm/paper_assets/drone_lifestyle_wide.png
