orpheo28/physicallovablex/gtm/paper_assets/fantom_bg_3zE3eLjjpwMLVNUEK5PAUEZaCJk.png

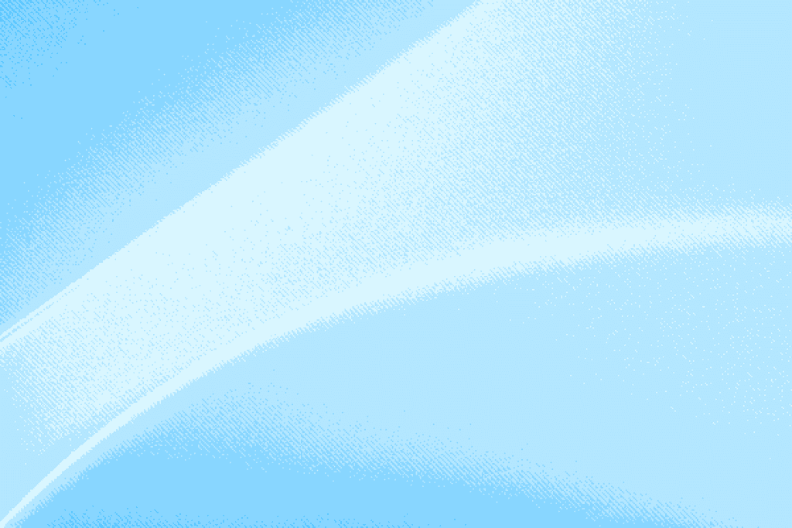
gtm/paper_assets/fantom_bg_3zE3eLjjpwMLVNUEK5PAUEZaCJk.png
