orpheo28/physicallovablex/gtm/paper_assets/fantom_bg_7JLgNnHNWS2ZheqZrTXBTaVCv6Q.png

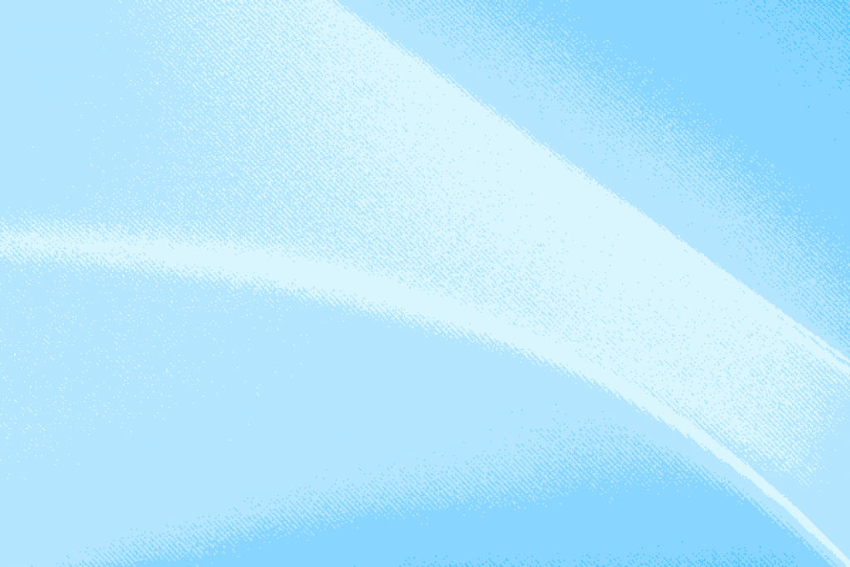
gtm/paper_assets/fantom_bg_7JLgNnHNWS2ZheqZrTXBTaVCv6Q.png
