orpheo28/physicallovablex/gtm/paper_assets/fantom_bg_svSq1hHi3TFnZce7BPcnb7uXyFw.png

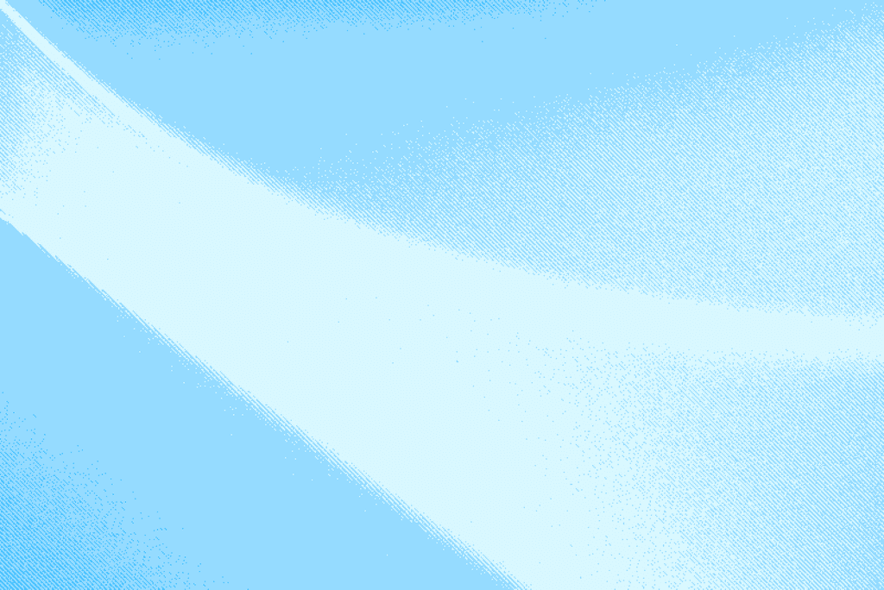
gtm/paper_assets/fantom_bg_svSq1hHi3TFnZce7BPcnb7uXyFw.png
