orpheo28/physicallovablex/gtm/paper_assets/kit45_detail_macro.png

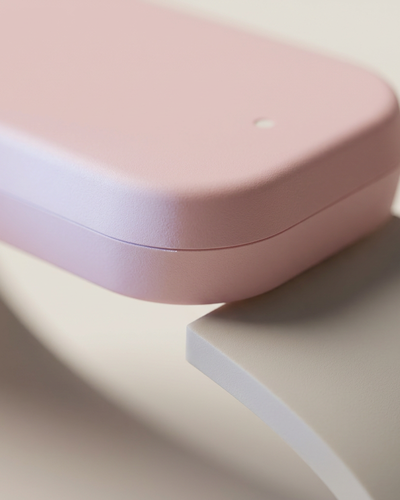
gtm/paper_assets/kit45_detail_macro.png
