orpheo28/physicallovablex/gtm/paper_assets/kit45_packshot_white.png

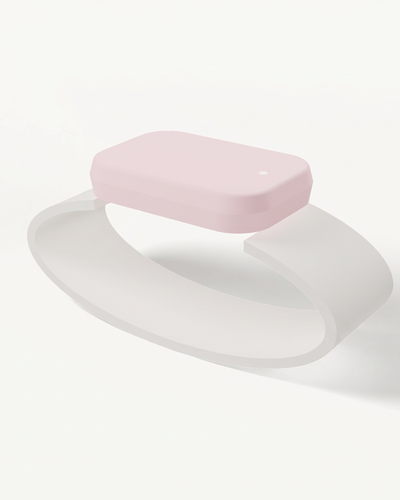
gtm/paper_assets/kit45_packshot_white.png
