orpheo28/physicallovablex/gtm/paper_assets/kit_in_hand_scale.png

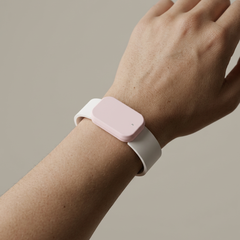
gtm/paper_assets/kit_in_hand_scale.png
