orpheo28/physicallovablex/gtm/paper_assets/kit_lifestyle.png

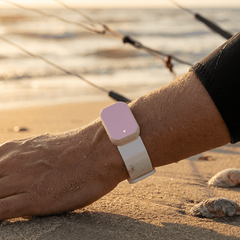
gtm/paper_assets/kit_lifestyle.png
