orpheo28/physicallovablex/gtm/paper_assets/phone_studio.png

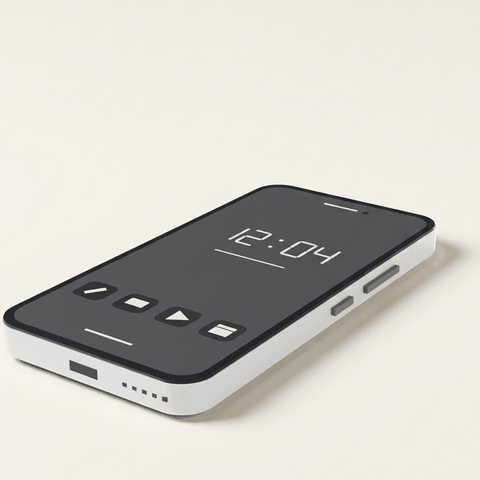
gtm/paper_assets/phone_studio.png
