orpheo28/physicallovablex/gtm/paper_assets/ref_whoop_packshot.jpg

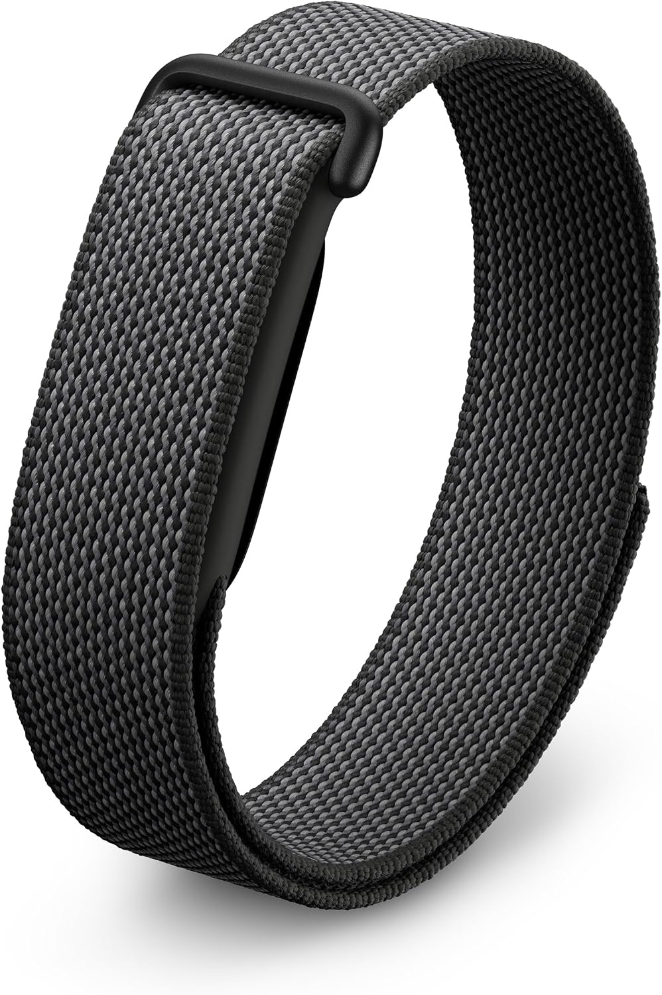
gtm/paper_assets/ref_whoop_packshot.jpg
