orpheo28/physicallovablex/gtm/paper_assets/ref_whoop_strap_detail.jpg

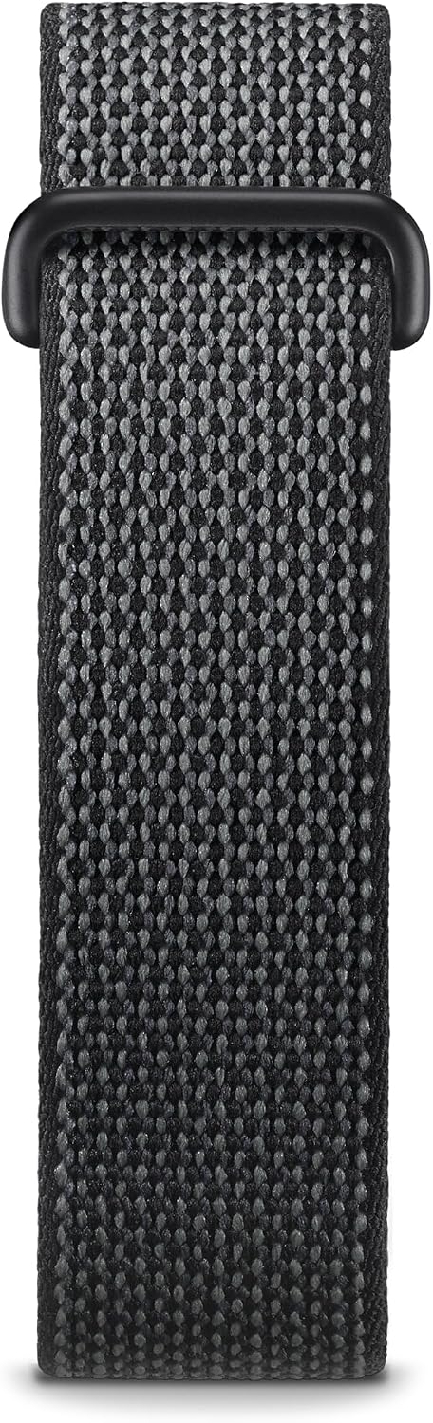
gtm/paper_assets/ref_whoop_strap_detail.jpg
