orpheo28/physicallovablex/gtm/paper_assets/ref_whoop_wrist_blue.jpg

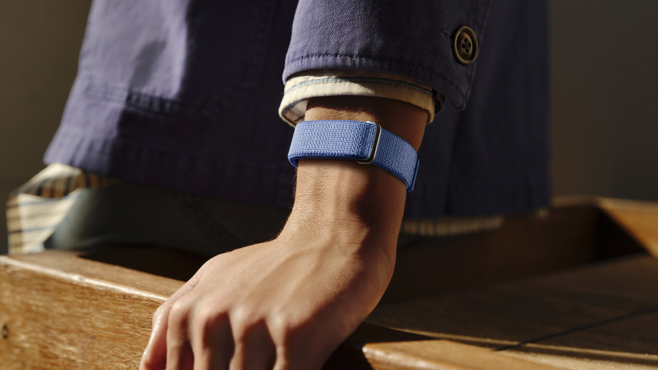
gtm/paper_assets/ref_whoop_wrist_blue.jpg
