orpheo28/physicallovablex/gtm/paper_assets/ref_whoop_wrist_sky.jpg

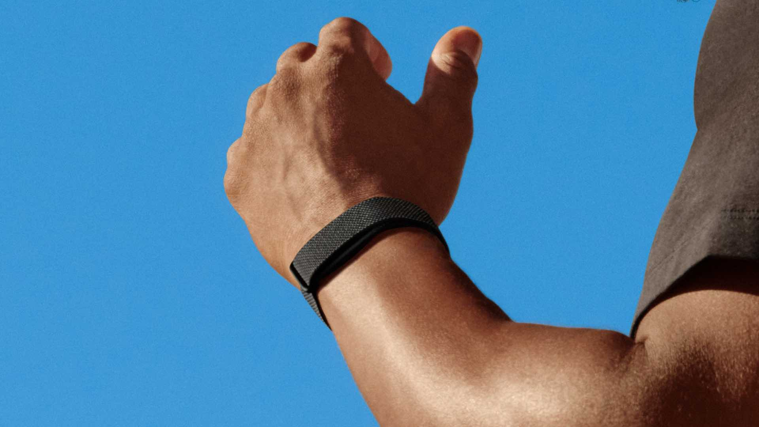
gtm/paper_assets/ref_whoop_wrist_sky.jpg
