orpheo28/physicallovablex/gtm/paper_assets/viewer_drone.png

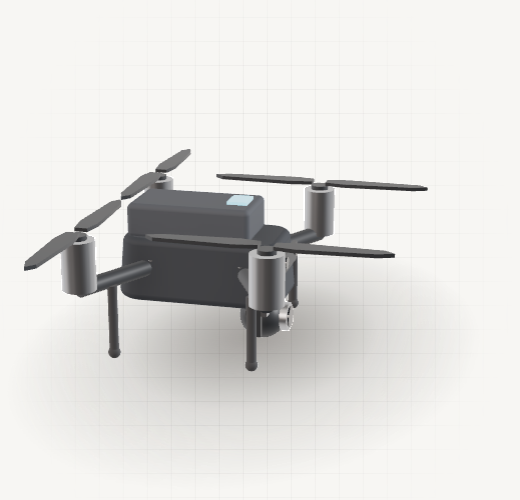
gtm/paper_assets/viewer_drone.png
