orpheo28/physicallovablex/gtm/paper_assets/viewer_whoop_sage.png

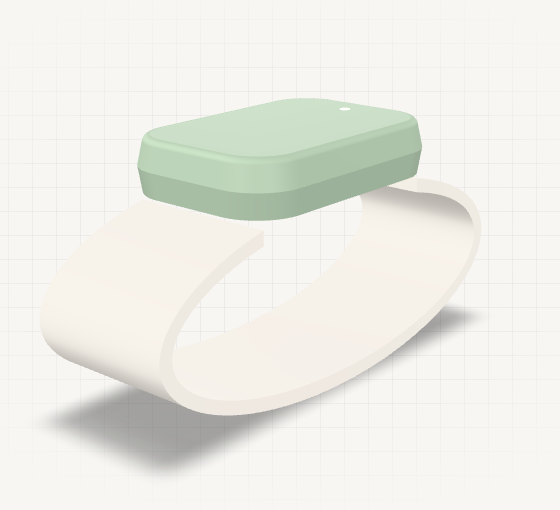
gtm/paper_assets/viewer_whoop_sage.png
