orpheo28/physicallovablex/app/api/cad/prebuilt/showcase_drone_follow/v2.step

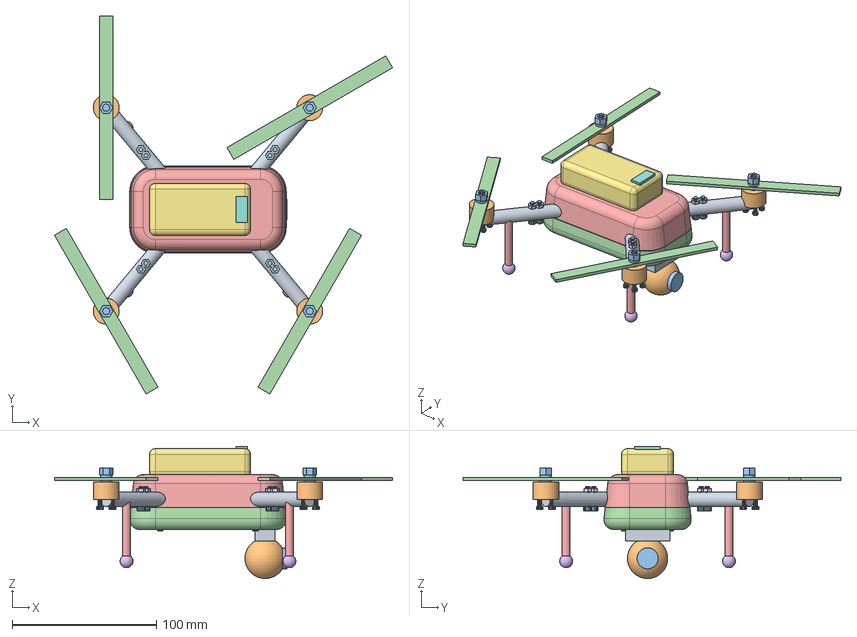
[picture p249: CAD file, 2026-09-28]
app/api/cad/prebuilt/showcase_drone_follow/v2.step
234.2 x 261.9 x 91.5 mm
coat.1
metal.1
accent.1
accent.11
rubber.1
rubber.11
coat.2
metal.2
accent.2
accent.12
rubber.2
rubber.12
coat.3
metal.3
accent.3
accent.13
rubber.3
rubber.13
coat.4
metal.4
accent.4
accent.14
rubber.4
rubber.14
accent.30
led.1
coat.20
coat.21
glass.1
steel.137 x 4
brass.138 x 4
steel.168 x 8
steel.169 x 8
steel.173 x 16
steel.174 x 4
