orpheo28/physicallovablex/app/api/cad/prebuilt/showcase_hair_dryer/d1.step

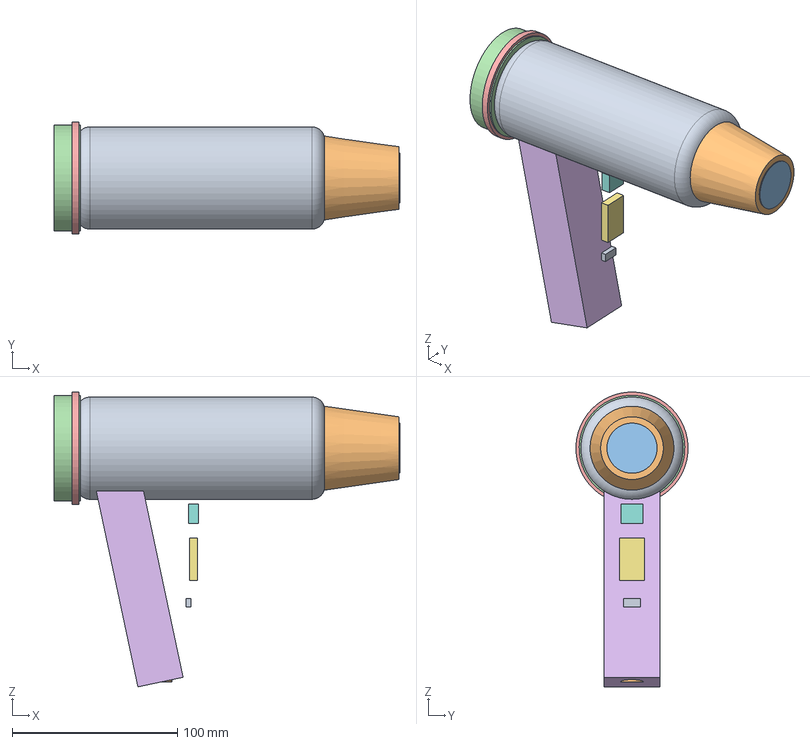
[picture p250: CAD file, 2026-09-27]
app/api/cad/prebuilt/showcase_hair_dryer/d1.step
209.6 x 68.0 x 178.5 mm
accent.1
coat.1
coat.2
accent.2
button.1
button.2
led.1
rubber.1
