orpheo28/physicallovablex/app/api/cad/prebuilt/showcase_home_robot/v1_enclosure.step

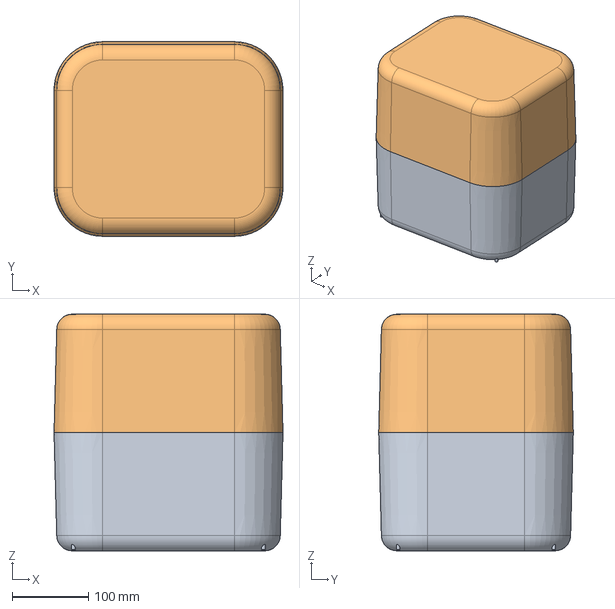
[picture p251: CAD file, 2026-09-27]
app/api/cad/prebuilt/showcase_home_robot/v1_enclosure.step
300.0 x 255.0 x 310.0 mm
bottom_shell
top_shell
