orpheo28/physicallovablex/app/api/cad/prebuilt/showcase_instant_camera/v1_enclosure.step

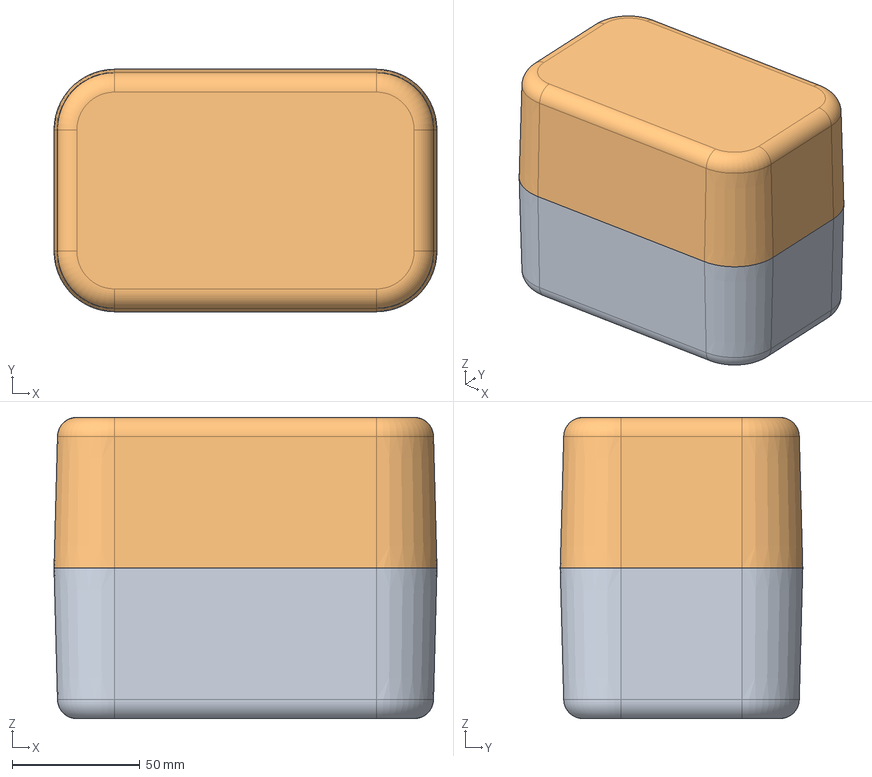
[picture p252: CAD file, 2026-09-27]
app/api/cad/prebuilt/showcase_instant_camera/v1_enclosure.step
150.0 x 95.0 x 118.0 mm
bottom_shell
top_shell
