orpheo28/physicallovablex/app/api/cad/prebuilt/showcase_irrigation_biarritz/v2.step

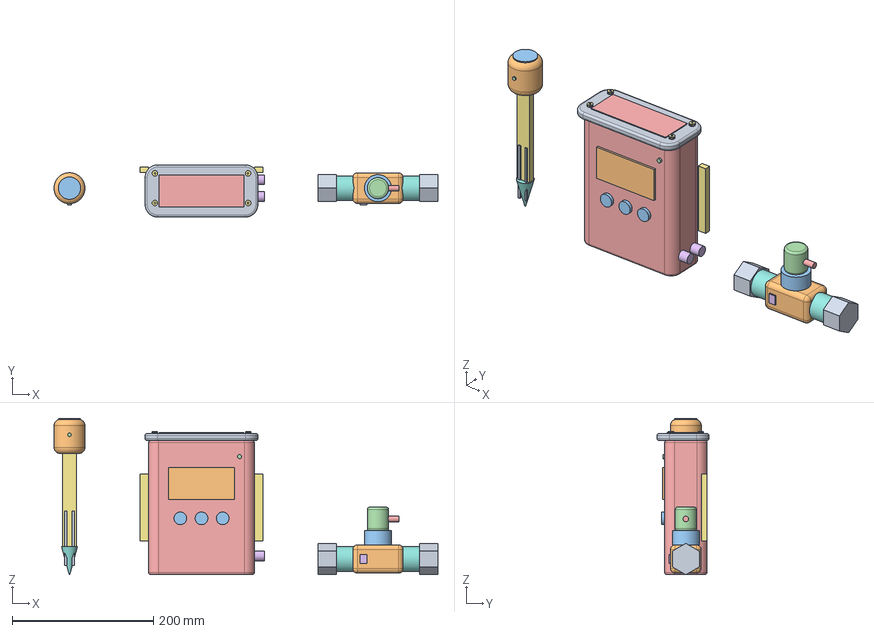
[picture p253: CAD file, 2026-09-28]
app/api/cad/prebuilt/showcase_irrigation_biarritz/v2.step
544.0 x 74.0 x 221.5 mm
accent.1
glass.1
button.1
button.2
button.3
led.1
cell.1
rubber.1
rubber.2
accent.2
accent.3
coat.1
coat.2
coat.3
coat.4
coat.5
rubber.3
rubber.4
accent.4
accent.5
accent.6
steel.1
steel.2
cell.2
led.2
rubber.127
steel.134 x 4
brass.135 x 4
