orpheo28/physicallovablex/app/api/cad/prebuilt/showcase_minimal_phone/v1_enclosure.step

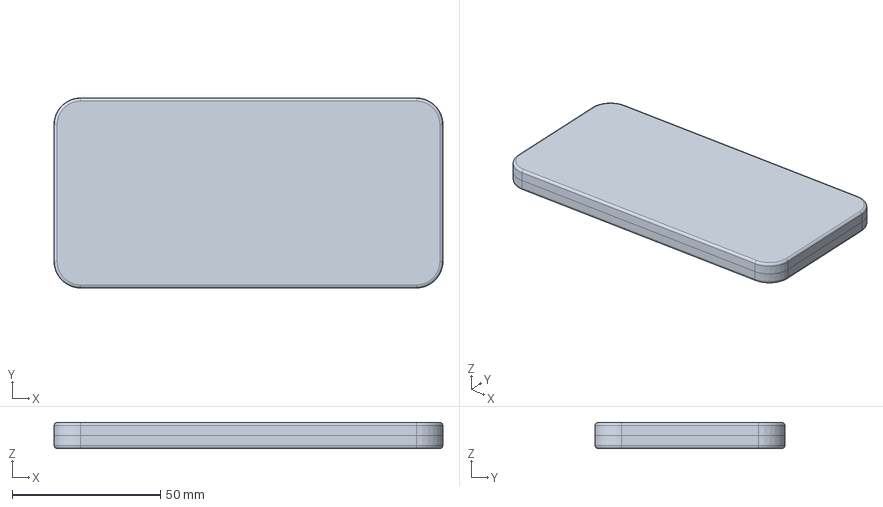
[picture p254: CAD file, 2026-09-27]
app/api/cad/prebuilt/showcase_minimal_phone/v1_enclosure.step
131.0 x 64.0 x 8.80 mm
bottom_shell
top_shell
