orpheo28/physicallovablex/app/api/cad/prebuilt/showcase_stick_vacuum/v2.step

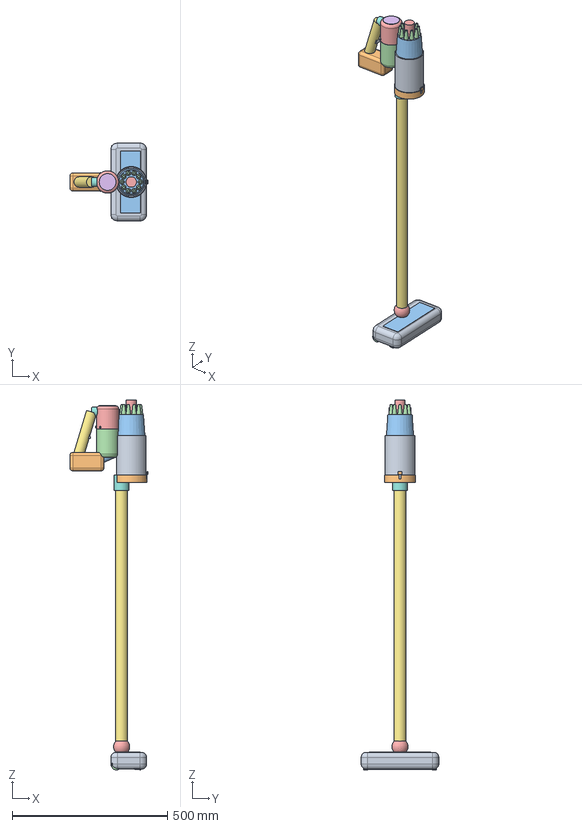
[picture p255: CAD file, 2026-09-28]
app/api/cad/prebuilt/showcase_stick_vacuum/v2.step
252.1 x 250.0 x 1190.5 mm
accent.1
rubber.1
clear.1
rubber.3
rubber.2
metal.1
accent.2
metal.2
accent.3
clear.2
accent.4
metal.3
accent.5
accent.6
accent.7
accent.8
accent.9
accent.10
accent.11
accent.12
accent.13
accent.14
coat.1
button.1
accent.40
steel.143 x 7
accent.132
accent.134
accent.136
accent.138
accent.140
accent.142
accent.144
accent.145
button.146
