orpheo28/physicallovablex/app/api/cad/prebuilt/showcase_changing_table/v2_enclosure.step

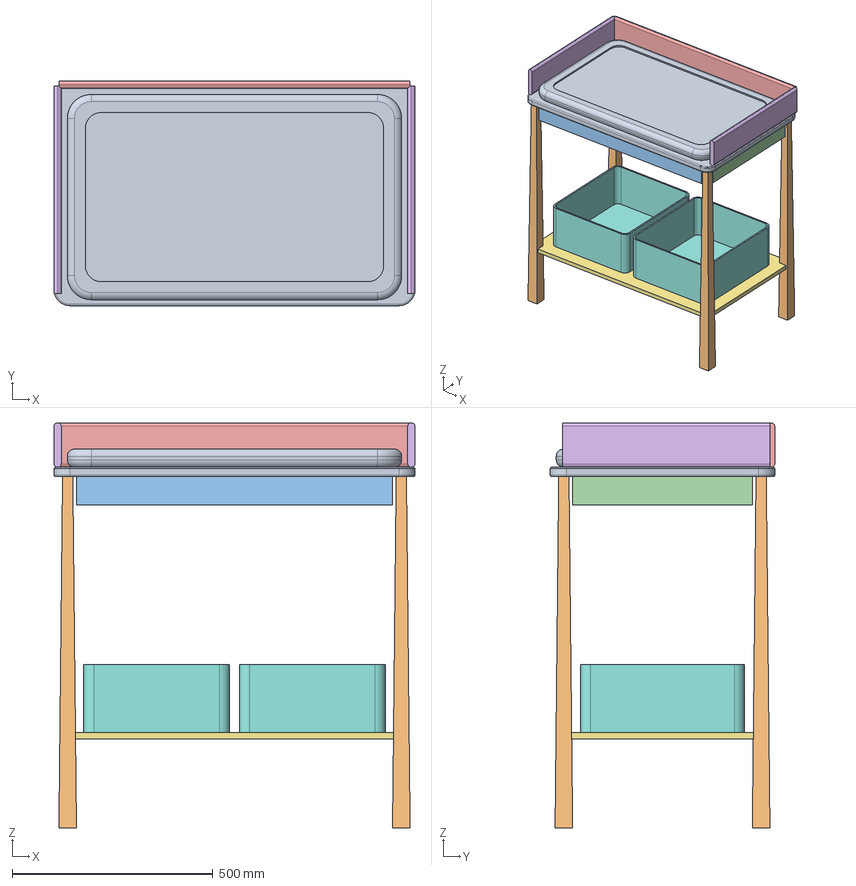
[picture p256: CAD file, 2026-09-27]
app/api/cad/prebuilt/showcase_changing_table/v2_enclosure.step
900.0 x 560.0 x 1010.0 mm
wood.1
wood.2
wood.3
wood.4
wood.5
wood.6
fabric.1
fabric.2
fabric.3
