orpheo28/physicallovablex/app/api/cad/prebuilt/showcase_drone_follow/d1.step

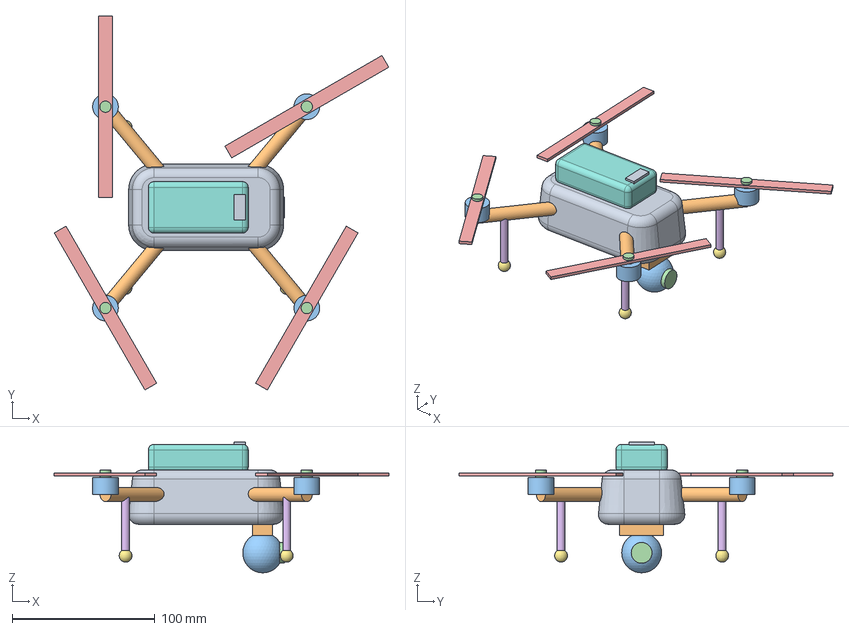
[picture p257: CAD file, 2026-09-27]
app/api/cad/prebuilt/showcase_drone_follow/d1.step
234.2 x 261.9 x 91.5 mm
coat.1
metal.1
accent.1
accent.11
rubber.1
rubber.11
coat.2
metal.2
accent.2
accent.12
rubber.2
rubber.12
coat.3
metal.3
accent.3
accent.13
rubber.3
rubber.13
coat.4
metal.4
accent.4
accent.14
rubber.4
rubber.14
accent.30
led.1
coat.20
coat.21
glass.1
