orpheo28/physicallovablex/app/api/cad/prebuilt/showcase_hair_dryer/v1_enclosure.step

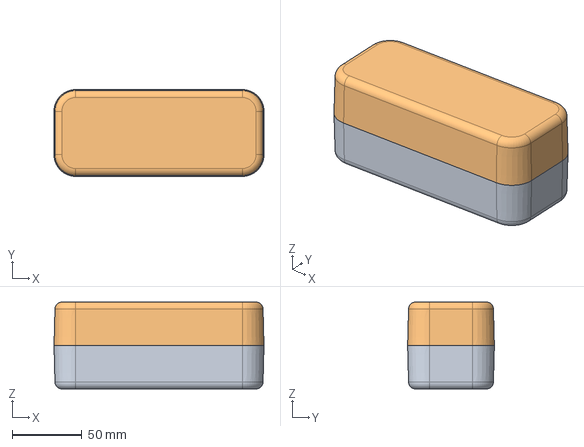
[picture p258: CAD file, 2026-09-27]
app/api/cad/prebuilt/showcase_hair_dryer/v1_enclosure.step
150.0 x 62.0 x 62.0 mm
bottom_shell
top_shell
