orpheo28/physicallovablex/app/api/cad/prebuilt/showcase_home_robot/d1.step

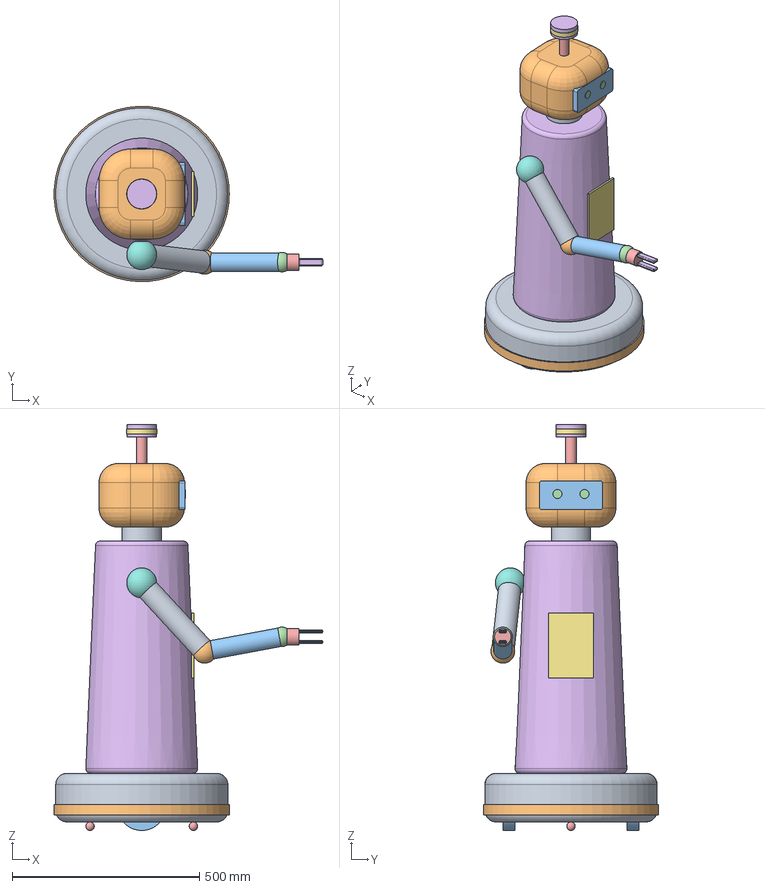
[picture p259: CAD file, 2026-09-27]
app/api/cad/prebuilt/showcase_home_robot/d1.step
717.0 x 467.8 x 1084.0 mm
accent.1
rubber.1
rubber.2
metal.1
rubber.3
metal.2
rubber.4
rubber.5
glass.1
led.1
coat.1
glass.2
led.2
led.3
metal.3
coat.2
glass.3
coat.3
coat.4
coat.5
metal.4
rubber.6
rubber.7
