orpheo28/physicallovablex/app/api/cad/prebuilt/showcase_instant_camera/d1.step

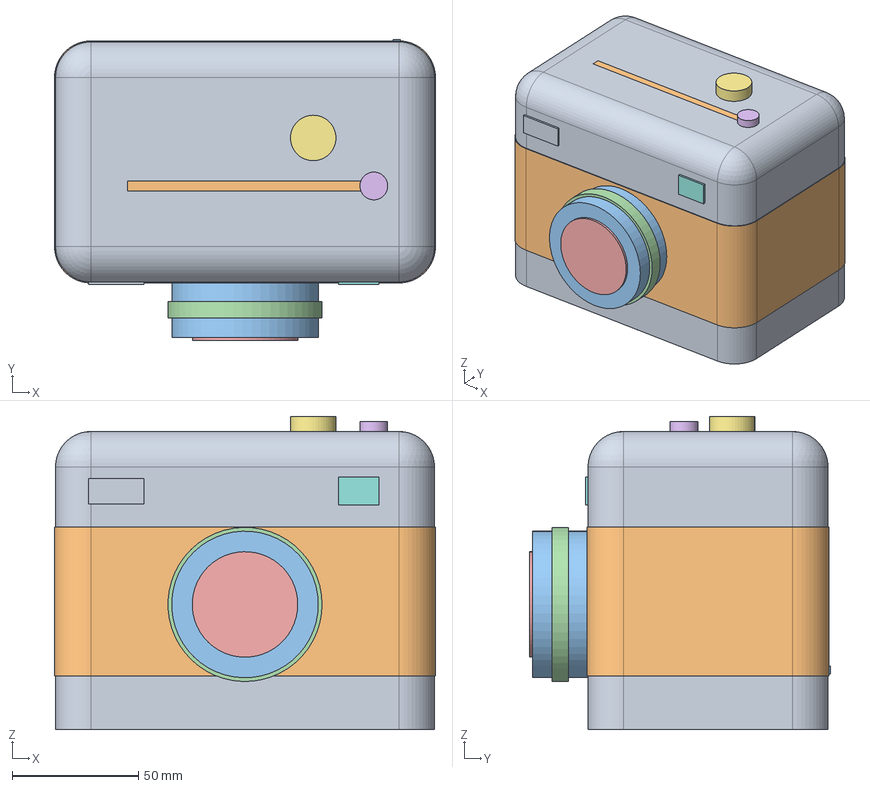
[picture p260: CAD file, 2026-09-27]
app/api/cad/prebuilt/showcase_instant_camera/d1.step
150.8 x 119.2 x 124.0 mm
rubber.1
metal.1
coat.1
glass.1
button.1
metal.2
glass.3
diffuser.1
coat.2
led.1
