orpheo28/physicallovablex/app/api/cad/prebuilt/showcase_irrigation_biarritz/d1.step

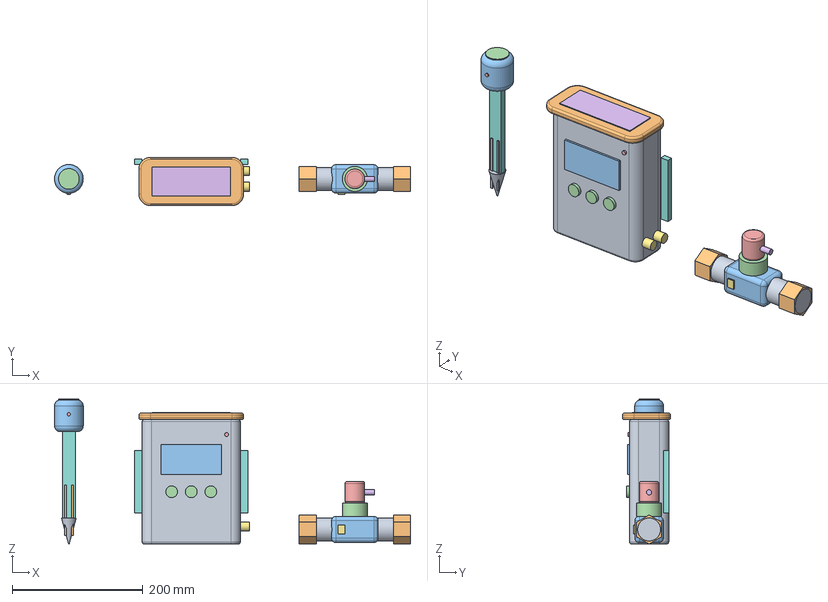
[picture p261: CAD file, 2026-09-27]
app/api/cad/prebuilt/showcase_irrigation_biarritz/d1.step
544.0 x 74.0 x 221.5 mm
accent.1
glass.1
button.1
button.2
button.3
led.1
cell.1
rubber.1
rubber.2
accent.2
accent.3
coat.1
coat.2
coat.3
coat.4
coat.5
rubber.3
rubber.4
accent.4
accent.5
accent.6
steel.1
steel.2
cell.2
led.2
