orpheo28/physicallovablex/app/api/cad/prebuilt/showcase_minimal_phone/d1.step

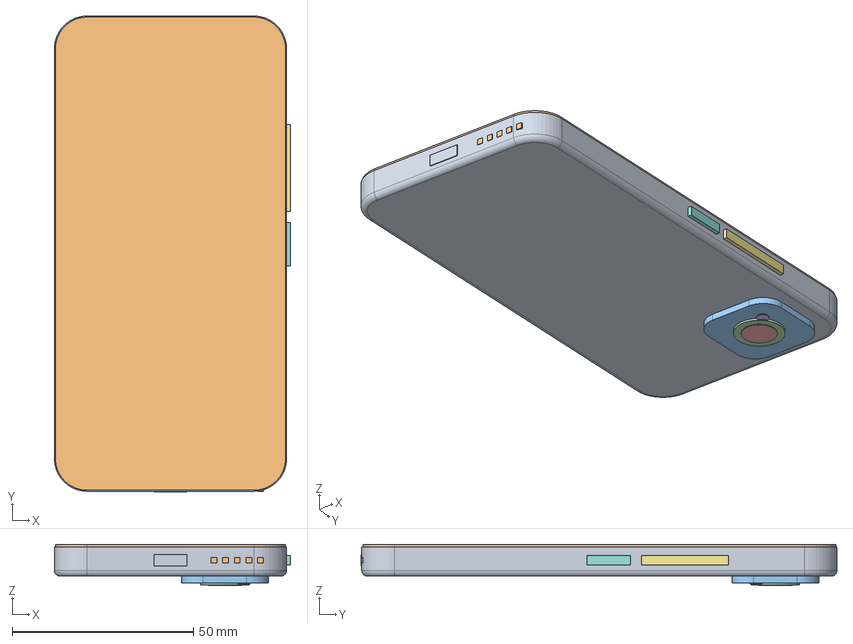
[picture p262: CAD file, 2026-09-27]
app/api/cad/prebuilt/showcase_minimal_phone/d1.step
65.1 x 131.2 x 11.4 mm
metal.1
glass.1
glass.2
metal.2
glass.3
diffuser.1
button.1
button.2
port.1
coat.1
coat.2
coat.3
coat.4
coat.5
