orpheo28/physicallovablex/app/api/cad/prebuilt/showcase_solar_biarritz/v2_enclosure.step

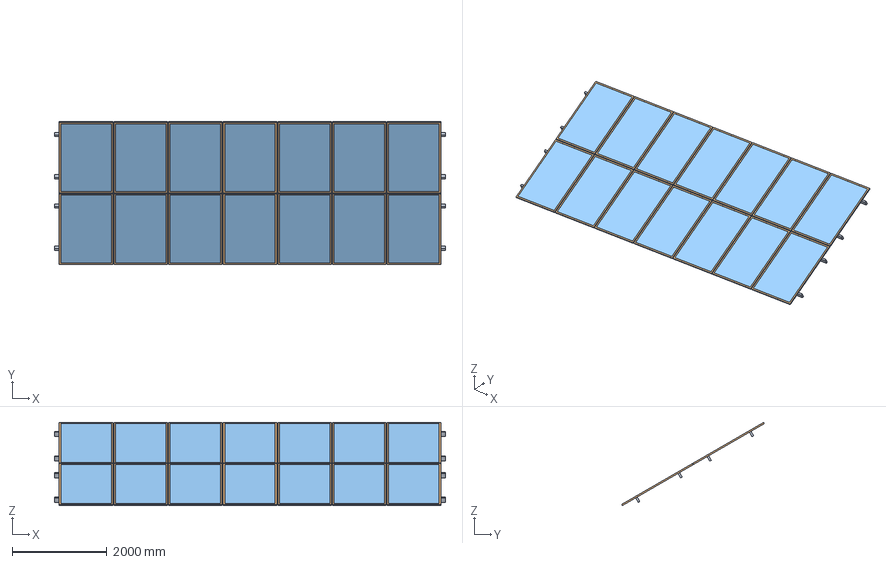
[picture p263: CAD file, 2026-09-27]
app/api/cad/prebuilt/showcase_solar_biarritz/v2_enclosure.step
8258.0 x 3014.9 x 1758.0 mm
metal.1
metal.2
metal.101
cell.1
metal.102
cell.2
metal.103
cell.3
metal.104
cell.4
metal.105
cell.5
metal.106
cell.6
metal.107
cell.7
metal.3
metal.4
metal.108
cell.8
metal.109
cell.9
metal.110
cell.10
metal.111
cell.11
metal.112
cell.12
metal.113
cell.13
metal.114
cell.14
