orpheo28/physicallovablex/app/api/cad/prebuilt/showcase_stick_vacuum/v2_enclosure.step

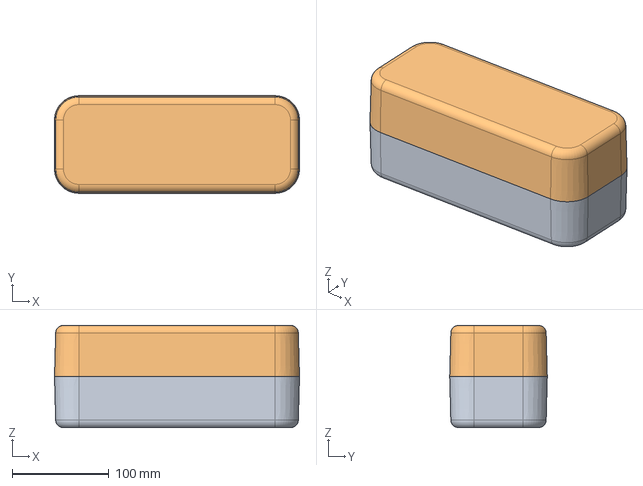
[picture p264: CAD file, 2026-09-27]
app/api/cad/prebuilt/showcase_stick_vacuum/v2_enclosure.step
253.0 x 100.8 x 105.6 mm
bottom_shell
top_shell
