orpheo28/physicallovablex/app/api/cad/prebuilt/showcase_surfboard_beginner/v2_enclosure.step

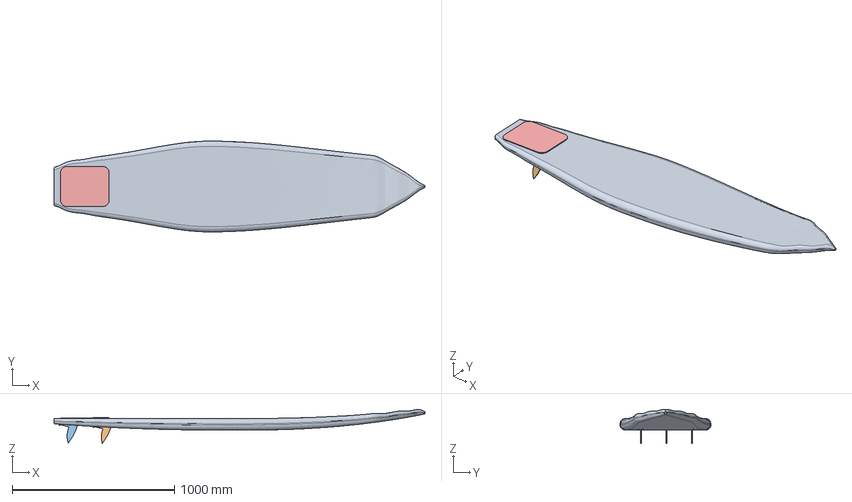
[picture p265: CAD file, 2026-09-27]
app/api/cad/prebuilt/showcase_surfboard_beginner/v2_enclosure.step
2286.0 x 559.9 x 210.0 mm
fin.1
fin.2
fin.3
rubber.1
rubber.2
rubber.3
rubber.4
