orpheo28/physicallovablex/app/api/cad/prebuilt/showcase_drone_follow/v2_enclosure.step

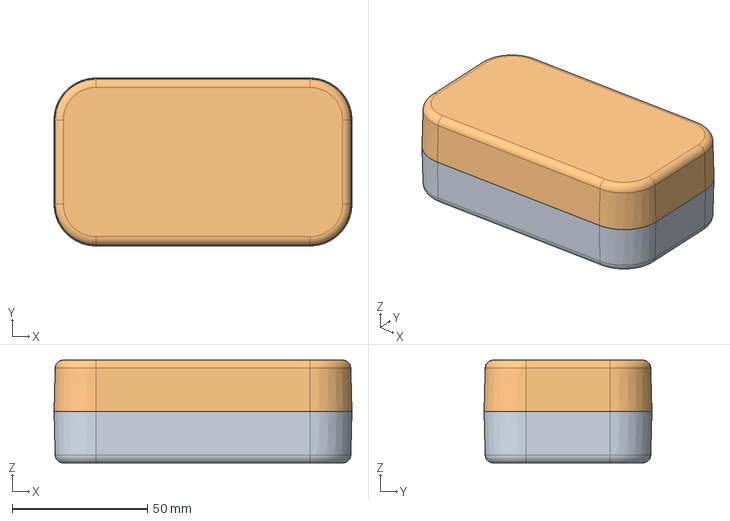
[picture p266: CAD file, 2026-09-27]
app/api/cad/prebuilt/showcase_drone_follow/v2_enclosure.step
110.0 x 62.0 x 38.0 mm
bottom_shell
top_shell
