orpheo28/physicallovablex/app/api/cad/prebuilt/showcase_irrigation_biarritz/v2_enclosure.step

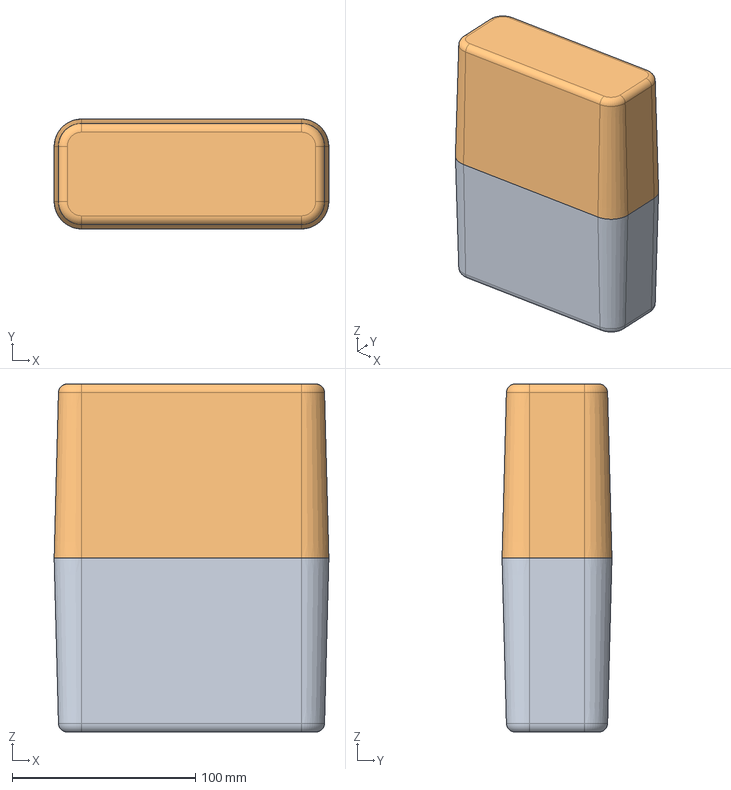
[picture p267: CAD file, 2026-09-27]
app/api/cad/prebuilt/showcase_irrigation_biarritz/v2_enclosure.step
150.0 x 60.0 x 190.0 mm
bottom_shell
top_shell
