orpheo28/physicallovablex/app/api/cad/prebuilt/showcase_whoop_kitesurf/v4_enclosure.step

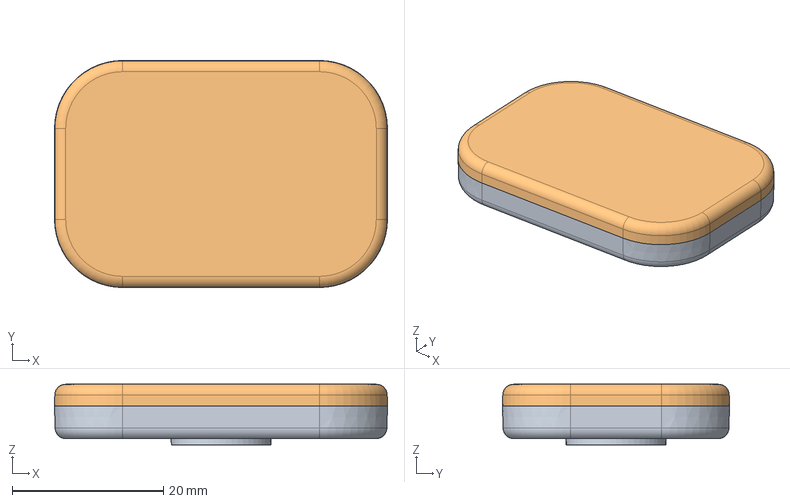
[picture p269: CAD file, 2026-09-27]
app/api/cad/prebuilt/showcase_whoop_kitesurf/v4_enclosure.step
44.0 x 30.0 x 8.00 mm
bottom_shell
top_shell
