orpheo28/physicallovablex/gtm/fantom_screens/09_testimonial.png

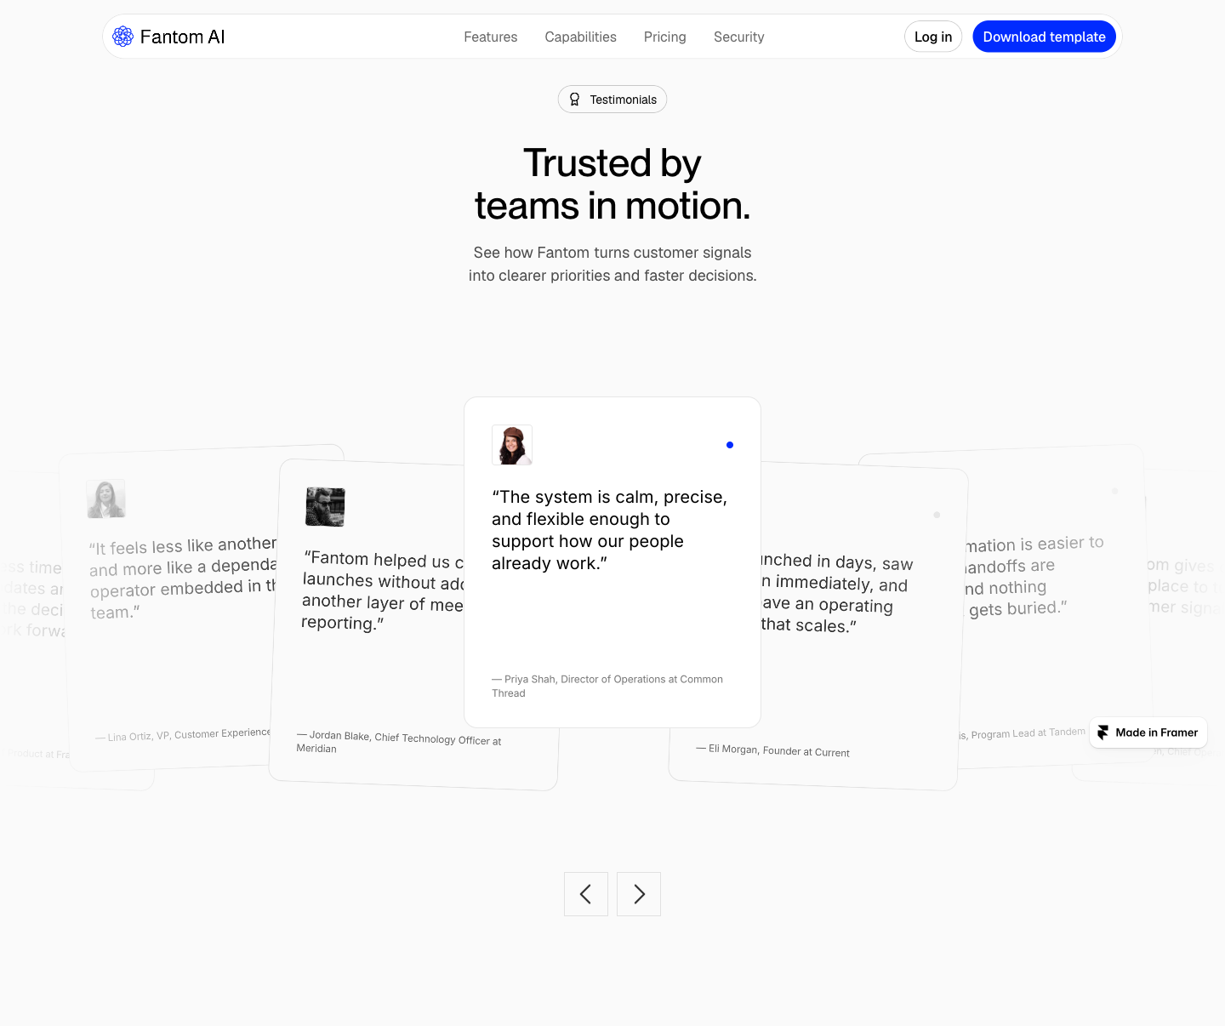
gtm/fantom_screens/09_testimonial.png
