orpheo28/physicallovablex/gtm/fantom_screens/10_faqs.png

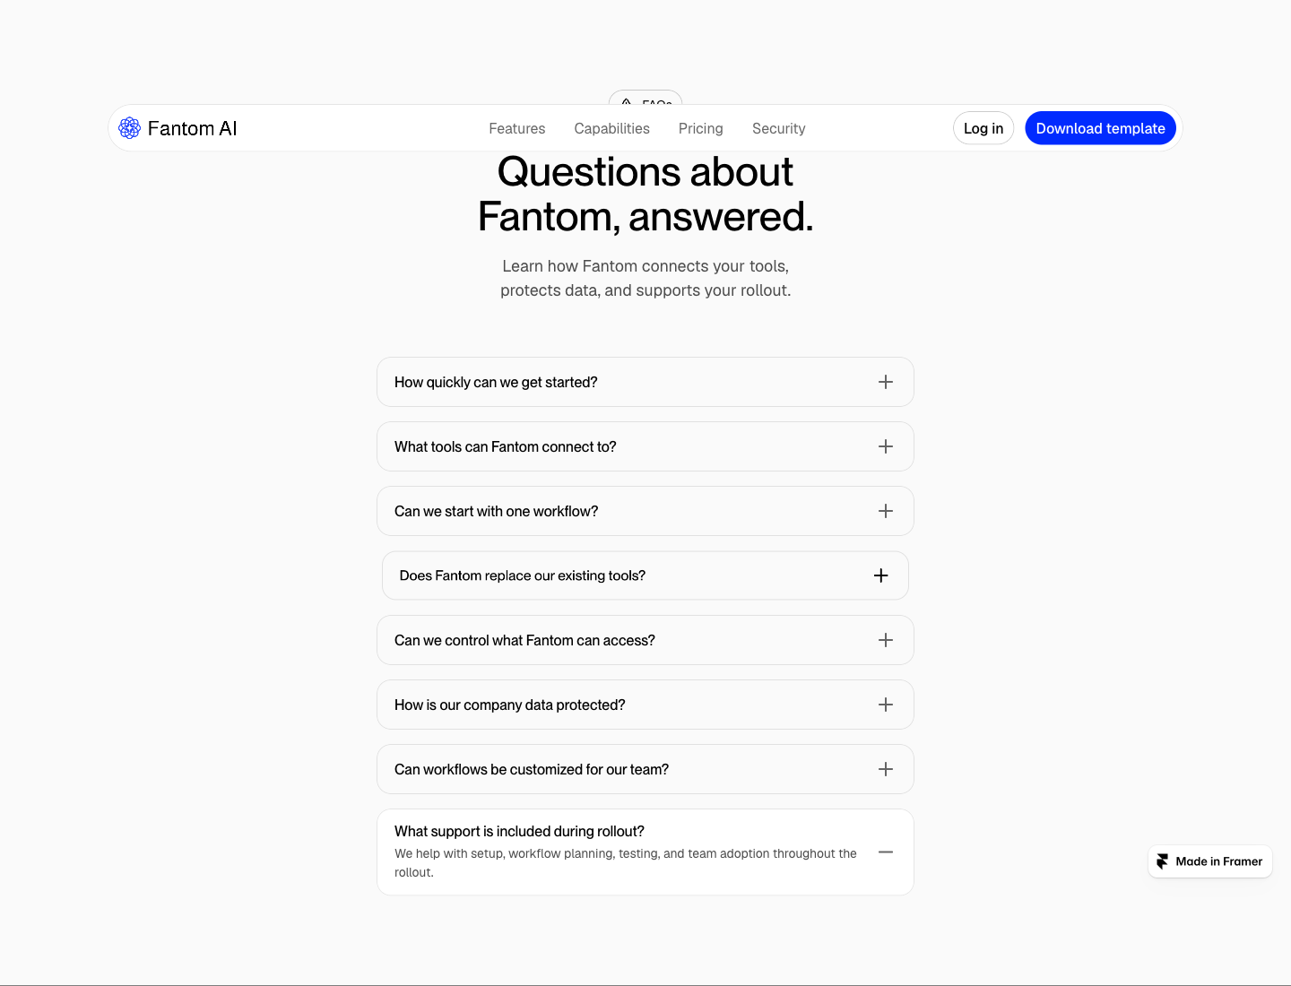
gtm/fantom_screens/10_faqs.png
